lgili/Fenolite/docs/design-model.md

# The Fenolite design model (v0)

Normative text: `openspec/specs/design-model/`, `openspec/specs/canonical-serialization/` and
`openspec/specs/core-primitives/`. Decision record: `docs/adr/0001-neutral-model.md`.

## Entity header

Every entity (`fenolite.model.base.Entity`) carries:

| Field | Meaning |
|---|---|
| `id` | `<prefix>_<uuid>` (prefixes in `fenolite.core.ids.PREFIXES`) |
| `native_ids` | the object's id in each backend, e.g. `{"kicad": "a81c…"}` |
| `provenance` | backend, file, file SHA-256, opaque locator, evidence |
| `ext` | per backend, what the model does not understand, verbatim, with the minimum format version it needs |

Entities are frozen dataclasses; change them with `dataclasses.replace` and
`Design.replace_entity`.

## Units

Lengths are `int` nanometres, angles `int` microdegrees; floats are rejected everywhere
(`docs/formats/units.md`). `fenolite.core.units.parse_length("0.25mm") == 250_000`.

## Ids

| Object | Id |
|---|---|
| imported, with a native id | `uuid5(FENOLITE_NS, "<backend>:<native id>")` |
| imported, without one | `uuid5(FENOLITE_NS, "<backend>:<document id>:<section>:<content hash>")` |
| created by Fenolite | `uuid4` from a seeded generator (`--seed`) |
| placed copy of a library definition | from the caller's key, never from the seed (see "Placed copies") |
| created from a design script | `derived_id(prefix, "dsl", "<kind>:<key>")`, never from the seed (see "Ids of design scripts") |

A file hash never enters an id. Ids of objects without a native id are stable when *other*
objects change; the diff matches such objects by content.

## Layers (v0.1 subset)

| File | Class | Contents |
|---|---|---|
| `meta.json` | `DesignHeader` | id, name, `schema_version` (`"0"`), `fenolite_version` |
| `circuit.json` | `Circuit` | components (pins), nets (pin members), net classes, interfaces, modules, no-connect marks |
| `board.json` | `Board` | outline, layers, stack-up, footprints (pads), tracks, arcs, vias, zones, keep-outs, texts, graphics, holes |
| `rules.json` | `RuleSet` | rules: kind, selectors, layers, min/opt/max, severity, priority (1 = highest); check severities |
| `manufacturing.json` | `Manifest` | generated artefacts with tool, version, revision, variant, evidence, state |
| `findings.json` | `Findings` | issues, waivers |

`Design` aggregates them and offers read-only indexes (`by_id`, `by_ref`, `by_net`, `by_layer`)
and `validate()` (duplicate ids and references, dangling references, empty and single-pin nets, and
no-connect marks on unknown or connected pins).

### No-connect marks

`Circuit.no_connects: tuple[PinRef, ...]` (the last field of `Circuit`, `()` by default) lists the pins
that the design leaves unconnected on purpose (`no_connect` of `docs/dsl.md`).

- A mark is a `PinRef(component_id, pin)`, the form of a net member. `pin` has two forms: the
  designator as written (a pin number or a pin name) in the model that `to_model` gives, and a pin
  number after a build has resolved it. Marks are stored in `PinRef` order without duplicates.
- A mark is a fact of the connection, not of the library pin. `Pin` and `PinType` are unchanged, and
  `Pin.etype == "no_connect"` still means the pin type that the symbol declares. A mark has no id.
- The field is additive: `canonical` omits the default, so a design without marks gives the
  `circuit.json` bytes it gave before, and a file without the key `no_connects` loads with `()`.
  `SCHEMA_VERSION` stays `"0"`; `schemas/fenolite.model.v0/circuit.json` lists `no_connects` as an
  optional array of pin references.
- `Design.validate()` reports three findings for a mark, each with `where` set to `<ref>-<pin>` (or
  `<component id>-<pin>` when the component is unknown):
  - `model.no-connect-on-net` (error): a net lists the same pin reference; the message names the net.
  - `model.unknown-component` (error): no component has the id.
  - `model.unknown-pin` (error): the component holds pins and none has the number.
- A marked pin is no member of any net: `by_net`, `model.single-pin-net` and `model.dangling-net` are
  unchanged.

### Buses

`Circuit.buses: tuple[Bus, ...]` (empty by default, change c0043) records a bus, an indexed vector of nets.

- `Bus` carries the entity header (prefix `bus`), `name` (the vector's name without its range: `D` for
  `D[0..7]`) and `members`, an ordered tuple of `BusMember(index, net_id)`. A member without a net is left
  out, so indexes may have gaps.
- A bus differs from an `Interface`, which maps role names to nets. A group of nets with different names
  (a harness, a KiCad group bus) stays an `Interface`.
- The change is additive: a design without buses gives the `circuit.json` bytes it gave before, and a file
  without the key `buses` loads with `()`. `SCHEMA_VERSION` stays `"0"`.
- `Design.entities()` yields buses. `Design.validate()` reports, with `where` set to the bus name:
  - `model.unknown-net` (error): a member's `net_id` is no net of the circuit;
  - `model.duplicate-bus-index` (error): an index is used twice in one bus.
- A bus gives no net and no net member. No backend writes a bus; a build keeps it in `.fenolite/`.

## Library definitions

`fenolite.model.library` holds reference data shared by many designs, outside `Design` and outside
the `.fenolite/` layer files (normative text: requirement "Library definitions" of the
`design-model` capability, change c0008):

| Class | Contents |
|---|---|
| `FootprintDef` | entity: `name`, `library`, `description`, `keywords`, `kind`, `flags`, `properties`, `pads` (board `Pad`, `net_id = None`, positions relative to the definition), `graphics` (board `Graphic`), `models` |
| `SymbolDef` | entity: `name`, `library`, `extends`, `power`, `properties`, `in_bom`, `on_board`, `exclude_from_sim`, pin-name settings, `units`, `pins`, ordered symbol-local vector `graphics` |
| `SymbolPin`, `SymbolUnit`, `SymbolGraphic`, `PinAlternate` | value objects without the entity header; a pin is identified by `(unit, body_style, number)` and graphic points use integer nanometres |
| `Library` | `name`, `footprints`, `symbols`; schema `fenolite.library.v0` (`schemas/fenolite.model.v0/library.json`) |

- Every field other than `name` has a default. `keywords`, `flags`, `pads`, `graphics`, `models`,
  `units`, `pins` and `alternates` are ordered; `properties` is sorted by key.
- **Ids.** Definitions use the prefixes `fpd` and `sym`, with the native id `"<library>:<name>"`
  (or `"<name>"` for the library `""`) stored in `native_ids[<backend>]`.
- Pads, padstacks and graphics are scoped to their definition:
  - with a native uuid `U`, the id is `derived_id(prefix, backend, "<native id>:<U>")`, and `U` is
    stored in `native_ids[<backend>]`; a uuid repeated inside one definition keeps that form for its
    first occurrence, and its k-th repetition uses `"<native id>:<U>:<k>"`;
  - without one, it is a content id whose document is the definition's native id, whose section is
    `pad` or `gfx`, and whose digest includes an occurrence counter among identical contents.

  Ids are therefore unique within a `Library`. A consumer that places a definition twice derives new
  ids for the placed copies.

## Presentation

`fenolite.model.presentation` (change c0012) holds what a sheet draws around a board:

- `Board.sheet: SheetFrameRef | None`: the paper (`A0` … `A5`, `Letter`, `Legal`, `Tabloid`, or `custom`
  with `width` and `height` in nm), `portrait`, and `drawing_sheet`, the project-relative path of the
  drawing-sheet file the project names (or `${KIPRJMOD}/…`).
- `Board.title_block: TitleBlock | None`: `title`, `date`, `revision`, `organization`, `doc_id`,
  `responsible`, `approver`, and `params`, user parameters a sheet may show.
- `DrawingSheet(name, setup, items)`: a definition outside `Design`, like a library definition, with
  prefix `wks` and its own schema `drawing_sheet.json`. One sheet serves many boards and sizes, so it is
  never written to the six layer files. Its id is `derived_id("wks", "template", <sheet.name>)` for a
  sheet built from a `*.sheet.toml` specification and `derived_id("wks", "kicad", <name>)` for one read
  from a KiCad file.
- Items are value objects in drawing order: `SheetShape` (`kind` `line` or `rect`), `SheetText` and
  `SheetBitmap`. Every point is a `SheetPoint(corner, x, y)`, an offset from a corner of the margin box
  (the page minus the setup margins), positive toward the interior, so one sheet fits every page size.
- Texts hold neutral tokens only: `{title}`, `{doc_id}`, `{revision}`, `{sheet}`, `{sheets}`, `{date}`,
  `{organization}`, `{responsible}`, `{approver}`, `{filename}`, `{paper}`, `{param:NAME}`, and `{{`/`}}`
  for literal braces. `split_tokens` is the only parser; each backend maps the tokens to its own
  variables.
- `Design.validate()` reports `model.sheet-path` (an absolute path or a `..` segment), `model.sheet-size`
  (an inconsistent custom or named size) and `model.param-name` (a parameter name outside
  `[A-Za-z_][A-Za-z0-9_]*`).

## Schematic sheets

`fenolite.model.schematic` (change c0060) holds what one schematic file says:

- `SchematicSheet(name, paper, title_block, lib_symbols, symbols, labels, no_connects, wires, sheets, pages)`: a
  definition outside `Design`, like a `DrawingSheet`, with prefix `sch` and its own schema
  `schematic.json`. A generated sheet is derived from the circuit, and a sheet read from a file is checked
  and compared, so a sheet is never written to the six layer files.
- `SymbolInstance` (prefix `sci`): `lib_ref`, `position`, `rotation` (0, 90, 180 or 270 degrees in µdeg),
  `mirror` (`""`, `"x"` or `"y"`), `unit`, `body_style`, the properties with `ref`, `value` and `footprint`
  repeated as fields, the flags `dnp`, `in_bom`, `on_board` and `exclude_from_sim`, `lib_name`, and `uses`:
  one `SymbolUse(project, path, ref, unit)` per place of the hierarchy that shows the symbol.
- `NetLabel` (prefix `lbl`): `kind` (`local`, `global` or `hierarchical`, always written), `name`,
  `position`, `rotation` and `shape`. `NoConnectFlag` (prefix `ncf`): `position`.
- `SheetRef` (prefix `shr`): `name`, `file` (the text as written), `position`, `size` and `uses`, one
  `SheetUse(project, path, page)` each. `SheetPage(path, page)` lists the pages the root sheet names.
- `lib_symbols` holds the `SymbolDef` copies embedded in the file.
- Collections keep file order; `properties` is sorted by key. Uses and pages carry no ids.
- `Wire` (prefix `wir`, change c0070): `start` and `end`, horizontal or vertical and never a point. Only a
  sheet that Fenolite creates holds wires: the straight segments its generator draws from pin end to pin
  end. A backend keeps the wires of a file it reads as opaque slots, and `wires` stays empty.
- Junctions and buses are not modelled: a backend keeps them as opaque slots of the sheet.
- **Ids.** An entity read from a file has `derived_id(<prefix>, <backend>, <native id>)`. An entity that
  Fenolite creates for a design has `derived_id("sch", "fenolite", "<design name>")` for the sheet and
  `derived_id(<prefix>, "fenolite", "<design name>:<key>")` for the others, so two builds of one design
  give equal ids.

## Boards read from a backend

Normative text: requirements "Board entities read from file backends" and "Components synthesised
from a board" of the `design-model` capability (change c0009); KiCad facts in
`docs/formats/kicad/board.md`.

| Field | Meaning |
|---|---|
| `FootprintInstance.attributes` | ordered footprint flags: `smd`, `through_hole`, `board_only`, `exclude_from_pos_files`, `exclude_from_bom`, `dnp`, `allow_missing_courtyard`, `allow_soldermask_bridges` |
| `Via.via_type` | `through` (default), `blind`, `buried` or `micro` |
| `Track.locked`, `Arc.locked`, `Via.locked` | the copper lock (change c0108): tools must not move or remove the item. `fenolite route --rip` keeps it, the KiCad backend reads and writes it as `(locked yes)`, and an Altium build writes it as the lock bit of the record. `False` by default, and the key is written only when true, so a design without locked copper serialises to the bytes it had. Releases 0.2.x and 0.3.x cannot read a model document that carries the key `locked` on a track, an arc or a via: their reader refuses an unknown key |
| `ZoneFill.island` | the fill is an island; a zone may have several fills per layer, in file order |
| `Zone.name` | the zone's name, `""` when it has none |
| `Zone.settings` | how the zone is filled (section "Zone settings") |
| `Zone.filled` | the board's own fill flag, kept apart from `Zone.fills`: a zone may be filled with an empty result |
| `Zone.locked` | the zone is locked against edits in the board editor |
| `Pad.zone_connection` | how zones connect to the pad: `solid`, `thermal`, `none` or `thru_hole_only`; `None` means that the pad follows its footprint and the zone |
| `Pad.fab_property` | the fabrication mark of the pad (change c0118), what KiCad calls the fabrication property of a pad: `bga`, `fiducial_global`, `fiducial_local`, `test_point`, `heatsink`, `castellated`, `mechanical` or `press_fit`; `None` for no mark. Board pads and library pads carry it; the model does not check it against the pad's kind or layers. The key is written only when a mark is set, so a design without marks serialises to the bytes it had. Releases 0.2.x and 0.3.0 cannot read a model document that carries the key `fab_property`: their reader refuses an unknown key |

- **Pad frame.** `Pad.position` is footprint-local: absolute = `instance.position +
  R(instance.rotation)·pad.position`, with no further mirror, so a bottom footprint keeps its stored,
  mirrored coordinates. `Pad.rotation` is relative to the footprint, and `Pad.layers` are real board
  layers without wildcards.
- **Footprint assignment.** `Component.pin_pad_map` stores explicit symbol-pin-number to physical-pad-number
  pairs. An empty map means identity assignment; net membership remains keyed by symbol pin number. A pin
  may be bonded to several pads (section "Pins bonded to several pads").
  `Padstack.hole_shape`, `hole_length` and `hole_rotation` describe non-round drilled holes; `Pad.drill` is
  their width, and slot length includes both rounded ends. `hole_rotation` is the slot's axis in the pad's
  own frame, in a library footprint and on a board alike: it does not change when the pad or its footprint
  is rotated.
- **Outlines.** An empty `Zone.outline` or `Keepout.outline` means the backend keeps the outline as
  an opaque slot. `Board.outline` is `None` for an imported board; its edge graphics are authoritative.
- **Outline arcs.** `Outline.points` and `Outline.cutouts` hold the vertices of each ring, in order.
  `Outline.arcs` makes an edge an arc: `OutlineArc(ring, edge, mid)`, where ring 0 is `points`, ring k is
  `cutouts[k − 1]`, and edge i of a ring of n vertices joins vertex i to vertex (i + 1) mod n; the arc
  runs from the first vertex through `mid` to the second. Entries are sorted by `(ring, edge)`, at most
  one per edge. A ring has three vertices or more, or two when one of its two edges is an arc: a circle
  is two arcs. The canonical writer omits `arcs` when it is empty, so a `board.json` written before
  loads unchanged and an outline without arcs keeps its bytes.
  Release 0.2.x cannot read a model document that carries `arcs`: its reader refuses an unknown key.
- **Layers.** `Layer.ordinal` is the stack position; the backend's own number, type and user name
  are in `Layer.ext[<backend>]`.
- **Synthesised circuit.** A board read without a schematic gets one `Component` per footprint, one
  `Pin` per distinct non-empty pad number and net members from the numbered pads. `validate()`
  reports `model.duplicate-ref` as a warning (not an error) when the shared reference ends in `**`,
  or when every component sharing it is placed only by `board_only` footprints.

## Pins bonded to several pads

Normative text: requirement "Persist per-component pin-to-pad maps" of the `design-model` capability
(change c0123).

A pin of a part may be bonded to several pads: the tab and a pad of a regulator, the shield pads of a
connector, the pads a footprint model lists for one pin. `Component.pin_pad_map` says so by holding the
pin in several pairs: `(("3", "3"), ("3", "EP"))` bonds pin 3 to the pads 3 and EP.

- **The pads of a pin** are the pads of its pairs, in map order. The first is the pad a schematic symbol
  shows as the pin's number; the order has no other meaning. A pin that the map does not hold has one pad,
  of its own number. A pad has one pin.
- **Readers.** `Component.pads_of(pin)` gives the pads of a pin and `Component.pin_pads()` the pads of
  every pin the map holds. No other code turns the pairs into pads: `dict(component.pin_pad_map)` keeps
  one pad per pin, and a test refuses it anywhere in `src/fenolite` outside `model/circuit.py`.
- **Canonical form.** The field did not change: same name, same type, same place, pairs written in the
  order held, an empty map left out. A design whose pins have one pad each is written byte for byte as
  before, and a document written before loads as it is; nothing is migrated. `SCHEMA_VERSION` stays `"0"`
  (decided by the maintainer on 2026-10-06), and `schemas/fenolite.model.v0/circuit.json` gained only a
  description of the field.
- **The cost of keeping the version.** Fenolite 0.2.x and earlier read a document that holds a pin of
  several pads without an error and apply one pad per pin. Read such a
  document with the version that wrote it, or a later one.
- **Validation.** `Design.validate()` reports `model.pin-pad-map` (error), with `where` set to
  `<ref>-<pin>`, for a pair with an empty pin or pad, for a pair that occurs twice, and for a pad that two
  pins name. For a component that holds pins, a pin outside the map names the pad of its own number, so
  `(("1", "2"),)` on a part with the pins 1 and 2 is refused: the pad 2 would have two pins.
- **What each consumer does** with a pin of several pads: the KiCad build gives every pad the pin's net
  and embeds one hidden pin per further pad in the symbol (`docs/schematic.md`); the Altium build writes
  the pads as the map of the footprint model (`docs/altium.md`); `netlist.assignment_compare` and level 2
  of `equivalent` name every pad; the BOM, the placement file, the parity comparison and level 3 of
  `equivalent` do not read the map.

## Padstack holes, offsets and component bodies

Change c0043 completes the padstack and adds the body of a part. Every field has a default, so documents
written before them still load.

- `Padstack.hole_shape` (`round`, `square`, `slot`), `hole_length` (the length of a slot along its axis,
  ends included) and `hole_rotation` (the angle of the hole's axis relative to the footprint) describe a
  hole that is not round. `Pad.drill` stays the hole's size: the diameter of a round hole, the side of a
  square hole, the width of a slot.
- `PadstackLayer.offset: Point` is where the copper's centre lies on that layer relative to `Pad.position`,
  the centre of the hole, in the footprint frame.
- `Padstack.layers` may be empty: one shape on all layers with a hole that is not round. `Pad.padstack is
  None` still means one shape on all layers, a round hole or no hole, and no offset.
- In a library definition `PadstackLayer.layer` may be the wildcard `In*.Cu`, every inner copper layer.
- `ComponentBody` (prefix `bdy`) is the physical body of a part, in `FootprintInstance.bodies` and
  `FootprintDef.bodies`, ordered and empty by default: `kind` (`extruded` or `model`), `height` (from the
  board surface to the top of the body), `standoff` (from the board surface to its underside, 0 by
  default), `outline` (a polygon in the footprint frame, empty when the source gives none), `layer`,
  `model` (the name of a 3D model for the kind `model`) and `name`.
- A legacy body states a volume above its mounted side and carries no model data. Outward height
  is the largest known z_max (or legacy height); without known extents it is unknown.
- `fenolite.model.board.outward_height(footprint)` (change c0140) is the one function of the package that
  computes the height of a placed part: the largest upper bound of the footprint's known bodies, `None`
  when it has no known body or that bound is not positive. A body is known when its `projection_unknown`
  is false; its upper bound is its `z_max` when it has signed bounds (change c0099), and its `height`
  otherwise. It reads neither the component, nor a footprint property, nor a 3D model, nor `standoff`, nor
  `z_min`. No other field holds a part's height: `Component` has none, and a script states a height by
  giving the part a body (`docs/dsl.md`, `Part(height=…)`). Every consumer (the height limits of
  `docs/placement.md`, a checker, an exporter) calls it.
- `Design.validate()` reports `model.body-height` (error), with `where` set to the body's id, for a body
  without signed bounds and without unknown projection whose `height` is below its `standoff`
  or whose `standoff` is negative.
- Signed body intervals use integer-nm `z_min` and `z_max`, both present and ordered, in the
  mounted-face frame with positive Z outwards. They take precedence over source height/standoff;
  `model.body-volume` reports a half-specified or reversed interval at the body id.
- `projection_unknown` defaults to false. Unknown projections are retained but have no qualified
  extrusion; malformed source heights use 0, reversed heights, unsupported model types and mismatched
  projection sides produce warnings and bypass `model.body-height`. Explicit intervals still validate.
- Known imports serialize both bounds equal to source standoff/height, including negative standoff.
  Old v0.2.0 body documents retain default fields and identical bytes; legacy validation applies until
  source reimport. The canonical readers of releases 0.2.x and 0.3.0 refuse documents containing the new
  body keys.
- The KiCad backend reads and writes no body: a KiCad build keeps the bodies of a design in `.fenolite/`.

## Footprint items and corner ratio

Normative text: requirements "Graphics and texts of a footprint instance", "Corner ratio of a
rounded-rectangle pad" and "Models without footprint items" of the `design-model` capability (change
c0126).

| Field | Meaning |
|---|---|
| `FootprintInstance.graphics` | the drawings of this placed footprint: `Graphic` entities (the entity of `Board.graphics`), in the order of their source; `()` by default |
| `FootprintInstance.texts` | the free texts of this placed footprint: `Text` entities (the entity of `Board.texts`), in the order of their source; `()` by default |
| `Pad.corner_ratio` | the corner radius of a `roundrect` pad, an integer in parts per million of the shorter side of `Pad.size`, from 0 to 500 000; `None` by default, and for every other shape |

- **Frame.** A point `p` of a footprint's graphic or text is in the pad frame: it lies on the board at
  `instance.position + R(instance.rotation)·p`, with no further mirror, so a bottom footprint holds
  mirrored coordinates, as its pads do. `Text.rotation` is relative to the footprint.
- **Layers.** `layer` is the board layer the item lies on: a silkscreen line of a bottom footprint is on
  `B.SilkS`. A graphic may be of any kind and on any layer, a copper layer included; a consumer that
  cannot use one counts it and says so.
- **Reference and value.** Where they are drawn stays in `FootprintInstance.fields`; `texts` holds only
  texts that are no field, with the string as the source stores it.
- **Unit of the ratio.** 250 000 is a quarter of the shorter side (KiCad `roundrect_rratio` `0.25`,
  Altium 50 %). One Altium percent is 5 000 ppm; a KiCad decimal `r` is `r · 1 000 000`, rounded half to
  even when it has more than six decimals. No float and no decimal string is stored.
  `Design.validate()` reports `model.corner-ratio` (error), with `where` set to the pad's id, for a value
  outside the range and for a value on a pad that is no `roundrect`. A library pad (`FootprintDef.pads`)
  carries the field alike.
- **Who fills them.** The Altium import fills all three for a PCB document. An Altium build stores them
  in `.fenolite/board.json` for the footprints it wrote. The KiCad readers and writers neither fill nor
  read them: a design read from a KiCad board has empty `graphics` and `texts` and no ratio, and keeps
  its footprint drawings where it always kept them, in the footprint's opaque slots.
  `backends.kicad.fpitems.with_footprint_items` gives them on request, as read-only copies.
- **Old model documents.** The three fields are additive and `SCHEMA_VERSION` stays `"0"`. The canonical
  form leaves a field at its default out, so a design without footprint items gives the `board.json`
  bytes it gave before, and a model document without the keys `graphics`, `texts` and `corner_ratio`
  loads unchanged: `tests/data/model/v0.2.0/blink_2layer.board.json`, which release 0.2.0 itself wrote,
  loads and serialises again to its own bytes.
- **Release 0.2.0 cannot read a model document that carries one of the new keys: its reader refuses an
  unknown key** (`unexpected property 'graphics'`). The same holds for every 0.2.x release, and it held
  for every earlier additive change of the model. A `.fenolite/` folder that a newer release wrote for
  an Altium build, or the model of an imported Altium board, is therefore not readable by 0.2.x; build
  or import again with the older release if you must go back.

## Stack-up

`Board.stackup` describes the board's build-up from its top face to its bottom face (change c0101);
a board whose source states none has `stackup` `None`, and the model then holds no board thickness.

- `Stackup.layers` lists every entry the source keeps, in order. A `copper` entry is named after its
  copper layer in `Board.layers`. `soldermask`, `silkscreen` and `solderpaste` entries describe the outer
  layers and lie above the first copper entry or below the last; silkscreen and paste entries have the
  thickness 0. Every entry between two copper entries is a `dielectric`; a dielectric made of several
  sheets is one entry per sheet, consecutive, the sheets sharing a name.
- `StackLayer.dielectric_kind` is `core`, `prepreg` or `None` (not stated); `StackLayer.color` is the
  colour as the source names it; `Stackup.impedance_controlled` is true when the dielectric values are
  requirements for the fabricator. `epsilon_r` and `loss_tangent` are plain decimal texts or empty.
- `Stackup.thickness()` is the sum of the entries: the board thickness of the model, and the only one.
  `Stackup.depth(name)` gives the depths, below the top face, of the two faces of the first entry of that
  name (`KeyError` for an unknown name). `Stackup.between(upper, lower)` gives the entries strictly
  between two entries, top to bottom (`KeyError` for an unknown name, `ValueError` when `upper` does not
  lie above `lower`).
- `Design.validate()` reports, with `where` set to the stack-up's id and at most once each, naming the
  first problem: `model.stackup-order` (error) for an outer entry between two copper entries, two entries
  of one outer kind on one side, a dielectric outside the outer copper entries, two neighbouring copper
  entries with nothing between them, the dielectrics of one gap with different kinds, or a
  `dielectric_kind` on an entry that is not a dielectric; `model.stackup-copper` (error) for a stack-up
  without a copper entry, or whose copper entries are not the board's copper layers in ordinal order;
  `model.stackup-value` (error) for a negative thickness, a copper or dielectric entry of thickness 0, an
  `epsilon_r` that is neither empty nor a plain decimal above 0, or a `loss_tangent` that is neither empty
  nor a plain decimal (digits, an optional point and digits, no sign and no exponent; a loss tangent of 0
  is what KiCad writes for a solder mask).
- The three fields are additive: `canonical` omits the defaults, a `board.json` written before them loads
  unchanged and serialises to its own bytes (`tests/data/model/v0.2.1/blink_2layer.board.json`), and
  `schema_version` stays `"0"`. The other direction does not hold. Release 0.2.x cannot read a model
  document that carries `dielectric_kind`, `color` or `impedance_controlled`: its reader refuses an
  unknown key.

## Rule areas, board items and the area selector

Change c0103 adds what a script needs to declare rule areas and drawings:

- `Keepout.name: str = ""`, the name of a rule area. A `Keepout` whose five settings are false is a named
  area that only rules select.
- `Text.h_justify` and `Text.v_justify` (`left`, `center`, `right` and `top`, `center`, `bottom`; `center`
  by default), in the reading frame of the text.
- `Dimension`, a linear dimension between two points: `kind` (`aligned` or `orthogonal`), `layer`, `start`,
  `end`, `offset` (the signed distance of the dimension line from the points), `direction` (`horizontal`
  or `vertical`, for an orthogonal one), `units` (`mm` or `in`), `precision` (4 by default), and `size`,
  `thickness` and `width`, where `None` means the backend's default. The measured value is not a field: it
  follows from the points. `Board.dimensions` holds them; the id prefix is `dim`.
- The selector op `area`: `Selector("area", v)` matches a subject whose `RuleSubject.areas` (the names of
  the rule areas it lies in) holds a name that `v` matches with `fnmatch.fnmatchcase`. Letter case counts
  and `*` is a glob.
- The keys are additive: `canonical` omits the defaults, and a document written before them loads
  unchanged and serialises to its own bytes. The other direction does not hold. Release 0.2.x cannot read
  a model document that carries one of the new keys (`name` of a keep-out, `h_justify` and `v_justify` of
  a board text, `dimensions` of a board) or a selector of the op `area`: its reader refuses an unknown key
  and its schema an unknown op.

## Via protection

`Via.protection` and `Board.via_protection` say how vias are protected (change c0112). Both hold a
`ViaProtection`, a value object without an entity header and with eight fields, each `True`, `False` or
`None`: `tenting_front`, `tenting_back`, `covering_front`, `covering_back`, `plugging_front`,
`plugging_back`, `capping` and `filling`. `True` means that the feature is applied on that side (or to the
via, for `capping` and `filling`), `False` that it is not.

- On a via, `None` means that the field follows the board's default. A via without protection holds
  `ViaProtection()`, every field `None`. `protection` is the field before `locked` (c0108), which stays
  the last field of `Via`.
- `Board.via_protection` is the default for every via. `None`, whole or for one field, means the backend's
  own default: KiCad tents both sides and applies nothing else (`docs/formats/kicad/board.md`, "Via
  protection"); the Altium backend leaves the tenting flags clear (`docs/altium.md`).
- The model computes no effective value: `fenolite.backends.kicad.via_protection.effective` does, for the
  KiCad backend.
- The two fields are additive: `canonical` omits the defaults, so a via whose protection is
  `ViaProtection()` and a board without a default write the text they wrote before, a `board.json` written
  before them loads unchanged and serialises to its own bytes
  (`tests/data/model/v0.2.1/blink_2layer.board.json`), and `schema_version` stays `"0"`. The other
  direction does not hold. Fenolite 0.2.x and 0.3.0 cannot read a `board.json` that carries `protection` or
  `via_protection`: their reader of the canonical form is strict.

## Differential pairs

A differential pair is an `Interface` whose kind is a key of `fenolite.model.pairs.PAIR_ROLES`
(change c0104): `diff_pair` with the roles `p` and `n`, and `usb2` with `dp` and `dn`, the positive role
first. The model holds no other pair entity, and a pair holds no constraint of its own: its width, gap
and via gap are values of the net class of its two nets, and its limits are rules that select it.

- **Name rule** (`H-K-DIFFPAIR-NAMES-2`, `docs/formats/kicad/rules.md`). `split_pair_name(name)` takes the
  longest trailing run of digits and `_` as the tail; the character before it must be `P`, `N`, `+` or `-`
  (the polarity), and the text before that is the base. `coupled_name` swaps the polarity;
  `pair_base(positive, negative)` is the base when the first name has the polarity `P` or `+` and the
  second is its coupled name. `USB_P`/`USB_N` has the base `USB_`, `USB_DP`/`USB_DN` the base `USB_D`,
  `D_P0`/`D_N0` the base `D_`. Letter case counts. `net_bases(names)` gives the base of every name whose
  coupled name is among `names`; `pair_nets(interface)` gives the two net ids of a pair interface.
- **Class values.** `NetClass.diff_pair_width`, `diff_pair_gap` and `diff_pair_via_gap` are lengths in
  nm or `None` (the default), stored in `circuit.json`. They are what a router lays a pair with, not
  limits.
- **Rule kinds.** `RuleKind` holds five kinds for pairs and nets: `diff_pair_gap`, `diff_pair_uncoupled`,
  `skew` (every selected net against the longest of them), `diff_pair_skew` (the two nets of each
  selected pair) and `length`.
- **The pair leaf.** `SelectorOp` and `LEAF_OPS` hold `diff_pair`, whose value is a pair base or `*`.
  `RuleSubject.diff_pair` is the base of the subject's net when the design holds its coupled net, and
  `Selector("diff_pair", v)` matches a subject whose base matches `v` as a glob with its letter case, or
  ends with `_` and matches `v` without that `_`.
- The fields, the kinds and the leaf are additive: `canonical` omits the defaults, a `circuit.json` and a
  `rules.json` written before them load unchanged, and `schema_version` stays `"0"`. The other direction
  does not hold. Fenolite 0.2.x and 0.3.0 cannot read a `circuit.json` or a `rules.json` that carries them
  (one of the three class keys, one of the five kinds or a `diff_pair` leaf): their reader of the canonical
  form is strict. A build regenerates `.fenolite/`.

## Proximity rules

`RuleSet.proximity` holds the placement rules of a design (change c0113): which parts belong near which
pads. `fenolite.model.rules` defines two frozen value objects for it, without an entity header.

- `PadSelection(path, number="", index=None)` selects pads of one part by its component path: every pad
  when `number` is empty, the pads of that number otherwise, and only the one at `index` among them, in
  the footprint's pad order, when `index` is given. An `index` needs a `number`.
- `ProximityRule(name, parts, anchor, within, severity="error")`: each part of `parts` keeps one of its
  selected pads within `within` (nm, pad centre to pad centre) of a selected pad of `anchor`. `severity`
  is `error` or `warning` (`PlacementSeverity`). `parts` and `anchor` are not empty and `within` is above
  0; a `RuleSet` refuses two rules of one name.
- A rule is named by its key and has no id. It is no rule of `RuleSet.rules` and has no `RuleKind`: no
  backend lowers it, and a board read from a file has none. `to_model` writes the rules in name order
  (`docs/dsl.md`, `near`), and `fenolite.checks.placement.judge` judges them (`docs/placement.md`).
- The field is additive: `canonical` omits `proximity` when it is empty, so a design that declares no
  rule writes the bytes it wrote before and every output of 0.2.0 keeps its bytes, a `rules.json` written
  before the field loads unchanged, and `schema_version` stays `"0"`. The other direction does not hold.
  Fenolite 0.2.x and 0.3.0 cannot read a `rules.json` that carries `proximity`: their reader of the
  canonical form is strict.

## Height limits

`RuleSet.heights` holds the height limits of a design (change c0140): where parts may not be tall.
`fenolite.model.rules` defines the frozen value object for it, without an entity header.

- `HeightLimit(area, max, severity="error")`: every rule area (`Keepout`) whose `name` is `area` limits the
  parts under it to `max` (nm, the outward height of `outward_height`). `area` is not empty, `max` is above
  0, `severity` is `error` or `warning` (`PlacementSeverity`); a `RuleSet` refuses two limits of one area.
- A limit is keyed by its area and has no id. It is no rule of `RuleSet.rules` and has no `RuleKind`: no
  backend lowers it, and a board read from a file has none. `to_model` writes the limits in area order
  (`docs/dsl.md`, `height_limit`), and `fenolite.checks.placement.judge_heights` judges them
  (`docs/placement.md`).
- The field is additive: `canonical` omits `heights` when it is empty, so a design that declares no limit
  writes the bytes it wrote before, a `rules.json` written before the field loads unchanged, and
  `schema_version` stays `"0"`. The other direction does not hold. Fenolite 0.2.x and 0.3.0 cannot read a
  `rules.json` that carries `heights`: their reader of the canonical form is strict.

## Impedance targets

`RuleSet.impedance` holds the impedance targets of a design (change c0105; guide `docs/impedance.md`).

- `ImpedanceKind` is `single` or `differential`.
- `TraceGeometry(layer, references, width, gap=None)` is a value object: a copper layer, one or two
  reference layers in stack order (none equal to the layer), the width in nm above 0, and the gap in nm
  above 0 for a `differential` target, `None` for a `single` one.
- `ImpedanceTarget(name, kind, netclass_ids, ohms, tolerance_percent="", layers=())` is an entity (prefix `imp`): the
  ids of the classes it governs, `ohms` and `tolerance_percent` as decimal text (`"90"`, `"7.5"`; never
  from a `float`; `ohms` is `""` only for a target read from a file that gives none), and one geometry per
  layer in stack order. Targets keep their declaration order.
- `Design.validate()` reports `model.impedance-invalid` (error) for an unknown class, a class of two
  targets, two targets of one name, a layer given twice, a gap that does not fit the kind, a width or gap
  of 0 or less, a reference count other than one or two, a reference equal to the layer, and an `ohms` or
  tolerance text that is not a positive decimal or a tolerance of 100 or more.
- Every width and gap is the user's or a KiCad profile's: no estimate enters the model.
- The field is additive: `canonical` omits `impedance` when it is empty, a `rules.json` written before the
  field loads with an empty tuple, and `schema_version` stays `"0"`. The other direction does not hold:
  0.2.x and 0.3.0 cannot read a `rules.json` that carries the key `impedance`, because their reader of the
  canonical form is strict.

## Zone settings

Normative text: requirement "Zone settings in the board model" of the `design-model` capability (change
c0031); KiCad facts in `docs/formats/kicad/board.md`, "Zone settings".

`ZoneSettings` and `ZoneHatch` are frozen value objects without the entity header. Every `Zone` has a
`settings` value; the defaults are the values KiCad gives a new zone, so a zone created with
`ZoneSettings()` behaves like one drawn in KiCad with the default dialog.

| `ZoneSettings` field | Meaning | Default |
|---|---|---|
| `clearance` | the smallest distance the fill keeps from copper of other nets; a larger net-class or rule clearance still wins | 500 000 nm |
| `min_thickness` | the smallest width of copper that a fill keeps | 250 000 nm |
| `connection` | how the fill meets pads of its own net: `solid`, `thermal` (reliefs with spokes), `none`, or `thru_hole_only` (reliefs on through-hole pads, solid on the others) | `thermal` |
| `thermal_gap` | the gap of a thermal relief | 500 000 nm |
| `thermal_spoke_width` | the width of a relief's spokes | 500 000 nm |
| `island_removal` | `always` removes copper that no pad connects, `never` keeps it, `below_area` keeps islands of at least `min_island_area` | `always` |
| `min_island_area` | square nanometres | 10 000 000 000 000 (10 mm²) |
| `smoothing`, `smoothing_radius` | `none`, `chamfer` or `fillet` at the corners of the fill, and its size | `none`, 0 |
| `fill_mode` | `solid` or `hatched` | `solid` |
| `hatch` | a `ZoneHatch`: `thickness` (1 mm), `gap` (1.5 mm), `orientation` (0), `smoothing_level` (0), `smoothing_value` (`"0.1"`), `border` (`hatch_thickness` or `min_thickness`) and `min_hole_area` (`"0.15"`) | `ZoneHatch()` |

- **Ratios are strings.** `smoothing_value` and `min_hole_area` are decimal strings: the model holds no
  float.
- **Effective settings.** `settings.effective()` returns a copy in which every value that cannot change
  the fill is at its default: `hatch` of a solid fill, `smoothing_radius` without smoothing, and
  `min_island_area` unless `island_removal` is `below_area`. Comparisons and digests use it, so a value
  without effect never counts as a change.
- **`filled` is state, not a setting.** It says that the board holds the result of a fill, which may be
  empty. It does not enter `effective()`.
- **Pads.** `Pad.zone_connection` overrides the zone for one pad. Board pads and library pads carry it
  alike, so a library footprint can make its exposed pad solid in a thermal pour.
  `Pad.fab_property` (change c0118) is carried the same way: a library pad marked as a BGA ball, a
  fiducial or a test point keeps its mark on every placed copy.
- **Old documents.** The four fields have defaults, so a `board.json` written before them still loads.

## Placed copies

Normative text: requirement "Placed copies of library definitions" of the `design-model` capability
and the third case of "Identifier derivation" (change c0017); KiCad facts in
`docs/formats/kicad/board.md` ("Placed footprints").

A backend that places a library definition into a design derives every id of the copy from a key the
caller passes (c0011 passes the component path), never from the seeded generator and never from the
definition's own ids. For KiCad each native id is `uuid5(FENOLITE_NS, "kicad-place:<key>:<locator>")`,
the locator being the node's place in the emitted definition, and the Fenolite ids follow from those
native ids as for any imported object, so a design read back from the written file has the same ids.
Placing again with the same key gives the same ids; two keys share none; adding or removing another
placement changes no id of a copy. The copy records the definition in `FootprintInstance.lib_ref`,
belongs to the caller's component, and its pads have no net until the caller assigns one. The
definition stays unchanged.

## Ids of design scripts

Normative text: the fourth case of requirement "Identifier derivation" of the `design-model`
capability (change c0011); the key table is in `docs/dsl.md` ("Ids: the key table").

Every object that `fenolite.dsl.to_model` or `fenolite build` creates gets
`derived_id(prefix, "dsl", "<kind>:<key>")`, where the key is a name or a path from the script
(`component:<path>`, `net:<name>`, `pin:<path>:<number>`, `rule:<kind>`, …) from the closed table
`dsl.KEYS`.
Footprints and pads are placed copies keyed by the component path (see "Placed copies"), and the
board layers are keyed by their KiCad names. These ids are not generated: they do not depend on
`--seed`, on `PYTHONHASHSEED` or on the order in which the script creates objects, so inserting a part
changes no id of another object, and two builds of one script give byte-identical files.

## Ids of script copper

Normative text: the fifth case of requirement "Identifier derivation" (change c0028); the uuid layout
is in `docs/copper.md` ("Ids and markers").

A track or via created from a copper intent takes the KiCad uuid `copper_uuid(key, locator)` as its
native id, and the id that an imported object with that native id gets:
`derived_id("trk" | "via", "kicad", uuid)`. A design read back from the written board therefore has
the same ids. The key is the intent's key and the locator numbers the item inside that intent, so
adding, removing or reordering intents changes no id, and neither do `--seed` and `PYTHONHASHSEED`.

## Canonical JSON

`fenolite.model.canonical`: UTF-8, LF, two-space indent, keys in field order, defaults omitted,
integers only, collections of entities sorted by `(kind, path | ref | name | number, id)` unless a
field is marked `ordered` (stack-up and board layers, polygon points), mappings sorted by key.
`dumps(loads(dumps(x))) == dumps(x)`; moving one footprint changes only its position lines.
Reading validates every value against the same annotations the JSON Schemas in
`schemas/fenolite.model.v0/` are generated from and reports the first problem with its JSON pointer.

## Slots (for backends)

A backend represents each node it reads as an ordered list of `Modeled(field)` and
`Opaque(fragment, min_version)` children and writes opaque children back verbatim in their original
position. This is what makes "read → write unchanged" lossless without matching the tool's own
formatter byte for byte. The first backend to implement it is the KiCad board backend. On a write, a
backend changes an opaque child only where one of its requirements says so; the KiCad writer's list
is in the `kicad-slots` requirement "Slot source for model entities" (net references in the target's
form, rows the target no longer writes, slots dropped under `--allow-lossy`, the Reference and Value
atoms, and respelled fields written from changed model values).

## Layout authority

For a design authored in Fenolite, the exported tool project is the source of truth for layout;
`.fenolite/` is a regenerable, git-ignored cache; imported third-party files are kept immutable by
SHA-256 under `native/`.

## Rule kinds (c0107)

`model.rules.RuleKind` holds eighteen kinds. The thirteenth, `no_tracks`, was added by change c0107: tracks
and arcs of the items that `selector_a` selects are not allowed on the copper layers of `layers`. It takes
no limit and no `selector_b`, and it follows the twelve kinds of before, so the first twelve keep their
order; the five pair and length kinds of change c0104 ("Differential pairs") follow it.

The kind is additive in one direction only. A `rules.json` without a `no_tracks` rule is, byte for byte,
what it was (`tests/data/model/v0.2.1/twelve_kinds.rules.json` loads and serialises to its own bytes), and
`schema_version` stays `"0"`.
Releases 0.2.x and 0.3.x cannot read a model document that holds a `no_tracks` rule: their `RuleKind` lacks
the value.
## Net ties, waivers and check severities

Three keys of change c0114. Each is omitted at its default, so a design that uses none of them writes the
documents it wrote before, byte for byte.

- **`net_ties`** (`board.json`, `library.json`). `FootprintInstance.net_ties` and `FootprintDef.net_ties`
  are tuples of groups, each group the numbers of pads of different nets that the footprint joins on
  purpose, in the order its source lists them; ordered, `()` by default. A backend reads them from its
  own form (KiCad: the `net_tie_pad_groups` child), the copper check does not judge two pads of one
  group, and `Design.validate()` does not check the numbers against the pads. A backend that reads no
  groups leaves the field empty: the Altium import does. 0.2.x and 0.3.0 cannot read a document that
  carries `net_ties`.
- **`waivers`** (`findings.json`). `Findings.waivers` holds `Waiver(name, code, items, reason, min_gap)`
  values, sorted by name: the acceptance of one finding with a reason. `code` is a finding code
  (`copper.short`, `copper.clearance`, `copper.zone-overlap` or `<oracle>.drc.<suffix>`), `items` are
  the names of the finding's items as `where` prints them, or patterns of them, and `min_gap` is in
  integer nm. What a waiver may say is checked where it is declared (`design.waive()`, `docs/dsl.md`);
  how it matches is `fenolite.checks.waivers`. 0.2.x and 0.3.0 cannot read a `findings.json` that carries
  `waivers`.
- **`severities`** (`rules.json`). `RuleSet.severities` maps the finding code of a check of a
  design-rule tool (`<oracle>.drc.<suffix>`) to `error`, `warning` or `ignore`, written with its keys
  sorted. A severity is not a rule: it has no `RuleKind` and no row in a backend's rule table. 0.2.x and
  0.3.0 cannot read a `rules.json` that carries `severities`.
### Optional mechanical intent (c0096)

`Hole.intent`, `Keepout.intent` and `FootprintInstance.anchor` optionally hold `MechanicalIntent`:
a stable key, board-relative frame, integer nm tolerance, supplied source/evidence and `measured`,
`estimated` or `proposed` status. Conversion adds the board origin once; absent fields remain omitted
canonically. An anchor requires a locked DSL placement. Metadata records an input, not assembly fit.
No script call fills `Hole.intent` or `Keepout.intent`: holes and keep-outs of a script come from
`hole()` (c0102) and `rule_area()` (c0103), the calls the maintainer kept on 2026-10-07.
Planner reservations reference existing physical drill pads and never add a hole or change a net.

The DSL's intent metadata is conversion-only: `Placement.anchor` in `placements`. Builds and rebuilds do not persist these fields in a native
project or its `.fenolite/` cache. `FootprintInstance.anchor` is available to callers that explicitly
construct a neutral model; the build does not synthesize it from a placement request.
