lgili/Fenolite/openspec/changes/c0104-diff-pair-constraints/design.md

## Context

- **Scope.** The review of 2026-10-05 named the gaps to a complex board; since 2026-10-07 the group is milestone v0.4 (`docs/roadmap.md`, "Milestone names" and "v0.4: proposals on other branches", where the row of c0104 holds its id and slug only). The gap this change closes, in the review's words: "a differential pair lowered to KiCad: pair net names, class pair width, gap and via gap, rule kinds for gap, uncoupled length, skew and length". The plan's rules row put `length`, `skew` and `diff_pair_gap` at v0.6, and c0071 and c0073 list them as non-goals; this change pulls them forward with the uncoupled length, which the yardstick's pairs need.
- **What exists** on `origin/dev` at `9aba2dff` (2026-10-07). c0071 and c0073 are archived (2026-10-05), so the living specs hold their text, and the MODIFIED requirements of this change are copies of that living text with this change's edits only (compared word by word on that commit).
  - `model.circuit.Interface(name, kind, members)`. The DSL's `DiffPair(p, n)` gives kind `diff_pair` with the roles `p` and `n`, and `USB2(dp, dn, …)` gives kind `usb2` with `dp` and `dn` (c0073). No other pair type exists in `src/`.
  - `NetClass` holds `clearance`, `track_width`, `via_diameter`, `via_drill` and `description`. `lowering.NETCLASS_KEYS` writes the four lengths, and `lower_netclass` copies every other key of the project's `Default` entry, so every written class carries the template's `diff_pair_width` 0.2, `diff_pair_gap` 0.25 and `diff_pair_via_gap` 0.25 mm. `pro.ProjectClass` reads four values.
  - `model.rules`: twelve kinds (c0071); the ops `all`, `net`, `netclass`, `ref`, `layer`, `item_kind`, `and`, `or` and `not`; `Rule.min/opt/max` in nm. `rulemap.rule_nodes` writes only `min`, `opt` and `max` inside a constraint, and `lift_rule` keeps a rule with any other constraint child opaque. The token inventory loads `diff_pair_gap`, `diff_pair_uncoupled`, `skew`, `length` and `constraint/within_diff_pairs` since 9 (`H-K-TOK-RULES-FLOOR`; the flag is written as a list, and a bare atom disables the rules).
  - `lens.build`: `PAIR_KINDS`, `is_pair` (names equal except for a last character `P`/`N` or `+`/`-`, `H-K-DIFFPAIR-NAMES`) and `interface_checks`, which gives one `build.interface-not-lowered` info per `diff_pair` and `usb2` interface and `build.diff-pair-name`.
  - `checks.clearance.ClearanceResolver`: subjects of item kind, net, class, reference and layer; every leaf compared without letter case; `k` is the larger class clearance (c0029, c0068).
  - A DRC violation of any type becomes a `kicad.drc.<type>` finding, with one `explain` entry for the family, so new types need no registry.
  - The Altium build (c0084, implemented on `dev`, two tasks open, not archived). `backends.altium.rulemap.TABLE` holds one row per kind of `model.rules.RuleKind`: eight `exact` rows and four `no-counterpart` rows; `lower()` looks a rule's row up by its kind (`_ROWS[rule.kind]`), and the scenario "Every kind has a row" of c0084's "Rule lowering table" compares the kinds of the model with the table. A kind without a row raises `KeyError` in the build and fails that scenario. `rulemap._leaf` refuses every leaf other than `net` and `netclass` with `scope-unsupported`. Each rule that is not written gives one `altium.not-lowered` warning at `design-rules/<kind>`. `lens.altium` names the rule values of the net classes in one info at `rules` when no PCB document is written (with a document the class clearance, width and via values become rule records), and names `diff_pair`, `i2c`, `spi`, `uart` and `usb2` interfaces in one info at `interfaces`. `read.scope.parse_scope` has a closed grammar with no pair function. The word "pair" in `rulemap.ScopeForm` means a rule with two scopes, not a differential pair.
  - c0097 (branch `codex/c0097-copper-rule-explain`, not on `dev`): `ClearanceResolver.explain` returns the candidate rows `rule:<name>`, `class:<name>`, `floor` and the zone row, taken from the resolver's own candidates; its design says that a later pair-gap source adds a candidate row.
- **Measured on 2026-10-05.** Scratch benches were written with the `write_board` of the branch `review-roadmap-complex-board`: 0.2 mm tracks on `F.Cu`, rows 4 mm apart, the canary scoped to `CANARY_A`. DRC ran as `kicad-cli pcb drc --format json --severity-all -o <report> <board>` on the local 10.0.6, and as the same command in the pinned 9.0.9 image (`docker run --rm --platform linux/amd64 -v <bench folder>:/p -w /p -e HOME=/tmp kicad/kicad:9.0.9@sha256:e638b79b… kicad-cli pcb drc …`). The canary fired in every run, and the two majors gave the same outcomes on every row except the one marked.

  1. *Rule kinds*, project `{}`, pairs 0.3 mm apart edge to edge unless said; several rules files ran on one board, so a row recurs:

     | rule (condition `A.inDiffPair('<row>')` unless said) | row | reported |
     |---|---|---|
     | `diff_pair_gap (min 0.35mm)` | GA | `diff_pair_gap_out_of_range` "minimum gap 0.3500 mm; actual 0.3000 mm", naming both tracks |
     | the same | GB, 0.4 mm apart | nothing |
     | `diff_pair_gap (max 0.25mm)` | GC | `diff_pair_gap_out_of_range` "maximum gap 0.2500 mm" |
     | `diff_pair_gap (min 0.35mm) (max 0.5mm)` | GA; GB | reported; nothing |
     | `diff_pair_gap (opt 0.5mm)` | GD | nothing |
     | `diff_pair_gap (min 0.25mm) (opt 0.3mm) (max 0.35mm)`; `(min 0.35mm) (opt 0.35mm) (max 0.35mm)` | GE; GF | nothing; reported "minimum gap 0.3500 mm" |
     | `(layer "F.Cu")` with `diff_pair_gap (min 0.35mm)`; the same with `(layer "B.Cu")` | GA; GC, both on `F.Cu` | reported; nothing |
     | min 0.35 on the two net names | GE | reported |
     | min 0.35 on the positive net's name only | GF | reported |
     | min 0.35 on `GG_A` and `GG_B`, which do not pair by name | GG | nothing |
     | `diff_pair_uncoupled (max 2mm)` | UA: the positive track 3 mm longer | `diff_pair_uncoupled_length_too_long` "actual 3.0000 mm" |
     | the same | UB: 1 mm longer | nothing |
     | the same | UC: equal tracks 3 mm apart | nothing: parallel segments count as coupled at any distance |
     | `skew (max 0.5mm) (within_diff_pairs)` | SA: 20 and 21 mm | `skew_out_of_range` on the shorter track, "actual -1.0000 mm; target net length 21.0000 mm (from SA_N)" |
     | the same | SB: 20 and 20.2 mm | nothing |
     | `skew (max 0.5mm)` on four net names | SC 20/20 mm, SD 23/23 mm | `skew_out_of_range` on both SC tracks, -3 mm against SD_N |
     | `skew (max 0.5mm) (within_diff_pairs)` on four net names | SE 20/20, SF 23/23 | nothing |
     | the same | SG 20/21, SH 23/23 | on SG_P only |
     | `skew (opt 0.1mm) (within_diff_pairs)` | SM 20/21 | nothing |
     | `length (min 25mm)`; `(max 15mm)`; `(min 15mm) (max 25mm)`; `(opt 30mm)`; `(min 25mm) (max 30mm)`; `(min 15mm) (opt 20mm) (max 25mm)`, on a net name | 20 mm tracks | `length_out_of_range` "min length 25.0000 mm; actual 20.0000 mm"; reported; nothing; nothing; reported; nothing |
     | `length (max 20.5mm)` | 10 mm on `F.Cu`, a 0.6 mm via, 10 mm on `B.Cu` | reported: actual 21.5800 mm on 10.0.6, 21.5450 mm on 9.0.9 (the two majors differ here only) |

  2. *Selectors.* `A.inDiffPair('*')` reported every pair 0.3 mm apart, not GB (0.4 mm), not GG (no pair by name) and not UC. `A.inDiffPair('GD_')`, the base with its underscore, selected GD; `A.inDiffPair('gc')` selected nothing on `GC_P`/`GC_N`, so the base keeps its letter case, unlike `NetName`. `A.NetClass == 'DPG'` selected the pair of class DPG.
  3. *Order.* `diff_pair_gap` on `*` (min 0.35 mm) then on GA (min 0.25 mm): GA not reported; with the two rules swapped, reported. The same for `length` on `A.NetName == 'L*'` (max 15 mm) then on `LA` (max 25 mm).
  4. *Names*, `diff_pair_gap (min 0.35mm)` on both net names: `TA_P1`/`TA_N1`, `TB_P_2`/`TB_N_2` and `TDP1`/`TDN1` are pairs; `TC_P1`/`TC_N2` and `TG_PA`/`TG_NA` are not. `A.inDiffPair('TE_')` selects `TE_P1`/`TE_N1`; `A.inDiffPair('TF_P')` selects nothing on `TF_P1`/`TF_N1`. So KiCad skips a trailing run of digits and underscores before the polarity character, and the base is the text before that character. c0073's rule is the case of an empty run.
  5. *Class values*, a project from `synthesize_project` with the pair keys set by hand, the nets in classes by exact-name patterns, pairs 0.15 mm apart unless said:

     | class: clearance / pair gap / pair width / pair via gap (mm) | row | reported |
     |---|---|---|
     | DPA: 0.2 / 0.1 / 0.3 / 0.5 | CA_P/CA_N | nothing: the pair gap lowers the clearance inside the pair |
     | DPB: 0.2 / 0.25 / 0.2 / 0.25 | CB_P/CB_N | `clearance` "netclass 'DPB' clearance 0.2000 mm; actual 0.1500 mm" |
     | DPA | CC_A/CC_B, which do not pair | `clearance` (netclass 'DPA') |
     | DPC: 0.1 / 0.4 / 0.3 / 0.25 | CF_P/CF_N of 0.2 mm tracks | nothing: the pair gap and width are no limits |
     | DPA | two 0.6 mm vias of a pair, 0.3 mm apart | nothing: the via gap is no limit |

  6. *Custom rules against the class values* (class DPA unless said):

     | set-up | row | reported |
     |---|---|---|
     | a board-wide custom `clearance (min 0.2mm)` | CA, 0.15 mm | `clearance` "rule 'board' clearance 0.2000 mm; actual 0.1500 mm" |
     | the same, then `clearance (min 0.1mm)` on `A.inDiffPair('CA') && B.inDiffPair('CA')` | CA | nothing; CC still reported |
     | the same with `A.inDiffPair('CB') && AB.isCoupledDiffPair()` | CB (DPB) | nothing |
     | no board rule; `diff_pair_gap (min 0.1mm)` on CB | CB | `clearance` (netclass 'DPB'): a gap rule does not lower the clearance |
     | project `min_clearance` 0.12 mm | 0.11 mm; 0.13 mm | `clearance` "board minimum clearance 0.1200 mm" and `diff_pair_gap_out_of_range` "netclass 'DPA' (diff pair) minimum gap 0.1200 mm"; nothing |
     | project `min_clearance` 0.2 mm and the pair clearance rule (min 0.1 mm) | 0.15 mm | `diff_pair_gap_out_of_range` "netclass 'DPA' (diff pair) minimum gap 0.2000 mm", no `clearance` |
     | the same, then `diff_pair_gap (min 0.1mm)` on the pair | 0.15 mm | nothing |

  None of these benches is committed; task group 1 turns every row into a recorded probe. The measurements were made on the branch `review-roadmap-complex-board` and were not repeated on `dev`; the board and rules writers they used did not change in what these rows read (the kinds and the selector are new), and task group 1 repeats every row on `dev` before any table is filled.
- **Constraints.** Stdlib only, integers only, no value shipped (plan D6). A kind and a selector are written for a major only when a probe proved them there.

## Goals / Non-Goals

**Goals:**
- A script declares a pair's class values and its gap, uncoupled length, skew and length limits, and KiCad's DRC checks each on both majors.
- What KiCad takes as a pair, Fenolite takes as a pair, by one measured rule.
- `check` judges the clearance inside a pair as KiCad's DRC does.

**Non-Goals:**
- Everything under "Non-goals" in the proposal.
- Approximating a selector, as in c0071: a selector outside a kind's grammar is refused.
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
