lgili/Fenolite/openspec/changes/c0104-diff-pair-constraints/proposal.md

## Why

A script can declare a differential pair (`DiffPair`, `USB2`); c0073 warns when KiCad would not pair its names. Nothing else reaches KiCad: every class gets the template's pair width, gap and via gap, and no rule kind checks a pair. The review of 2026-10-05 found this as one of the gaps to a complex board (milestone v0.4, `docs/roadmap.md`, "v0.4: proposals on other branches"); the plan had these kinds at v0.6. On `origin/dev` at `9aba2dff` the gap is still whole: `model.rules.RuleKind` holds the twelve kinds of c0071, `SelectorOp` has no pair leaf, and `NetClass` holds four values.

Probes on 9.0.9 and 10.0.6 (2026-10-05, same results) show:

- No pair object: two nets pair by name, and `A.inDiffPair('<base>')` selects them. Digits and underscores may follow the P or N (`D_P0`/`D_N0`), which c0073's rule misses.
- Only custom rules check a pair: `diff_pair_gap` (min, max), `diff_pair_uncoupled` (max), `skew` (max; within each pair with `(within_diff_pairs)`) and `length` (min, max). `opt` is never checked.
- Class pair values are router defaults, not limits. A class pair gap below the class clearance lowers the clearance inside a pair, unless a custom clearance rule governs it.

## What Changes
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
