lgili/Fenolite/openspec/changes/c0105-impedance-targets/design.md

## Context

- **Scope.** The review of 2026-10-05 named the gaps to a complex board; since 2026-10-07 the group is milestone v0.4 (`docs/roadmap.md`, "Milestone names" and "v0.4: proposals on other branches", where the row of c0105 holds its id and slug only). The gap this change closes, in the review's words: "an impedance target per class or pair; width and gap from the stack-up, or KiCad 10 tuning profiles; the impedance table for the fabricator". It depends on c0101 (the stack-up in the model and in the board file) and c0104 (pairs lowered to KiCad, and the rule kind for the pair gap).
- **What exists** on `origin/dev` at `9aba2dff` (2026-10-07).
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
