lgili/Fenolite/openspec/changes/c0137-schematic-pin-frame-order/tasks.md

## 0. Entry check

- [x] 0.1 Find every place that maps a pin's library offset to the sheet. Proof: `grep -rn "pin_point\|turned(\|label_angle(" src tests tools`; `design.md`, Context.
  - 2026-10-08: one transform, `schlayout.turned`, behind `pin_point` and `label_angle`; every caller (`schlayout` boxes, `schgen`, `sch._text_anchor`, `sch_netlist._pins`, the test helpers) goes through them. No copy.
- [x] 0.2 Look for the infra commit of the v0.4 notes. Proof: `git log origin/v04 --oneline | grep -i 39a3668`; `git log origin/v04 --oneline -S pin_point`.
  - 2026-10-08: no object `39a36681` in the clone; the infra commit near the schematic oracle on `origin/v04` is 7d8c0d0a (the docker form of `FENOLITE_KICAD_CLI` for the probe runner). It touches no pin point and is not needed here (`design.md`, Context).
- [x] 0.3 Measure the order on the corpus. Proof: `uv run python tools/corpus_fetch.py --uses sch` and `--uses sch-9`; a scratch script (not a product test) over the fetched sheets.
  - 2026-10-08: 132 and 92 items, 0 failed. 125 sheets read; 188 instances mirrored and turned by 90° or 270° (all `mirror x`): 142 touch more at the rotate-first points, 45 tie, 1 the other way (explained); 336 against 76 pin points; 20 sheets of both tags. Mirror axis at 0°: 1 943 against 336 (`design.md`, Measurement).

## 1. Facts and register

- [x] 1.1 The fact in `docs/formats/kicad/schematic.md` (`CORPUS-VERIFIED`, S-0058 with the corpus rows), the correction of the `H-K-SCH-PINFRAME` row there and in `docs/hypotheses.md`, the row `H-K-SCH-PINFRAME-ORDER`, the c0137 note of S-0058 in `docs/evidence/sources.md` and the probe table of `docs/evidence/kicad-schematic.md`. Proof: `uv run pytest tests/unit/test_hypotheses_register.py tests/unit/test_evidence_register.py tests/unit/test_capability_evidence.py -q`.
  - 2026-10-08: passed with the gates of 4.1 (135 passed, 5 skipped).

## 2. The fix

- [x] 2.1 `schlayout.turned` rotates, then mirrors; docstrings of `turned`, `pin_point` and `PROVED_FRAMES`. Proof: `uv run pytest tests/unit/backends/kicad/test_pin_frame_order.py tests/unit/backends/kicad/test_schlayout.py -q`.
  - 2026-10-08: 50 passed after the one assertion of `test_schlayout.py` that held the old order (`pin_point(origin, left, 90, "y")`) was turned round.
- [x] 2.2 `sch_netlist.FRAME_ORDER_EVIDENCE`, `frame_evidence`, its use in `evidence_of` and in the build envelope. Proof: `uv run pytest tests/unit/backends/kicad/test_pin_frame_order.py -q`.
  - 2026-10-08: 34 passed: the twelve frames of `pin_point` and of `label_angle` by hand, the two orders differ only at the four mirrored quarter turns, the authored sheet of `tests/_pinframe.py` read back through the own netlist and its control, the evidence, and the blink with `U1` placed in five frames keeping its nets.
- [x] 2.3 Pinned builds and the KiCad backend tests unchanged. Proof: `uv run pytest tests/unit/backends/kicad tests/unit/lens/test_build_bytes_pinned.py tests/unit/lens/test_schplacements.py tests/unit/lens/test_build_schematic.py tests/unit/lens/test_build_netlist_guard.py -q -n 2 -m "not needs_kicad and not needs_corpus and not needs_libs"`; `git diff --stat origin/dev -- tests/data`.
  - 2026-10-08: 2442 passed, 1 skipped; `test_build_bytes_pinned.py` alone 83 passed; no pin moved and no file under `tests/data` changed (no pinned design and no golden places a unit mirrored).

## 3. Tests against KiCad

- [x] 3.1 `tests/kicad/schematic/test_stacked_corpus.py` without `left_out`. Proof: collected and skipped here (no `kicad-cli`); the candidates counted without `kicad-cli` with the test's own selection.
  - 2026-10-08: 49 skipped (`kicad-cli` not found) for 3.1 and 3.2 together. Candidates: `kicad-demo-10-0-6-sch-017` 10 before and 10 after, the same stacks; no other root project of 9 or 10 has one; `PINNED` unchanged.
- [x] 3.2 `tests/kicad/schematic/test_pin_frame_oracle.py` (`needs_kicad`) and the authored sheet `tests/_pinframe.py`. Proof: collected and skipped here; the sheet is read back by the unit tests of 2.2 for target 10.
- [x] 3.3 `FENOLITE_REQUIRE=kicad uv run pytest tests/kicad/schematic/test_pin_frame_oracle.py -rA` on 9.0.9 and 10.0.6; then `H-K-SCH-PINFRAME-ORDER` becomes `KICAD-VERIFIED (9.0.x, 10.0.x)` and `FRAME_ORDER_EVIDENCE` follows. Owed: CI (kicad-9/kicad-10).
  - 2026-10-08, CI run https://github.com/lgili/Fenolite/actions/runs/37836186018 of `release-0.4.0` at `32a19b3`: the `kicad-9` job (`kicad-cli` 9.0.9, `FENOLITE_REQUIRE=kicad`, `-rA`) prints `PASSED` for `test_every_pin_is_on_the_net_of_its_frame` and `test_the_control_tells_the_two_orders_apart`; the `kicad-10` job (10.0.6, `FENOLITE_REQUIRE=kicad,corpus`) passed with no skip of the file (3019 passed, 146 skipped, none in it). `H-K-SCH-PINFRAME-ORDER` is now `KICAD-VERIFIED (9.0.x, 10.0.x)` in `docs/hypotheses.md` and in its fact row of `docs/formats/kicad/schematic.md`, `FRAME_ORDER_EVIDENCE` is `Level.KICAD_VERIFIED`, `docs/schematic.md` names the new label and `docs/evidence/matrix.md` is regenerated.
- [x] 3.4 `FENOLITE_REQUIRE=kicad,corpus uv run pytest tests/kicad/schematic/test_stacked_corpus.py -rs` on 10.0.6 (and 9.0.9, where c0123's task 10.5 waits). Owed: CI (kicad-9/kicad-10).
  - 2026-10-08, CI run https://github.com/lgili/Fenolite/actions/runs/37836186018: on 10.0.6 (`kicad-10` job, `kicad,corpus` required) 46 of the 47 roots skip with their reasons (13 no project at the tag, 1 older format, 32 no stack) and the pinned `kicad-demo-10-0-6-sch-017` passes with its stacks, the mirrored and turned instances included; on 9.0.9 (`kicad-9` job) all 47 skip (12 no project at tag 9.0.9.1, 5 older format, 30 no stack), so 9.0.9 judges no stack, as c0123's task 10.5 says.
- [x] 3.5 `tests/kicad/schematic/test_naming_probes.py` and `tests/kicad/test_probe_results.py` on both majors: the `sch-pin-frame-*` outcomes stay `absent`. Owed: CI (kicad-9/kicad-10).
  - 2026-10-08, CI run https://github.com/lgili/Fenolite/actions/runs/37836186018: `test_naming_probes.py::test_pin_frame` and `test_probe_results.py::test_probe_results` `PASSED` in the `kicad-9` job (9.0.9) and passed with no skip in the `kicad-10` job (10.0.6), so the twelve `sch-pin-frame-*` outcomes are still `absent` on both majors.

## 4. Documents and gates

- [x] 4.1 `docs/schematic.md` (placements file), `CHANGELOG.md`. Proof: `make check-fast`; every `uv run python tools/gen_*.py --check`; `uv run pytest tests/residue tests/corpus/test_manifest.py -q`; `openspec validate c0137-schematic-pin-frame-order --strict`.
  - 2026-10-08: `make check-fast` 9942 passed, 18 skipped (exit 0); the three `gen_*` tools exit 0 with `--check` (the matrix page regenerated for `FRAME_ORDER_EVIDENCE`); residue, manifest and the register tests 135 passed, 5 skipped; the change is valid (exit 0), its one note is that MODIFIED "Stacked pins of corpus sheets" waits for c0123's archive, and `validate --changes --strict` lists no error of it (its 5 known errors are those of c0084, c0085, c0086 and c0128).
- [x] 4.2 `make check` on the rebased branch before the merge.
  - 2026-10-08, on the release branch (`release-0.4.0`, `32a19b3` and the settlement commits of c0154, which change no code but this change's evidence label): `make check` exit 0 (ruff check all passed, 1772 files already formatted, pyright 0 errors, residue 0 hits with 11 waivers and the private gate skipped, `13828 passed, 2374 skipped in 1243.06s` on Python 3.11.15, 4 workers) (c0154, task 4.3). CI run https://github.com/lgili/Fenolite/actions/runs/37836186018 of `32a19b3` passed every job.
