lgili/Fenolite/openspec/changes/c0121-altium-component-bodies/tasks.md

Implementation waits until the batch of the write part of v0.3 (c0083 to c0092 and their follow-ups) is on `dev`; the base of the implementing branch is `dev` then, not the branch this proposal was written on.

## 0. Entry check

- [x] 0.1 Read `openspec list` and the requirements this change modifies where they stand: "Component bodies are reported" (c0085), "Imported boards are written from the model" and "RT-A2 on a written model" (c0090), in the living specs when those changes are archived and in their deltas otherwise. Write under this task, with the date: which of c0085, c0090 and c0043 are archived; whether another change (c0128 is the likely one) edited one of the three texts since 2026-10-06, and then copy its text and apply this change's edit again; and whether the maintainer reversed one of the "Decisions (2026-10-06)" of the design, which is then switched as its entry says. Proof: `openspec validate c0121-altium-component-bodies --strict --no-interactive` passes.
  - 2026-10-07: done. `openspec list`: c0085, c0090, c0127 and c0128 are on `dev` and not archived; c0043 is archived (2026-10-05). "Component bodies are reported" stands in c0085's delta, "RT-A2 on a written model" in c0090's, and neither was edited since. "Imported boards are written from the model" was modified by c0127 and then by c0128: the delta here now starts from c0128's text, the last of them, with this change's edits applied again; c0126 (proposed only) modifies the same requirement from c0090's text and takes the newer text when it is implemented. The clauses of c0099 that decision 9 no longer allows were removed from "Component bodies are reported". No decision of "Decisions (2026-10-06)" was reversed. `openspec validate c0121-altium-component-bodies --strict --no-interactive`: valid.

## 1. Fact rows first (no writer code before this group is ticked)

- [x] 1.1 Register S-0570 and S-0571 in `docs/evidence/sources.md` (licence, what was read, the date; c0121 keeps S-0570 for the documentation page that c0099 also reads, but if c0099 is on `dev` first, cite c0099's id for that page instead and leave S-0570 unused) and the eight rows `H-A-PCBX-BODY-*` of the design in `docs/hypotheses.md` (backend `altium`, level `INFERRED`); add a row to `LEGAL-ANNEX.md`. Proof: `uv run pytest tests/unit/test_hypotheses_register.py tests/unit/test_provenance.py`.
  - 2026-10-07: done before any writer code. S-0570 and S-0571 are registered (both pages read again on 2026-10-07; c0099 is not on `dev`, so S-0570 is used), the eight rows `H-A-PCBX-BODY-*` are in the register and a row is in `LEGAL-ANNEX.md`. `uv run pytest tests/unit/test_hypotheses_register.py tests/unit/test_provenance.py -q -n 0`: 44 passed.
- [x] 1.2 Write `tests/corpus/test_altium_bodies.py` from the measurement of the design ("Measured"): the kinds per document, the binary fields, the key order, every constant, the links between keys, the twin record, the centre of the bounding box, the `Models` entries, and the count of repositories. It prints counts and value forms only. Where the run differs from a number of the design, correct the design and say so under "Found on <date>". Proof: `FENOLITE_REQUIRE=corpus FENOLITE_HEAVY=1 uv run pytest tests/corpus/test_altium_bodies.py -rA` (say whether the heavy row ran).
  - 2026-10-07: done before any writer code. The measurement was repeated with throwaway scripts kept outside the repository and then pinned in `tests/corpus/test_altium_bodies.py`: per document the bodies of each kind and the entries of `Models`, every asserted row on every record, and the counted rows as numbers per document whose sums are the numbers of the page. `FENOLITE_REQUIRE=corpus FENOLITE_HEAVY=1 uv run pytest tests/corpus/test_altium_bodies.py -rA -q -n 0`: 13 passed, **with the heavy row** (one run). No number of the design's field table differs; two sentences of "Measured" are corrected ("Found on 2026-10-07", 1).
- [x] 1.3 Write the section "Written form of an extruded body" of `docs/formats/altium/pcb-bodies.md`: one row per binary field and per key of the field table of the design, with the value rule, the sources, the label that task 1.2 earned and the hypothesis; the two stand-in rows; the rows of a library body; the sentence that 1265 of the 1272 records come from one repository; and what is not written (model bodies, the optional keys). Proof: `uv run pytest tests/unit/test_format_facts.py tests/unit/test_provenance.py tests/consistency`.
  - 2026-10-07: done before any writer code: 8 rows of binary fields, 35 key rows (two marked stand-in, under `H-A-PCBX-BODY-OPEN`), 3 rows of what is written of a model body (the layer rule, the short form, the library), and what is not written. The section opens with how far the evidence goes. `uv run pytest tests/unit/test_format_facts.py tests/unit/test_provenance.py tests/unit/test_hypotheses_register.py tests/consistency/test_cli_consistency.py -q -n 2`: passed (434 passed and 15 skipped in the run of the closing, with eight more files).

## 2. The record and the document

- [x] 2.1 Write `pcbrecords.BODY_KEYS`, `body_record` and `body_model_id`, and the test that compares `BODY_KEYS` with the rows of task 1.3 (scenarios "Keys and rows agree", "Rectangle on a top component", "Short form"). Proof: `uv run pytest tests/unit/backends/altium/test_pcb_bodies.py`; `uv run pyright src`.
  - 2026-10-07: done. `uv run pytest tests/unit/backends/altium/test_pcb_bodies.py -q -n 0`: 20 passed (`-k facts`: 3). `uv run pyright src/fenolite/backends/altium`: 0 errors (the whole `pyright src` is part of `make check-fast`, task 6.3).
- [x] 2.2 Write `pcbdoc.PlacedBody`, `PcbDocSpec.bodies`, `body_problem` and the two storages (scenario "Document with three bodies"); a spec without bodies keeps its bytes. Proof: `uv run pytest tests/unit/backends/altium -k "bodies or pcbdoc"`.
  - 2026-10-07: done. `uv run pytest tests/unit/backends/altium -q -n 2`: 2300 passed, 1 skipped (the whole folder, which holds `-k "bodies or pcbdoc"`). The independent reader of the tests (`tests/_altium_pcb_read.py`) refused a body storage with data and a primitive of type 12: it now decodes a body on its own, from the fact page, and `test_pcb_own_files.py` compares both readers on `body2`.

## 3. Build and model writer

- [x] 3.1 Add `--altium-bodies` and `bodies=` to the build, the lens and `lower`; lower the bodies with their reasons; `result.pcb.bodies`; reword the entry of `altium.not-lowered` in `explain.toml` where it says that no body is written (scenarios of "Component bodies are reported" and of "Component bodies in an Altium build", but "Sample with bodies"). Proof: `uv run pytest tests/unit/lens/test_altium_bodies.py tests/unit/lens/test_altium_pcb_complete.py tests/unit/cli/test_build_altium.py tests/unit/cli/test_explain_cmd.py tests/unit/backends/altium/test_lower.py`.
  - 2026-10-07: done. The option, `bodies=` on `build_altium`, `write_model`, `from_design`, `write_design`, `AltiumBackend.write` and `model_roundtrip`; `result.pcb.bodies`. The result of the command did not hold `pcb` at all: it does now ("Found on 2026-10-07", 4). `explain.toml`: one clause added ("Found", 12). `uv run pytest tests/unit/lens/test_altium_bodies.py tests/unit/lens/test_altium_pcb_complete.py tests/unit/cli/test_build_altium.py tests/unit/cli/test_explain_cmd.py tests/unit/backends/altium/test_lower.py -q -n 2`: passed (the lens files in a run of 22 Altium lens files, 410 passed and 1 skipped; the CLI files in a run of 18 files, 238 passed; `test_explain_cmd.py` 8 passed).
- [x] 3.2 Write the bodies of a library footprint (scenario "Footprint with a body"). First item of the cut order: when cut, write why under this task and leave "Component bodies of a library footprint" open. Proof: `uv run pytest tests/unit/backends/altium/test_pcblib_bodies.py tests/unit/backends/altium -k pcblib`.
  - 2026-10-07: done, not cut. `uv run pytest tests/unit/backends/altium/test_pcblib_bodies.py -q -n 0`: 3 passed; the folder run of 2.2 holds `-k pcblib`. The body is the last primitive, counted in the header, without a unique-id entry, as the one saved library with a body has it ("Found", 10).

## 4. Sample, read-back, round trips, oracle

- [x] 4.1 Author `tests/_altium_body2.py` and commit the built files under `tests/data/altium/body2/` with their rows in `tests/data/MANIFEST.toml` (scenario "Sample with bodies"); check that no other committed sample changed. Proof: `uv run pytest tests/unit/lens/test_altium_bodies.py -k body2` and `uv run pytest tests/unit/lens -k "altium and samples"`; then, after `git add -A`, `uv run pytest tests/corpus/test_manifest.py tests/residue` and `git status --short tests/data/altium` lists only `body2/`.
  - 2026-10-07: done. `tests/data/altium/body2/` holds the five files of the build with `--altium-bodies extruded`, with five rows in `tests/data/MANIFEST.toml`. `uv run pytest tests/unit/lens/test_altium_bodies.py -k body2`: passed; `test_altium_samples_of_earlier_changes_keep_their_bytes` passed in the lens run of 3.1; after `git add -A`, `uv run pytest tests/corpus/test_manifest.py tests/residue -q -n 2`: 85 passed after one waiver of the residue scan for `body2.PcbLib` ("Found", 13), and `git status --short tests/data/altium` lists only `body2/`.
- [x] 4.2 Write `BODY_SCOPE` and the comparison of the kind `body` in RT-A2 and RT-A3 (scenarios "Own sample" and "A moved vertex is caught"). Proof: `uv run pytest tests/unit/lens/test_altium_bodies.py tests/unit/lens/test_altium_rta2.py tests/unit/backends/altium -k "rta or roundtrip"`.
  - 2026-10-07: done. `roundtrip.BODY_SCOPE`; the comparison is `bodydiff.py` ("Found", 8 and 9). `uv run pytest tests/unit/lens/test_altium_bodies.py tests/unit/lens/test_altium_rta2.py -q -n 2` and the folder run of 2.2 (`-k "rta or roundtrip"`): passed; `tests/unit/checks/test_rta2.py`, `test_rta3.py` and `test_documents.py` passed.
- [x] 4.3 Run the corpus documents with bodies on and write the table into `docs/evidence/altium-roundtrip.md` under "RT-A3" (scenario "Corpus documents with bodies"); the table of the default must not move. Third item of the cut order. Proof: `FENOLITE_REQUIRE=corpus uv run pytest tests/corpus/test_altium_rta3.py tests/corpus/test_altium_roundtrip.py -rA` (say whether `FENOLITE_HEAVY=1` was set).
  - 2026-10-07: done for the seven documents that are not heavy; **the heavy row with bodies is owed** (a long run). `FENOLITE_REQUIRE=corpus uv run pytest tests/corpus/test_altium_rta3.py tests/corpus/test_altium_roundtrip.py tests/corpus/test_altium_bodies.py -q -n 2` **without** `FENOLITE_HEAVY=1`: 98 passed, 6 skipped. With bodies the seven trips are equal and write 2, 0, 5, 30, 0, 0 and 18 bodies (55 of 446); the 391 others name a model. The table of the default did not move. The evidence page marks the heavy row as expected, not measured.
  - 2026-10-07: the slot: `FENOLITE_REQUIRE=corpus FENOLITE_HEAVY=1 uv run pytest tests/corpus/test_altium_rta3.py tests/corpus/test_altium_roundtrip.py tests/corpus/test_altium_bodies.py -rA -n 2` **with** `FENOLITE_HEAVY=1`: 104 passed, exit code 0. The heavy document with bodies is equal: 1217 bodies written, 81 not written (each names a 3D model). The evidence page and the row `H-A-PCBX-BODY-READBACK` hold the measured numbers; nothing is owed.
- [x] 4.4 Write `tests/_bodycases.py` and `tests/kicad/altium/test_pcb_bodies_oracle.py`, and record the probe `altium-pcbx-bodies` for KiCad 10.0.6. Proof: `uv run pytest tests/kicad/altium/test_pcb_bodies_oracle.py tests/kicad/test_probe_results.py -rA`.
  - 2026-10-07: written and run as one file; **`tests/kicad/test_probe_results.py` is owed** (it runs every probe of the major, a long run), so the task stays open. `uv run pytest tests/kicad/altium/test_pcb_bodies_oracle.py -q -n 0 -rA`: 4 passed with `kicad-cli` 10.0.6 (macOS), three times in a row; the probe `altium-pcbx-bodies` is `equal` and is recorded in `docs/evidence/kicad/probes/10.0.6.json` by hand. Levels 1 to 4, not 5, and the boards are compared as sets of lines ("Found", 11).
  - 2026-10-07: the slot: `uv run pytest tests/kicad/test_probe_results.py tests/kicad/altium -q -n 2`: 95 passed, exit code 0, `kicad-cli` 10.0.6 (macOS). The probe file holds `altium-pcbx-bodies` `equal` and no outcome drifted.

## 5. Step X8 and pages

- [x] 5.1 Replace the line of step X8 in Part X of `docs/evidence/altium-pcb.md` by the steps X8.1 to X8.7 of the design, with the table of values and the SHA-256 of the files; add the tests `-k golden` (writes both file sets into the folder of `FENOLITE_ALTIUM_BODY2`), `-k protocol` (the digests of the page) and `-k saved_report` (counts of a file that Altium saved); build the two sets into `~/fenolite-altium-checks/session-2/X8-bodies/` (`saved/` and `short/`) and add step X8 with both forms to the list of **session 2** of the maintainer's Altium work on that page, not to session 1, whose folder he already has; change the sentence of `verify/kit/steps.py` that says no step reads bodies. The `short` set is the second item of the cut order. Proof: `uv run pytest tests/unit/lens/test_altium_bodies.py -k "golden or protocol"` and `uv run pytest tests/unit/verify`.
  - 2026-10-07: done, the `short` set not cut. Step X8 of Part X holds the steps X8.1 to X8.7, the table of values, the SHA-256 of both sets, session 2 and Altium Designer 26, and the sentence that the option stays off until the step is reported. The page had no list of session 2: step X8 names its session itself. Both sets and a `README.md` are built in `~/fenolite-altium-checks/session-2/X8-bodies/` (`saved/`, `short/`); `session-1` was not touched. `uv run pytest tests/unit/lens/test_altium_bodies.py -k "golden or protocol"`: passed; `uv run pytest tests/unit/verify/kit tests/unit/cli/test_explain_cmd.py tests/unit/cli/test_kit_cmd.py -q -n 2`: 67 passed with the reworded sentence of `verify/kit/steps.py` (one failure of the explain table was the length of the entry, corrected); the four other files of `tests/unit/verify` passed in the run of the closing.
- [ ] 5.2 Hand the files to the maintainer with the steps; record his report under "Reports" of `docs/evidence/altium-pcb.md` (tool as `AD <major>.<minor>`, date, one generic outcome per step, no artefact) and in `docs/hypotheses.md`; give a refuted row a registered successor. OPEN until Altium was run; nothing is marked `ALTIUM-VERIFIED` before. Proof: `uv run pytest tests/unit/test_hypotheses_register.py tests/unit/test_provenance.py`.
  - 2026-10-07: OPEN: Altium was not run. The files are in `~/fenolite-altium-checks/session-2/X8-bodies/`. Nothing is marked `ALTIUM-VERIFIED`.
  - 2026-10-08: step X8 was not done in the maintainer's session 2 (`docs/evidence/altium-pcb.md`, "Session 2 of 2026-10-08"); owed after 0.3.0, and `--altium-bodies extruded` stays off by default.
- [x] 5.3 Document the option, what is written of a body and what is not, in `docs/altium.md` (the rows "component bodies" of "Complete board" and of the written scope) and in `docs/cli-contract.md`. Proof: `uv run pytest tests/consistency tests/unit/test_repo_layout.py`.
  - 2026-10-07: done: `docs/altium.md` (the row of "Complete board", the new paragraph "Component bodies", the rows of the written scope and of the write of a model) and `docs/cli-contract.md` (the option, the synopsis, `result.pcb.bodies`). `uv run pytest tests/consistency/test_cli_consistency.py tests/unit/test_repo_layout.py -q -n 2`: passed in the run of the closing.

## 6. Closing

- [x] 6.1 Update the evidence: every row of this change holds its measured level and result in `docs/hypotheses.md`; `pcbdoc.EVIDENCE` names the rows a written body rests on; `uv run python tools/gen_evidence_matrix.py` as the last generated edit. Proof: `uv run pytest tests/unit/test_provenance.py tests/unit/test_hypotheses_register.py tests/unit/backends/test_evidence_declared.py tests/unit/test_evidence_matrix_page.py`.
  - 2026-10-07: done. `H-A-PCBX-BODY-FORM` and `-2D` are `CORPUS-VERIFIED` by their rule, and say that they are thin; `-READBACK` is `INFERRED` and confirmed; `-KICAD` is `ORACLE-VERIFIED(kicad-cli)` for 10.0.6; `-OPEN`, `-SHORT`, `-ID` and `-LIB` are `INFERRED` and pending. `pcbdoc.EVIDENCE` and `pcblib.EVIDENCE` name the rows; `pcbrecords.EVIDENCE` is pinned to its thirteen rows by a test and was left; the build's evidence gains `pcblib.EVIDENCE`. The matrix was regenerated last. `uv run pytest tests/unit/test_provenance.py tests/unit/test_hypotheses_register.py tests/unit/backends/test_evidence_declared.py tests/unit/test_evidence_matrix_page.py tests/unit/lens/test_altium_build.py -q -n 2`: passed.
- [x] 6.2 Add to `CHANGELOG.md` under Unreleased: "An Altium build writes the extruded component bodies of a board on request (`--altium-bodies extruded`, off by default); bodies that name a 3D model are reported". Set the row of this change in `docs/roadmap.md` to its state. Proof: `git diff --stat CHANGELOG.md docs/roadmap.md` lists both files.
  - 2026-10-07: done: one line under `[Unreleased]`, which says that the evidence is thin and that the result gains `pcb`; the row of the change in `docs/roadmap.md`. `git diff --stat CHANGELOG.md docs/roadmap.md` lists both.
- [x] 6.3 Run the residue and the fast suite. Proof: `uv run pytest tests/residue tests/corpus/test_manifest.py` and `uv run python tools/residue/scan.py` exit 0; `make check-fast` passes; `openspec validate --all --strict` passes; `python3 tools/dco_check.py <base>..HEAD` prints nothing. The full `make check` and `gh pr checks` are the coordinator's, once, at the merge.
  - 2026-10-07: open until the slot for the long runs: `make check-fast PYTEST_WORKERS=4`, the unit suite on Python 3.11, the heavy corpus row with bodies and `tests/kicad/test_probe_results.py` are owed. Run so far: `ruff check` and `ruff format --check` on `src` and on the test files touched, `pyright` on the packages touched, `uv run python tools/residue/scan.py` (0 hits), `tests/residue` and `tests/corpus/test_manifest.py` after `git add -A`, `openspec validate --all --strict`.
  - 2026-10-07: the slot, on the branch rebased onto `origin/dev` `a32dcfa4`, one run after another: `make check-fast PYTEST_WORKERS=4`: 9430 passed, 18 skipped, exit code 0; `uv run --isolated --python 3.11 --extra dev pytest tests/unit -q -n 4 -p no:cacheprovider`: 9151 passed, 3 skipped, exit code 0; the heavy corpus run of 4.3 and the oracle run of 4.4. After `git add -A`: `tests/residue`, `tests/corpus/test_manifest.py`, `tests/unit/test_evidence_matrix_page.py`, `uv run python tools/residue/scan.py`, `openspec validate --all --strict` and `python3 tools/dco_check.py origin/dev..HEAD` (the last on the amended commit). The full `make check` and `gh pr checks` are the coordinator's.
