lgili/Fenolite/openspec/changes/c0079-agent-guide/tasks.md

## 0. Entry check

- [x] 0.1 Read the living `cli-contract`, `release-gate` and `package-layering` specs and `openspec list`. Write under this task, with the date and the commit:
  - that `0.3.0` is released and that c0077 is archived (the starter depends on it; stop here otherwise);
  - whether c0092 is archived (it edits `agent/SKILL.md` and decides the status of the Altium write kinds that the start page points at) and, for every open change that names `agent/SKILL.md` (`grep -rln "agent/SKILL.md" openspec/changes --exclude-dir=archive`), the task that names it: change the path to `src/fenolite/agent/skill/SKILL.md` in this change's first commit;
  - whether c0078 is archived (the start page then names `fenolite fetch freerouting`, else it does not);
  - the public commands and the global flags of the day, from `fenolite capabilities --json --no-tools` and `fenolite build --help`, and the size of that reply;
  - whether another change modified "Agent guide is executable" since this proposal (then regenerate the MODIFIED delta from the living text).
  Register the page that documents the first row of `AGENT_DIRS` in `docs/evidence/sources.md` as S-0617. Proof: `openspec validate c0079-agent-guide --strict --no-interactive` passes after any re-base; `uv run pytest tests/unit/test_provenance.py tests/unit/verify/test_cited_ids.py -q`; `grep -c '^| S-0617 ' docs/evidence/sources.md` prints `1`.
  - **Entry note, 2026-10-07, on the integration branch `v04` at `f36e08d9` (`dev` at `c69f8c6b` plus the v0.4 proposals). The task stays open: two of its conditions do not hold on this base.**
    - `0.3.0` is not released (the package is 0.2.1) and c0077 is not archived: it is open and another lane implements it. The coordinator decided to implement, on this base, every task that does not need c0077. Waiting for c0077: task 4.2 (the block on KiCad, since `check` on a catalog-only board reports `netlist.assignment-differs` and `netlist.uncovered` without it) and task 6.1.
    - c0092 is not archived. The start page states no fixed word for the Altium target and points at `capabilities --json` (`result.matrix`, `experimental`), so it holds before and after c0092.
    - c0078 is not archived: the start page does not name `fenolite fetch`.
    - Open changes that name `agent/SKILL.md` (`grep -rln "agent/SKILL.md" openspec/changes --exclude-dir=archive`): c0078 (task 5.2), c0080 (proposal), c0092 (proposal, task 5.1), c0108 (design, task 7.1), c0120 (design, task 7.1) and c0141 (task 3.1). Their paths are **not** edited here: other lanes implement several of them tonight on sibling branches. The coordinator changes each to `src/fenolite/agent/skill/SKILL.md` when the branches are stacked.
    - Measured: `fenolite capabilities --json --no-tools` prints 21 294 bytes (`matrix` 12 141, `experimental` 3 470, `commands` 3 137, `backends` 1 305, `routers` 567, `extras` 293). It lists 30 public commands (`analyze`, `bom`, `build`, `capabilities`, `catalog`, `check`, `diff`, `doctor`, `equivalent`, `explain`, `export`, `fill`, `fmt`, `inspect`, `kit`, `manifest`, `neighbors`, `net`, `netlist`, `pads`, `parity`, `place`, `pnp`, `region`, `render`, `restore`, `roundtrip`, `route`, `sync`, `template`) and the hidden `_echo`. The global flags of `fenolite build --help` are `--json`, `--text`, `--fields`, `--limit`, `--cursor`, `--format`, `--seed`, `--timestamp`, `--no-backup`, `--kicad-version` and `--allow-lossy`.
    - No other change modifies "Agent guide is executable": the name is in this change only. `openspec validate c0079-agent-guide --strict --no-interactive` passes.
    - **After the rebase onto the wave-1 tip `7392159d` (2026-10-07):** c0077 and c0078 are on the base (implemented, not archived), so the start page names `fenolite fetch freerouting` and carries the route and report-limit sentences that c0078, c0108 and c0141 wrote into the old file. S-0617 is registered: the page "Extend Claude with skills" (https://code.claude.com/docs/en/skills) was read on 2026-10-07 for the one fact of the row `claude-code` → `.claude/skills`; the id was free and the row is the last of the table. The task stays open for what is not this change's to do: `0.3.0` is not released, c0077 is not archived, and the paths in the other open changes are the coordinator's.
    - **Closing note, 2026-10-08, base `04ef42a` (`v04`, rebased onto 0.3.0 in `9fb3513`).** `0.3.0` is released: `fenolite --version` prints `0.3.0`, `CHANGELOG.md` holds `## [0.3.0] - 2026-10-08`, and the release record is the archived change `2026-10-08-c0150-release-0-3-0`. c0077 is not archived but is implemented on this base and closed for 0.4 in the same pass, which the maintainer's decision of 2026-10-08 (release 0.4 is prepared from `v04`) makes enough for the starter. c0092 is not archived; the start page still points at `capabilities --json` for the Altium kinds, so it holds either way. c0078 is implemented on the base, and the start page names `fenolite fetch freerouting`. The open tasks that name the old path now name `src/fenolite/agent/skill/SKILL.md`: c0092 task 5.1 and c0141 task 3.1 (the other hits are ticked tasks, designs and proposals that record what was done or read at `9aba2dff`, and stay as written). Measured: `fenolite capabilities --json --no-tools` prints 23 371 bytes (`result` 23 145) and lists 37 public commands (`analyze`, `bom`, `build`, `capabilities`, `catalog`, `check`, `diff`, `doctor`, `equivalent`, `explain`, `export`, `fetch`, `fill`, `fmt`, `guide`, `impedance`, `init`, `inspect`, `kit`, `manifest`, `models`, `neighbors`, `net`, `netlist`, `pads`, `parity`, `place`, `pnp`, `region`, `render`, `restore`, `roundtrip`, `route`, `skill`, `sync`, `template`, `testpoints`) and the hidden `_echo`; the global flags of `fenolite build --help` are `--json`, `--text`, `--fields`, `--limit`, `--cursor`, `--format`, `--progress`, `--seed`, `--timestamp`, `--no-backup`, `--kicad-version` and `--allow-lossy`. No archive modified "Agent guide is executable" (the archives of 0.2.2 and 0.3.0 leave it as it was), so the delta stands. S-0617 is registered (`grep -c '^| S-0617 ' docs/evidence/sources.md` prints `1`). Proofs: `openspec validate c0079-agent-guide --strict --no-interactive` gives no error (long-requirement warnings only); `uv run pytest tests/unit/test_provenance.py tests/unit/verify/test_cited_ids.py -q` passes.
- [x] 0.2 Add the row `H-K-GUIDE-STARTER` to `docs/hypotheses.md` (backend `kicad`, level `INFERRED`, the test and criterion of `design.md`, result `pending`). Proof: `uv run pytest tests/unit/test_hypotheses_register.py -q`; `grep -c '^| H-K-GUIDE-STARTER ' docs/hypotheses.md` prints `1`.
  - Done on 2026-10-07 after the rebase: the row is the last of the table and `uv run pytest tests/unit/test_hypotheses_register.py -q` passes on the base `7392159d`.

## 1. The loader

- [x] 1.1 Create `src/fenolite/agent/` with `__init__.py` and `guide.py` (front matter, `pages`, `page`, `skill_files`, `GuideError`), move `agent/SKILL.md` to `src/fenolite/agent/skill/SKILL.md` with `git mv`, and write `tests/unit/agent/test_guide.py` (scenarios "Guide loads from the installed package", "Malformed page is refused", "Guide stays stdlib-only"). Keep the file's text for now and point `tests/unit/test_agent_skill.py` and `tests/routing/test_acceptance_loop.py` at the new path. Proof: `uv run pytest tests/unit/agent tests/unit/test_agent_skill.py tests/unit/test_import_graph.py tests/unit/test_spdx_headers.py -q`; `uv run pyright src`; `uv build` lists `fenolite/agent/skill/SKILL.md` in the wheel.
- [x] 1.2 Add starters to `guide` (`starters`, `render_starter`) and write `src/fenolite/agent/starters/blink/` (`starter.toml`, `design.py.tmpl`): tune the placement until `route --router direct` closes the three nets with a clean copper check for targets 9 and 10 (the hermetic proof of "Starter projects"). Proof: `uv run pytest tests/unit/cli/test_init_cmd.py -k starter -q` (written here, with the catalog rule); `uv build` lists the two starter files in the wheel.
- [x] 1.3 Add `AGENT_DIRS`, `AGENTS_SECTION` and `SKILL_NAME` to `guide`, with the source comment per row (scenario "Rows are sourced"). Proof: `uv run pytest tests/unit/agent/test_guide.py -k agent_dirs tests/residue -q`.
  - Done on 2026-10-07: the row `claude-code` → `.claude/skills` with its source S-0617 on the row's line; `uv run pytest tests/unit/agent/test_guide.py -k agent_dirs tests/residue -q` passes (2 passed).

## 2. Dispatcher and descriptions

- [x] 2.1 Add `Result.text`, print it in text mode, and add the hidden option `--text-body` to `_echo` (scenarios of "Command text"). Proof: `uv run pytest tests/unit/cli/test_output.py tests/unit/cli/test_main.py tests/consistency -q`.
- [x] 2.2 Write `src/fenolite/cli/describe.py` and `tests/unit/cli/test_describe.py` (scenarios of "Command description"). Proof: `uv run pytest tests/unit/cli/test_describe.py -q`; `uv run pyright src`.

## 3. Commands

- [x] 3.1 Write `src/fenolite/cli/cmd_guide.py` and `tests/unit/cli/test_guide_cmd.py` (scenarios of "Guide command"). Proof: `uv run pytest tests/unit/cli/test_guide_cmd.py tests/consistency tests/unit/cli/test_hermetic_examples.py -q`.
- [x] 3.2 Write `src/fenolite/cli/cmd_skill.py` and `tests/unit/cli/test_skill_cmd.py` (scenarios of "Skill command"), with a test that walks the folder before and after `--agents-md` and proves that only `AGENTS.md` and its backup changed. Proof: `uv run pytest tests/unit/cli/test_skill_cmd.py tests/consistency tests/unit/cli/test_hermetic_examples.py -q`.
- [x] 3.3 Write `src/fenolite/cli/cmd_init.py` and the rest of `tests/unit/cli/test_init_cmd.py` (scenarios of "Init command"). Proof: `uv run pytest tests/unit/cli/test_init_cmd.py tests/consistency tests/unit/cli/test_hermetic_examples.py -q`.
- [x] 3.4 Add `--brief` and `--command NAME` to `capabilities` and write `tests/unit/cli/test_capabilities_brief.py` (scenarios of "Brief capabilities" and "Command view of capabilities"). Write under this task the measured size of the brief result and of the default result. Proof: `uv run pytest tests/unit/cli/test_capabilities_brief.py tests/unit/cli/test_capabilities.py tests/unit/cli/test_capabilities_backends.py tests/unit/cli/test_capabilities_experimental.py tests/consistency -q`.
  - Measured on 2026-10-07 with `--no-tools`, as the JSON of `result`: the brief view is 5 714 bytes for 33 public commands (the bound is 300 × 33 + 2 000 = 11 900), of which `commands` is 4 898; the default view is 21 318 bytes (21 067 before this change: its `commands` gained the entries of `guide`, `init` and `skill` and nothing else changed).
  - After the rebase onto `7392159d` (35 public commands, with `fetch` of c0078): the brief view is 5 995 bytes (the bound is 300 × 35 + 2 000 = 12 500) and the default view 21 881 bytes.

## 4. The start page and the block

- [x] 4.1 Rewrite `src/fenolite/agent/skill/SKILL.md` ("Start page"): the rules, the new `fenolite-loop` block, what each step is for, when a step fails, how to read a page, "Small questions between the steps" with every command it names on `dev` that day plus `inspect`, the sentence that separates the guide from the Altium verification kit, and "Limits". Copy the block into `README.md`, and update `README.md` and `AGENTS.md` (the guide's path and `fenolite guide`). Update `tests/unit/test_agent_skill.py`: the order check, the hermetic prefix, the rules (scenarios "Block parses", "A stale flag fails", "First six lines need no tool", "Start page states the rules", "No command is lost"). Proof: `uv run pytest tests/unit/test_agent_skill.py tests/unit/agent tests/residue -q`; `grep -rn "agent/SKILL.md" README.md AGENTS.md tests src` prints only lines that hold `src/fenolite/agent/skill/SKILL.md`.
  - Done on 2026-10-07. `AGENTS.md` names the guide's path and, in one added sentence of item 7, `fenolite guide start --text`.
- [x] 4.2 Write `tests/kicad/acceptance/test_skill_block.py` and remove `test_skill_block` from `tests/routing/test_acceptance_loop.py`; update the row of item 7 in `docs/release/v0.1.md` only if `tests/unit/test_release_record.py` requires the test to exist at the old place (then say there that the test moved). Proof: `uv run pytest tests/kicad/acceptance/test_skill_block.py -rA` on the local KiCad 10.0.6 and on KiCad 9.0.9; `uv run pytest tests/unit/test_release_record.py tests/unit/test_ci_workflow.py -q`.
  - Half open. On the base with c0077, `uv run pytest tests/kicad/acceptance/test_skill_block.py -rA` on the local KiCad 10.0.6: 2 passed (the ten lines for target 9 and for target 10 exit 0, `check` reports 0 violations and 0 unconnected items, `blink/fab` holds the manifest and Gerber files). `uv run pytest tests/unit/test_release_record.py tests/unit/test_ci_workflow.py -q` passes. 9.0.9 run owed to the coordinator's image run.
  - 2026-10-08: the 9.0.9 half could not be settled by the image run. Inside the pinned image run by `PYTHONPATH` (no installed distribution), `test_block[9]` fails at `route`: `unknown router 'direct' (registered: none)`, because the test gives its subprocess `PYTHONPATH=<root>/src` alone and the router entry points are then not visible; that is the recipe, not KiCad. With the host's Python and `FENOLITE_KICAD_CLI=docker:<the pinned image>`, the ten lines exit 0 for target 9, and the test then fails on `capabilities`, which reports no `kicad-cli` for the docker form. The `kicad-9` job, which installs the package, settles it.
  - 2026-10-08: ticked by CI run 37772583226 on `04ef42a` (every job green): the `kicad-9` job (`kicad/kicad:9.0.9@sha256:e638b79b…`) passes `tests/kicad/acceptance/test_skill_block.py::test_block[9]` and skips `test_block[10]` ("target 10 on kicad-cli 9"); the `kicad-10` job (`kicad/kicad:10.0.6`) passes the file. Locally, without `kicad-cli`, both cases are collected and skip (`kicad-cli not found`), and `uv run pytest tests/unit/test_release_record.py tests/unit/test_ci_workflow.py -q` passes (47 passed with the two skips). `test_skill_block` is no longer in `tests/routing/test_acceptance_loop.py`.
- [x] 4.3 Make the `wheel` CI job run `fenolite guide start --text` and `fenolite init blink --dry-run --json` from an empty folder with the installed wheel (scenario "Wheel carries the guide"), and update `tests/unit/test_ci_workflow.py`. Proof: `uv run pytest tests/unit/test_ci_workflow.py -q`; locally, `uv build` and then `uvx --from dist/*.whl fenolite guide start --text` from an empty folder exits 0. The `wheel` job of the pull request is read at the merge.
  - Done on 2026-10-07. Local proof: `uv build`, the wheel installed alone into a fresh environment with `--no-index`, then `fenolite guide start --text` (exit 0, the page with its block) and `fenolite init blink --dry-run --json` (exit 0, plan `blink/design.py`, nothing written) from an empty folder. The `wheel` job of the pull request is read at the merge.

## 5. Documentation

- [x] 5.1 Add to `docs/cli-contract.md`: the sections `guide`, `skill` and `init` with their result keys and exit codes; the brief view and the command view under "Discovery", with the fields of an argument and the key `targets.build`; `Result.text` under "Output", with what `--format concise` does beside it. Each statement is checked against a run of the command. Proof: `uv run pytest tests/consistency tests/unit/test_repo_layout.py tests/residue -q`.
  - Done on 2026-10-07: the sections `guide`, `skill` and `init` at the end of the page, "The brief view and the command view" under "Discovery", and "A command's own text" under "Output".

## 6. Closing

- [x] 6.1 Update the evidence labels: `H-K-GUIDE-STARTER` becomes `KICAD-VERIFIED (9.0.x, 10.0.x)` with the two runs, or records which line failed and why. Proof: `uv run pytest tests/unit/test_provenance.py tests/unit/test_hypotheses_register.py -q`.
  - Half open: the row is `KICAD-VERIFIED (10.0.x)` with the run of 2026-10-07 on 10.0.6 for both targets. It becomes `KICAD-VERIFIED (9.0.x, 10.0.x)` with the 9.0.9 run, owed to the coordinator's image run.
  - 2026-10-08: ticked. `H-K-GUIDE-STARTER` is `KICAD-VERIFIED (9.0.x, 10.0.x)`: its result names the `kicad-9` job of CI run 37772583226 (`test_block[9]` passed) beside the 10.0.6 run. `uv run pytest tests/unit/test_provenance.py tests/unit/test_hypotheses_register.py -q` passes.
- [x] 6.2 Add to `CHANGELOG.md` under `## [Unreleased]`: "**The agent guide ships in the package**: `fenolite guide` prints it, `fenolite skill install` copies it to an agent's skill folder or adds a pointer to `AGENTS.md`, and `fenolite init` writes a starter project that passes `check` with the built-in catalog and router; `capabilities --brief` and `capabilities --command NAME` give a small first reply and a command's arguments as data. **`agent/SKILL.md` moved into `src/fenolite/agent/skill/`**, and its loop block now starts from an empty folder". Update the row of this change in `docs/roadmap.md`. Proof: `git diff --stat HEAD -- CHANGELOG.md docs/roadmap.md` lists both files.
  - Open: the `CHANGELOG.md` entry is written (the last entry of `## [Unreleased]`); roadmap/README edited by the coordinator.
  - 2026-10-08, base `04ef42a`: ticked. The entry now says that the block is proved on 9.0.9 too, and the row of c0079 in `docs/roadmap.md` carries the slug of its folder (`agent-guide`; the page said `agent-kit`) and says that it ships in 0.4; `git diff --stat HEAD -- CHANGELOG.md docs/roadmap.md` lists both files.
- [x] 6.3 Stop and report "ready for the long runs": `make check-fast`, the unit suite on Python 3.11 (`uv run --python 3.11 pytest tests/unit -q`), `uv run pytest tests/residue tests/corpus/test_manifest.py -q` after `git add -A`, `uv run python tools/residue/scan.py`, and `openspec validate --all --strict --no-interactive`. The full `make check` is run once by the coordinator on the rebased branch, not by the implementing agent. Proof: each command exits 0.
  - 2026-10-08, branch `v04-close-a` on `04ef42a`, with every edit of the closing pass of c0077 to c0103 in the tree (the gate of the release, run once for all of them): `make check-fast PYTEST_WORKERS=4` exits 0 (ruff check, the guide's `--check`, ruff format, pyright, the residue scan, and 12731 passed, 29 skipped); the whole unit suite on Python 3.11.15, `uv run --isolated --python 3.11 --extra dev pytest tests/unit -q -n 4 -p no:cacheprovider`: 12348 passed, 25 skipped, exit 0; after `git add -A`, `uv run pytest tests/residue tests/corpus/test_manifest.py -q`: 80 passed, 5 skipped (no `kicad-cli`, no KiCad libraries), exit 0; `uv run python tools/residue/scan.py`: 0 hits, exit 0; `openspec validate --all --strict --no-interactive` reports the same six errors as on `04ef42a` (c0084, c0085 twice, c0086, c0108, c0128) and none of this change, besides the long-requirement warnings. The full `make check` is the coordinator's.
