lgili/Fenolite/openspec/changes/c0117-fab-assembly-drawings/tasks.md

## 0. Entry check

- [x] 0.1 Read the living `manufacturing-exports`, `cli-contract`, `kicad-oracle`, `sheet-templates` and `package-layering` specs and `openspec list`. Write under this task, with the date and the commit of `dev`: that `0.3.0` is released and c0084, c0101 and c0116 are archived (else stop: the stack-up table, `run_kind(layers=)` and the PDF date rule need them); that the MODIFIED delta of "Artefact states" is regenerated from the living text of that day with only `fab-drawing` and `assembly-drawing` added (c0116's kinds stay; if c0118 or c0105 landed first against the order of design Decision 17, theirs stay too); whether "Export command" or "Export kinds and their arguments" differ from c0116's text (then re-read "Drawing options of the export command" against the living text and repair the delta); whether c0103, c0105, c0112 or c0077 landed first against that order (then say under this task which builder, block or row is taken from them, and add the delta that Decisions 9 and 11 leave to them); whether c0080 is archived (task 8.2); and whether another change added a requirement of the same name as one here. Proof: `openspec validate c0117-fab-assembly-drawings --strict --no-interactive` passes after any repair.
  - 2026-10-08, on the integration base of v0.4 (`7392159d`: `dev` at `446b310a` with the proposals of the milestone and the changes of wave 1). `openspec list` and the tree: `0.3.0` is not released (the last tag is `v0.2.1`); c0084 is implemented and not archived ("Export command" of the living spec has no `--altium-rul` yet); c0116 is implemented on this base (`run_kind(layers=)`, the `/CreationDate` prefix, `result.repeat`) and not archived; **c0101 is not on this base** (the model has no `dielectric_kind`, `color`, `impedance_controlled` or `Stackup.thickness()`, and `read_board` fills no stack-up). By the coordinator's rule for this wave the work went on instead of stopping: everything that does not need c0101 is done, and the stack-up table reads c0101's fields where the model has them (it prints `dielectric` and sums the entries until then). The MODIFIED delta of "Artefact states" is regenerated from c0116's text of the requirement (what the living text holds once c0116 is archived, order c0116, c0117): its kinds and its scenario "Documents follow their source" stay, and only `fab-drawing`, `assembly-drawing` and the scenario "A drawing follows its board" are added. "Drawing options of the export command" was re-read against c0116's "Export command" (a selected kind, `--all`, the tool, `--preset`, `result.repeat`): nothing to repair. c0103, c0105, c0112 are not on this base; c0077 is (its `Reference` is on `F.SilkS`, so Decision 12 still adds the references); c0080 is not archived (no guide line in task 8.2). No other change or living spec holds a requirement of one of the nine names. `openspec validate c0117-fab-assembly-drawings --strict --no-interactive`: valid, exit 0.

## 1. Probe and register

- [x] 1.1 Add the rows `H-K-DRAW-ITEMS`, `H-K-DRAW-TEXT`, `H-K-DRAW-PAGE`, `H-K-DRAW-SHEET`, `H-K-DRAW-DRILL`, `H-K-DRAW-ASSEMBLY`, `H-K-DRAW-REPEAT` and `H-K-DRAW-LAYER` to `docs/hypotheses.md` (level `INFERRED`, the tests and criteria of `design.md`, result `pending` with the measurements of 2026-10-05 as the first record). Widen the "used for" text of S-0020, S-0022, S-0037 and S-0039 in `docs/evidence/sources.md` with the facts of the design's Context, only as each source states them. Proof: `uv run pytest tests/unit/test_hypotheses_register.py tests/unit/test_provenance.py`; `grep -cE '^\| H-K-DRAW-(ITEMS|TEXT|PAGE|SHEET|DRILL|ASSEMBLY|REPEAT|LAYER) ' docs/hypotheses.md` prints `8`.
  - Partly done on 2026-10-08. The eight rows are in `docs/hypotheses.md` (level `INFERRED`, the measurements of 2026-10-05 as the first record, then the 10.0.6 probes): `pytest tests/unit/test_hypotheses_register.py tests/unit/test_provenance.py`: 44 passed, exit 0; the `grep -c` prints `8`. Open: only the cell of S-0020 (the tool run as an oracle) is widened. The pages S-0022, S-0037 and S-0039 were not read again in this session (no download), so nothing was added to their cells, and the fact rows cite S-0020 for what was measured and S-0039 only for the token names that `tokens.toml` already holds.
  - 2026-10-08, on `v04-close-c` from `origin/v04` at `d6e6a19`: ticked. The CLI pages were read again (`https://docs.kicad.org/10.0/en/cli/cli.html`, S-0022, and `https://docs.kicad.org/9.0/en/cli/cli.html`, S-0037), and their "used for" cells now name what each page states of the facts of the Context: the options of `pcb export pdf` (`--include-border-title`, `-D`/`--define-var`, the three DNP options of the fabrication layers, `--sketch-pads-on-fab-layers`, the three modes; `--scale`, `--bg-color`, `--check-zones` and `--variant` on the 10.0 page only, `--plot-invisible-text` on the 9.0 page only), `--scale`, `--page-size-mode` and `--exclude-drawing-sheet` of `pcb export svg`, and `--generate-map`, `--map-format` and their formats of `pcb export drill`, with `--generate-report` and `--report-path` on the 10.0 page only (the 9.0 page omits them, which the 9.0.9 help shows: S-0020). S-0039 is widened only with what `tokens.toml` records from it for a drawing (the rows `table` and `table-uuid`); the measured facts stay cited to S-0020. `uv run pytest tests/unit/test_hypotheses_register.py tests/unit/test_provenance.py`: 44 passed, exit 0; the `grep -c` prints `8`.
- [x] 1.2 Write `tests/kicad/drawings/_drawbench.py` (the bench of "Drawing facts are probed") and the probes of items (`draw-dimension` among them), text, page and sheet in `tests/kicad/drawings/test_drawing_probes.py`, registered in `tests/kicad/_probes.py`. Record the page sizes KiCad plots for A2, A1 and A0 and the default sheet's boxes on A4 to A0. A probe that records another outcome stops its part, and the register row says what KiCad showed. Proof: `uv run pytest tests/kicad/drawings/test_drawing_probes.py -k "items or text or page or default_sheet" -rA` on the local `kicad-cli` 10.0.6; the probes are in `docs/evidence/kicad/probes/10.0.6.json`.
  - 2026-10-08: the bench is `tests/_drawdesign.py` (the design and its text, importable by the unit tests) and `tests/kicad/drawings/_drawbench.py` (the probes). Its stack-up is in the model only: the board text holds none before c0101 writes it. `FENOLITE_REQUIRE=kicad pytest tests/kicad/drawings/test_drawing_probes.py -k "items or text or page or default_sheet" -rA` on the local `kicad-cli` 10.0.6: 8 passed, 5 deselected, exit 0. The 29 probes are in `docs/evidence/kicad/probes/10.0.6.json` (merged by a script in the form `_probes.verify` writes; the whole `tests/kicad/test_probe_results.py` was started and stopped after ten minutes, so the coordinator's `kicad-10` run is its first full check). Page sizes of A2, A1 and A0 and the default sheet's boxes: `docs/evidence/kicad-drawings.md`. One probe recorded another outcome than the hypothesis stated: a line is longer than its advances by 0.25 × the size, so the bound of 1.45 × the size per glyph was too short for one `m`; the register row says what KiCad showed, `text_width` adds the constant (`LINE_EXTRA`), the delta of "Drawing tables and notes" states it, and with it `draw-glyph-bound` is `equal`.
- [x] 1.3 Add the probes of drill, assembly, repeat and layer to the same file. Record how the report lists slotted holes and the drill files of blind and micro vias, and the names of their maps; task 6.1 compares by what is recorded. Proof: `uv run pytest tests/kicad/drawings/test_drawing_probes.py -k "drill or assembly or repeat or layer" -rA` on the local 10.0.6.
  - 2026-10-08: `FENOLITE_REQUIRE=kicad pytest tests/kicad/drawings/test_drawing_probes.py -k "drill or assembly or repeat or layer" -rA` on the local 10.0.6: 4 passed, 9 deselected, exit 0. Recorded: the report counts a slot with the round holes of its width (`(3 holes)  (with 1 slot)`), the blind and the micro via share `<stem>-front-in1.drl` with the map `<stem>-front-in1-drl_map.pdf`, and the report heads that file with its layer pair; `check_drill` compares by that. `--exclude-value` is no option of `pcb export svg` on 10.0.6, so `draw-values` reads the PDF.
- [x] 1.4 Run every probe of the file in the pinned 9.0.9 image, in one container. Proof: `docker run --rm --platform linux/amd64 -v "$PWD":/w -w /w -e HOME=/tmp "kicad/kicad:9.0.9@sha256:e638b79b0321f29395a5b783e94bb9f3c73303e8da15da27b8f5cb4b67a37729" …` running `uv run pytest tests/kicad/drawings/test_drawing_probes.py -rA`, or the `kicad-9` job; the probes are in `9.0.9.json`; `uv run pytest tests/kicad/test_probe_results.py`.
  - Not run: no container run in this session (2026-10-08). `docs/evidence/kicad/probes/9.0.9.json` holds none of the 29 rows, so `tests/kicad/test_probe_results.py` reports them as drift on 9.0.9 until the `kicad-9` job or one image run records them.
  - 2026-10-08: ticked by the second local run of 2026-10-08 in the pinned 9.0.9 image (`kicad/kicad:9.0.9@sha256:e638b79b…`, linux/amd64, branch `v04-k9-probes-2`; whole `tests/kicad` without the corpus: 998 passed, 2 failed, 806 skipped, 1 xfailed; `tests/kicad/test_probe_results.py` passed on the 723 probes of major 9): `tests/kicad/drawings/test_drawing_probes.py` 13 passed; the 29 rows are in `9.0.9.json`, merged by name: the outcomes of 10.0.6, except `help-pcb-export-pdf-scale` and `help-pcb-export-svg-scale`, which are `absent` on 9.0.9 as `H-K-DRAW-PAGE` states.

## 2. Spec file

- [x] 2.1 Write `src/fenolite/exports/drawing_spec.py` (`SCHEMA`, `DrawingSpec`, `PageSpec`, `FabSpec`, `AssemblySpec`, `DEFAULT`, `SpecError`, `read_spec`) and `tests/unit/exports/test_drawing_spec.py` (scenarios of "Drawing specification files", the closed keys one by one, a note with a control character). Proof: `uv run pytest tests/unit/exports/test_drawing_spec.py tests/unit/test_import_graph.py`; `uv run pyright src`.
  - 2026-10-08: `pytest tests/unit/exports/test_drawing_spec.py tests/unit/test_import_graph.py`: 62 passed, exit 0; `pyright src`: 0 errors, exit 0.

## 3. Tables and notes

- [x] 3.1 Write `text_width`, `break_lines`, `LINE_PITCH`, `GLYPH_BOUND` and `GLYPH_SET` from the probes of task 1.2, `Block` and `notes_block` in `src/fenolite/exports/drawing_tables.py`, with `tests/unit/exports/test_drawing_tables.py -k "text or notes"` (the scenario "Notes are broken by the bound", a word longer than the width, line feeds kept). Proof: `uv run pytest tests/unit/exports/test_drawing_tables.py -k "text or notes"`.
  - 2026-10-08: `pytest tests/unit/exports/test_drawing_tables.py -k "text or notes"`: 5 passed, 8 deselected, exit 0. `text_width` also adds `LINE_EXTRA` (task 1.2).
- [x] 3.2 Write `board_block`, `stackup_block`, `drill_rows` and `drill_block`, and `impedance_block`, which returns no block (design Decision 9); extend the test file (scenarios "Stack-up rows of a two-layer board", "Drill rows of vias and pads", "No stack-up", and a spec whose `tables` names `impedance` giving no block and no issue). Proof: `uv run pytest tests/unit/exports/test_drawing_tables.py`; `uv run pyright src`.
  - 2026-10-08: `pytest tests/unit/exports/test_drawing_tables.py`: 13 passed, exit 0; `pyright src`: 0 errors. Without c0101 the scenario "Stack-up rows of a two-layer board" asserts `dielectric` where it says `core`, and takes the total from the sum of the entries; the test reads the field when the model has it.

## 4. Layout

- [x] 4.1 Write `src/fenolite/exports/drawing_layout.py` (`Obstacles`, `Placed`, `place`, `choose_paper`, `AUTO_PAPERS` with the page sizes of task 1.2) and the board box of each page, mirror included, with `tests/unit/exports/test_drawing_layout.py` (the four scenarios of "Drawing page layout", fixed corners, determinism). Proof: `uv run pytest tests/unit/exports/test_drawing_layout.py tests/unit/test_import_graph.py`.
  - 2026-10-08: `pytest tests/unit/exports/test_drawing_layout.py tests/unit/test_import_graph.py`: 39 passed, exit 0.
- [x] 4.2 Write `default_sheet_obstacles(width, height)` in `src/fenolite/backends/kicad/drawing.py` from the boxes of task 1.2, and the obstacles of a known sheet through `templates.layout` in `cmd_export` (`drawing.sheet-unread` for a sheet that cannot be read or built). Proof: `uv run pytest tests/unit/backends/kicad/test_drawing_copy.py -k obstacles tests/unit/cli/test_export_drawings.py -k sheet`.
  - 2026-10-08: `pytest tests/unit/backends/kicad/test_drawing_copy.py tests/unit/cli/test_export_drawings.py -k "obstacles or sheet"`: 4 passed, 19 deselected, exit 0.

## 5. Plot copies

- [x] 5.1 Add `PlotTable`, `PlotText` and `PlotDimension` to `src/fenolite/backends/base.py`, and `plot_copy`, `item_nodes`, `layer_extent` and `shows_reference` to `src/fenolite/backends/kicad/drawing.py`; build the orthogonal dimension node in `drawing.py` in the form that the probe `draw-dimension` of task 1.2 recorded (design Decision 11); write `tests/unit/backends/kicad/test_drawing_copy.py` (the four scenarios of "Drawing plot copies"). Proof: `uv run pytest tests/unit/backends/kicad/test_drawing_copy.py tests/unit/test_import_graph.py`; `uv run pyright src`.
  - 2026-10-08: `pytest tests/unit/backends/kicad/test_drawing_copy.py tests/unit/test_import_graph.py`: 40 passed, exit 0; `pyright src`: 0 errors. The dimension node is in the form c0103 specifies, and `draw-dimension` is `present` on 10.0.6.
- [x] 5.2 Let `KicadCli.run` and `KicadCli.export` take `bytes` sources in `files`, and extend `tests/_fakecli.py` with fake PDF, map and report outputs. Proof: `uv run pytest tests/unit/backends/kicad/test_cli_runner.py -k bytes tests/unit/cli/test_export_cmd.py`.
  - 2026-10-08: `pytest tests/unit/backends/kicad/test_cli_runner.py -k bytes`: 3 passed, 36 deselected, exit 0; `pytest tests/unit/cli/test_export_cmd.py`: 35 passed, exit 0.

## 6. Drawing kinds

- [x] 6.1 Write `run_fab_drawing` and `read_drill_report` in `src/fenolite/exports/drawings.py` and `backends/kicad/drawing.py`, with the report check of Decision 10 as task 1.3 recorded it; extend `tests/unit/exports/test_drawings.py` (scenarios "Files of the kind", "Both forms of a tool line", a count that differs, an unreadable report). Proof: `uv run pytest tests/unit/exports/test_drawings.py -k fab`.
  - 2026-10-08: `pytest tests/unit/exports/test_drawings.py -k fab`: 8 passed, 5 deselected, exit 0.
- [x] 6.2 Write `run_assembly_drawing` with the options, the side rule and the added references (scenarios of "Assembly drawing kind"). Proof: `uv run pytest tests/unit/exports/test_drawings.py -k assembly`.
  - 2026-10-08: `pytest tests/unit/exports/test_drawings.py -k assembly`: 5 passed, 8 deselected, exit 0.
- [x] 6.3 Add the two kinds to `VOLATILE_PREFIXES` (reusing c0116's PDF prefix), the seven `drawing.*` codes to `exports/codes.py` with one entry each in `src/fenolite/cli/data/explain.toml`, `exports.drawings.EVIDENCE`, and the two kinds to `exports.states.DERIVED` with the manifest entries of "Drawing kinds in the manifest"; extend `tests/unit/exports/test_states.py` (scenario "A drawing follows its board"). Proof: `uv run pytest tests/unit/exports tests/unit/cli/test_explain_cmd.py tests/consistency -k "drawing or codes or explain or states"`.
  - 2026-10-08: `pytest tests/unit/exports tests/unit/cli/test_explain_cmd.py tests/consistency -k "drawing or codes or explain or states"`: 100 passed, 474 deselected, exit 0. The closed sets of `tests/unit/exports/test_plan.py::test_issue_codes` and `test_states.py::test_roles_and_ranks` hold the seven codes and the two kinds.

## 7. Export command

- [x] 7.1 Add `--fab-drawing`, `--assembly-drawing` and `--drawing-spec` to `src/fenolite/cli/cmd_export.py`, with `result.drawings`, the combined evidence and the all-or-nothing rule; write `tests/unit/cli/test_export_drawings.py` (scenarios of "Drawing options of the export command", "Drawings join the manifest" and "A count that differs", and one test that a `.PcbDoc` path with `--fab-drawing` exits 2 with `FEN-2001` before the spec is read). Proof: `uv run pytest tests/unit/cli/test_export_drawings.py tests/unit/cli/test_export_cmd.py tests/unit/cli/test_check_readonly.py tests/unit/cli/test_hermetic_examples.py tests/consistency`.
  - 2026-10-08: `pytest tests/unit/cli/test_export_drawings.py tests/unit/cli/test_export_cmd.py tests/unit/cli/test_check_readonly.py tests/unit/cli/test_hermetic_examples.py tests/consistency`: 375 passed, 17 skipped, exit 0. `result.drawings` is present only when a drawing kind is selected, so the reply of every other call is as before.

## 8. Oracle and documentation

- [x] 8.1 Write `tests/kicad/drawings/test_drawing_oracle.py` (the checks of "Drawing facts are probed" on the bench's exported drawings). Proof: `uv run pytest tests/kicad/drawings/test_drawing_oracle.py -rA` on the local 10.0.6 and in the pinned 9.0.9 image.
  - Done on 10.0.6 (2026-10-08): `FENOLITE_REQUIRE=kicad pytest tests/kicad/drawings/test_drawing_oracle.py -rA`: 4 passed, exit 0 (both kinds exported, the drill check passes, every block text inside its block and outside the board box and the sheet, no line wider than its column, equal content hashes of two exports). Open: the pinned 9.0.9 image was not run (no container run in this session).
  - 2026-10-08: ticked by the second local run of 2026-10-08 in the pinned 9.0.9 image (`kicad/kicad:9.0.9@sha256:e638b79b…`, linux/amd64, branch `v04-k9-probes-2`; whole `tests/kicad` without the corpus: 998 passed, 2 failed, 806 skipped, 1 xfailed; `tests/kicad/test_probe_results.py` passed on the 723 probes of major 9): `tests/kicad/drawings/test_drawing_oracle.py` 4 passed.
- [x] 8.2 Write `docs/drawings.md` (the spec file with every key and default, the pages, the tables, the layout rule, the codes, the limits of the proposal, and that a note naming an undefined variable is printed as written) and `docs/evidence/kicad-drawings.md` (the probe outcomes); say there that the drawing kinds take a KiCad board and what an Altium project has instead (design Decision 18), and that the maps under `drawings/` are those the preset key `drill.map` writes under `drill/`; update `docs/exports.md`, `docs/cli-contract.md`, and `docs/formats/kicad/cli.md` and `board.md` with the facts of the Context and their labels. If c0080 is archived, add one tested line for `--fab-drawing` with `--drawing-spec` to its guide page. Proof: `uv run pytest tests/consistency tests/unit/test_format_facts.py tests/unit/test_repo_layout.py tests/residue`.
  - 2026-10-08: `pytest tests/consistency tests/unit/test_format_facts.py tests/unit/test_repo_layout.py tests/residue`: 342 passed, 17 skipped, exit 0. Written: `docs/drawings.md`, `docs/evidence/kicad-drawings.md`, the section "Drawings" of `docs/exports.md`, the options, `result.drawings` and the seven codes in `docs/cli-contract.md`, and the fact rows of `docs/formats/kicad/cli.md` ("Drawings") and `board.md` ("Drawing items"), every row `INFERRED`. c0080 is not archived, so no guide line was added.

## 9. Closing

- [x] 9.1 Run the tests and the residue scan. Proof: `make check-fast`; `uv run pytest tests/unit tests/kicad/drawings -q`; the unit suite on Python 3.11 (`uv run --python 3.11 pytest tests/unit -q -n auto --dist loadfile`); `uv run python tools/residue/scan.py` exits 0; `openspec validate c0117-fab-assembly-drawings --strict --no-interactive` passes; the full `make check` and the pull request checks (`unit`, `kicad-9`, `kicad-10`) are run once at the merge by the coordinator, never by the implementing agent.
  - `make check-fast PYTEST_WORKERS=3`, run once on 2026-10-08: ruff, format, pyright and the residue scan passed; of the tests, 10166 passed, 22 skipped and 3 failed, exit 2. The three were `tests/unit/test_kicad_probes.py` (its fake test lists the folders of `tests/kicad` and lacked `drawings/`); the folder was added and `pytest tests/unit/test_kicad_probes.py`: 11 passed, exit 0. The whole of `check-fast` was not run a second time. `openspec validate c0117-fab-assembly-drawings --strict --no-interactive`: valid; `uv run python tools/residue/scan.py`: exit 0. Open: the whole unit suite on Python 3.11 was not run (no Python 3.11 is installed on this machine, and none was downloaded); the full `make check` and the pull request checks are the coordinator's.
  - 2026-10-08, on `v04-close-c` from `origin/v04` at `d6e6a19`, with the edits of this closing round staged: `make check-fast PYTEST_WORKERS=3` exits 0 (ruff, format, pyright, residue scan; 12888 passed, 29 skipped; a first run failed only on `tests/unit/test_evidence_matrix_page.py` before `docs/evidence/matrix.md` was regenerated); `uv run --isolated --python 3.11 --extra dev pytest tests/unit -q -n 3 -p no:cacheprovider` exits 0 (12497 passed, 25 skipped); `uv run pytest tests/residue tests/corpus/test_manifest.py` (82 passed, 3 skipped) and `uv run python tools/residue/scan.py` (0 hits) exit 0; `uv run python tools/gen_schemas.py --check` exits 0; `openspec validate --all --strict --no-interactive` gives only the errors that were there before (c0084, c0085 twice, c0086, c0108, c0128) and long-requirement warnings; `python3 tools/dco_check.py origin/v04..HEAD` prints nothing. Three workers in place of four, as parallel agents share the machine. `uv run pytest tests/unit tests/kicad/drawings -q` is inside those runs (the drawing tests skip without `kicad-cli`; they passed in CI run 37772583226).
- [x] 9.2 Update the evidence labels: the eight `H-K-DRAW-*` rows become `KICAD-VERIFIED (9.0.x, 10.0.x)` with their scope, or record what was refuted and the part stopped; `exports.drawings.EVIDENCE` rises to `KICAD-VERIFIED` when `H-K-DRAW-ITEMS`, `-PAGE` and `-DRILL` hold on both majors; the fact rows of task 8.2 carry the same labels. Proof: `uv run pytest tests/unit/test_provenance.py tests/unit/test_hypotheses_register.py tests/kicad/test_probe_results.py`.
  - Not done: the eight rows and `exports.drawings.EVIDENCE` stay `INFERRED`, because the probes are recorded on 10.0.6 only (task 1.4). On 10.0.6 every probe has the outcome its hypothesis states, after the correction of `H-K-DRAW-TEXT` (task 1.2).
  - 2026-10-08: after the image run named under task 1.4, the eight `H-K-DRAW-*` rows are `KICAD-VERIFIED (9.0.x, 10.0.x)`. Still open: the code-side evidence constants and the labels of the fact rows of `docs/formats/kicad/` were not raised by the commit that recorded the probes; CI has still to confirm the 9.0.9 half. (`exports.drawings.EVIDENCE` is `INFERRED`.)
  - 2026-10-08, on `v04-close-c` (`d6e6a19`): ticked. Every test of `tests/kicad/drawings/` (unchanged since `04ef42a`) passed in the all-green CI run 37772583226 on that commit, in the `kicad-9` job (each `PASSED` in its `-rA` log: the probes of items, text, page, default sheet A4 to A0, drill, assembly, repeat and layer, and the four oracle checks) and in the `kicad-10` job (none skipped), so `H-K-DRAW-ITEMS`, `-PAGE` and `-DRILL` hold on both majors and `exports.drawings.EVIDENCE` (`backends/kicad/drawing.py`) is `KICAD_VERIFIED`, with the two unit tests that pinned `INFERRED`, `docs/drawings.md` and `docs/cli-contract.md` following. The fact rows of `docs/formats/kicad/cli.md` ("Drawings", 10 rows) and `board.md` ("Drawing items", 7 rows) are `KICAD-VERIFIED (9.0.x, 10.0.x)`, the row on `--scale` `(10.0.x)`. `uv run pytest tests/unit/test_provenance.py tests/unit/test_hypotheses_register.py tests/kicad/test_probe_results.py`: passed (the probe file check skips without `kicad-cli`); the drawing unit tests: 95 passed.
- [x] 9.3 Add to `CHANGELOG.md` under Unreleased: "`export --fab-drawing` writes a fabrication drawing (outline and its dimensions, board, stack-up, drill and impedance tables, numbered notes) with KiCad's drill maps and report, and `--assembly-drawing` top and bottom assembly drawings, all plotted by `kicad-cli` from a copy of the board; `--drawing-spec FILE` sets paper, sheet, tables, notes and assembly options; the drill counts are checked against KiCad's report". Update the line of c0117 under "v0.4" in `docs/roadmap.md`. Proof: `git diff --stat CHANGELOG.md docs/roadmap.md` lists both files.
  - Partly done on 2026-10-08: the entry is the last one of `## [Unreleased]` in `CHANGELOG.md` (with the two limits of this base: no impedance row, and no stack-up table before c0101). `docs/roadmap.md` is not edited here: the coordinator of the wave updates it.
  - The CHANGELOG line of this round is under `### Changed` of `## [Unreleased]`, and the row of this change in `docs/roadmap.md` (v0.4, the complex board) says what ships in 0.4. `git diff --stat CHANGELOG.md docs/roadmap.md` lists both files.
