lgili/Fenolite/openspec/changes/c0118-assembly-test-features/tasks.md

## 0. Entry check

- [x] 0.1 Read the living `design-model`, `kicad-file-backend`, `design-dsl`, `dsl-footprint-authoring`, `cli-contract`, `manufacturing-exports`, `assembly-outputs`, `altium-build` and `kicad-oracle` specs and `openspec list`. Write under this task, with the date and the commit of `dev`: that `0.3.0` is released and c0102 and c0103 are archived (else stop: task group 3 needs `rule_area`, the generated definitions and `Fenolite_Holes:Hole`); the names under which they landed `Design.rule_area`, `Design.rule_areas`, `H-K-AREA-KEEPOUT` and `H-K-HOLE-FOOTPRINT`, and what c0102's living "PCB document output" does with a hole part in an Altium build (then correct design Decision 13 and "Assembly and test features in an Altium build" if a tooling hole can be written); whether c0096 is on `dev`, and if so that its `hole` and `keepout` calls are those of c0102 and c0103 (maintainer's decision 2 of 2026-10-07); that the three MODIFIED deltas ("IPC-D-356 parsing", "Artefact states", "Manifest option of producing commands") are regenerated from the living text of the day with only this change's edits (the kinds of c0116 and c0117 stay); whether c0077 and c0080 are archived (tasks 3.6 and 7.2). Proof: `openspec validate c0118-assembly-test-features --strict --no-interactive` passes after any re-base.
  - Result: 2026-10-08, on the v0.4 integration base `15964cc3` (branch `v04-impl-c0118`): **entry check not met, so the task stays open.** `0.3.0` is not released (the version is dynamic; the last tag line of `CHANGELOG.md` is 0.2.1) and c0102 and c0103 are neither archived nor implemented (`openspec list`: 0/25 and 0/26 tasks; `Design` has no `rule_area`, `rule_areas` or `hole`; `docs/hypotheses.md` holds no `H-K-AREA-KEEPOUT` or `H-K-HOLE-FOOTPRINT` row). c0096 is not on the base. c0077 is implemented but not archived; c0080 is not archived (0/15). By the coordinator's rule for this night the parts that need neither change were done (groups 1, 2, 4, 5, 6 and tasks 3.1, 7.1), and the rest of group 3 is open. Decision 13 could not be re-read against c0102's final "PCB document output": nothing changed there. The three MODIFIED deltas were compared with the living text of the day by a script: "IPC-D-356 parsing", "Artefact states" and "Manifest option of producing commands" each equal the living requirement plus this change's edits only (one bullet and one scenario each; four bullets for the manifest option), so nothing was rewritten. c0116 and c0117 are not archived, so the living text holds none of their kinds yet: the two shared deltas must be regenerated again when they archive (order c0116, c0117, c0118, c0105). `openspec validate c0118-assembly-test-features --strict --no-interactive`: valid, exit 0.
  - 2026-10-08, on `v04-close-c` from `origin/v04` at `d6e6a19`: met as the maintainer's release plan of 2026-10-08 reads it. `0.3.0` is released (c0150, archived, `docs/release/v0.3.md`). c0102 and c0103 are on `v04` with every task closed, not archived (they ship in 0.4 with this change): `Design.rule_area` and `Design.rule_areas` (c0103) and `Design.hole` with `Fenolite_Holes:Hole` (c0102) are the names this change uses, and `H-K-AREA-KEEPOUT` and `H-K-HOLE-FOOTPRINT` are registered under those ids. c0102's "PCB document output" writes every part of `Fenolite_Holes:Hole` as a board hole, so a tooling hole is written as one: Decision 13 and "Assembly and test features in an Altium build" already say so (task 3.5). c0096 is on `v04` without hole or keep-out calls of its own (its R10 of 2026-10-08): its holes and keep-outs are those of c0102 and c0103. The MODIFIED deltas were regenerated from the text the tip leaves: "Artefact states" from c0117's delta (which carries c0116's kinds and its two scenarios), with only `testpoints` added to the kinds and the scenario "The test-point table follows its board"; "Manifest option of producing commands" from c0116's delta (its `layer` and `sch-pdf` sentences, its evidence bullet and its scenario "Layer and source of document entries" kept), with only `testpoints` added to the four bullets and the scenario "The test-point table joins the manifest"; "IPC-D-356 parsing" equals the living text plus this change's bullet and scenario, so it stands. c0077 and c0080 are on `v04` with every task closed and count as archived for v0.4 (tasks 3.6 and 7.2). `openspec validate c0118-assembly-test-features --strict --no-interactive` reports only the long-requirement warnings of its ADDED requirements.

## 1. Probe and register

- [x] 1.1 Add the rows `H-K-PAD-FABPROP`, `H-K-PAD-FABPROP-LIB`, `H-K-FIDUCIAL-FORM`, `H-K-FIDUCIAL-KEEPOUT` and `H-K-TESTPOINT-D356` to `docs/hypotheses.md` (backend `kicad`, level `INFERRED`, the tests and criteria of `design.md`, result `pending` with the measurements of 2026-10-05 as the first record). Proof: `uv run pytest tests/unit/test_hypotheses_register.py tests/unit/test_provenance.py`; `grep -cE '^\| (H-K-PAD-FABPROP|H-K-PAD-FABPROP-LIB|H-K-FIDUCIAL-FORM|H-K-FIDUCIAL-KEEPOUT|H-K-TESTPOINT-D356) ' docs/hypotheses.md` prints `5`.
  - Result: 2026-10-08: the five rows are at the end of the table of `docs/hypotheses.md`, `INFERRED`, with the measurements of 2026-10-05 as first record and the 10.0.6 run of 2026-10-08. `uv run pytest tests/unit/test_hypotheses_register.py tests/unit/test_provenance.py`: passed, exit 0; the `grep -cE` prints `5`.
- [x] 1.2 Write `tests/kicad/assembly/_featurebench.py` (the marked-pad bench of measurements 2 and 3: copies of `Mini` footprints and authored footprints, marks added by token edit until task 2.2 writes them) and `tests/kicad/assembly/test_pad_properties.py` with the probes `pad-fabprop-<value>`, `pad-fabprop-outputs`, `pad-fabprop-padstack`, `pad-fabprop-lib-mismatch` and `pad-fabprop-lib-same`; register them and record their outcomes. Write the facts to `docs/formats/kicad/board.md` (the token table, the place of the child, the Gerber functions) with sources S-0020 and S-0029. An outcome that differs from `design.md` stops this task, and the design is corrected first. Proof: `uv run pytest tests/kicad/assembly/test_pad_properties.py -rA` on the local KiCad 10.0.6 and inside the pinned 9.0.9 image; `FENOLITE_PROBES_WRITE=1` updates both probe files; `uv run pytest tests/kicad/test_probe_results.py tests/unit/test_format_facts.py`.
  - Result: 2026-10-08: done for KiCad 10.0.6, open for 9.0.9 (no run inside the pinned image this night; docker was not to be used). `_featurebench.py` and `test_pad_properties.py` are written; the bench is a created board with one footprint per mark, marked by token edit and, since task 2.2, also written from the model; the library subjects are the built blink (a marked copy) and the blink with authored marked parts. Probes on 10.0.6, targets 9 and 10: the eight `pad-fabprop-<value>`, `pad-fabprop-outputs`, `pad-fabprop-padstack` and the added `pad-fabprop-resave` = `equal`; `pad-fabprop-lib-mismatch` = `present`; `pad-fabprop-lib-same` = `absent`. Every outcome is the one of `design.md`. They are registered for major 10 only (`_featurebench.MAJORS`), so the kicad-9 job does not ask for outcomes nobody recorded; the 9.0.9 run sets `MAJORS = (9, 10)` and records `9.0.9.json`. Facts are in `docs/formats/kicad/board.md`, "Pad fabrication properties". `FENOLITE_REQUIRE=kicad uv run pytest tests/kicad/assembly/test_pad_properties.py -rA`: 15 passed, exit 0. `uv run pytest tests/unit/test_format_facts.py`: passed. The 19 outcomes of this change were added to `docs/evidence/kicad/probes/10.0.6.json` by a script that runs `_probes.run` for them and writes the file in the form of `FENOLITE_PROBES_WRITE=1`; the whole-file write was not possible because `tests/kicad/test_probe_results.py` fails on this base before it compares (the `pcb-layers-*` probes of `_layertables` raise `LossyWriteError`, also on a clean checkout of `15964cc3`: `tests/kicad/board/test_layer_tables.py`, 17 failed).
  - 2026-10-08, on `v04-close-c` (`d6e6a19`): written; awaits the CI run. `tests/kicad/assembly/test_features_nine.py` runs, on KiCad 9 only (marker `needs_kicad`, skipped on another major), every probe of `_featurebench.feature_probes` that is stated for both majors, prints its outcome beside the one 10.0.6 recorded (`-rA` of the `kicad-9` job) and writes it to the census file; `test_expected_names_every_probe_of_both_majors` holds the table to the registry. The probes stay registered for major 10 only, so `tests/kicad/test_probe_results.py` asks nothing new of the `kicad-9` job; once its log shows the outcomes, `MAJORS` becomes `(9, 10)` and `9.0.9.json` takes them. Locally (no `kicad-cli`): 18 tests collected, skipped cleanly. `pad-fabprop-press_fit` is vacuous on 9.0.9 as the bench stands (it skips target 9), so the drop on load that the requirement names is not measured by it.
  - 2026-10-08, on `v04-ci-ticks` from `origin/v04` at `38fecbd`: done for 9.0.9. The `kicad-9` job (the pinned image `kicad/kicad:9.0.9@sha256:e638b79b…`) of CI run 37803522539 on `a105cc0` (the code of `38fecbd` less a test-only fix of `test_features_nine.py`) printed with `-rA`, from `tests/kicad/assembly/test_features_nine.py::test_nine_observation`: `pad-fabprop-bga`, `-castellated`, `-fiducial_global`, `-fiducial_local`, `-heatsink`, `-mechanical`, `-press_fit`, `-test_point`, `-outputs` and `-padstack` = `equal`, `pad-fabprop-lib-mismatch` = `present`, `pad-fabprop-lib-same` = `absent`, each the outcome that 10.0.6 recorded and `design.md` states. Its only failure was `test_expected_names_every_probe_of_both_majors` (the table check, fixed by `38fecbd`). Following the module docstrings, `_featurebench.MAJORS` is now `(9, 10)` and the twelve outcomes are in `docs/evidence/kicad/probes/9.0.9.json`, added by hand in the form that `FENOLITE_PROBES_WRITE=1` writes (sorted keys), since no `kicad-cli` is here; `pad-fabprop-resave` stays registered for 10 alone. Limits kept: `pad-fabprop-press_fit` is vacuous on 9.0.9 (it skips target 9 there), so the drop on load is not measured by it; `test_pad_properties.py` itself was skipped in that job (the probes were registered for 10 alone then), so its control `test_unmarked_pads_keep_their_function` runs on 9.0.9 for the first time in the next `kicad-9` job, where `tests/kicad/test_probe_results.py` also checks the new lines.
- [x] 1.3 Add to `_featurebench.py` the boards of measurements 5, 6 and 9 written through the model API (a fiducial of two pads, test pads on both sides and through-hole, a keep-out octagon), and record the probes `asm-fiducial-drc`, `asm-fiducial-mask`, `asm-fiducial-d356`, `asm-keepout-track` and `asm-keepout-fill` (10.0.6 only: 9.0.9 cannot refill) in `tests/kicad/assembly/test_features_oracle.py`, with their facts in `docs/formats/kicad/board.md`. Proof: `uv run pytest tests/kicad/assembly/test_features_oracle.py -rA` on 10.0.6 and inside the 9.0.9 image; `uv run pytest tests/kicad/test_probe_results.py`.
  - Result: 2026-10-08: done for KiCad 10.0.6, open for 9.0.9 (as task 1.2). The features bench is written through the model API: a fiducial of two unnumbered pads on each side (without the courtyard: a placed footprint holds no graphics in the model on this base), four test pads and a keep-out octagon of 3 mm. On 10.0.6, targets 9 and 10: `asm-fiducial-drc` = `absent`, `asm-fiducial-mask` = `equal`, `asm-fiducial-d356` = `equal`, `asm-keepout-track` = `present`, `asm-keepout-fill` = `equal` (the pour stays 1.500000 mm from the centre). `FENOLITE_REQUIRE=kicad uv run pytest tests/kicad/assembly/test_features_oracle.py -rA`: 6 passed, exit 0.
  - 2026-10-08: the 9.0.9 half (`asm-fiducial-drc`, `-mask`, `-d356`, `asm-keepout-track`) is in `tests/kicad/assembly/test_features_nine.py` with task 1.2: written; awaits the CI run (`kicad-9` job).
  - 2026-10-08, on `v04-ci-ticks`: done for 9.0.9. The `kicad-9` job of CI run 37803522539 on `a105cc0` printed `asm-fiducial-drc` = `absent`, `asm-fiducial-mask` = `equal`, `asm-fiducial-d356` = `equal` and `asm-keepout-track` = `present` (`test_features_nine.py`, `-rA`), each the 10.0.6 outcome; they are registered for both majors (`MAJORS = (9, 10)`) and in `9.0.9.json`. `asm-keepout-fill` stays registered for 10 alone (9.0.9 cannot refill).

## 2. Model and the KiCad mapping

- [x] 2.1 Add `PadFabProperty` and `Pad.fab_property` to `src/fenolite/model/board.py`, regenerate the schemas, and write `tests/unit/model/test_pad_fab_property.py` (scenarios of "Assembly and test pad properties in the model", and one test that the committed fixture of release 0.2.0, `tests/data/model/v0.2.0/blink_2layer.board.json` of c0126, loads unchanged and serialises to its own bytes). Write the compatibility sentence to `docs/design-model.md`: 0.2.x and 0.3.0 cannot read a model document that carries `fab_property`. Proof: `uv run pytest tests/unit/model tests/unit/test_schema_drift.py`; `uv run python tools/gen_schemas.py --check` exits 0; `grep -c 'fab_property' docs/design-model.md` prints at least `2`.
  - Result: 2026-10-08: `uv run pytest tests/unit/model tests/unit/test_schema_drift.py`: passed (the 0.2.0 fixture case is skipped: `tests/data/model/v0.2.0/` comes with c0126, which is not on this base; the 0.2.1 fixture loads and serialises to its own bytes). `tools/gen_schemas.py` regenerated `board.json` and `library.json`; `--check` exits 0. `grep -c 'fab_property' docs/design-model.md` prints `1` line with three occurrences (the row holds the field, the eight values and the compatibility sentence).
- [x] 2.2 Map the child in `_fpmap` (`FAB_PROPERTY_TOKENS`, the reader, the emitters, `PAD_CANONICAL`), `CANONICAL_ORDER["pad"]` in `pcb.py`, the slot in `mod.prepare_authored_definition` and the value in `embed.place_footprint`; check that `press_fit` for target 9 is refused by the emit check; write `tests/unit/backends/kicad/test_pad_fab_property.py` (scenarios of "Assembly and test pad properties on boards and footprints"). Proof: `uv run pytest tests/unit/backends/kicad/test_pad_fab_property.py tests/unit/backends/kicad`; `uv run pytest tests/corpus/test_footprint_rt.py` with the libraries cached; `uv run pyright src`.
  - Result: 2026-10-08: `uv run pytest tests/unit/backends/kicad/test_pad_fab_property.py`: 26 passed; `uv run pytest tests/unit/backends/kicad`: passed; `uv run pytest tests/corpus/test_footprint_rt.py` with the libraries cached: 25 passed, exit 0; `uv run pyright src`: 0 errors. `embed.place_footprint` needed no edit: it reads the emitted footprint back, so the mark follows the definition's slot. `press_fit` for target 9 is refused by the emit check (`kicad.token.too-new`, row `pad-property-pressfit`, not droppable).
- [x] 2.3 Add `Ipcd356Record.covered` to `src/fenolite/backends/kicad/ipcd356.py` and the scenario "Mask codes" to `tests/unit/backends/kicad/test_ipcd356.py`. Proof: `uv run pytest tests/unit/backends/kicad/test_ipcd356.py tests/unit/backends/kicad -k "ipcd356 or padnets"`.
  - Result: 2026-10-08: `uv run pytest tests/unit/backends/kicad/test_ipcd356.py`: 8 passed, exit 0.

## 3. Script

- [x] 3.1 Add `fab_property=` to `Footprint.pad` and write `tests/unit/dsl/test_footprint_fab_property.py` (scenarios of "Assembly and test properties on authored pads"). Proof: `uv run pytest tests/unit/dsl/test_footprint_fab_property.py tests/unit/dsl/test_footprint.py tests/unit/test_import_graph.py`.
  - Result: 2026-10-08: `uv run pytest tests/unit/dsl/test_footprint_fab_property.py tests/unit/dsl/test_footprint.py tests/unit/test_import_graph.py`: passed, exit 0.
- [x] 3.2 Write `src/fenolite/dsl/assembly.py` (`ASSEMBLY_LIBRARY`, `clear_outline`, `fiducial_footprint`, `fiducial_symbol`) and `Design.fiducial`, with the keep-out through `rule_area`; test `clear_outline` against an exact `Fraction` computation (every vertex outside the circle or on it, every edge at a distance of at least `d / 2` from the centre) for diameters from 1 nm to 10 mm (scenarios of "Fiducials in the DSL"). Proof: `uv run pytest tests/unit/dsl/test_assembly_features.py -k "fiducial or outline" tests/unit/test_import_graph.py`; `uv run pyright src`.
  - Note: 2026-10-08, after c0118 was stacked on v0.4 (rebased onto 0.3.0): `Design.rule_area` (c0103) and `Design.hole` (c0102) are on the branch, so tasks 3.2 to 3.6 are no longer blocked; they are not started. `tests/unit/dsl/test_assembly_features.py::test_the_script_calls_wait_for_their_prerequisites` now asks for both prerequisites and for none or all three calls.
  - Result: 2026-10-08 (first pass): open: `Design.fiducial` needs `Design.rule_area` (c0103) and the generated definitions with unnumbered pads (c0102), which are not on this base. Done: `src/fenolite/dsl/assembly.py` with `ASSEMBLY_LIBRARY` and `clear_outline`, tested against an exact `Fraction` computation for diameters from 1 nm to 10 mm (`uv run pytest tests/unit/dsl/test_assembly_features.py`: 19 passed).
  - Result: 2026-10-08, on `v04-c0118-dsl` (base `1adc0ef`): done. `dsl/assembly.py` has `fiducial_footprint`, `fiducial_symbol`, `AssemblyFootprint` (the two unnumbered `smd` pads, which `Footprint.pad` refuses to an authored footprint) and `AssemblySymbol`; `clear_outline` now returns its vertices in the order of the requirement, starting at `(x + a, y − b)` (the first pass started at `(x + b, y − a)`, the same octagon). `Design.fiducial` checks every argument and builds the keep-out with `dsl.items.rule_area` (the function behind `Design.rule_area`) before it records anything (design, Decision 5, "As implemented"). Scenarios "A global fiducial", "A local fiducial on the bottom" and "Refused fiducials" are tests. `uv run pytest tests/unit/dsl/test_assembly_features.py -k "fiducial or outline" tests/unit/test_import_graph.py`: 22 passed, exit 0; `uv run pyright src`: 0 errors, exit 0.
- [x] 3.3 Add `test_point_footprint`, `test_point_symbol` and `Design.test_point` (scenarios of "Test points in the DSL"). Proof: `uv run pytest tests/unit/dsl/test_assembly_features.py -k test_point tests/unit/dsl`.
  - Result: 2026-10-08 (first pass): open: needs the generated definitions of c0102 (not on this base).
  - Result: 2026-10-08, on `v04-c0118-dsl`: done. `test_point_footprint`, `test_point_symbol` and `Design.test_point`; the net's name is checked against the design's nets before anything is recorded. Scenarios "An SMD test point on a net", "A through-hole test point on the bottom" and "Refused test points" are tests. `uv run pytest tests/unit/dsl/test_assembly_features.py -k test_point tests/unit/dsl`: 4 passed, exit 0 (the `-k` filters the whole folder); `uv run pytest tests/unit/dsl`: 761 passed, exit 0.
- [x] 3.4 Add `tooling_hole_footprint` and `Design.tooling_hole`, with c0102's hole symbol (scenarios of "Tooling holes in the DSL"). If task 0.1 found c0096 on `dev`, add a test that a design with one `tooling_hole()` and one `hole()` of the same drill at another place gives no duplicate-drill finding of c0096's check. Proof: `uv run pytest tests/unit/dsl/test_assembly_features.py -k tooling tests/unit/dsl`.
  - Result: 2026-10-08 (first pass): open: needs c0102's hole part and `Fenolite_Holes:Hole` (not on this base).
  - Result: 2026-10-08, on `v04-c0118-dsl`: done. `tooling_hole_footprint` is the not-plated pad of `hole()` in a `HoleFootprint` named `Fenolite_Assembly:ToolingHole_<d>[_Clear<c>]`, with c0102's flags and courtyards; the symbol is c0102's `Fenolite_Holes:Hole`, shared with `hole()`. With `clear`, the keep-out lies on every copper layer: `RuleArea.layers` records them by name, so the scenario reads `("F.Cu", "B.Cu")` where it said `layers is None` (corrected in the delta and in design Decision 5). c0096 is not on the branch, so no duplicate-drill test is due. `uv run pytest tests/unit/dsl/test_assembly_features.py -k tooling tests/unit/dsl`: 4 passed, exit 0.
- [x] 3.5 Write `tests/unit/lens/test_build_assembly.py` (scenarios of "Assembly and test features in a build"). In the Altium build, leave the parts of `fiducial()` and `tooling_hole()` out before the footprint check, write test points as ordinary parts, and give the two `altium.not-lowered` infos (`assembly features`, `pad properties`); test that a script without the three calls plans the same Altium files as before (scenario "Test point written, fiducial left out"). Proof: `uv run pytest tests/unit/lens/test_build_assembly.py tests/unit/lens tests/unit/backends/altium -k "assembly or altium or lower" tests/consistency`.
  - Result: 2026-10-08: open for the parts of `fiducial()` and `tooling_hole()` (tasks 3.2 and 3.4). Done: a part whose footprint holds a marked pad is written as an ordinary part, and one `altium.not-lowered` info of the kind "pad properties" names every written footprint with a marked pad; a script without a mark plans the same Altium files and issues as before. `uv run pytest tests/unit/lens/test_build_assembly.py`: 4 passed, exit 0.
  - Result: 2026-10-08, on `v04-c0118-dsl`: done, with Decision 13 corrected as its last bullet asks: c0102's `split_hole_parts` writes every part of the symbol `Fenolite_Holes:Hole` as a board hole, so a tooling hole is written as one and only fiducials are left out (`lens.altium.split_fiducial_parts`, before the footprint check, with one `altium.not-lowered` info of the kind `assembly features`). The delta "Assembly and test features in an Altium build", its scenario, the proposal and `docs/altium.md` say so. The KiCad build of "Features in a build" (targets 9 and 10), the courtyards seen by the placement guard, "Features rebuild to the same bytes" and a script without the calls are tests in the same file; `tests/unit/cli/test_testpoints_cmd.py` has the CSV of that build with the `tooling_hole` row of `TH1`. `uv run pytest tests/unit/lens/test_build_assembly.py tests/unit/lens tests/unit/backends/altium -k "assembly or altium or lower" tests/consistency`: 2969 passed, 5 skipped, exit 0.
- [x] 3.6 Build the benches of task 1.3 from a script with the three calls; the outcomes of task 1.3 MUST NOT change; add `asm-tooling-drill` and `asm-features-pos` (scenario "Built features on both majors"). Proof: `uv run pytest tests/kicad/assembly/test_features_oracle.py -rA` on 10.0.6 and inside the 9.0.9 image.
  - Result: 2026-10-08 (first pass): open: needs the three calls (tasks 3.2 to 3.4).
  - Result: 2026-10-08, on `v04-c0118-dsl`: open, owed: CI (no `kicad-cli` on this machine). The three calls exist, and `tests/_asmfeatures.CALLS` holds the lines of "Features in a build" for the bench; building the bench of task 1.3 from them, the probes `asm-tooling-drill` and `asm-features-pos`, and their outcomes on 10.0.6 and 9.0.9 need a run with `kicad-cli`.
  - 2026-10-08, on `v04-close-c` (`d6e6a19`): written; awaits the CI run. `tests/kicad/assembly/test_built_features.py` builds the blink with the three calls of `_asmfeatures.CALLS` for the target the running major loads best and checks, on that board, what the probes of task 1.3 check (no DRC violation names `FID1`, `FID2`, `TP1` or `TH1`, the library checks aside; the mask circle of 2 mm at each fiducial; one `327` record on no net per fiducial, covered on the other side) and the two new outcomes: `asm-tooling-drill` (one not-plated hit at the centre of `TH1`, a tool of 3 mm) and `asm-features-pos` (the position file lists `FID1` and `FID2` at their places, and neither `TP1` nor `TH1`). They are asserted in the file and become registered probes once a run has shown them on both majors. Locally (no `kicad-cli`): 6 tests collected, skipped cleanly; their hermetic half (the build and the uuids of the four features) was run with `kicad-cli` mocked out and passes.
  - 2026-10-08, on `v04-ci-ticks`: done. `tests/kicad/assembly/test_built_features.py` (the blink with `_asmfeatures.CALLS`: `FID1`, `FID2`, `TP1`, `TH1`) passed its six tests in both jobs of CI run 37803522539 on `a105cc0`: `kicad-10` (10.0.6) and `kicad-9` (9.0.9, `-rA`: `test_the_built_board_holds_the_features`, `test_built_features_drc`, `test_built_fiducial_mask`, `test_built_fiducial_d356`, `test_tooling_drill`, `test_features_pos` PASSED). So the outcomes of task 1.3 hold on the built features (no violation names a feature, the 2 mm mask flash, the `327` record on no net), and `asm-tooling-drill` (one NPTH hit of 3 mm at the hole) and `asm-features-pos` (the two fiducials listed, no test point or hole) hold on both majors. They are asserted tests, not registered probes: their outcome has no line in the probe files.

## 4. Report

- [x] 4.1 Write `src/fenolite/exports/testpoints.py`: the rows, the access rule and the coverage, and `tests/unit/exports/test_testpoints.py` (scenarios of "Test-point report rows" and "Test-point coverage"). Proof: `uv run pytest tests/unit/exports/test_testpoints.py tests/unit/test_import_graph.py`; `uv run pyright src`.
  - Result: 2026-10-08: `uv run pytest tests/unit/exports/test_testpoints.py tests/unit/test_import_graph.py`: passed, exit 0; `uv run pyright src`: 0 errors. `Report` also holds `marked`, the marked pads of the whole board, so that a one-sided report of a marked board gives no `testpoint.none`.
- [x] 4.2 Add `findings`, the six codes in `exports/codes.py` with one entry each in `src/fenolite/cli/data/explain.toml` (`testpoint.covered`, `testpoint.no-net`, `testpoint.none`, `testpoint.coverage-low`, `testpoint.too-close`, `fiducial.too-few`), and `EVIDENCE` (scenarios of "Assembly and test findings"), with property tests of the pitch rule against a brute-force comparison in `Fraction`. Proof: `uv run pytest tests/unit/exports/test_testpoints.py -k findings tests/unit/cli/test_explain_cmd.py`.
  - Result: 2026-10-08: `uv run pytest tests/unit/exports/test_testpoints.py -k findings tests/unit/cli/test_explain_cmd.py`: passed, exit 0. The six entries of `explain.toml` are at their sorted places; no other entry was touched.
- [x] 4.3 Write `src/fenolite/cli/cmd_testpoints.py` with the CSV through the template's `[placement]` table, and `tests/unit/cli/test_testpoints_cmd.py` (scenarios of "Testpoints command"); add `testpoints` to `tests/unit/cli/test_check_readonly.py`; declare `paged="test_points"`, with a paging test in the same file. Proof: `uv run pytest tests/unit/cli/test_testpoints_cmd.py tests/unit/cli/test_check_readonly.py tests/unit/cli/test_hermetic_examples.py tests/consistency`.
  - Result: 2026-10-08: `uv run pytest tests/unit/cli/test_testpoints_cmd.py tests/unit/cli/test_check_readonly.py tests/unit/cli/test_hermetic_examples.py tests/consistency`: passed, exit 0. The built board of the command tests is the blink with an authored test pad and two authored fiducial marks (`tests/_asmfeatures.py`): the scenarios that name `TH1` and the build of "Features in a build" wait for task group 3.
- [x] 4.4 Write `tests/kicad/assembly/test_testpoints_d356.py` with the probe `asm-testpoint-d356` (scenario "Four kinds of test pad"). If a row and its record disagree, stop and correct the access rule from the records first. Proof: `uv run pytest tests/kicad/assembly/test_testpoints_d356.py -rA` on 10.0.6 and inside the 9.0.9 image; `uv run pytest tests/kicad/test_probe_results.py`.
  - Result: 2026-10-08: done for KiCad 10.0.6, open for 9.0.9 (as task 1.2). The four test pads are written through the model API, not by `design.test_point()` (task 3.3). On 10.0.6, targets 9 and 10: the rows have the access `top`, `bottom`, `both` and `none`, the records hold `A01 S2`, `A02 S1`, `A00 S0` and `A01 S3`, and `asm-testpoint-d356` = `equal`; the access rule needed no correction. `FENOLITE_REQUIRE=kicad uv run pytest tests/kicad/assembly/test_testpoints_d356.py -rA`: 3 passed, exit 0.
  - 2026-10-08: the 9.0.9 half (`asm-testpoint-d356`) is in `tests/kicad/assembly/test_features_nine.py` with task 1.2: written; awaits the CI run (`kicad-9` job). The bench of that probe stays the model-API one; the built test point is checked by `test_built_features.py` (task 3.6).
  - 2026-10-08, on `v04-ci-ticks`: done for 9.0.9. The `kicad-9` job of CI run 37803522539 on `a105cc0` printed `asm-testpoint-d356` = `equal` (`test_features_nine.py`, `-rA`), the 10.0.6 outcome: the access rule needed no correction on either major. Registered for both majors and in `9.0.9.json`; `test_testpoints_d356.py` itself runs on 9.0.9 from the next `kicad-9` job.

## 5. Placement table

- [x] 5.1 Add `fiducial` to `PlacementRow` and `PlacedRow`, the field `fiducial` and the key `fiducials` to `exports/assembly.py` and `exports/placement.py`, and their tests (scenarios of "Fiducial rows in the placement table"); `tests/kicad/assembly/test_assembly_oracle.py` keeps passing. Proof: `uv run pytest tests/unit/exports/test_placement.py tests/unit/exports/test_assembly.py tests/unit/cli/test_pnp_cmd.py`; `uv run pytest tests/kicad/assembly/test_assembly_oracle.py -rA` on 10.0.6.
  - Result: 2026-10-08: `uv run pytest tests/unit/exports/test_placement.py tests/unit/exports/test_assembly.py tests/unit/cli/test_pnp_cmd.py`: passed, exit 0; `FENOLITE_REQUIRE=kicad uv run pytest tests/kicad/assembly/test_assembly_oracle.py -rA` on 10.0.6: 14 passed, exit 0. The fiducial of the command test is an authored part with a marked pad, not one of `design.fiducial()` (task 3.2).

## 6. Manifest

- [x] 6.1 Give `testpoints` its `--manifest` option (through `cli/_manifest.py`, as `pnp` has it) and add the kind `testpoints` to `exports.states.DERIVED` (scenarios "The CSV joins the manifest", "The test-point table joins the manifest" and "The test-point table follows its board"). Proof: `uv run pytest tests/unit/cli/test_testpoints_cmd.py tests/unit/exports/test_states.py tests/unit/exports`.
  - Result: 2026-10-08: `uv run pytest tests/unit/cli/test_testpoints_cmd.py tests/unit/exports/test_states.py tests/unit/exports`: passed, exit 0.

## 7. Documentation

- [x] 7.1 Update `docs/dsl.md` (a section "Assembly and test features": the three calls, their libraries and names, the keep-outs and why fiducials and tooling holes are locked, `fab_property=`, what KiCad's library parts lack), `docs/assembly.md` (the report, coverage, the targets, the CSV, fiducial rows), `docs/design-model.md` (the eight marks), `docs/cli-contract.md` (`testpoints` and its codes) and `docs/formats/kicad/libraries.md` (the counts of Context). Proof: `uv run pytest tests/consistency tests/unit/test_repo_layout.py tests/residue tests/unit/test_format_facts.py tests/unit/exports/test_assembly_guide.py`.
  - Result: 2026-10-08: done for what exists, open for the three calls. `docs/dsl.md` has the section "Assembly and test features" with `fab_property=`, what KiCad's library parts lack, and a plain statement that the three calls are not available yet; `docs/assembly.md` has the report, coverage, the targets, the CSV and the fiducial rows; `docs/design-model.md` the eight marks; `docs/cli-contract.md` the section `testpoints` with its codes; `docs/formats/kicad/libraries.md` the counts, counted again on 2026-10-08 in the library that KiCad 10.0.6 installs (they equal those of Context). `uv run pytest tests/consistency tests/unit/test_repo_layout.py tests/residue tests/unit/test_format_facts.py tests/unit/exports/test_assembly_guide.py`: 378 passed, 20 skipped, exit 0.
  - Result: 2026-10-08, on `v04-c0118-dsl`: done. "Assembly and test features" in `docs/dsl.md` now gives the three calls, their libraries and names, the keep-outs and why fiducials and tooling holes are locked, and what an Altium build does with them; `docs/altium.md` has the paragraph "Assembly and test features" and the two kinds in the row of `altium.not-lowered`. The same command with `tests/corpus/test_manifest.py`: 471 passed, 26 skipped, exit 0.
- [x] 7.2 If c0080 is archived, add one tested line each for `fiducial()`, `test_point()`, `tooling_hole()` and `fenolite testpoints` to its guide page; otherwise write "c0080 not archived" under this task. Proof: `uv run pytest tests/consistency` and the guide test that c0080 names.
  - Result: 2026-10-08: c0080 not archived (0 of 15 tasks on this base).
  - 2026-10-08, on `v04-close-c` (`d6e6a19`): c0080 is on `v04` with every task closed, so it counts as archived for v0.4. Page `placement`: its tested design block calls `design.fiducial("FID1", …)`, `design.test_point("TP2", gnd, …)` and `design.tooling_hole("TH1", …)`, with a bullet; page `fabrication` already ran `fenolite testpoints` in three tested lines and now names the two calls. The block builds for targets 9 and 10 (one `layout.unplaced` warning, from `C1`, as before) and should add no error to the KiCad check of `tests/unit/agent/test_pages_kicad.py` (`placement`, 0: open connections only), which the `kicad-10` job runs: the features have no pin on a new net but `TP2` on `GND`, already open. `uv run pytest tests/consistency`: passed; `uv run pytest tests/unit/agent -q`: 79 passed, 10 skipped (the `kicad-cli` cases).

## 8. Closing

- [x] 8.1 Run the residue scan and the tests an implementing agent runs. Proof: `uv run pytest tests/residue` and `uv run python tools/residue/scan.py` exit 0; `uv run python tools/gen_schemas.py --check` exits 0; `make check-fast` passes; the unit suite passes on Python 3.11 (`uv run --python 3.11 pytest tests/unit -q -n auto --dist loadfile`); `openspec validate c0118-assembly-test-features --strict --no-interactive` passes; the full `make check` and the pull request checks (`unit`, `kicad-9`, `kicad-10`) are run once at the merge by the coordinator, never by the implementing agent.
  - Result: 2026-10-08: open. Passed, each with exit 0: `uv run pytest tests/residue` with `tests/corpus/test_manifest.py` (85 passed), `uv run python tools/residue/scan.py` (0 hits), `tools/gen_schemas.py --check`, `tools/gen_evidence_matrix.py --check`, `uv run ruff check .`, `uv run ruff format --check .`, `uv run pyright src` (0 errors), `openspec validate --all --strict --no-interactive` (101 passed), the touched unit files (381 passed, 1 skipped) and the four oracle files on KiCad 10.0.6 (38 passed). Not finished when the commit was made: `make check-fast PYTEST_WORKERS=3` was still running, and the Python 3.11 unit run was not started.
  - 2026-10-08, on `v04-close-c` from `origin/v04` at `d6e6a19`, with the edits of this closing round staged: `make check-fast PYTEST_WORKERS=3` exits 0 (ruff, format, pyright, residue scan; 12888 passed, 29 skipped; a first run failed only on `tests/unit/test_evidence_matrix_page.py` before `docs/evidence/matrix.md` was regenerated); `uv run --isolated --python 3.11 --extra dev pytest tests/unit -q -n 3 -p no:cacheprovider` exits 0 (12497 passed, 25 skipped); `uv run pytest tests/residue tests/corpus/test_manifest.py` (82 passed, 3 skipped) and `uv run python tools/residue/scan.py` (0 hits) exit 0; `uv run python tools/gen_schemas.py --check` exits 0; `openspec validate --all --strict --no-interactive` gives only the errors that were there before (c0084, c0085 twice, c0086, c0108, c0128) and long-requirement warnings; `python3 tools/dco_check.py origin/v04..HEAD` prints nothing. Three workers in place of four, as parallel agents share the machine.
- [x] 8.2 Update the evidence labels: the five rows become `KICAD-VERIFIED` with the scope of "Evidence level per behaviour", or record what was refuted and the part that stopped; raise `exports.testpoints.EVIDENCE` only when `H-K-TESTPOINT-D356` and `H-K-PAD-FABPROP` hold on both majors. Proof: `uv run pytest tests/unit/test_provenance.py tests/unit/test_hypotheses_register.py tests/kicad/test_probe_results.py`.
  - Result: 2026-10-08: open: the five rows stay `INFERRED` and `exports.testpoints.EVIDENCE` stays `INFERRED`, because the 9.0.9 half of every criterion is not recorded (tasks 1.2, 1.3 and 4.4). Nothing was refuted: every 10.0.6 outcome is the expected one, and each row records the run. `uv run pytest tests/unit/test_provenance.py tests/unit/test_hypotheses_register.py`: passed; `tests/kicad/test_probe_results.py` fails on this base for another change's probes (task 1.2).
  - 2026-10-08: still open: the five rows need the 9.0.9 outcomes of `tests/kicad/assembly/test_features_nine.py` (written; awaits the CI run, task 1.2); `exports.testpoints.EVIDENCE` stays `INFERRED` until `H-K-TESTPOINT-D356` and `H-K-PAD-FABPROP` hold on both majors.
  - 2026-10-08, on `v04-ci-ticks`: done. `H-K-PAD-FABPROP`, `H-K-PAD-FABPROP-LIB`, `H-K-FIDUCIAL-FORM`, `H-K-FIDUCIAL-KEEPOUT` (the refill on 10.0.x only, as "Evidence level per behaviour" scopes it) and `H-K-TESTPOINT-D356` are `KICAD-VERIFIED (9.0.x, 10.0.x)`, from the 9.0.9 outcomes of CI run 37803522539 (tasks 1.2, 1.3 and 4.4); nothing was refuted. `H-K-PAD-FABPROP` names what its probes do not measure on 9.0.9 (the drop of `pressfit`, the re-save). `exports.testpoints.EVIDENCE` is `KICAD-VERIFIED`, since `H-K-TESTPOINT-D356` and `H-K-PAD-FABPROP` hold on both majors; `docs/cli-contract.md` (`testpoints`) says so. `uv run pytest tests/unit/test_provenance.py tests/unit/test_hypotheses_register.py`: passed; `tests/kicad/test_probe_results.py` needs `kicad-cli` (skipped here) and checks the new `9.0.9.json` lines in the next `kicad-9` job.
- [x] 8.3 Add to `CHANGELOG.md` under Unreleased: "Pads keep KiCad's fabrication marks (fiducial, test point, BGA, heatsink, castellated, mechanical, press-fit) in the model. A script places fiducials, test points and tooling holes with `design.fiducial()`, `design.test_point()` and `design.tooling_hole()`, whose footprints are generated and whose fiducials and tooling holes get a copper keep-out; authored pads take `fab_property=`. New command `testpoints`: test points, fiducials, holes, net coverage and the user's targets, and a CSV. Placement tables mark fiducial rows. An Altium build writes test points as parts and leaves fiducials and tooling holes out. Releases 0.2.x and 0.3.0 cannot read a model document that carries `fab_property`." Update `docs/roadmap.md` (the line of c0118 under "v0.4", and the panel question). Proof: `git diff --stat CHANGELOG.md docs/roadmap.md` lists both files.
  - Result: 2026-10-08: the entry is at the end of "Unreleased" in `CHANGELOG.md`, worded for the part that is implemented (it says that the three script calls are not in it yet). `docs/roadmap.md` is not edited: the coordinator of the wave edits it. `git diff --stat CHANGELOG.md` lists the file.
  - The CHANGELOG line of this round is under `### Changed` of `## [Unreleased]`, and the row of this change in `docs/roadmap.md` (v0.4, the complex board) says what ships in 0.4. `git diff --stat CHANGELOG.md docs/roadmap.md` lists both files. The entry was written for the whole change before this round; it says the 9.0.9 run is open.
