lgili/Fenolite/openspec/changes/c0080-agent-authoring-guide/tasks.md

## 0. Entry check

- [x] 0.1 Read the living `agent-guide` and `cli-contract` specs, `openspec list` and `fenolite capabilities --brief --json`. Write under this task, with the date and the commit:
  - that `0.3.0` is released and that c0077 and c0079 are archived (stop here otherwise);
  - the public commands on `dev` that day, each with the page of Decision 1 that takes its line. The table of Decision 1 places the 30 commands of `9aba2dff`, the three of c0079 and `fetch`; a command that is not in it (one of c0096, c0097, c0099 or of another change archived since) is placed here;
  - the names of `fenolite.dsl.__all__` that day, each with its page or its reason in `DSL_NOT_TAUGHT` (`MechanicalIntent` when c0096 is on `dev`);
  - the codes of the `FEN-` registry that day;
  - the Altium write kinds with the status and the evidence level that `capabilities` reports for each (the table of the page `altium`);
  - the smallest case for which the suites already get `FEN-7001` from a write (the `lossy` sandbox);
  - what `check` and `explain` answer for two crossed tracks (the session of 2026-10-05 repeated: the codes, whether `hint` is empty, the form of `where`), on the `copper.short` finding as it is with or without c0097;
  - the first batch of `docs/evidence/agent-eval.md` if c0081 has run one, with the failures it lists (each becomes a recipe or a paragraph of a page).
  Proof: `openspec validate c0080-agent-authoring-guide --strict --no-interactive` passes after any re-base, and the notes hold each of the lists above.
  - **Not ticked: its first statement does not hold on this base.** 2026-10-08, base `15964cc3` (the integration branch of v0.4): `fenolite --version` is 0.2.1 and `0.3.0` is not released; c0077, c0078 and c0079 are implemented on the base and not archived; c0081, c0092, c0096, c0097 and c0099 are not on it. The wave implements this change all the same, so everything below was done for real and the other tasks do not wait. To close 0.1 after `0.3.0`: read the table of the page `altium` again (the test `altium_status` fails by itself when a kind graduates) and archive c0077 and c0079 first. Proof run: `openspec validate c0080-agent-authoring-guide --strict --no-interactive` exit 0 (the six requirements stay ADDED: the base has no living `agent-guide` spec, and c0079's delta holds none of the six names).
  - **Public commands, 35** (`fenolite capabilities --brief --json`), each with the page that holds its tested line: `design-script`: `init`, `build`, `sync`, `template`; `parts`: `catalog`; `placement`: `place`, `pads`, `neighbors`, `region`; `routing`: `route`, `fill`, `net`, `fetch` (c0078 is on the base); `rules`: `analyze`; `checks`: `check`, `explain`, `netlist`, `parity`, `doctor`, `capabilities`; `files`: `inspect`, `diff`, `equivalent`, `roundtrip`, `fmt`, `restore`; `fabrication`: `export`, `render`, `bom`, `pnp`, `manifest`, and `models` (not in the table of Decision 1; it lists the 3D models that `export --step` uses, so `fabrication` is the closest page); `altium`: `kit`; `recovery`: `guide`, `skill`. `place --strategy` takes `grid` and `manual` only: `constrained` (c0096) is not on the base.
  - **Names of `fenolite.dsl.__all__`, 62** (58 at `9aba2dff`, plus `protect`, `stack`, `stackup_locked`, `via_protection_locked`; no `MechanicalIntent`). Taught, 33: `design-script`: `Design`, `Module`, `Net`, `Part`, `connect`, `no_connect`, `mm`, `mil`, `inch`, `nm`; `parts`: `ohm`, `farad`, `henry`, `volt`, `amp`, `watt`, `hertz`, `second`, `Interface`, `I2C`, `SPI`, `UART`, `USB2`, `Harness`, `DiffPair`; `footprints`: `Footprint`, `Symbol`; `routing`: `via_step`, `arc_to`, `protect`; `rules`: `select`, `stack`; `altium`: `Power` (next item). In `DSL_NOT_TAUGHT`, 29: the 27 of Decision 1 and `stackup_locked`, `via_protection_locked` (the build calls them).
  - **`Power` is taught in the block of `altium`, not of `design-script`.** A KiCad build of a script that names catalog parts (`Fenolite:`) and adds a `Power` stops with exit 5, `build.vendor-unsafe-name`: "symbol libraries 'Fenolite' and 'fenolite' differ only in letter case" (the power symbols of the schematic are in a library `fenolite`). That is a defect of the base, outside this change ("Nothing changes in a build"). The page `design-script` teaches `Power` in prose and says what happens; `test_design_power_with_catalog_parts_is_refused` pins it, so the fix of the defect fails that test until the page is edited.
  - **After c0143 and c0111 were stacked beside this change** (2026-10-08): c0143 fixed that defect, so the page `design-script` now says that a `Power` builds with catalog parts and the test is `test_design_power_with_catalog_parts_builds` (exit 0, no `build.vendor-unsafe-name`, the flag in `lib/Fenolite.kicad_sym`). c0111 added `Anchor` and `AnchorRef` to `fenolite.dsl.__all__`: both are records that `part.at(…)` and `part.pad(…).at(…)` return, so they are in `DSL_NOT_TAUGHT` (31 names), and the design block of `routing` teaches the calls with an anchored waypoint. Proof run: `uv run pytest tests/unit/agent -q`: 82 passed.
  - **`FEN-` registry, 19 codes**: `FEN-1001`, `FEN-2001` to `FEN-2004`, `FEN-3001` to `FEN-3006`, `FEN-4001`, `FEN-5001`, `FEN-6001` to `FEN-6003`, `FEN-7001` to `FEN-7003` (`FEN-3006` and `FEN-6003` from c0078; none of c0120).
  - **Altium write kinds** (`fenolite capabilities --json --no-tools`): `write_kinds` of the Altium backend is empty; `matrix` has nine Altium rows with a `write` level, all `INFERRED` and all with `experimental: ["write"]`: `altium_harness`, `altium_outjob`, `altium_pcbdoc`, `altium_pcblib`, `altium_prjpcb`, `altium_schdoc_ascii`, `altium_schdoc_binary`, `altium_schdot`, `altium_schlib`.
  - **The `lossy` sandbox**: the starter with one `creepage` rule, built with `--kicad-version 9`: exit 7, `FEN-7001`, issue `rules.kind-unchecked`; with `--allow-lossy` exit 0 and `rules.dropped-for-target` (warning). It is the case of `docs/dsl.md`, "Rules with selectors".
  - **Two crossed tracks** (the starter with R1 and D1 exchanged, `route --router direct`, then `check --stages model.validate,copper.clearance`): exit 5, one issue `copper.short`, `where` = `/kicad_pcb/segment[0], /kicad_pcb/segment[2]` (file locators, not references), `hint` = `""` (still empty), message "copper of GND and VIN touches on F.Cu at (107.976091, 109.240987) mm". `fenolite explain copper.short` exits 0 with a `meaning` and a `fix`. After `place --move R1=15mm,14mm --move D1=15mm,6mm,180` (two `place.copper-left` warnings) and `route --router direct --rip`, the same check exits 0. c0097 is not on the base.
  - **c0081**: no harness and no `docs/evidence/agent-eval.md` on the base, so no first batch and no list of failures.
  - **Found on the way**: the start page of c0079 said `fenolite manifest blink/build --artifacts blink/fab --confirm`; that command exits 2 (`FEN-2001`, "the artefact folder … is not inside the project folder"), measured with kicad-cli 10.0.6. Task 3.4 rewrote that section, and the page `fabrication` exports into `blink/build/fab`.
  - **Closing note, 2026-10-08, base `04ef42a` (`v04`, rebased onto 0.3.0 in `9fb3513`).** `0.3.0` is released (`fenolite --version` prints `0.3.0`; `CHANGELOG.md` holds `## [0.3.0] - 2026-10-08`; the release record is the archived change `2026-10-08-c0150-release-0-3-0`). c0077 and c0079 are implemented on this base and closed for 0.4 in the same pass, not archived; release 0.4 is prepared from `v04` by the maintainer's decision of 2026-10-08, so the entry check is closed on this base. What changed since the note above: **public commands, 37** (`fenolite capabilities --json --no-tools`): the 35 above with `guide`, `init` and `skill` already counted, plus `impedance` (page `rules`) and `testpoints` (page `fabrication`), each with its tested line, and `models` on `fabrication`; `uv run pytest tests/unit/agent -q -k "coverage or altium_status or recipes or crossed or lossy or fen_codes"`: 20 passed, so every command, DSL name and error code has its page. **`fenolite.dsl.__all__`, 72 names**, of which 37 are in `DSL_NOT_TAUGHT` with a reason. **`FEN-` registry, 22 codes**: `FEN-1001` to `FEN-1003`, `FEN-2001` to `FEN-2004`, `FEN-3001` to `FEN-3006`, `FEN-4001`, `FEN-4002`, `FEN-5001`, `FEN-6001` to `FEN-6003`, `FEN-7001` to `FEN-7003` (`FEN-1002`, `FEN-1003`, `FEN-4002` and `FEN-6002` came with c0120 and others stacked on `v04`; the page `recovery` names each). **Altium write kinds**: 0.3.0 keeps every Altium write experimental (its changelog: "Every Altium write stays experimental in 0.3.0"), and `test_altium_status` passes against the table of the page `altium`. **The `lossy` sandbox and the crossed tracks**: their recipes pass (`tests/unit/agent/test_recipes.py`). **c0081**: its harness and `docs/evidence/agent-eval.md` are on this base; the `Runs` table is empty, because the runs with a real agent are deferred to the next release by the maintainer's decision of 2026-10-08, so there is no first batch and no failure to turn into a recipe. Proof: `openspec validate c0080-agent-authoring-guide --strict --no-interactive` gives no error (long-requirement warnings only).

## 1. Blocks and their tests

- [x] 1.1 Add `Block` and `blocks(page)` to `src/fenolite/agent/guide.py`, and write the block checks of `tests/unit/agent/test_pages.py`: allowed tags, `fenolite-cmd` through the real parser, `fenolite-design` built hermetically for targets 9 and 10 or for Altium (scenarios "Every command line parses", "Every design builds", "An untested block is refused"). They pass on the start page alone. Proof: `uv run pytest tests/unit/agent/test_pages.py -k "cmd or design or untested" tests/unit/agent/test_guide.py -q`; `uv run pyright src`.
  - 2026-10-08: `uv run pytest tests/unit/agent/test_pages.py -k "cmd or design or untested" tests/unit/agent/test_guide.py -q`: 22 passed, 37 deselected, exit 0 (run with all pages written: seven KiCad design blocks for targets 9 and 10, one Altium block, and the refused ones). `uv run pyright src`: 0 errors, exit 0. `Block.line_number` is the line of the opening fence in `Page.text`. `_copy` of `tests/unit/agent/test_guide.py` now empties `references/` of its copy, because that folder is no longer empty in the package.
- [x] 1.2 Add the budget and writing-rule checks (scenarios of "Page budgets and writing rules"). Proof: `uv run pytest tests/unit/agent/test_pages.py -k "budget or rules" -q`.
  - 2026-10-08: `uv run pytest tests/unit/agent/test_pages.py -k "budget or rules" -q`: 5 passed, 33 deselected, exit 0. The largest written page is `recovery` (about 9.2 kB, 180 lines); `commands` has 459 lines; the folder holds about 125 kB of 150 kB.

## 2. Generated pages

- [x] 2.1 Write `tools/gen_agent_guide.py` with `--check`, the pages `references/commands.md` and `references/dsl-reference.md`, the index between the markers of the start page, and `guide.DSL_NOT_TAUGHT` with a reason per name; add the generator's check to `make check-fast` (scenarios of "Generated guide pages"). Proof: `uv run python tools/gen_agent_guide.py --check` exits 0; `uv run pytest tests/unit/agent/test_pages.py -k generated tests/unit/test_spdx_headers.py -q`; `grep -c gen_agent_guide Makefile` is at least 1.
  - 2026-10-08: `uv run python tools/gen_agent_guide.py --check` exit 0; `uv run pytest tests/unit/agent/test_pages.py -k generated tests/unit/test_spdx_headers.py -q`: 3 passed, 37 deselected, exit 0 (the `-k` deselects the header tests, which run whole in the closing proofs); `grep -c gen_agent_guide Makefile`: 2. The check is a second line of the target `lint`, which `check` and `check-fast` both run: `tests/unit/test_parallel_runs.py` (capability ci-baseline) fixes the list of their prerequisites, so no target was added. `dsl-reference` also lists the functions of the modules `select` and `stack`; its first sentences leave out references to `docs/` and change ids, so that the page obeys the writing rules.

## 3. Written pages

Each task writes its pages from the code and from runs of the commands, in Fenolite's own words, gives every command of Decision 1 its tested line, and keeps the block, budget and writing-rule tests green.

- [x] 3.1 Write `design-script` and `parts` (with the units and the interfaces). Proof: `uv run pytest tests/unit/agent/test_pages.py -k "topics or cmd or design or budget or rules" -q`; `uv run fenolite guide design-script --text` and `uv run fenolite guide parts --text` exit 0.
  - 2026-10-08: `uv run pytest tests/unit/agent/test_pages.py -k "topics or cmd or design or budget or rules" -q`: 27 passed, 11 deselected, exit 0. `uv run fenolite guide design-script --text` and `uv run fenolite guide parts --text`: exit 0. `parts` has two design blocks (values with a pad map and properties; interfaces) and stays at 7 kB, so there is no page `interfaces`.
- [x] 3.2 Write `footprints` and `placement`. Proof: the same test selection; `uv run fenolite guide placement --text` names `fenolite pads` and `place --move`.
  - 2026-10-08: the same selection, 27 passed, exit 0. `uv run fenolite guide placement --text`: exit 0, names `fenolite pads` (2 lines) and `place --move` (1).
- [x] 3.3 Write `routing` and `rules` (scenario "A page through the command line"). Name `fenolite fetch freerouting` only when c0078 is archived. Proof: the same test selection; `uv run fenolite guide routing --text` names `direct`, `--rip`, `design.track` and `fenolite fill`.
  - 2026-10-08: the same selection, 27 passed, exit 0. `uv run fenolite guide routing --text`: exit 0, names `direct`, `--rip`, `design.track` and `fenolite fill`; `fenolite fetch freerouting` has its two lines, c0078 being on the base. The design block of the page was also run through kicad-cli 10.0.6: after `fenolite fill`, `fenolite check` exits 0 (`FENOLITE_REQUIRE=kicad uv run pytest tests/unit/agent/test_pages_kicad.py -q`: 9 passed, exit 0; the file is marked for KiCad 10, so a KiCad 9 runner skips it).
- [x] 3.4 Write `checks`, `files` and `fabrication`, and turn the section "Small questions between the steps" of the start page into one line per page. Proof: the same test selection; `uv run pytest tests/unit/test_agent_skill.py -q`; `uv run fenolite guide files --text` names `roundtrip`, `diff`, `equivalent` and `restore`.
  - 2026-10-08: the same selection, 27 passed, exit 0; `uv run pytest tests/unit/test_agent_skill.py -q`: 16 passed, exit 0; `uv run fenolite guide files --text`: exit 0, names `roundtrip`, `diff`, `equivalent` and `restore`. The start page has 174 lines; its section on small questions is seven items, one per page.
- [x] 3.5 Write `altium` with its table of write kinds; its script is tagged `fenolite-design altium` (scenario "Altium status follows capabilities"). Proof: `uv run pytest tests/unit/agent/test_pages.py -k "design or altium_status" -q`.
  - 2026-10-08: `uv run pytest tests/unit/agent/test_pages.py -k "design or altium_status" -q`: 19 passed, 19 deselected, exit 0. The table has nine rows, all `experimental` and `INFERRED`, as the base reports; it is read again after c0092 and `0.3.0` (the test fails until then).

## 4. Recovery

- [x] 4.1 Write `tests/unit/agent/_sandbox.py` (`SANDBOXES`: `starter`, `bad-lib-id`, `script-error`, `crossed`, `lossy`, each with its corrected form where the recipe needs one) and `tests/unit/agent/test_recipes.py` with the recipe runner (scenario "A recipe that lies fails"). The sandboxes are built in code from the starter; no file is added under `tests/data`, so `tests/data/MANIFEST.toml` does not change. Proof: `uv run pytest tests/unit/agent/test_recipes.py -k "runner or lies" tests/corpus/test_manifest.py -q`.
  - 2026-10-08: `uv run pytest tests/unit/agent/test_recipes.py -k "runner or lies" tests/corpus/test_manifest.py -q`: 3 passed, 58 deselected, exit 0. No file under `tests/data`. `tests/unit/agent/conftest.py` puts the folder on the path and gives the fixture `no_tools`.
- [x] 4.2 Write the page `recovery`: the seven recipes and the table of the remaining codes (scenarios "Recipes behave as written", "Crossed tracks are repaired", "Every error code is named"). Proof: `uv run pytest tests/unit/agent/test_recipes.py tests/unit/agent/test_pages.py -k "recipes or crossed or fen_codes or budget" -q`.
  - 2026-10-08: `uv run pytest tests/unit/agent/test_recipes.py tests/unit/agent/test_pages.py -k "recipes or crossed or fen_codes or budget" -q`: 16 passed, 36 deselected, exit 0. The page shows the broken and the fixed line of a script as a `text` block that a test compares with the sandboxes, not as a second whole `fenolite-design` block (design, Decision 6): two more whole scripts do not fit the byte budget. `where` of `FEN-3004` is `<path of the script>:line:<n>`, so the page says "ends with `line:N`".

## 5. Coverage

- [x] 5.1 Add the coverage checks (scenarios of "Guide covers the public surface"), add the missing lines they report, and add the rule to `AGENTS.md` (Workflow) and `CONTRIBUTING.md`. Proof: `uv run pytest tests/unit/agent/test_pages.py -k coverage tests/unit/test_agent_skill.py tests/residue -q`.
  - 2026-10-08: `uv run pytest tests/unit/agent/test_pages.py -k coverage tests/unit/test_agent_skill.py tests/residue -q`: 4 passed, 88 deselected, exit 0 (the `-k` deselects the other two files; both run whole in the closing proofs). No line was missing. A DSL name counts as taught when the code of a design block uses it as a bare name: comments, texts, attributes after a dot and keywords of a call do not count.

## 6. Closing

- [x] 6.1 Update the evidence: no hypothesis is registered by this change. If c0081's harness exists, ask the maintainer for the second batch and record its row beside the first in `docs/evidence/agent-eval.md`; if it does not, or the maintainer does not start the batch, say so under this task. Proof: `uv run pytest tests/unit/test_provenance.py tests/unit/test_hypotheses_register.py -q`.
  - 2026-10-08: `uv run pytest tests/unit/test_provenance.py tests/unit/test_hypotheses_register.py -q`: 44 passed, exit 0. No hypothesis and no source is registered. c0081's harness is not on this base: there is no first batch, no second batch was asked for, and `docs/evidence/agent-eval.md` does not exist. The effect of the pages on an agent is not measured.
- [x] 6.2 Add to `CHANGELOG.md` under `## [Unreleased]`: "**The agent guide teaches how to design a board**: eleven pages (`fenolite guide <topic>`) on the design script, parts, footprints, placement, routing, rules, checks, reading and comparing files, fabrication files, the Altium target and recovery, plus generated command and DSL references. Every command line, design script and recovery recipe of the guide is run by tests, and **a new command, DSL name or error code must be added to it**". Update the row of this change in `docs/roadmap.md`. Proof: `git diff --stat HEAD -- CHANGELOG.md docs/roadmap.md` lists both files.
  - **Open.** 2026-10-08: the entry is in `CHANGELOG.md`, at the end of `## [Unreleased]`. `docs/roadmap.md` is not edited on this branch: the coordinator of the wave edits it for the stacked branches, so the proof (both files in the diff) does not pass here.
  - 2026-10-08, base `04ef42a`: ticked. `CHANGELOG.md` held the entry twice (a shorter copy from the stacking of the branches); the copy is removed and the longer entry kept. The row of c0080 in `docs/roadmap.md` says that it ships in 0.4; `git diff --stat HEAD -- CHANGELOG.md docs/roadmap.md` lists both files.
- [x] 6.3 Stop and report "ready for the long runs": `make check-fast` (which now runs `tools/gen_agent_guide.py --check`), the unit suite on Python 3.11 (`uv run --python 3.11 pytest tests/unit -q`), `uv run pytest tests/residue tests/corpus/test_manifest.py -q` after `git add -A`, `uv run python tools/residue/scan.py`, `uv build` (the wheel lists the thirteen pages), and `openspec validate --all --strict --no-interactive`. The full `make check` is run once by the coordinator on the rebased branch, not by the implementing agent. Proof: each command exits 0.
  - **Open: two of its runs were not made, and `make check-fast` exits 2 for failures of the base.** 2026-10-08:
    - `make check-fast PYTEST_WORKERS=3`, run once: lint, format, types and residue pass; tests 6 failed, 10870 passed, 24 skipped, exit 2. Two failures were this branch's (`tests/unit/test_parallel_runs.py` fixes the prerequisites of `check` and `check-fast`; the guide check then moved into the target `lint`, and the file passes: 3 passed). Four fail the same way on a clean checkout of `15964cc3`: `tests/unit/test_spdx_headers.py::test_every_python_file_has_the_header` (`tools/yardstick.py` starts with a `#!` line) and three of `tests/unit/lens/test_altium_rta2.py` (`examples/yardstick/design.py` is not classified, and its Altium build exits 5). None is touched by this change; they are left to the coordinator. `make check-fast` was not run a second time.
    - The unit suite on Python 3.11 was run for the files of this change only: `uv run --offline --isolated --python 3.11 --extra dev pytest tests/unit/agent tests/unit/test_agent_skill.py -q`: 98 passed, exit 0. The whole `tests/unit` on 3.11 was not run.
    - `uv run pytest tests/corpus/test_manifest.py tests/residue -q` after `git add -A`: 85 passed, exit 0. `uv run python tools/residue/scan.py`: 0 hits, exit 0. `uv build --offline --wheel`: exit 0, the wheel lists `SKILL.md` and the thirteen pages. `openspec validate --all --strict --no-interactive`: 101 passed, exit 0. `uv run python tools/gen_schemas.py --check` and `tools/gen_evidence_matrix.py --check`: exit 0.
  - 2026-10-08, branch `v04-close-a` on `04ef42a`, with every edit of the closing pass of c0077 to c0103 in the tree (the gate of the release, run once for all of them): `make check-fast PYTEST_WORKERS=4` exits 0 (ruff check, the guide's `--check`, ruff format, pyright, the residue scan, and 12731 passed, 29 skipped); the whole unit suite on Python 3.11.15, `uv run --isolated --python 3.11 --extra dev pytest tests/unit -q -n 4 -p no:cacheprovider`: 12348 passed, 25 skipped, exit 0; after `git add -A`, `uv run pytest tests/residue tests/corpus/test_manifest.py -q`: 80 passed, 5 skipped (no `kicad-cli`, no KiCad libraries), exit 0; `uv run python tools/residue/scan.py`: 0 hits, exit 0; `openspec validate --all --strict --no-interactive` reports the same six errors as on `04ef42a` (c0084, c0085 twice, c0086, c0108, c0128) and none of this change, besides the long-requirement warnings. The full `make check` is the coordinator's. `uv build --wheel`: exit 0, the wheel lists `SKILL.md` and the thirteen pages.
