lgili/Fenolite/openspec/changes/c0106-length-measure-tune/tasks.md

## 0. Entry check

- [x] 0.1 Read the living `board-analyses`, `backend-protocol`, `board-frame`, `geometry-kernel`, `verification-loop`, `design-dsl`, `manual-copper`, `kicad-oracle`, `design-equivalence` and `altium-verification` specs and `openspec list`. Check the prerequisites of the proposal: release `0.3.0` cut; c0104 and c0101 archived. Note that c0066 and c0089 are archived, and read `checks/equivalence/routing.py` (its `arc_length`, `_distance` and their callers) and `checks/stages.py` and `checks/documents.py` (the two stage lists) as they are that day. Check that the seven hypothesis ids and the fifteen issue codes are still free (`docs/hypotheses.md`, `src/fenolite/cli/data/explain.toml`). Write under this task, with the date and the commit of `dev`: whether c0104 is archived and the names it gave (the rule kinds and their limits, the mark of a skew rule judged within pairs, the pair entity, how a pair selector matches a `RuleSubject`), then adapt "Length rules stage", "Pair skew in the length report" and their scenarios to those names before code starts; whether c0101 is archived (`Board.stackup` read and written, a board thickness in the model); whether c0100 is archived; whether c0123 landed (two pads of one number and the start-pad rule); and whether another change added a requirement of the same name as one of this change's fifteen. Proof: `openspec validate c0106-length-measure-tune --strict --no-interactive` passes after any adaptation.
  - Read on 2026-10-08, on the v0.4 integration base `15964cc3` (dev plus the proposals and the first changes of the milestone). Still open because c0104 is not on this base, so its names cannot be confirmed and "Length rules stage" and "Pair skew in the length report" are not adapted. What was found:
  - Release `0.3.0` is not cut on this base.
  - **c0104: not implemented** (0 of 29 tasks). `RuleKind` holds the twelve kinds of c0071, `RuleSubject` has no `diff_pair`, `model/pairs.py` does not exist. Tasks 4.3 (pair rows), 6.1 (the stage) and the stage half of 7.1 wait for it.
  - c0101: implemented on this base, not archived (`Board.stackup` read and written, `Stackup.depth`; the model holds no board thickness, the reader keeps `(general (thickness …))` opaque). The depths use it.
  - c0100: implemented on this base, not archived (boards of 6 and 8 copper layers), so task 1.3 was run.
  - c0123: implemented on this base (several pads of one number). The start-pad rule sorts by `(ref, number)` and then by pad id, and `test_two_pads_of_one_number` covers two pads of one number.
  - c0066 and c0089 are archived. `checks/equivalence/routing.py` held its own `arc_length` (128 bits) and `_distance`; `checks/stages.py` and `checks/documents.py` hold the two stage lists as the design describes them.
  - The seven hypothesis ids and the fifteen issue codes were free; no living requirement has one of the fifteen names (`grep` over `openspec/specs`, 0 matches).
  - Proof: `openspec validate c0106-length-measure-tune --strict --no-interactive` exit 0, after the delta amendments listed under 1.2, 3.2, 4.1 and 8.2.
  - 2026-10-08, on `v04` at `1adc0ef` (c0104 stacked, implemented, not archived): c0104's names are those this change assumed, so "Length rules stage" needs no adaptation: the kinds `length` (`min`, `opt`, `max`), `skew` and `diff_pair_skew` (`model.rules.RuleKind`; a hand-written `skew … (within_diff_pairs)` lifts to `diff_pair_skew`); no pair entity besides `Interface`, whose kind is a key of `model.pairs.PAIR_ROLES` (`diff_pair` with `p`, `n`; `usb2` with `dp`, `dn`), with `pair_nets` and `net_bases`; `RuleSubject.diff_pair` holds the base of `net_bases`, and the leaf matches it by `base_matches` (letter case counts; a base ending in `_` also matches without it). "Pair skew in the length report" lost its clause "until `model.pairs` exists, `pairs` is empty" and gained the scenario "Pair by name". Release `0.3.0` is still not cut, and c0104, c0101 and c0100 are still not archived, so the task stays open. The openspec CLI of this session (1.14.1) fails `--strict` on every change of the repository for its new warning "Requirement text is very long" (c0104 too); `openspec validate c0106-length-measure-tune --no-interactive` exit 0, and `--strict` gives no `ERROR`, warnings only.
  - 2026-10-08, on `v04` at `09ee580` (branch `v04-close-b`): checked again: `CHANGELOG.md` holds `## [0.3.0] - 2026-10-08` (c0150 archived; no tag `v0.3.0` on `origin`); c0104, c0101 and c0100 are built on the branch and not archived, and the names of c0104 are those adapted in the note above. The maintainer's decision of 2026-10-08 closes this change for 0.4 without the archives. `openspec validate c0106-length-measure-tune --strict --no-interactive`: no ERROR, the long-requirement warnings only, which the coordinator accepts for this release.

## 1. Probe and register

- [x] 1.1 Add the rows `H-K-NETLEN-TOTAL`, `H-K-NETLEN-VIA10`, `H-K-NETLEN-VIA9`, `H-K-NETLEN-STACKUP`, `H-K-NETLEN-RULES`, `H-G-NETLEN-PATH` and `H-K-NETLEN-MEANDER` to `docs/hypotheses.md` (level `INFERRED`, the tests and criteria of `design.md`, result `pending` with the measurements of Context as the first record). Proof: `uv run pytest tests/unit/test_hypotheses_register.py tests/unit/test_provenance.py`; `grep -cE '^\| H-[KG]-NETLEN-' docs/hypotheses.md` prints `7`.
  - Result, 2026-10-08: seven rows at the end of the register table; `uv run pytest tests/unit/test_hypotheses_register.py tests/unit/test_provenance.py` 44 passed, exit 0; the `grep` prints 7.
- [x] 1.2 Write `tests/_lengthbench.py`, the benches of Context (tables 1 to 4) for targets 9 and 10, built hermetically; the explicit stack-ups are set in `Board.stackup` and written into the file by c0101's writer, or by token edit while c0101 is not archived. Add one four-layer board whose stack-up node c0101's reader does not project, and record what KiCad counts for its vias (design, Risks). Write `tests/kicad/length/test_length_parity.py` with the bracket runs, the scoped canary and the probes of "Net length parity canaries", taking `T` from the hand-computed values of Context until task 3.3 lands. Record the outcomes. Proof: `uv run pytest tests/kicad/length/test_length_parity.py -rA` on the local KiCad 10.0.6 and inside the pinned 9.0.9 image; `FENOLITE_PROBES_WRITE=1` updates both probe files; `uv run pytest tests/kicad/test_probe_results.py`.
  - Result, 2026-10-08: done for KiCad 10.0.6; open for 9.0.9 (the pinned image is not run in this session) and for the full probe-file test.
  - 2026-10-08, integration onto `v04` (on c0104): the eleven `length-*` probes were run inside the pinned 9.0.9 image (`kicad/kicad:9.0.9` by digest, local) and are recorded in `docs/evidence/kicad/probes/9.0.9.json`: all `equal`, the outcomes of 10.0.6. `tests/kicad/length/test_length_parity.py` gives 18 passed on the local 10.0.6 and 18 passed inside the image; `FENOLITE_REQUIRE=kicad uv run pytest tests/kicad/test_probe_results.py` on 10.0.6: 1 passed (every probe registered for major 10 run again, 12 min 45 s). The probe-file test of 9.0.9 still lacks probes that other changes registered (c0104's pair probes, c0114's net-tie probes); none of them is of this change.
  - `tests/_lengthbench.py` holds the cases `two`, `two-stackup`, `two-noheight`, `four`, `four-explicit`, `four-unprojected`, `six`, `eight` and `rules`; the stack-ups go through `Board.stackup` and c0101's writer. `tests/kicad/length/_lengthcases.py` holds the runs and probes, and `T` already comes from `length_facts` (task 7.1).
  - `FENOLITE_REQUIRE=kicad uv run pytest tests/kicad/length/test_length_parity.py -rA` on 10.0.6: 18 passed, exit 0; the canary fired in every run.
  - The eleven `length-*` outcomes of 10.0.6 were merged into `docs/evidence/kicad/probes/10.0.6.json` by a script that runs only these probes (`FENOLITE_PROBES_WRITE=1` would rerun every probe of the major). **`9.0.9.json` holds none of them**, so `tests/kicad/test_probe_results.py` fails on 9.0.9 until they are written there; that test was not run in full on 10.0.6 either.
  - The node c0101's reader does not project: 10.0.6 counts the thicknesses of a node without silkscreen and paste rows (`length-via-four-unprojected` `equal` against the explicit totals; the default totals are not what it prints). So `length_facts` gives such a file no depth (`stackup` `none`) instead of the default; "KiCad net lengths" and "Net length parity canaries" were amended to say so.
- [x] 1.3 Once c0100 is archived: add six- and eight-layer boards without a stack-up to the benches, record the default stack-up there, and extend `H-K-NETLEN-STACKUP` or record what differs. Proof: `uv run pytest tests/kicad/length/test_length_parity.py -rA -k default_stackup` on both majors.
  - Result, 2026-10-08: done on 10.0.6: the cases `six` and `eight` (no stack-up) are `equal` (`length-via-six`, `length-via-eight`; dielectrics of 0.274 mm and 0.1857 mm), `-k default_stackup` 4 passed. Open for 9.0.9.
  - 2026-10-08, integration: `length-via-six` and `length-via-eight` are `equal` inside the pinned 9.0.9 image too and are recorded in `9.0.9.json`; `-k default_stackup` passes there (4 cases of the 21 of `tests/kicad/length`). The task stays open for its condition (c0100 archived).
  - 2026-10-08: ticked by CI run 37772583226 on `04ef42a` (all jobs green): `-k default_stackup` passed for `two`, `four`, `six` and `eight` in the `kicad-9` job (9.0.9) and in the `kicad-10` job (10.0.6), and `length-via-six` and `length-via-eight` are `equal` in both probe files; `H-K-NETLEN-STACKUP` is extended to 6 and 8 layers (task 10.3). c0100 is built on the branch and not archived; the maintainer's decision of 2026-10-08 closes this change for 0.4 without the archive.

## 2. Kernel lengths

- [x] 2.1 Write `src/fenolite/geometry/lengths.py` (`segment_length`, `arc_length`, `arc_length_to`) and re-export them; write `tests/unit/geometry/test_lengths.py` (scenarios "Segment", "Half circle and its quarter", "Points on a line", "Agreement with an independent computation"), with the comparison against `views.arc_length` and against `checks.equivalence.routing.arc_length` as they are before this task changes them, on generated arcs, on collinear points (`mid` between and outside the ends), on points of which two are equal and on the arcs of the level-5 fixtures. Write the count of inputs compared and any difference under this task; a difference stops the task until the requirement "Path lengths" is corrected to what `dev` returns. Proof: `uv run pytest tests/unit/geometry/test_lengths.py tests/unit/test_import_graph.py`; `uv run pyright src`.
  - Result, 2026-10-08: before the two copies were changed, the kernel was compared with `views.arc_length` and `routing.arc_length` on 12 001 inputs (4 000 generated arcs, 4 000 collinear triples with `mid` between and outside the ends, 4 000 triples with two or three equal points, the one arc of the level-5 fixtures): 0 differences with either. `uv run pytest tests/unit/geometry/test_lengths.py tests/unit/test_import_graph.py` 40 passed, exit 0; `uv run pyright src` 0 errors. One function more than the task names: `segment_length_to`, which `arc_length_to` uses for points that form no arc and the paths use to split a track ("Path lengths" amended).
- [x] 2.2 Make `analysis.views` and `checks.equivalence.routing` call the kernel and remove their own fixed-point arithmetic (scenario "Equivalence level 5 measures with the kernel"). Add one sentence to `docs/analyses.md` and one to `docs/equivalence.md`: `NetLength.routed` and the span lengths of `equiv.route-length` sum the same per-item lengths. Proof: `uv run pytest tests/unit/geometry/test_lengths.py tests/unit/analysis/test_views.py tests/unit/checks/equivalence tests/unit/test_import_graph.py`; the no-float scan of `tests/unit/analysis/test_report.py -k no_float` passes; `grep -c "_atan_fixed" src/fenolite/analysis/views.py src/fenolite/checks/equivalence/routing.py` prints 0 for both files.
  - Result, 2026-10-08: 174 passed, exit 0; `-k no_float` 1 passed; `grep -c "_atan_fixed"` prints 0 for both files. `routing.track_length` keeps its own exact sum of collinear tracks (not arc arithmetic); the sentence of `docs/equivalence.md` says that a span adds the tracks of one line before it rounds.

## 3. KiCad net lengths

- [x] 3.1 Add `NetLength`, `LengthFacts` and `LengthSource` to `src/fenolite/backends/base.py`, `KicadBackend.length_facts` and `_LENGTHS` (scenarios "KiCad backend is a length source" and "Records are plain data"). Proof: `uv run pytest tests/unit/backends/test_base_types.py -k "length_source or length_records" tests/unit/backends/test_registry.py -k base_imports`; `uv run pyright src`.
  - Result, 2026-10-08: `-k "length_source or length_records"` 2 passed, `test_registry.py -k base_imports` 2 passed, exit 0; `uv run pyright src` 0 errors.
- [x] 3.2 Write `layer_depths` (per major, from `Board.stackup` or the default stack-up), `die_lengths`, `counts_via_heights`, `LENGTH_ISSUE_CODES` and `EVIDENCE` in `src/fenolite/backends/kicad/lengths.py`, with `tests/unit/backends/kicad/test_lengths.py` (scenarios "Default stack-up" and "Die length and the project switch"), and the tables of `kicad.length.default-stackup` and `kicad.length.bad-die` in `cli/data/explain.toml`. Proof: `uv run pytest tests/unit/backends/kicad/test_lengths.py -k "default or die or switch" tests/unit/cli/test_explain_cmd.py`.
  - Result, 2026-10-08: 4 passed, exit 0 (the `-k` of the command also deselects the explain tests; `tests/unit/cli/test_explain_cmd.py` alone: 8 passed). `explain.TABLES` names `LENGTH_ISSUE_CODES`. `length_facts` reads the project file of its `ProjectSet` (one switch and the major), as `KicadBackend.design_rules` reads its two files; "KiCad net lengths" was amended, which said that no function reads a file.
- [x] 3.3 Write `joined_layers`, `via_height` per major, `net_lengths` and `length_facts` (scenarios "Via heights per major", "A pad joins a via" and "The total is the sum of its parts"). Proof: `uv run pytest tests/unit/backends/kicad/test_lengths.py tests/unit/backends/test_base_types.py tests/unit/test_import_graph.py`.
  - Result, 2026-10-08: 85 passed, exit 0.

## 4. Paths and pairs

- [x] 4.1 Write `LengthRow`, `LengthReport` and the totals of `measure_lengths` in `src/fenolite/analysis/length.py`, and the joins of Decision 7 (item ends, splits of tracks and arcs, pads met by a body, vias), with `tests/unit/analysis/test_length.py` (scenarios of "Net length report", and unit cases of every kind of join). Proof: `uv run pytest tests/unit/analysis/test_length.py -k "facts or selection or join"`.
  - Result, 2026-10-08: `-k "facts or selection or join"` 9 passed, exit 0. A via is joined like a pad (on a track body, and to the pad it stands in), which the scenario "KiCad 9 counts no height where the path does" needs; "Pin-to-pin length" was amended to say so.
- [x] 4.2 Write `PathRow`, the start pad, the search, `off_path` and the open pads (scenarios of "Pin-to-pin length"), with a property test: on generated unbranched chains of tracks, arcs and vias between two pads, the path equals the total with facts of major 10. Proof: `uv run pytest tests/unit/analysis/test_length.py`.
  - Result, 2026-10-08: 24 passed, exit 0; the property holds on 40 generated chains.
- [x] 4.3 Add `PairRow`, the pairs of the report, the two `analysis.length-*` codes with their tables in `cli/data/explain.toml`, and `analysis.length.EVIDENCE` (scenarios of "Pair skew in the length report" and "Length analysis issue codes"). Proof: `uv run pytest tests/unit/analysis tests/unit/cli/test_explain_cmd.py`; `uv run pyright src`.
  - Result, 2026-10-08: open: `model.pairs` (c0104) is not on this base, so `LengthReport.pairs` is always empty and no pair scenario runs. (2026-10-08, integration: c0104 is on the branch now; the pairs of the report were not written in the integration, the task stays open.) Done: the record `PairRow`, the two `analysis.length-*` codes with their tables, `analysis.length.EVIDENCE`. `uv run pytest tests/unit/analysis tests/unit/cli/test_explain_cmd.py` 265 passed, exit 0.
  - Result, 2026-10-08 (on `v04` at `1adc0ef`, c0104 stacked): the pairs of the report are written with c0104's pair model: each interface whose kind is a key of `PAIR_ROLES`, under its name, its nets from `pair_nets`; then each two measured nets that `net_bases` couples and no pair interface names, under their base, the positive net as `p`; sorted by name. `path_skew` when each net has one path (two pads) and both exist. Tests `-k pair`: the scenario "Pair one millimetre apart", a pair by name on the rules bench (`SK_`), a `usb2` interface with a path skew, and a pair whose second net is not measured. `uv run pytest tests/unit/analysis tests/unit/cli/test_explain_cmd.py tests/unit/cli/test_analyze_length.py` 314 passed, exit 0; `uv run pyright src` 0 errors, exit 0.

## 5. Analyze kind

- [x] 5.1 Add the kind `length` and the options `--net` and `--from` to `src/fenolite/cli/cmd_analyze.py`, with the major from the global `--kicad-version`, with `tests/unit/cli/test_analyze_length.py` (scenarios of "Length kind in the analyze command"), with a case on an Altium PCB document of the samples (no facts, one `analysis.input-missing`, `UNVERIFIED`), and document them in `docs/cli-contract.md`. Proof: `uv run pytest tests/unit/cli/test_analyze_length.py tests/unit/cli/test_analyze_cmd.py tests/unit/cli/test_check_readonly.py tests/consistency`.
  - Result, 2026-10-08: 347 passed, 19 skipped, exit 0. `result.inputs` gains `nets`, `from` and `kicad_version` only when the kind runs, so the default reply is unchanged. `tests/unit/cli/test_analyze_power.py` asserts the opt-in kinds and now names `length`.

## 6. Length rules stage (second in the cut order)

- [x] 6.1 Write `src/fenolite/checks/length.py`, the three `length.*` codes in `checks/codes.py` with their tables in `cli/data/explain.toml`, the stage in `STAGE_ORDER` (after `copper.clearance`, before `zone.fill`) with its runner in `run_checks`, and `tests/unit/checks/test_length_stage.py` (scenarios of "Length rules stage" and "Length stage issue codes"). Leave `checks.documents.DOCUMENT_STAGES` as it is (scenario "Altium input has no length stage"). Proof: `uv run pytest tests/unit/checks tests/unit/cli/test_check_cmd.py tests/unit/cli/test_check_readonly.py tests/unit/cli/test_explain_cmd.py tests/consistency`.
  - Result, 2026-10-08: not started: the stage judges the rule kinds `length`, `skew` and `diff_pair_skew` and the pair bases of c0104, which is not on this base. No `length.*` code, no stage, no `checks/length.py`.
  - 2026-10-08, integration: c0104 is on the branch now (`length`, `skew`, `diff_pair_skew`, `model.pairs`); the stage is a new module with three codes and was not written in the integration, the task stays open.
  - Result, 2026-10-08 (on `v04` at `1adc0ef`): `checks/length.py` (`length_stage`, `judge_lengths`, `governing`, `routed_lengths`, `EVIDENCE`), the three `length.*` codes in `checks/codes.py` and `explain.toml`, `length.rules` in `STAGE_ORDER` right after `copper.clearance` (so before `placement.rules` of c0113, which c0113's design placed after it, and before `zone.fill`), its runner in `run_checks` with the validator as rules and length source; `DOCUMENT_STAGES` unchanged. `tests/unit/checks/test_length_stage.py` 22 passed: the five scenarios, the rules cases of `H-K-NETLEN-RULES` on targets 9 and 10 through the command without `kicad-cli`, and fakes for precedence, `ignore`, the two skew kinds as one constraint, ties and the missing sources. Rule selectors are matched with names folded as the copper check folds them (`clearance.selector_matches`, design "Found on 2026-10-08 (length stage)"). The lists of stages in `test_stages.py`, `test_copper_stage.py`, `test_placement_stage.py`, `test_check_cmd.py` and the agent page `checks` name the stage. `uv run pytest tests/unit/checks tests/unit/cli/test_check_cmd.py tests/unit/cli/test_check_readonly.py tests/unit/cli/test_explain_cmd.py tests/consistency` 1058 passed, 21 skipped, exit 0.

## 7. Oracle

- [x] 7.1 Take `T` from `length_facts` in `test_length_parity.py`, add the stage's verdicts on the rules benches, and run the canaries on both majors (scenarios of "Net length parity canaries"). A probe that records `different` stops the part it settles, and what KiCad showed goes into the register row. Write `docs/formats/kicad/length.md` (every fact with S-0020 or S-0029, its label and its hypothesis) and `docs/evidence/length.md` (the printed `actual` values per case and major). Proof: `uv run pytest tests/kicad/length/test_length_parity.py -rA` on the local KiCad 10.0.6 and inside the pinned 9.0.9 image; `uv run pytest tests/unit/test_format_facts.py tests/kicad/test_probe_results.py`.
  - Result, 2026-10-08: open for the stage verdicts (6.1) and for 9.0.9. Done: `T` comes from `length_facts`; `-k rules` compares KiCad's violations with the nets `H-K-NETLEN-RULES` predicts (5 cases, equal on 10.0.6; no `length-rules-*` probe is registered until the stage exists); `docs/formats/kicad/length.md` and `docs/evidence/length.md` are written (the 9.0.9 column is the proposal's first record, marked as such). `uv run pytest tests/unit/test_format_facts.py` passes (66 passed with the register tests).
  - 2026-10-08 (on `v04` at `1adc0ef`): the stage verdicts are added to `test_rules` (`_lengthcases.stage_pairs`: the stage on the bench with the KiCad backend as both sources must name KiCad's nets); without `kicad-cli` the helper gives the predicted pairs for all five cases on targets 9 and 10. Owed: CI (the `kicad-9` and `kicad-10` jobs run `test_length_parity.py -k rules` with the stage; the `length-rules-*` probes are registered and recorded by that run). No `kicad-cli` in this session.
  - 2026-10-08: ticked by CI run 37772583226 on `04ef42a` (all jobs green): `tests/kicad/length/test_length_parity.py` passed whole in the `kicad-9` job (9.0.9; KiCad's printed lengths equal Fenolite's totals, and `test_rules` gives the stage's verdicts on the five cases equal to KiCad's violations) and in the `kicad-10` job (10.0.6); `tests/kicad/test_probe_results.py` passed on both. No `length-rules-*` probe is registered: `test_rules` compares the stage with KiCad's violations directly. `uv run pytest tests/unit/test_format_facts.py`: passed.

## 8. Meanders (first in the cut order)

- [x] 8.1 Add `Design.meander`, `MeanderIntent` and `dsl.meanders` to `dsl/intents.py`, `dsl/design.py` and `dsl/__init__.py` (scenarios of "Meanders in the DSL"). Proof: `uv run pytest tests/unit/dsl/test_meander_dsl.py tests/unit/dsl tests/unit/test_import_graph.py`.
  - Result, 2026-10-08: 506 passed, exit 0.
- [x] 8.2 Write `src/fenolite/backends/kicad/meander.py` (`MeanderIntentLike`, `resolve_meanders`, `LENGTH_TOLERANCE_NM`, `MEANDER_ISSUE_CODES`, `EVIDENCE`), the tables of the eight `kicad.meander.*` codes in `cli/data/explain.toml`, with `tests/unit/backends/kicad/test_meander.py` (scenarios of "Meanders from intents") and a property test on generated runs, directions and targets: the intent's length is within 10 nm of the target, or the meander is refused with a code of the table and the design is unchanged. Proof: `uv run pytest tests/unit/backends/kicad/test_meander.py tests/unit/cli/test_explain_cmd.py`; `uv run pyright src`.
  - Result, 2026-10-08: 22 passed, exit 0; `uv run pyright src` 0 errors. The property test: 300 generated runs, every one within 10 nm of its target or refused with a code of the table and the design unchanged. A missing length of 0 to 10 nm gives `kicad.meander.not-needed` (the task says exactly 0): it is already within the tolerance, and bumps of a few nanometres would be the alternative ("Meanders from intents" amended).
- [x] 8.3 Add `meanders=` to `build_design` with its step after `resolve_copper`, `result.copper.meanders`, the call in `cmd_build.py`, the authored design scripts of `tests/_meanderdesign.py` and `tests/unit/lens/test_build_meander.py` (scenarios of "Meanders in a build"). Proof: `uv run pytest tests/unit/lens/test_build_meander.py tests/unit/lens tests/unit/cli/test_build_command.py tests/consistency`.
  - Result, 2026-10-08: 323 passed, 19 skipped, exit 0 (`tests/unit/lens/test_build_meander.py`: 7 passed; the rest of `tests/unit/lens` ran in the broad run, where the only failures were the three `test_altium_rta2.py` tests of the yardstick example, which fail the same way on a clean checkout of `15964cc3`). `result.copper.meanders` is present only in the reply of a script with meanders. The Altium build passes the meanders to its in-memory KiCad build, and `kicad.meander.*` joins its script copper codes.
- [x] 8.4 Write `tests/kicad/length/test_meander_oracle.py` with the three designs and the probes `length-meander-*` (scenario "Meanders on both majors"). Proof: `uv run pytest tests/kicad/length/test_meander_oracle.py -rA` on the local KiCad 10.0.6 and inside the pinned 9.0.9 image.
  - Result, 2026-10-08: done on 10.0.6: `FENOLITE_REQUIRE=kicad uv run pytest tests/kicad/length/test_meander_oracle.py -rA` 3 passed, exit 0; `length-meander-axis`, `-angle` and `-pair` are `equal`. Open for 9.0.9.
  - 2026-10-08, integration onto `v04` (on c0104): the eleven `length-*` probes were run inside the pinned 9.0.9 image (`kicad/kicad:9.0.9` by digest, local) and are recorded in `docs/evidence/kicad/probes/9.0.9.json`: all `equal`, the outcomes of 10.0.6; `tests/kicad/length/test_meander_oracle.py` gives 3 passed inside the image and 3 passed on the local 10.0.6.

## 9. Documentation

- [x] 9.1 Update `docs/analyses.md` (the length kind: total and path, the counting of each major, the default stack-up, the limits listed in the proposal, the oracle of each behaviour), `docs/dsl.md` and `docs/copper.md` (`Design.meander`: its shape, its codes, its limits) and `docs/cli-contract.md` (`length.rules` and the `length.*`, `analysis.length-*`, `kicad.length.*` and `kicad.meander.*` codes). Proof: `uv run pytest tests/consistency tests/unit/test_repo_layout.py tests/residue`.
  - Result, 2026-10-08: written for everything that exists: `docs/analyses.md` ("Length"), `docs/dsl.md` and `docs/copper.md` ("Meanders"), `docs/cli-contract.md` (the kind, its options and the `analysis.length-*`, `kicad.length.*` and `kicad.meander.*` codes), `docs/geometry.md` ("Path lengths"). Open: `length.rules` and the three `length.*` codes, with task 6.1. `uv run pytest tests/consistency tests/unit/test_repo_layout.py tests/residue` 344 passed, 19 skipped, exit 0.
  - Result, 2026-10-08 (on `v04` at `1adc0ef`): `docs/cli-contract.md` has the stage in the stage table, the paragraph "Length rules", the three `length.*` codes and the pair rows of `result.pairs`; `docs/analyses.md` has "Pair skew", "Length rules in check" and two oracle rows. `uv run pytest tests/consistency tests/unit/test_repo_layout.py tests/residue` 398 passed, 26 skipped, exit 0.
- [x] 9.2 If c0080 is on `dev`: add one tested line for `fenolite analyze --kinds length` and one for `Design.meander` to the guide page that c0080 names, with its recipe test. Otherwise write "c0080 not on dev" under this task. Proof: the guide test that c0080 names, run with `-k length` (on the day: `uv run pytest tests/unit/agent -q -k length`), or the note under this task.
  - Result, 2026-10-08: c0080 not on dev (0 of 15 tasks on this base), so no guide line is added.
  - 2026-10-08, integration onto `v04`: c0080 is on the branch now, so the two lines are added: `fenolite analyze … --kinds length --json` in the command block of the page `rules` ("Measuring a board"), and `design.meander("vin_len", …)` in the tested script of the page `routing`, which the guide tests build, check and fill. `MeanderIntent` and `meanders` stand in `guide.DSL_NOT_TAUGHT` (a record a call returns; a call of the build). No test of `tests/unit/agent` has `length` in its name, so the proof as written selects nothing; run instead: `uv run pytest tests/unit/agent -q` gives 82 passed (the blocks of `routing` and `rules` among them).

## 10. Closing

- [x] 10.1 Run the residue and the fast suite. Proof: `uv run pytest tests/residue tests/corpus/test_manifest.py` (after `git add -A`) and `uv run python tools/residue/scan.py` exit 0; `make check-fast` passes; `openspec validate c0106-length-measure-tune --strict --no-interactive` and `openspec validate --all --strict --no-interactive` pass. The full `make check` and `gh pr checks` (`unit`, `kicad-9`, `kicad-10`) are the coordinator's, once, on the rebased branch at merge; this change's agent does not start a full suite.
  - Result, 2026-10-08: open: `make check-fast PYTEST_WORKERS=3` was started and had not finished when this change was committed (its ruff steps passed; the log is with the session). Passed before it: `uv run pytest tests/corpus/test_manifest.py tests/residue` 85 passed, `uv run python tools/residue/scan.py` 0 hits, `openspec validate --all --strict --no-interactive` 101 passed, each exit 0.
  - 2026-10-08 (on `v04` at `1adc0ef`, the length stage): `uv run pytest tests/residue tests/corpus/test_manifest.py` (after staging every file) 80 passed, 5 skipped, exit 0; `uv run python tools/residue/scan.py` 0 hits, exit 0; the four `tools/gen_*.py --check` exit 0. `make check-fast PYTEST_WORKERS=2`: ruff, format, pyright (0 errors) and residue passed; `test-fast` gave 12 692 passed, 30 skipped and 1 failed (`test_manifest_cmd.py::test_states_from_a_check`, a list of the default stages without `length.rules`), exit 2; the list was corrected (and the two of `tests/kicad/check`) and the file gives 18 passed, exit 0; the suite was not run a second time (one full run per agent). `openspec validate --all --strict --no-interactive` (CLI 1.14.1): the six known `ERROR`s of c0084, c0085 (2), c0086, c0108 and c0128, none in c0106, whose `--strict` run gives the CLI's "very long" warnings only. Still open: a green `make check-fast` on the rebased branch and the `openspec validate` proofs as written.
  - 2026-10-08, on `v04` at `09ee580` with the edits of this pass (branch `v04-close-b`): `make check-fast PYTEST_WORKERS=3`: ruff check, ruff format, the guide check, pyright and the residue scan pass, 12761 passed, 30 skipped, exit 0 (no rerun needed: the two timing tests passed). `uv run --isolated --python 3.11 --extra dev pytest tests/unit -q -n 3 -p no:cacheprovider`: 12378 passed, 26 skipped, exit 0 (three workers, as the coordinator asked, for the four of the proof). After `git add -A`: `uv run pytest tests/residue tests/corpus/test_manifest.py` 82 passed, 3 skipped; `uv run python tools/residue/scan.py` 0 hits; `tools/gen_schemas.py --check` and `tools/gen_evidence_matrix.py --check` exit 0. `openspec validate --all --strict --no-interactive`: five ERRORs, all of other changes (c0084, c0085 twice, c0086, c0128; the one of c0108 is gone) and the long-requirement warnings that every change gives, which the coordinator accepts for this release; this change's own `--strict` run gives no ERROR. The full `make check` and the CI run are the coordinator's.
- [x] 10.2 Run the unit suite on Python 3.11 before handing over. Proof: `uv run --isolated --python 3.11 --extra dev pytest tests/unit -q -n 4 -p no:cacheprovider` exits 0.
  - Result, 2026-10-08: open: the whole unit suite was not run on 3.11 in this session (one full suite at a time on the shared machine). The test files this change added or touched pass on 3.11: `uv run --isolated --python 3.11 --extra dev pytest <10 files> -q` 141 passed, exit 0.
  - 2026-10-08, on `v04` at `09ee580` with the edits of this pass (branch `v04-close-b`): `make check-fast PYTEST_WORKERS=3`: ruff check, ruff format, the guide check, pyright and the residue scan pass, 12761 passed, 30 skipped, exit 0 (no rerun needed: the two timing tests passed). `uv run --isolated --python 3.11 --extra dev pytest tests/unit -q -n 3 -p no:cacheprovider`: 12378 passed, 26 skipped, exit 0 (three workers, as the coordinator asked, for the four of the proof). After `git add -A`: `uv run pytest tests/residue tests/corpus/test_manifest.py` 82 passed, 3 skipped; `uv run python tools/residue/scan.py` 0 hits; `tools/gen_schemas.py --check` and `tools/gen_evidence_matrix.py --check` exit 0. `openspec validate --all --strict --no-interactive`: five ERRORs, all of other changes (c0084, c0085 twice, c0086, c0128; the one of c0108 is gone) and the long-requirement warnings that every change gives, which the coordinator accepts for this release; this change's own `--strict` run gives no ERROR. The full `make check` and the CI run are the coordinator's.
- [x] 10.3 Update the evidence labels: `H-K-NETLEN-TOTAL`, `H-K-NETLEN-VIA10`, `H-K-NETLEN-VIA9`, `H-K-NETLEN-STACKUP`, `H-K-NETLEN-RULES` and `H-K-NETLEN-MEANDER` become `KICAD-VERIFIED` with their scope (the stack-up row for the layer counts measured), or record what was refuted and the fallback taken; `H-G-NETLEN-PATH` stays `INFERRED`. Proof: `uv run pytest tests/unit/test_provenance.py tests/unit/test_hypotheses_register.py tests/kicad/test_probe_results.py`.
  - Open, 2026-10-08 (integration): the 9.0.9 outcomes are recorded now (tasks 1.2 and 8.4), so the labels can be raised; the rows, the `EVIDENCE` values of `lengths.py` and `meander.py` and the fact rows of `docs/formats/kicad/length.md` were not edited in the integration.
  - Result, 2026-10-08: `H-K-NETLEN-VIA10` is `KICAD-VERIFIED (10.0.x)`: its criterion names 10.0.6 only and is met. The five other `H-K-` rows stay `INFERRED` with what 10.0.6 showed, because their criteria name both majors and 9.0.9 is not run (`H-K-NETLEN-RULES` also waits for the stage). `H-G-NETLEN-PATH` stays `INFERRED`. `uv run pytest tests/unit/test_provenance.py tests/unit/test_hypotheses_register.py tests/unit/test_format_facts.py` 66 passed, exit 0.
  - 2026-10-08: from CI run 37772583226 on `04ef42a` (all jobs green): `H-K-NETLEN-TOTAL`, `H-K-NETLEN-RULES` and `H-K-NETLEN-MEANDER` are `KICAD-VERIFIED (9.0.x, 10.0.x)`, `H-K-NETLEN-STACKUP` `KICAD-VERIFIED (9.0.x, 10.0.x)` with the scope of 2, 4, 6 and 8 copper layers at 1.6 mm, `H-K-NETLEN-VIA9` `KICAD-VERIFIED (9.0.x)` and `H-K-NETLEN-VIA10` stays `KICAD-VERIFIED (10.0.x)`; `H-G-NETLEN-PATH` stays `INFERRED`. The fact rows of `docs/formats/kicad/length.md` follow (ten rows raised). `lengths.EVIDENCE`, `meander.EVIDENCE` and `checks.length.EVIDENCE` stay `INFERRED`, as their docstrings say: they cover benches, not every board. `uv run pytest tests/unit/test_provenance.py tests/unit/test_hypotheses_register.py tests/kicad/test_probe_results.py`: 44 passed, 1 skipped (no `kicad-cli` here; the probe test passed in both CI jobs).
- [x] 10.4 Add to `CHANGELOG.md` under Unreleased: "Net lengths as KiCad 9 and 10 count them (tracks, arcs, via heights from the stack-up, die lengths), pin-to-pin lengths and pair skew in `fenolite analyze --kinds length`, a `length.rules` stage in `check` for length and skew rules, and `Design.meander` to bring a script track to a target length". The entry also says that the stage runs on KiCad input only and that the routed lengths of `equivalent --level 5` come from the same kernel functions. Update `docs/roadmap.md`: the row of c0106 (the table of "v0.4: proposals on other branches", or the milestone table if the section was folded into it by then) and the v0.6 line "matched-length and skew analysis" it takes, in the Phase 5 table and in the table of proposed cuts. Proof: `git diff --stat CHANGELOG.md docs/roadmap.md` lists both files; `grep -n "matched-length" docs/roadmap.md` shows both lines changed.
  - Result, 2026-10-08: `CHANGELOG.md` has its entry at the end of Unreleased (it says what is not in this part). `docs/roadmap.md` is not edited in this session: the coordinator of the v0.4 wave edits it.
  - 2026-10-08 (on `v04` at `1adc0ef`): the entry now names the pair skew and the stage `length.rules` with its three codes, KiCad input only. `docs/roadmap.md` is still the coordinator's, so the task stays open.
  - 2026-10-08: `docs/roadmap.md`: the row of c0106 says it is built on `v04` and takes matched-length and skew analysis from v0.6; the v0.6 line of the Phase 5 table and the row of the table of proposed cuts say the analysis moved to v0.4 with c0106; a paragraph "c0106 on `v04`". `CHANGELOG.md` gains a line under `### Changed` for the raised rows. `git diff --stat CHANGELOG.md docs/roadmap.md` lists both; `grep -n "matched-length" docs/roadmap.md` shows both lines changed.
