lgili/Fenolite/openspec/changes/c0091-altium-verification-kit/tasks.md

## 0. Entry check

- [x] 0.1 Read `openspec list` and the living `altium-verification`, `verification-evidence` and `cli-contract` specs. Write under this task, with the date: which of the changes this one depends on are archived (a missing one stops the tasks that name it, and say which); whether another change modified a requirement that this change supersedes ("Spec deltas and archive order" in the design lists them): then write the MODIFIED text from the living one before any code; and which of c0084 to c0090 are archived: the steps of a group whose change is not archived are written and marked `pending`, and the first real run waits for all of them. Proof: `openspec validate c0091-altium-verification-kit --strict --no-interactive` passes.

  Entry check of 2026-10-06 (branch `c0091-altium-verification-kit`, on the commits of c0084 to c0087, c0089 and c0122):
  - **Archived:** none of the changes this one depends on. `openspec list` shows c0084 (11/13 tasks), c0085 (13/16), c0086 (13/16), c0087 (10/12), c0089 (9/10) and c0122 (10/11) as active with their code on this branch, and c0088 (0/12) and c0090 (0/13) as not started.
  - **What that stops.** Nothing of tasks 1.1 to 5.2: the kit's code needs the writers of c0084 to c0087 and levels 1 to 5 of `equivalent` (c0089), which are on the branch. Task 5.3 (the first real run) waits until c0084 to c0090 are archived.
  - **Pending.** c0088 is missing: `kit verify` has no `copper.clearance` stage for an Altium document, so that check is declared, documented and skipped with the reason `pending: c0088`; it is never passed silently. The import reads no clearance for a polygon yet (`docs/evidence/equivalence-triangle.md`), which c0088 also changes. c0090 is missing: no step of the kit writes back an imported board, and the group K9 step that updates a schematic from the libraries and the re-saved board after the change order (group K3) are compared through the import as it stands; what c0090 adds to that comparison is `pending: c0090`. The steps of the groups K4 (rule check counts against Fenolite's own judgement) and K6 (copper check on the repoured board) carry `pending` checks for c0088; the steps themselves are written and are run.
  - **Superseded requirement.** `verification-evidence`, "Reserved id families": no active change modifies it (only the archived c0014 and c0016 did). Its living text still requires `H-A-WRITE-*`, `H-A-PH-*` and `H-G-DSN-*` in the table, while the live table dropped `H-G-DSN-*` when c0023 registered its rows. The MODIFIED text was written from the living one into this change's delta before any code: the two Altium families leave the table when task 2.2 names their kit steps.
  - **`cli-contract`:** no active change adds a requirement named "Kit command"; c0092 is not started.
  - **Layering, found on 2026-10-06.** `package-layering` lets `verify` import `model`, `geometry` and `backends` only. Building a sample needs `dsl`, `catalog` and `lens`, and comparing a re-saved document needs `checks`. `fenolite.verify.kit` therefore takes the sample builder and the document judge as arguments, and `fenolite/cli/_kit.py` holds the two that the command uses. `build_kit` and `verify_results` have one keyword more than the design lists; the layering table is not changed.

## 1. Registers and page

- [x] 1.1 Add the five rows to `docs/hypotheses.md`; write the skeleton of `docs/altium-kit.md` (what the kit is, what a run proves, what a saved file may contain) and `docs/evidence/altium-kit/README.md`. Proof: `uv run pytest tests/unit/test_hypotheses_register.py tests/unit/test_provenance.py tests/unit/test_repo_layout.py`.

## 2. Kit build

- [x] 2.1 Author the five sample scripts under `examples/kit/` and write `manifest.py` (scenarios of "Verification kit contents"). Proof: `uv run pytest tests/unit/verify/kit/test_manifest.py tests/residue`; `uv run pyright src`.

  Done on 2026-10-06. The five scripts use Fenolite's own catalog for every symbol and footprint, so a build reads no library and no table. A script may bind `KIT` (sheets, forms, copper, planes, drawing sheet) and `kit_model(model)` for what the DSL cannot declare: the bus of `tree`, the six layers and board items of `board6`, the copper of `routed`. `build_kit(out, *, seed, timestamp, sources)` takes the built samples as an argument (entry check, "Layering"); `fenolite.cli._kit.kit_sources()` builds them. The kit holds no `.fenolite/` folder. No JSON Schema file is generated for `kit.json`: `schemas/` is generated from dataclasses and the manifest is a mapping.
- [x] 2.2 Write `steps.py` with the groups K1 to K9 and the generated `STEPS.md` (scenario "Steps and register agree"); set the settling test of `H-A-WRITE-*` and `H-A-PH-*` to their steps. Proof: `uv run pytest tests/unit/verify/kit/test_steps.py tests/unit/test_hypotheses_register.py`.

  Done on 2026-10-06: 32 steps in nine groups. The test cells of the eight rows `H-A-WRITE-*` and `H-A-PH-*` name their steps, and the two families left the reserved table. Their statements still speak of the author's earlier writer while the kit's samples are Fenolite's, and "Author-report rows" still allows those rows only an author-report level or `INFERRED`: a kit run cannot label them until c0092 decides that. `H-A-SCHX-BUS` is named by no step: no step reads the bus in Altium.
- [x] 2.3 Register the pages of Altium's public scripting documentation that the script relies on (one source row per page, read for facts), list every call with its source in `SCRIPT_CALLS` and in `docs/altium-kit.md`, then write `script.py` and mark the steps it performs `scripted` (scenarios of "Kit script"). A call without a public page is not used and its step stays manual; say which under this task. Proof: `uv run pytest tests/unit/verify/kit/test_script.py tests/unit/verify/kit/test_steps.py tests/unit/test_provenance.py`.

  Done on 2026-10-06. Pages registered before the script was written, all of Altium's public documentation, read for names and signatures through a text rendering of each page, nothing transcribed: S-0500 (writing scripts: DelphiScript is the default, File » Run Script), S-0501 (DelphiScript functions: the file and string routines, Try-Except), S-0502 (keywords), S-0503 (Workspace Manager API: `GetWorkspace`, `DM_FocusedProject`, `DM_MessagesManager`, the messages manager and its items), S-0504 (`IProject`: `DM_Compile`, `DM_ProjectFullPath`, `DM_ProjectFileName`), and two read and not used: S-0505 (`IServerDocument`, `IClient`) and S-0506 (server processes). Two addresses gave 404 and are not sources (`…/altium-dxp-developer/iworkspace-interface`, `…/imessagesmanager-interface`); the pages of the commands for the rule check and for report generation now lead to user-guide pages that name no process.
  **Scripted:** the five compile steps K2.1 to K2.5 (compile the project in focus, write its messages, log the step). **Manual, and why** (`script.NOT_SCRIPTED`, shown in `docs/altium-kit.md`): opening a project (two forms of `DM_OpenProject` in the documentation, and a person must see a repair prompt); every save under a result name (`DoSafeChangeFileNameAndSave` is described only as a test, `DoFileSave` as a save in place with format names of older versions); the rule check report, Repour All and the output job's containers (no process documented; the rule check opens a dialog); the change order and Update From Libraries (dialogs). The design asked for more; a call without a public page is not used.
  **Inferred, not documented:** that a script file opened without a script project is offered by File » Run Script; that `Messages` counts from 0; that `DM_ProjectFullPath` ends in the file name; that `Append` on a missing file raises an error that Try-Except catches. The script was never run: `H-A-KIT-SCRIPT` is `INFERRED`.

## 3. Kit verify

- [x] 3.1 Write `results.py`: manifest check, form schema, re-saved documents, the kit profile and the privacy scan (scenarios of "Kit result verification"), with the simulated run. Proof: `uv run pytest tests/unit/verify/kit/test_results.py`.

  Done on 2026-10-06, with three things to know. (1) The reference of a re-saved document is Fenolite's reading of the kit's own document, not the build's model: that model holds no placed footprint, and its unconnected pins differ from an import's. (2) `verify_results(folder, *, judge)` takes the document judge as an argument (entry check, "Layering"); `fenolite.cli._kit.judge_document` is the product's. (3) Fenolite's writers write every polygon unpoured, so no file of theirs can stand in for a repoured board: in the simulated run the check `poured` of step K6.1 runs on the import of the kit's own board with its zones filled in the model (`_simulate.simulated_judge`); with the product's judge that step fails on the stand-in, which a test asserts. That the import gives fills for a polygon that Altium poured is c0122's claim and is first exercised by a real run. `copper.clearance` on a re-saved board is pending on c0088 and keeps `H-A-KIT-DRC` and `H-A-KIT-REPOUR` at `pending`. The kit profile holds one exclusion (a part without a designator).

## 4. Record and label

- [x] 4.1 Write `record.py` and `stale_rows` (scenarios of "Kit run record"). Proof: `uv run pytest tests/unit/verify/kit/test_record.py`.
- [x] 4.2 Add the kit label rule to the register test (scenarios of "Kit label rows"). Proof: `uv run pytest tests/unit/test_hypotheses_register.py tests/unit/verify`.

## 5. Command and documentation

- [x] 5.1 Write `cmd_kit.py` (scenarios of "Kit command"). Proof: `uv run pytest tests/unit/cli/test_kit_cmd.py tests/consistency tests/unit/cli/test_hermetic_examples.py`.
- [x] 5.2 Finish `docs/altium-kit.md` with the steps, the time each group takes, and how to publish the archive; link it from `README.md` and `docs/evidence/README.md`. Proof: `uv run pytest tests/consistency tests/unit/test_repo_layout.py`.
- [ ] 5.3 Hand the kit to the maintainer for a first run on his machine (the design, "Decisions", lists the groups). The run is recorded by c0092's task, or here when c0084 to c0090 are archived: `fenolite kit verify`, `fenolite kit record`, commit the record. Proof: `fenolite kit status --json` lists the run and no stale row.

  **Not done: left to the maintainer** (written on 2026-10-06; there is no Altium on the machine of this change, and the run waits for c0084 to c0090). What to do, on the Windows machine with Altium Designer and a licence that may be used for Fenolite:
  1. In a checkout of the branch that holds c0084 to c0091: `uv run fenolite kit build --out <folder outside the repository>\kit --confirm --json`. Note `result.kit_sha256`. The kit lands in that folder: `STEPS.md`, `kit_script.pas`, `flat\`, `tree\`, `routed\`, `board6\`, `libs\`, `templates\` and `results\`.
  1a. Before anything else in Altium: open `kit_script.pas` in the script editor and compile it. Its call signatures were read from a rendering of the documentation pages on 2026-10-06 and it has never run. If a line is refused, report the first error line and do group K2 by hand.
  2. Open `STEPS.md` and fill `altium_version` (`AD <major>.<minor>`), `os_family` (`Windows`), `date` and `"synthetic": false` in `results\form.json`.
  3. Do the groups in order. Estimates made without a run, not measurements: K1 10 min, K2 8 min, K3 8 min, K4 8 min, K5 10 min, K6 4 min, K7 6 min, K8 5 min, K9 5 min; about 65 minutes with the form. For group K2 either follow the manual instruction, or, per sample project: focus the project, open `kit_script.pas`, File » Run Script, `FenoliteKitRun`; if `results\script.log` holds an error line or stays empty, do that step by hand and say so in the report (it settles `H-A-KIT-SCRIPT` either way).
  4. `uv run fenolite kit verify <folder>\kit --json`. Read `result.privacy` first, then the failed steps. A failed step is a finding to report, not something to repair in the files.
  5. `uv run fenolite kit record <folder>\kit --out <repository> --dry-run --json`, then `--confirm`. It writes `<folder>\results.zip` and `docs/evidence/altium-kit/<run id>.json`, and prints `result.rows`.
  6. Publish `results.zip` as the release asset `altium-kit-<run id>.zip`; commit the record; set the rows of `result.rows` that are to change (label and result text as printed). `H-A-WRITE-*` and `H-A-PH-*` stay as they are until c0092 changes "Author-report rows". Proof: `uv run fenolite kit status --json` lists the run and no stale row, and `uv run pytest tests/unit/test_hypotheses_register.py` passes.
  (Updated 2026-10-06: c0088 is on the branch and the copper check of K4.2 and K6.1 is wired to its stage; nothing is pending.) Expect the first run to show what Altium normalises on a save: each such difference fails its step until the kit profile names it with its cause.

## 6. Closing

- [ ] 6.1 Run the residue and full test suites. Proof: `uv run pytest tests/residue tests/corpus/test_manifest.py` and `uv run python tools/residue/scan.py` exit 0; `make check` passes; `openspec validate c0091-altium-verification-kit --strict --no-interactive` passes; `gh pr checks` shows `unit` passing.
- [x] 6.2 Update the evidence: every row of this change holds its measured level and result in `docs/hypotheses.md`, the cells of `backends/altium/claims.py` say what is written and at which level, and `uv run python tools/gen_evidence_matrix.py` regenerates `docs/evidence/matrix.md`. Proof: `uv run pytest tests/unit/test_provenance.py tests/unit/test_hypotheses_register.py tests/unit/backends/test_evidence_declared.py`.
- [x] 6.3 Add to `CHANGELOG.md` under Unreleased: "`fenolite kit` builds the Altium verification kit, checks the files a run leaves and records the run: the base of the label `ALTIUM-VERIFIED(kit)`". Update `docs/roadmap.md`. Proof: `git diff --stat CHANGELOG.md docs/roadmap.md` lists both files.
