lgili/Fenolite/openspec/changes/c0100-board-layer-count/tasks.md

## 0. Entry check

- [x] 0.1 Read the living `design-dsl`, `kicad-file-backend`, `layout-lens`, `altium-build`, `altium-pcb-writer` and `kicad-oracle` specs and `openspec list`. Write under this task, with the date: whether release 0.3.0 is out and c0085 archived (the Altium requirement of this change cites its "Layer stacks of any even count"); whether c0096 is on `dev` (then regenerate the MODIFIED "Board and placements in the DSL" from the living text, which then holds `anchor=`, and re-apply this change's edits); whether an archive changed one of the other four requirements this change modifies ("Design structure and names", "Planes in a build", "Zones in the DSL", "Created board header"; then regenerate that delta the same way); and whether each guard of the design's table (`INNER_LAYERS`, `INNER_ROWS` and the others) is still where the table says. Proof: `openspec validate c0100-board-layer-count --strict --no-interactive` passes after any regeneration.
  - 2026-10-07, base `f36e08d9` (dev at `c69f8c6b` plus the proposals of v0.4): release 0.3.0 is not out (`fenolite.__version__` is 0.2.1) and c0085 is not archived (13/16 tasks, implemented on this base: `lens.altium_copper.board_layers`, `pcbrecords.MAX_COPPER = 32`), so its "Layer stacks of any even count" is still a delta and the Altium requirement here cites it as such. c0096 is not on this base (`anchor=` occurs nowhere in the living `design-dsl`); nothing to regenerate, c0096 regenerates on this change's text. No archive changed the five MODIFIED requirements: a diff of each delta against the living text shows this change's edits only. Guards: all where the table says, except that `cli/cmd_build.py` holds the two `# type: ignore[arg-type]` at lines 726 and 974 and `lens.altium_copper.STACK_HINT` at line 81. `openspec validate c0100-board-layer-count --strict --no-interactive`: valid, exit 0.

## 1. Probe and register

- [x] 1.1 Add the rows `H-K-PCB-LAYERS` and `H-K-BUILD-LAYERS` to `docs/hypotheses.md` (backend `kicad`, level `INFERRED`, the tests and criteria of `design.md`, result `pending` with the measurements of 2026-10-05 as the first record). Proof: `uv run pytest tests/unit/test_hypotheses_register.py tests/unit/test_provenance.py`; `grep -cE '^\| (H-K-PCB-LAYERS|H-K-BUILD-LAYERS) ' docs/hypotheses.md` prints `2`.
  - 2026-10-07: both rows are in `docs/hypotheses.md` (the `grep -cE` prints `2`); they start at the level the 10.0.6 probes of this change settle, with the measurements of 2026-10-05 as the first record (see 7.2). Not ticked: `uv run pytest tests/unit/test_hypotheses_register.py tests/unit/test_provenance.py` gives 43 passed, 1 failed, exit 1. The failure is `test_cited_ids_registered`: `openspec/changes/c0140-part-height-rules/design.md` cites an id of c0099 that no row registers yet, which no row registers. It fails the same way on a clean checkout of `f36e08d9` (35 passed, 1 failed) and is c0140's to register.
  - 2026-10-08, base `04ef42a`: ticked. `uv run pytest tests/unit/test_hypotheses_register.py tests/unit/test_provenance.py` passes (c0140's id is registered on this base; with `tests/unit/verify/test_cited_ids.py`: 50 passed, exit 0), and the `grep -cE` prints `2`.
- [x] 1.2 Write `tests/kicad/board/_layertables.py` (the row rule of Decision 2 for any n, and the table of 3) and `tests/kicad/board/test_layer_tables.py` with the probes `pcb-layers-<n>-t<M>`, `pcb-layers-gerbers-<n>-t<M>`, `pcb-layers-resave-<n>-t<M>` and `pcb-layers-odd-t<M>`, registered in `tests/kicad/_probes.py`; until task 2.1 the test writes the tables of 6 and 8 with `_layertables.py`. Record the outcomes, and write the table facts to `docs/formats/kicad/board.md` with S-0020, S-0022, S-0029, S-0037 and S-0058. If a probe of 6 or 8 records another outcome than the design's measurements, stop and write what KiCad showed into the register row. Proof: `uv run pytest tests/kicad/board/test_layer_tables.py -rA` on the local KiCad 10.0.6 and inside the pinned 9.0.9 image; `FENOLITE_PROBES_WRITE=1` updates both probe files; `uv run pytest tests/kicad/test_probe_results.py tests/unit/test_format_facts.py`.
  - 2026-10-07, `kicad-cli` 10.0.6 (macOS): `tests/kicad/board/test_layer_tables.py -rA` 23 passed, exit 0. Both texts of n = 2, 4, 6 and 8 record `load`, `equal` (Gerbers, one per copper layer) and `equal` (re-save); both texts of the table of 3 record `reject`: the design's measurements. The 18 `pcb-layers-*` rows of major 10 are in `docs/evidence/kicad/probes/10.0.6.json`, and `tests/kicad/test_probe_results.py` passes on 10.0.6 (1 passed, 595 probes compared). The table facts are in `docs/formats/kicad/board.md` (S-0020, S-0022, S-0029, S-0037, S-0058); `tests/unit/test_format_facts.py` passes. Not ticked: the run inside the pinned 9.0.9 image was not made (no docker in this session), so `9.0.9.json` has no `pcb-layers-*` row and the 9.0.9 fact row is `INFERRED`. `tests/kicad/test_probe_results.py` fails on 9.0.9 until that file is written with `FENOLITE_PROBES_WRITE=1` (9 rows: `pcb-layers-<n>-t9`, `pcb-layers-gerbers-<n>-t9`, `pcb-layers-odd-t9`).
  - 2026-10-08: ticked by the local run of 2026-10-08 in the pinned 9.0.9 image (`kicad/kicad:9.0.9@sha256:e638b79b…`, linux/amd64, branch `v04-k9-probes`; whole `tests/kicad` without the corpus: 777 passed, 4 failed, 784 skipped, 1 xfailed; `tests/kicad/test_probe_results.py` passed on the 536 probes of major 9): `tests/kicad/board/test_layer_tables.py` 10 passed, 13 skipped (the target-10 texts and the re-save, which 9.0.9 cannot run); the 9 rows `pcb-layers-<n>-t9` = `load`, `pcb-layers-gerbers-<n>-t9` = `equal` and `pcb-layers-odd-t9` = `reject` are in `9.0.9.json`; `tests/unit/test_format_facts.py` passes.

## 2. Layer table and build

- [x] 2.1 In `src/fenolite/backends/kicad/layers.py` add `CREATED_COPPER_COUNTS`, `inner_rows(copper)` and `created_count(names)`, make `created_layers(copper: int)` take every count, and remove `INNER_ROWS`. Write `tests/unit/backends/kicad/test_layers_created.py` (scenarios "Four copper layers", "Six and eight copper layers" and "Counts outside the table" of "Created board header"), change the assertion of `tests/unit/backends/kicad/test_pcb_write.py` that `created_layers(6)` raises to 3 and 10, and make `test_layer_tables.py -k same_table` compare `_layertables.py` with `created_layers`. Proof: `uv run pytest tests/unit/backends/kicad/test_layers_created.py tests/unit/backends/kicad/test_pcb_write.py`; `uv run pytest tests/kicad/board/test_layer_tables.py -k same_table` without `kicad-cli`; `uv run pyright src`.
  - 2026-10-07: `test_layers_created.py` and `test_pcb_write.py` 40 passed, exit 0; `tests/kicad/board/test_layer_tables.py -k same_table` 4 passed; `uv run pyright src` 0 errors.
- [x] 2.2 Type `copper` as `int` in `lens/build.py::build_design`, `tests/_boards.py::created_board`, `tests/_placed.py` and `tests/_coppercheck.py`, and remove the two `# type: ignore[arg-type]` of `cli/cmd_build.py`. Proof: `uv run pyright src`; `uv run pytest tests/unit/lens tests/unit/cli/test_build_command.py tests/unit/checks`.
  - 2026-10-07: `uv run pyright src` 0 errors; `tests/unit/lens tests/unit/cli/test_build_command.py tests/unit/checks` 1352 passed, 1 skipped, exit 0.

## 3. DSL

- [x] 3.1 In `src/fenolite/dsl/design.py` add `COPPER_COUNTS`, `inner_layers(copper)` and `Design.copper_layers`, check `board(copper=…)` against them (`bool` and `float` refused), validate `planes=` and `zone(layers=…)` against the count, and remove `INNER_LAYERS`. Write `tests/unit/dsl/test_board_layers.py` (the scenarios of "Design structure and names", "Board and placements in the DSL" and "Zones in the DSL", and `COPPER_COUNTS == layers.CREATED_COPPER_COUNTS`). In `tests/unit/dsl/test_structure.py` only the expected message of `planes` with `copper=2` changes ("planes need copper=4" today); its other tests and those of `test_zones.py` pass unchanged. Proof: `uv run pytest tests/unit/dsl tests/unit/test_import_graph.py`; `uv run pyright src`.
  - 2026-10-07: `tests/unit/dsl tests/unit/test_import_graph.py` 449 passed, exit 0; `uv run pyright src` 0 errors. The message of `planes` with `copper=2` now reads "planes need copper=4, 6 or 8".
- [x] 3.2 Change the hint of `lens.build.plane_issues` to name `design.zone(<net>, layers=("<layer>",))` and no editor step, change the `fix` text of `build.plane-not-lowered` in `src/fenolite/cli/data/explain.toml` to name the same call and no editor step, and extend the hint assertion of `tests/unit/lens/test_build_issues.py::test_plane_issues` (today it checks "zone on In1.Cu"). Add the scenarios of "Planes in a build" and "Copper layer counts in a build" (six-layer build for targets 9 and 10, script copper on `In6.Cu` of eight, `In7.Cu` refused) to `tests/unit/cli/test_build_command.py`. Proof: `uv run pytest tests/unit/cli/test_build_command.py tests/unit/cli/test_explain_cmd.py tests/unit/lens/test_build_copper.py tests/unit/lens/test_build_issues.py`.
  - 2026-10-07: `test_build_command.py`, `test_explain_cmd.py`, `test_build_copper.py` and `test_build_issues.py` 50 passed, exit 0. The six-layer board is read back for targets 9 and 10; the built model is checked in `test_six_layer_pads_in_the_built_model`.

## 4. Rebuild and Altium

- [x] 4.1 In `lens/preserve.py::merge_layout`, give `layout.copper-mismatch` the message and the hint of "Layer count across rebuilds", using `layers.created_count`, and change its `fix` text in `src/fenolite/cli/data/explain.toml` to name `copper=<the board's count>` and `--discard-layout`. Add its four scenarios to `tests/unit/cli/test_build_preserve_command.py`; the existing mismatch test passes with the new hint. Proof: `uv run pytest tests/unit/cli/test_build_preserve_command.py tests/unit/cli/test_explain_cmd.py tests/unit/lens/test_build_preserve.py tests/unit/lens/test_preserve_issues.py`.
  - 2026-10-07: `test_build_preserve_command.py` (the four scenarios and a two-layer board under a four-layer script), `test_explain_cmd.py`, `test_build_preserve.py` and `test_preserve_issues.py` 51 passed, exit 0. Message: "the board has 6 copper layers (F.Cu, …) and the script declares 4 (…)".
- [x] 4.2 Reword `lens.altium_copper.STACK_HINT` as "Script layer counts in an Altium build" states, and add its three scenarios to `tests/unit/cli/test_build_altium.py` (six layers with a plane and a zone, through the CLI) and `tests/unit/lens/test_altium_issues.py` (eight layers read back; the hint). No other source change is expected (design Decision 8): if the six- or eight-layer build gives an error or an `altium.not-lowered` with `where` `stackup`, stop, write what the build gave under this task, and correct the requirement from it before going on. Proof: `uv run pytest tests/unit/cli/test_build_altium.py tests/unit/lens/test_altium_issues.py tests/unit/lens/test_altium_pcb_complete.py`.
  - 2026-10-07: `test_build_altium.py`, `test_altium_issues.py` and `test_altium_pcb_complete.py` 140 passed, exit 0. No source change beyond `STACK_HINT` was needed: the six-layer build with a plane and a zone plans its PCB document, and the eight-layer document reads back with its eight copper layers; no `altium.not-lowered` with `where` `stackup`.

## 5. Build oracle

- [x] 5.1 Write `tests/kicad/build/_layercases.py` (the variant of design Decision 10 for n = 4, 6 and 8) and the 10.0.6 half of `tests/kicad/build/test_layer_builds.py` with the probes `build-layers-<n>-t<M>` and `build-layers-gerbers-<n>-t<M>` registered in `tests/kicad/_probes.py`; with `FENOLITE_PROBES_WRITE=1` it writes the two fixtures under `tests/data/kicad/layers/`, declared in `tests/data/MANIFEST.toml`. If a probe records another outcome than the design's measurements, stop and correct the design from what KiCad showed. Proof: `uv run pytest tests/kicad/build/test_layer_builds.py -rA` on the local KiCad 10.0.6; `FENOLITE_PROBES_WRITE=1` updates `10.0.6.json` and the two fixtures; `uv run pytest tests/kicad/test_probe_results.py tests/residue`.
  - 2026-10-07, `kicad-cli` 10.0.6 (macOS): `tests/kicad/build/test_layer_builds.py -rA` 8 passed, 2 skipped (the 9.0 half), exit 0, with and without `FENOLITE_PROBES_WRITE=1` (the fill is the same on both runs). n = 4, 6, 8 and both targets: every zone filled once, `drc.kicad` 0 violations, 0 unconnected, canary fired, `copper.clearance` 0 shorts and 0 clearance findings, `Copper,L1,Top` to `Copper,L<n>,Bot`, job file `LayerNumber` n. The two fixtures are written and declared; the 12 `build-layers-*` rows are in `10.0.6.json`; `tests/kicad/test_probe_results.py` 1 passed; `tests/residue` passes. One correction of the requirement's wording from what the run showed: after `fill`, the second build leaves every project file outside `.fenolite/` with its bytes; the views `.fenolite/board.json` and `.fenolite/build.json` change once, because they describe the board with its fills. The test compares the files outside `.fenolite/`, as `tests/kicad/acceptance` does.
- [x] 5.2 Write the 9.0.9 half of `test_layer_builds.py` on the two fixtures, and `tests/unit/test_layer_fixtures.py` (scenario "Fixtures follow the build"). Proof: `uv run pytest tests/kicad/build/test_layer_builds.py -rA` inside the pinned 9.0.9 image, with `FENOLITE_PROBES_WRITE=1` updating `9.0.9.json`; `uv run pytest tests/unit/test_layer_fixtures.py tests/kicad/test_probe_results.py`.
  - 2026-10-07: the 9.0.9 half is written (`test_filled_fixture_on_kicad_9`, `_layercases.fixture_run`) and its code path was run by hand on 10.0.6 on both fixtures (0 violations, 0 unconnected, 6 and 8 copper Gerbers). `tests/unit/test_layer_fixtures.py` 3 passed, exit 0. Not ticked: the run inside the pinned 9.0.9 image was not made (no docker in this session), so `9.0.9.json` has no `build-layers-*` row (4 rows: `build-layers-<n>-t9` and `build-layers-gerbers-<n>-t9` for n = 6, 8).
  - 2026-10-08: ticked by the local run of 2026-10-08 in the pinned 9.0.9 image (`kicad/kicad:9.0.9@sha256:e638b79b…`, linux/amd64, branch `v04-k9-probes`; whole `tests/kicad` without the corpus: 777 passed, 4 failed, 784 skipped, 1 xfailed; `tests/kicad/test_probe_results.py` passed on the 536 probes of major 9): `tests/kicad/build/test_layer_builds.py` 2 passed (`test_filled_fixture_on_kicad_9` for 6 and 8 layers), 8 skipped (the 10.0 half); `build-layers-<n>-t9` = `absent` and `build-layers-gerbers-<n>-t9` = `equal` for n = 6, 8 are in `9.0.9.json`; `tests/unit/test_layer_fixtures.py` 3 passed.

## 6. Documentation

- [x] 6.1 Update `docs/dsl.md` (the counts of `board()`, `Design.copper_layers`, planes on any inner layer and the KiCad hint, the `layers` row of the zone table, the `DslError` list), `docs/lens.md` (the mismatch hint and the rebuild of a board given more layers in KiCad), `docs/altium.md` (a script of 6 or 8 layers is written with c0085's stack; the layer names of the document) and `docs/formats/kicad/board.md` ("Created boards": the inner row rule and the counts). Proof: `uv run pytest tests/consistency tests/unit/test_format_facts.py tests/residue`.
  - 2026-10-07: `tests/consistency tests/unit/test_format_facts.py tests/residue` 313 passed, 15 skipped, exit 0.
- [x] 6.2 If c0080 is archived, add one tested line for `design.board(…, copper=6)` and `Design.copper_layers` to its guide page on boards, as c0080 asks of every change that adds a public script name; otherwise write under this task that c0080 is open. Proof: the guide test that c0080 names passes, or the note is present.
  - 2026-10-07: c0080 is open (0/15 tasks, not archived): no guide page on boards exists yet. c0080 adds the tested line for `design.board(…, copper=6)` and `Design.copper_layers` when it writes that page.

## 7. Closing

- [x] 7.1 Run the residue and the test suites. Proof: `uv run pytest tests/residue`, `uv run python tools/residue/scan.py` and `uv run pytest tests/corpus/test_manifest.py` (the two fixtures are declared in `tests/data/MANIFEST.toml`) exit 0; `make check-fast` passes; the whole unit suite passes on Python 3.11, `uv run --isolated --python 3.11 --extra dev pytest tests/unit -q -n 6 -p no:cacheprovider`; `openspec validate c0100-board-layer-count --strict --no-interactive` passes. The full `make check` and `gh pr checks` (`unit`, `kicad-9`, `kicad-10`) are the coordinator's run at the merge, not this task's.
  - 2026-10-07: `tests/residue` and `tests/corpus/test_manifest.py` 85 passed, exit 0; `tools/residue/scan.py` 0 hits, exit 0; `openspec validate --all --strict` 100 passed, exit 0; the unit suite on Python 3.11 (`-n 3`): 9316 passed, 3 skipped, 1 failed (test_cited_ids_registered), exit 1; `make check-fast PYTEST_WORKERS=3`: ruff, format, pyright and the residue scan pass; tests 9595 passed, 18 skipped, 1 failed (the same test), exit 2. Not ticked while `test_cited_ids_registered` fails on the base (see 1.1).
  - 2026-10-08, branch `v04-close-a` on `04ef42a`, with every edit of the closing pass of c0077 to c0103 in the tree (the gate of the release, run once for all of them): `make check-fast PYTEST_WORKERS=4` exits 0 (ruff check, the guide's `--check`, ruff format, pyright, the residue scan, and 12731 passed, 29 skipped); the whole unit suite on Python 3.11.15, `uv run --isolated --python 3.11 --extra dev pytest tests/unit -q -n 4 -p no:cacheprovider`: 12348 passed, 25 skipped, exit 0; after `git add -A`, `uv run pytest tests/residue tests/corpus/test_manifest.py -q`: 80 passed, 5 skipped (no `kicad-cli`, no KiCad libraries), exit 0; `uv run python tools/residue/scan.py`: 0 hits, exit 0; `openspec validate --all --strict --no-interactive` reports the same six errors as on `04ef42a` (c0084, c0085 twice, c0086, c0108, c0128) and none of this change, besides the long-requirement warnings. The full `make check` is the coordinator's. The two fixtures stay declared in `tests/data/MANIFEST.toml`.
- [x] 7.2 Update the evidence: `H-K-PCB-LAYERS` becomes `KICAD-VERIFIED (9.0.x, 10.0.x)` with the re-save on 10.0.x named in its result, and `H-K-BUILD-LAYERS` `KICAD-VERIFIED (9.0.x, 10.0.x)` with the 9.0.x part on the fixtures named, or record what was refuted. Proof: `uv run pytest tests/unit/test_provenance.py tests/unit/test_hypotheses_register.py tests/kicad/test_probe_results.py`.
  - 2026-10-07: both rows are `KICAD-VERIFIED (10.0.x)` with the recorded 10.0.6 outcomes; the re-save is named as 10.0.6 only. Not ticked: the 9.0.x part (tables on 9.0.9, the two fixtures on 9.0.9) waits for the run in the pinned image; then the level becomes `KICAD-VERIFIED (9.0.x, 10.0.x)` and the 9.0.9 fact row of `board.md` its label.
  - 2026-10-08: ticked: `H-K-PCB-LAYERS` and `H-K-BUILD-LAYERS` are `KICAD-VERIFIED (9.0.x, 10.0.x)` with the image run of 2026-10-08 named in their results (the re-save on 10.0.6 only; the 9.0.x part of the builds on the two fixtures), and the 9.0.9 fact row of `docs/formats/kicad/board.md` is `KICAD-VERIFIED (9.0.x)`. `uv run pytest tests/unit/test_provenance.py tests/unit/test_hypotheses_register.py` passes; `tests/kicad/test_probe_results.py` passed in the image. CI has still to confirm the 9.0.9 half.
- [x] 7.3 Add to `CHANGELOG.md` under Unreleased: "`design.board(copper=…)` takes 6 and 8 copper layers: zones, planes and script copper on every inner layer, the KiCad layer table KiCad itself writes, proved through fill, DRC and export on KiCad 9 and 10; `Design.copper_layers`; a rebuild names the board's count when it differs; `--target altium` writes the six- and eight-layer document with the stack of c0085. `fenolite.dsl.design.INNER_LAYERS` and `layers.INNER_ROWS` are replaced by `inner_layers(copper)` and `inner_rows(copper)`". Update the entry of c0100 in `docs/roadmap.md` ("v0.4: proposals on other branches"). Proof: `git diff --stat CHANGELOG.md docs/roadmap.md` lists both files.
  - 2026-10-07: the entry is at the end of `## [Unreleased]` of `CHANGELOG.md`. Not ticked: `docs/roadmap.md` is the coordinator's file in this wave and was not edited, so `git diff --stat` lists `CHANGELOG.md` only.
  - 2026-10-08, base `04ef42a`: ticked. The entry now says that the proof holds on KiCad 9 and 10 (both rows `KICAD-VERIFIED (9.0.x, 10.0.x)`; the `kicad-9` and `kicad-10` jobs of CI run 37772583226 pass `test_layer_tables.py` and `test_layer_builds.py`), and the row of c0100 in `docs/roadmap.md` ("v0.4: proposals on other branches") says that it ships in 0.4; `git diff --stat CHANGELOG.md docs/roadmap.md` lists both files.
