lgili/Fenolite/openspec/changes/c0101-board-stackup/tasks.md

## 0. Entry check

- [x] 0.1 Read the living `kicad-file-backend`, `design-model`, `design-dsl`, `layout-lens`, `board-analyses`, `manufacturing-exports`, `cli-contract`, `altium-build` and `kicad-oracle` specs, and `openspec list`. Write under this task, with the date: whether release 0.3.0 is out with c0085, c0090 and c0126 archived (the Altium requirement and the 0.2.0 fixture rest on them); whether c0100 is archived (it must be: regenerate the MODIFIED "Created board header" from the living text, which then holds its `created_layers` sentence, re-apply this change's edits, and run the six-layer build of task 7.1); whether another archive changed "Modelled board content" or "Projected fields on write" (then regenerate that delta the same way; c0103 and c0112 regenerate after this change, design Decision 13); and what the living text now says about `setup`, `inspect` and export kinds. Proof: `openspec validate c0101-board-stackup --strict --no-interactive` passes after any regeneration.
  - Done: 2026-10-08, on the tip `7392159d`: release 0.3.0 is not out and c0126 is not on the branch (design, "Found on 2026-10-07"). c0100 is on the branch, implemented and not archived: "Created board header" is regenerated on the text of its delta, this change's edits applied again. No implemented change modifies "Modelled board content" or "Projected fields on write": both stand on the living text. "Export command" is regenerated on c0116's delta. `openspec validate c0101-board-stackup --strict --no-interactive` passes.

## 1. Probe and register

- [x] 1.1 Add the rows `H-K-STACKUP-JOB`, `H-K-STACKUP-COMPLETE`, `H-K-STACKUP-DEFAULT` and `H-K-STACKUP-RESAVE` to `docs/hypotheses.md` (backend `kicad`, level `INFERRED`, the tests and criteria of `design.md`, result `pending` with the measurements of 2026-10-05 as the first record), and widen the "used for" cells of S-0020, S-0021, S-0029, S-0033, S-0058 and S-0125 with the stack-up facts. Proof: `uv run pytest tests/unit/test_hypotheses_register.py tests/unit/test_provenance.py`; `grep -cE '^\| H-K-STACKUP-(JOB|COMPLETE|DEFAULT|RESAVE) ' docs/hypotheses.md` prints `4`.
  - Open: the four rows are registered (2026-10-07; the grep prints 4, `test_provenance.py` passes); the "used for" cells of S-0020, S-0021, S-0029, S-0033, S-0058 and S-0125 are not widened, because `docs/evidence/sources.md` is append-only for the lanes of this night. S-0033 was not read for this change: the names are sourced from S-0021 (read again on 2026-10-07) and S-0058.
  - 2026-10-08, base `04ef42a`: ticked. The "used for" cells of S-0020 (the job file, completeness, defaults, re-save and IPC-2581 runs), S-0021 (the `stackup` section and `general` thickness), S-0029 (the probes on the pinned 9.0.9 image), S-0058 (the rows of KiCad-written nodes and the census) and S-0125 (the download page lists the Gerber Job Format Specification, revision 2020.08) are widened with the stack-up facts. S-0033 is not: it is a keyword list in KiCad's source tree, the change takes no fact from it, and since 2026-10-08 no third-party source code is cited as a format fact; the design ("Sources") is corrected so. `uv run pytest tests/unit/test_hypotheses_register.py tests/unit/test_provenance.py` passes, and the `grep -cE` prints `4`.
- [x] 1.2 Write `tests/kicad/board/_stackbench.py`: created boards of 2, 4, 6 and 8 copper layers written by `write_board` for a major, the node cases of the oracle requirement inserted by token edit, the export of `F.Cu` and a reader of the job file; and its hermetic half `tests/unit/backends/kicad/test_stackbench.py` (every bench parses, every case is listed once). Proof: `uv run pytest tests/unit/backends/kicad/test_stackbench.py`; `uv run pytest tests/residue`.
  - Done: 2026-10-08: the module is `tests/_stackbench.py`; with c0100 on the branch its benches exist for 2, 4, 6 and 8 copper layers, and `tests/unit/backends/kicad/test_stackbench.py` passes.
- [x] 1.3 Write the KiCad half of `tests/kicad/board/test_stackup_oracle.py -k "complete or default"` (job verdicts only; the reader's verdict joins in task 3.3) and record the probes on both majors. The 9.0.9 outcomes of `more`, `nopaste`, `order` and `nopaste-table`, measured on 10.0.6 only, settle that half. A probe that differs stops this change: write what KiCad showed into the register row and correct Decision 5. Proof: `uv run pytest tests/kicad/board/test_stackup_oracle.py -k "complete or default" -rA` on the local KiCad 10.0.6 and inside the pinned 9.0.9 image; `FENOLITE_PROBES_WRITE=1` updates both probe files; `uv run pytest tests/kicad/test_probe_results.py`.
  - Open: the 9.0.9 side of `pcb-stackup-default-6` and `-8` waits for the one image run of the wave. Recorded: the seven `incomplete` probes `absent`, `order` and `nopaste-table` `present`, `default-2` and `default-4` `equal`, on 10.0.6 and 9.0.9 (2026-10-07; the 9.0.9 half of `more`, `nopaste`, `order` and `nopaste-table` gives the outcomes of 10.0.6, Decision 5 stands); `default-6` and `default-8` `equal` on 10.0.6 (2026-10-08). The outcomes were merged into the probe files by running these probes alone.
  - 2026-10-08: ticked by the local run of 2026-10-08 in the pinned 9.0.9 image (`kicad/kicad:9.0.9@sha256:e638b79b…`, linux/amd64, branch `v04-k9-probes`; whole `tests/kicad` without the corpus: 777 passed, 4 failed, 784 skipped, 1 xfailed; `tests/kicad/test_probe_results.py` passed on the 536 probes of major 9): `pcb-stackup-default-6` and `-8` = `equal` on 9.0.9, recorded in `9.0.9.json`; `test_stackup_oracle.py` 18 passed, 3 skipped (the 10.0-only re-save and IPC tests).
- [x] 1.4 Record `pcb-stackup-resave-defaults` and `pcb-stackup-ipc-thickness` on 10.0.6, with nodes in the form of Decision 6 inserted by token edit. Proof: `uv run pytest tests/kicad/board/test_stackup_oracle.py -k "resave_defaults or ipc" -rA` on the local KiCad 10.0.6.
  - Done: 2026-10-07: both `equal` on 10.0.6. The bench row of the dielectric holds a thickness alone: a dielectric row without a thickness comes back with `(thickness 0)`, which the hypothesis does not state.
- [x] 1.5 Write the section "Stack-up" of `docs/formats/kicad/board.md` (rows and types, child order, sheets, tail, completeness, defaults, the two thickness sources), each fact with its source and label, and `docs/evidence/kicad-stackup.md` with the measurements of `design.md`. Proof: `uv run pytest tests/unit/test_format_facts.py tests/residue`.
  - Done: 2026-10-07: section "Stack-up (c0101)" of `docs/formats/kicad/board.md` and `docs/evidence/kicad-stackup.md` (the measurements of the day, not those of the proposal).

## 2. Model

- [x] 2.1 Add `DielectricKind`, `StackLayer.dielectric_kind`, `StackLayer.color`, `Stackup.impedance_controlled`, `Stackup.thickness()`, `depth()` and `between()` to `src/fenolite/model/board.py`, regenerate the board schema, and write `tests/unit/model/test_stackup.py` (scenarios "Old documents still load", "A document of 0.2.0 still loads" on c0126's fixture `tests/data/model/v0.2.0/blink_2layer.board.json`, "Thickness, depth and the entries between two layers" and "Schema regenerated"). Proof: `uv run pytest tests/unit/model/test_stackup.py tests/unit/model/test_canonical.py tests/unit/model/test_footprint_items.py tests/unit/test_schema_drift.py`; `uv run python tools/gen_schemas.py --check`; `uv run pyright src`.
  - Done: 2026-10-07: the fixture is `tests/data/model/v0.2.1/blink_2layer.board.json`, written by the code of the base commit (c0126's 0.2.0 fixture is not on the branch); `tests/unit/model/test_footprint_items.py` of the proof is c0126's and does not exist. `tools/residue/scope.toml` gains one `numeric-code` waiver for the fixture (coordinates in nanometres above 100 mm): the maintainer approves waivers per file.
- [x] 2.2 Add `model.stackup-order`, `model.stackup-copper` and `model.stackup-value` to `Design.validate()` (scenarios "Copper entries out of table order" and "Mixed gap and a bad decimal"). Run the Altium import tests, the six-layer sample `tests/data/altium/board6` and the round-trip tests of c0090, and write under this task any finding that an imported or written stack-up now gives. Proof: `uv run pytest tests/unit/model -k "stackup or validate" tests/unit/backends/altium tests/unit/lens/test_altium_pcb_complete.py tests/unit/checks/test_rta2.py tests/unit/checks/test_rta3.py`; `uv run pytest tests/corpus/test_altium_import.py -rA` with the corpus cached.
  - Done: 2026-10-07: no imported or written stack-up gives a finding: `tests/unit/backends/altium` and the listed files pass (2330 passed), and `tests/corpus/test_altium_import.py` passes on the cached corpus without the heavy items. The loss tangent may be 0 ("Found on 2026-10-07").
- [x] 2.3 Describe the fields, helpers and findings in `docs/design-model.md`, with the sentence "Release 0.2.x cannot read a model document that carries `dielectric_kind`, `color` or `impedance_controlled`: its reader refuses an unknown key", and list the three codes in `docs/cli-contract.md`. Proof: `grep -n "0.2.x cannot read" docs/design-model.md` prints the sentence; `uv run pytest tests/consistency tests/residue`.
  - Done: 2026-10-07.

## 3. Reading

- [x] 3.1 Author `tests/data/kicad/board/stackup_four.kicad_pcb` (the board of "Four-layer node projected") with its row in `tests/data/MANIFEST.toml`, and add it beside `two_layer.kicad_pcb` to `tests/kicad/board/test_board_loads.py`. Proof: `uv run pytest tests/residue tests/unit/test_repo_layout.py tests/corpus/test_manifest.py`; `uv run pytest tests/kicad/board/test_board_loads.py -k fixture -rA` on the local KiCad 10.0.6.
  - Done: 2026-10-07: written by Fenolite's own writer from `tests/_boards.py` (`bare_board(4, four_layer_stackup())`), format 20241229; it loads on 10.0.6 and 9.0.9.
- [x] 3.2 Write `src/fenolite/backends/kicad/stackup.py` with `TYPES`, `project_stackup`, `values` and the three read codes, and `tests/unit/backends/kicad/test_stackup_read.py` (scenarios of "Stack-up on boards": sheets, side order, finish, completeness, exact values, ids). Proof: `uv run pytest tests/unit/backends/kicad/test_stackup_read.py tests/unit/test_import_graph.py`; `uv run pyright src`.
  - Done: 2026-10-07: 30 tests.
- [x] 3.3 Call `project_stackup` from `read_board`, with the thickness warning and the codes in `pcb.ISSUE_CODES` (scenarios "Total thickness that differs from the rows", "Board without a node", "Stack-up projected from an opaque setup"), and add the reader's verdict to the completeness probes of task 1.3. Proof: `uv run pytest tests/unit/backends/kicad -k "stackup or read or opaque"`; `uv run pytest tests/kicad/board/test_stackup_oracle.py -k complete -rA` on the local KiCad 10.0.6.
  - Done: 2026-10-07: the reader's verdict is asserted beside each completeness probe on both majors.
- [x] 3.4 Write `tests/corpus/test_stackup_census.py` (scenario "Corpus census") and copy its census into `docs/evidence/kicad-stackup.md`. Proof: `FENOLITE_CENSUS_OUT=<file> uv run pytest tests/corpus/test_stackup_census.py tests/corpus/test_board_rt1.py -rA` with the corpus cached; `git status --porcelain` lists no file under the cache.
  - Done: 2026-10-07: 17 of the 21 boards read hold a node and all 17 are projected (the proposal's census counted 18 of 24 on another cache state); RT1 passes.

## 4. Writing

- [x] 4.1 Add `complete`, `stackup_node` and the refusal `kicad.board.stackup-invalid` to `stackup.py`, with `tests/unit/backends/kicad/test_stackup_write.py` (completion, row order, sheets, tail, a mask of thickness 0, refusal with `allow_lossy`). Proof: `uv run pytest tests/unit/backends/kicad/test_stackup_write.py`; `uv run pyright src`.
  - Done: 2026-10-07.
- [x] 4.2 Write the node on created boards in `pcb.py` (first child of `setup`, `general` thickness of the completed stack-up), add the eight names to `FLOOR_HEADS` and their rows to `docs/formats/kicad/board.md`, and give `tests/_boards.py::created_board()` its stack-up (scenarios of "Created board header", "Created four-layer board", "Masks the stack-up omits"). Proof: `uv run pytest tests/unit/backends/kicad/test_pcb_write.py tests/unit/backends/kicad/test_stackup_write.py`.
  - Done: 2026-10-07: seven names join `FLOOR_HEADS`, not eight: `type` is in the skeleton, and the list is disjoint from it ("Found on 2026-10-07"). An existing test that wrote a board thickness from a stack-up of one copper and one dielectric entry now gives it both copper entries: such a stack-up is refused.
- [x] 4.3 Rewrite the node of a read board in `projection()` (`setup` and the `thickness` of `general`), with `kicad.board.stackup-rewritten` (scenarios "Stack-up edited on a read board", "Stack-up added to a read board", "Copper entries that do not fit the table", "Written nodes read back"). Proof: `uv run pytest tests/unit/backends/kicad -k "stackup or projected or roundtrip"`; `uv run pytest tests/corpus/test_board_rt1.py` with the corpus cached.
  - Done: 2026-10-07.
- [x] 4.4 Load the created test board with its stack-up on both majors (`H-K-PCB-WRITE` keeps its level). Proof: `uv run pytest tests/kicad/board/test_triad.py -rA` on the local KiCad 10.0.6 and inside the pinned 9.0.9 image.
  - Done: 2026-10-07: `tests/kicad/board/test_triad.py` passes on 10.0.6 and in the 9.0.9 image.

## 5. Script

- [x] 5.1 Write `src/fenolite/dsl/stack.py` (`StackEntry`, `silkscreen`, `mask`, `copper`, `core`, `prepreg`; decimals, lengths, refusals) and `tests/unit/dsl/test_stackup_dsl.py -k entries`. Proof: `uv run pytest tests/unit/dsl/test_stackup_dsl.py tests/unit/test_import_graph.py`; `uv run pyright src`.
  - Done: 2026-10-07: `dsl/stack.py` also imports `fenolite.dsl.errors` and `fenolite.dsl.units` ("Found on 2026-10-07").
- [x] 5.2 Add `Design.stackup`, `StackupSpec`, the model stack-up of `to_model`, the keys `stackup` and `stack_layer`, `stackup_locked` and the re-exports (scenarios of "Stack-up in the DSL"), and the section "Stack-up" and the key rows of `docs/dsl.md`. Proof: `uv run pytest tests/unit/dsl tests/unit/test_import_graph.py tests/consistency`.
  - Done: 2026-10-07.

## 6. Build and rebuild

- [x] 6.1 Add `merge_stackup`, `StackupMerge` and `MERGE_ISSUE_CODES` to `stackup.py`, with `tests/unit/backends/kicad/test_stackup_merge.py` (the five cases, the first difference named, purity). Proof: `uv run pytest tests/unit/backends/kicad/test_stackup_merge.py`.
  - Done: 2026-10-07.
- [x] 6.2 Add `lock_stackup` and the merge step to `build_design`, `result.stackup`, the call in `cmd_build.py`, an entry in `src/fenolite/cli/data/explain.toml` for each of the eleven new codes, and the rebuild rule in `docs/lens.md` (scenarios of "Stack-up in a build" and "Stack-up across rebuilds"). Proof: `uv run pytest tests/unit/lens/test_build_stackup.py tests/unit/lens/test_preserve_issues.py tests/unit/cli/test_build_command.py tests/unit/cli/test_explain_cmd.py tests/consistency`.
  - Done: 2026-10-07: eight entries in `explain.toml`, not eleven: the three `model.stackup-*` codes are in no `*ISSUE_CODES` table, as no `model.*` code is, and an entry without a table fails `test_explain_cmd.py`.
- [x] 6.3 Apply "Stack-ups with masks, sheets and kinds in an Altium build" to both `stack_from_stackup` functions (`lens/altium_copper.py` and `backends/altium/lower.py`): the stated dielectric kind, the info for values without a key (`account.skip` in the write of a model), and the gap named when sheets do not fit. Write `tests/unit/lens/test_altium_stackup.py` and `tests/unit/backends/altium/test_lower_stackup.py` with its four scenarios, and describe the rules in `docs/altium.md`. No new code is added, so `explain.toml` gains no entry. Proof: `uv run pytest tests/unit/lens/test_altium_stackup.py tests/unit/backends/altium/test_lower_stackup.py tests/unit/lens/test_altium_pcb_complete.py tests/unit/lens/test_altium_pcb_golden.py tests/unit/lens/test_altium_copper_golden.py`; every committed Altium sample keeps its bytes.
  - Done: 2026-10-07: every committed Altium sample keeps its bytes (the golden tests pass).

## 7. Oracle

- [x] 7.1 Write `test_stackup_oracle.py -k job` (`pcb-stackup-job-<n>` for 2, 4, 6 and 8 layers on the bench) and `build-stackup-job` with the stack-up blink; with c0100 archived, add its six-layer variant. A probe that is not `equal` stops this part: record what KiCad showed and correct the writer before going on. Proof: `uv run pytest tests/kicad/board/test_stackup_oracle.py -k job -rA` on the local KiCad 10.0.6 and inside the pinned 9.0.9 image; both probe files hold the five probes as `equal`.
  - Open: the 9.0.9 side of `pcb-stackup-job-6`, `-8` and of the six-layer variant inside `build-stackup-job` waits for the one image run of the wave. Recorded: `job-2`, `job-4` and `build-stackup-job` (two-layer blink) `equal` on both majors (2026-10-07); `job-6`, `job-8` and `build-stackup-job` with its six-layer variant `equal` on 10.0.6 (2026-10-08).
  - 2026-10-08: ticked by the local run of 2026-10-08 in the pinned 9.0.9 image (`kicad/kicad:9.0.9@sha256:e638b79b…`, linux/amd64, branch `v04-k9-probes`; whole `tests/kicad` without the corpus: 777 passed, 4 failed, 784 skipped, 1 xfailed; `tests/kicad/test_probe_results.py` passed on the 536 probes of major 9): `pcb-stackup-job-6` and `-8` = `equal` on 9.0.9, recorded in `9.0.9.json`; `build-stackup-job`, recorded `equal` on 2026-10-07 before its six-layer variant existed, compared `equal` again with the variant. The five probes are `equal` in both files.
- [x] 7.2 Record `pcb-stackup-resave` on 10.0.6 with the nodes that the writer of section 4 writes. Proof: `uv run pytest tests/kicad/board/test_stackup_oracle.py -k resave -rA` on the local KiCad 10.0.6.
  - Done: 2026-10-07: `equal` for the benches that exist. KiCad adds 4.5 and 0.02 to a dielectric sheet that states neither; the probe compares with that ("Found on 2026-10-07").

## 8. Analyses and outputs

- [x] 8.1 Add `inputs.board_thickness_source` and `inputs.stackup` to `cmd_analyze.py` (scenarios of "Stack-up thicknesses in analyze"), and say in `docs/analyses.md` that a KiCad stack-up now gives the thicknesses. Proof: `uv run pytest tests/unit/cli/test_analyze_cmd.py tests/unit/analysis`.
  - Done: 2026-10-07.
- [x] 8.2 Add `STACKUP_KINDS`, `export.stackup-default` and the write condition by errors to `exports/plan.py`, `exports/codes.py` and `cmd_export.py` (scenarios of "Stack-up note in exports"), and the note to `docs/exports.md`. Proof: `uv run pytest tests/unit/cli/test_export_cmd.py tests/unit/exports`.
  - Done: 2026-10-07: `export --gerbers` of a board without a stack-up now holds one info. 2026-10-08: on the tip only an error stops the writes (c0116's rule, kept); the delta of "Export command" is regenerated on c0116's text.
- [x] 8.3 Add `result.stackup` to `cmd_inspect.py` (scenarios of "Stack-up in inspect") and describe it in `docs/cli-contract.md`. Proof: `uv run pytest tests/unit/cli/test_inspect_cmd.py tests/unit/cli/test_hermetic_examples.py tests/consistency`.
  - Done: 2026-10-07.
- [x] 8.4 Only if c0080 is archived: add one tested line for `design.stackup()` to the guide page that c0080 names for board definition. Proof: the guide test of c0080 passes with the line.
  - Open: c0080 is not archived.
  - 2026-10-08, base `04ef42a`: ticked. c0080 is on this branch and counts as available for 0.4. The page that c0080 gives the build-up is `rules` (its section "The stack-up" and the `design.stackup(...)` of its first design block); it gains a paragraph on the presets and a `fenolite-design` block whose line `design.stackup(*stack.preset("four-layer-1.6mm"), finish="ENIG")` builds a four-layer board for targets 9 and 10. `tools/gen_agent_guide.py` rewrote `references/dsl-reference.md` (the docstring of `stack.preset`). `uv run pytest tests/unit/agent -q`: 79 passed, 10 skipped (no `kicad-cli`), with `test_design_blocks_build[rules:138:9]` and `[rules:138:10]` among them.

## 9. Presets (cut first)

- [x] 9.1 Choose at most three public fabricator pages that state a whole stack-up (2, 4 and 6 copper layers), register each in `docs/evidence/sources.md` under S-0620, S-0621 and S-0622 (first check that the three ids are still free there; take the next free ids of the block S-0620 to S-0639 otherwise and correct the design) with its URL, terms and date, write the preset files, `stack.preset` and `stack.PRESETS`, and list them in `docs/dsl.md` (scenarios of "Stack-up presets"). The files hold only what the page states; no fabricator name in a file name. If the maintainer cuts the part, write so under this task and remove the requirement's delta. Proof: `uv run pytest tests/unit/dsl/test_stackup_presets.py tests/unit/test_provenance.py tests/residue`.
  - Open: not started on 2026-10-07: the presets are the first cut of the design and came after every part that is never cut; no fabricator page was read. `stack.PRESETS` is empty and `stack.preset()` refuses every name. S-0620 to S-0622 are not used.
  - 2026-10-08, base `04ef42a`: ticked. Three pages of one fabricator, each a whole stack-up table with millimetre values: https://docs.oshpark.com/services/two-layer/, `/four-layer/` and `/six-layer/`, read on 2026-10-08. They are S-0720, S-0721 and S-0722, not S-0620 to S-0622: S-0620 to S-0622 were still free, but the coordinator of release 0.4 gave the lanes that close v0.4 the ids from S-0720 up, because parallel branches take ids of the S-06xx blocks; design (Decision 12, "Interfaces") and proposal are corrected. Each row states the page's terms ("© 2023 OSH Park, LLC", facts only) and the evidence label `INFERRED`. The files are `src/fenolite/dsl/stackups/two-layer-1.6mm.toml`, `four-layer-1.6mm.toml` and `six-layer-1.6mm.toml` (no fabricator name in a file name), with `source`, `url`, `retrieved`, `copper` and one `[[entry]]` per row of the page; a dielectric constant comes from the row, else from the page's one "Dielectric" value of its substrate (two- and four-layer cores), and the six-layer middle core, whose row and page name none, has none; no `finish` (the finish is the script's). The page's silkscreen thickness stays in the file and is not passed on, since a stack-up silkscreen has none. `stack.PRESETS` lists the files in code-point order and `stack.preset()` reads them with `importlib.resources`. `docs/dsl.md` has the section "Stack-up presets" with each preset's URL, source id and date. Proof: `uv run pytest tests/unit/dsl/test_stackup_presets.py tests/unit/test_provenance.py tests/residue` passes (53 passed, 5 skipped).

## 10. Closing

- [x] 10.1 Run the residue and the tests. Proof: `uv run pytest tests/residue tests/corpus/test_manifest.py` and `uv run python tools/residue/scan.py` exit 0; `uv run python tools/gen_schemas.py --check` exits 0; `make check-fast` passes; the whole unit suite passes on Python 3.11, `uv run --isolated --python 3.11 --extra dev pytest tests/unit -q -n 6 -p no:cacheprovider`; `openspec validate c0101-board-stackup --strict --no-interactive` passes. The full `make check` and `gh pr checks` (`unit`, `kicad-9`, `kicad-10`) are the coordinator's run at the merge, not this task's.
  - Open: 2026-10-07: the checks of the night ran (the report holds the counts); the whole unit suite on Python 3.11 was not run, by the rules of the night.
  - 2026-10-08, branch `v04-close-a` on `04ef42a`, with every edit of the closing pass of c0077 to c0103 in the tree (the gate of the release, run once for all of them): `make check-fast PYTEST_WORKERS=4` exits 0 (ruff check, the guide's `--check`, ruff format, pyright, the residue scan, and 12731 passed, 29 skipped); the whole unit suite on Python 3.11.15, `uv run --isolated --python 3.11 --extra dev pytest tests/unit -q -n 4 -p no:cacheprovider`: 12348 passed, 25 skipped, exit 0; after `git add -A`, `uv run pytest tests/residue tests/corpus/test_manifest.py -q`: 80 passed, 5 skipped (no `kicad-cli`, no KiCad libraries), exit 0; `uv run python tools/residue/scan.py`: 0 hits, exit 0; `openspec validate --all --strict --no-interactive` reports the same six errors as on `04ef42a` (c0084, c0085 twice, c0086, c0108, c0128) and none of this change, besides the long-requirement warnings. The full `make check` is the coordinator's. `uv run python tools/gen_schemas.py --check` exits 0, and so does `tools/gen_evidence_matrix.py --check` after `docs/evidence/matrix.md` was regenerated for `stackup.EVIDENCE`; the wheel lists the three preset files.
- [x] 10.2 Update the evidence labels: `H-K-STACKUP-JOB`, `H-K-STACKUP-COMPLETE` and `H-K-STACKUP-DEFAULT` become `KICAD-VERIFIED (9.0.x, 10.0.x)` and `H-K-STACKUP-RESAVE` `KICAD-VERIFIED (10.0.x)`, with their runs, or record what was refuted and the fallback taken; `stackup.EVIDENCE` and the labels of the "Stack-up" facts of `docs/formats/kicad/board.md` follow. Proof: `uv run pytest tests/unit/test_provenance.py tests/unit/test_hypotheses_register.py tests/kicad/test_probe_results.py tests/unit/test_format_facts.py`.
  - Open: `H-K-STACKUP-JOB` and `H-K-STACKUP-DEFAULT` name both majors for the benches of 6 and 8 layers: they are `equal` on 10.0.6, and the 9.0.9 side waits for the one image run of the wave, so both rows stay `INFERRED`. `H-K-STACKUP-COMPLETE` is `KICAD-VERIFIED (9.0.x, 10.0.x)` and `H-K-STACKUP-RESAVE` `KICAD-VERIFIED (10.0.x)`; `stackup.EVIDENCE` stays `INFERRED`.
  - 2026-10-08: `H-K-STACKUP-JOB` and `H-K-STACKUP-DEFAULT` are now `KICAD-VERIFIED (9.0.x, 10.0.x)` (the image run of 2026-10-08, named in the rows). Still open: `stackup.EVIDENCE` and the labels of the "Stack-up" facts of `docs/formats/kicad/board.md` were not raised by the commit that recorded the probes.
  - 2026-10-08, base `04ef42a`: ticked. `stackup.EVIDENCE` is `KICAD-VERIFIED` (its four hypotheses are; the re-save on 10.0.x), and the "Stack-up" facts of `docs/formats/kicad/board.md` follow: the job-file row and the default row `KICAD-VERIFIED (9.0.x, 10.0.x)`, the row of what a 10.0.6 re-save adds `KICAD-VERIFIED (10.0.x)`. CI run 37772583226 on `04ef42a` confirms the 9.0.9 half: its `kicad-9` job passes `tests/kicad/board/test_stackup_oracle.py` (job 2, 4, 6, 8 and the built blink, the incomplete and complete nodes, the defaults of 2, 4, 6, 8) and `tests/kicad/test_probe_results.py`. `uv run pytest tests/unit/test_provenance.py tests/unit/test_hypotheses_register.py tests/unit/test_format_facts.py` passes; `tests/kicad/test_probe_results.py` skips here without `kicad-cli` and passes in both `kicad-*` jobs of that run.
- [x] 10.3 Add to `CHANGELOG.md` under Unreleased: "Board stack-ups: `read_board` fills `Board.stackup` from a KiCad stack-up that KiCad uses, created boards get the complete node and a matching board thickness, and scripts declare one with `design.stackup()` and `fenolite.dsl.stack` (the board's stack-up wins over an unlocked script one). `analyze` takes its thicknesses from it, `export` notes a job file that will state KiCad's default, and `inspect` shows it. New warnings name a stack-up that KiCad ignores and a board thickness that differs from its layers. An Altium build writes a stated core or prepreg, passes masks over and names what the document does not hold. **Release 0.2.x cannot read a model document that carries the new keys** (`dielectric_kind`, `color`, `impedance_controlled`)." Update the entry of c0101 in `docs/roadmap.md` ("v0.4: proposals on other branches"). Proof: `grep -n "0.2.x cannot read" CHANGELOG.md` prints the line; `git diff --stat CHANGELOG.md docs/roadmap.md` lists both files.
  - Open: the changelog line is written (2026-10-07); `docs/roadmap.md` is the coordinator's file this night.
  - 2026-10-08, base `04ef42a`: ticked. The entry gains the presets and the raised labels, and the row of c0101 in `docs/roadmap.md` says that it ships in 0.4. `grep -n "0.2.x cannot read" CHANGELOG.md` prints its line (17); `git diff --stat CHANGELOG.md docs/roadmap.md` lists both files.

## Corrections

- [x] C1 (2026-10-08). `Design.stackup()` refused a board declared with `board(outline=…)` of change c0102 ("stackup() is called after board()"): it tested `Design.size`, which only `board(width, height)` sets. It now tests `Design.outline_path`, which both forms set, as `zone()` does. The requirement "Stack-up in the DSL" says "in either of its forms" and gains the scenario "A shaped board takes a stack-up". Found while building `examples/yardstick` (c0119, task 0.2). Proof: `uv run pytest tests/unit/lens/test_build_outline_compose.py -q` (fails before the correction, passes after); `uv run pytest tests/unit/dsl/test_stackup_dsl.py tests/unit/lens/test_build_stackup.py -q`.
