lgili/Fenolite/openspec/changes/c0102-board-outline-shapes/tasks.md

## 0. Entry check

- [x] 0.1 Read the living `design-model`, `design-dsl`, `dsl-footprint-authoring`, `kicad-file-backend`, `layout-lens`, `board-analyses`, `altium-build`, `altium-pcb-writer` and `kicad-oracle` specs and `openspec list`. Write under this task, with the date: whether release 0.3.0 is out with c0085, c0090 and c0126 archived; whether c0100 is archived (it must be) and whether c0101, c0096, c0077 and c0080 are; and the state of the branch that maps several pads to one pin (c0123), which touches the pad-to-pin mapping of task 5.1. Regenerate from the living text, re-applying this change's edits: "Board and placements in the DSL" and "Zones in the DSL" on c0100's text (and on c0096's `anchor=` when c0096 is on `dev`), and any of the other seven MODIFIED requirements that an archive changed since `9aba2dff`. With c0100 archived, add a MODIFIED delta of its "Layer count across rebuilds" that keeps its same-count rule and its case "Table that Fenolite does not create", and gives a count change to "Copper layer changes across rebuilds" in place of its refusal and of the scenario "Mismatch names the board's count"; give "Copper layer changes across rebuilds" a case of four layers becoming six. If c0096 is on `dev`, list here the names of the table "Relation to c0096" that task 5.2 removes. Proof: `openspec validate c0102-board-outline-shapes --strict --no-interactive` passes after the regeneration.
  - 2026-10-08, on the integration base `7392159d`. Open: c0100 is implemented on this base (10 of 16 tasks) but not archived, so its "Layer count across rebuilds" is not living and no MODIFIED delta of it can be written; "Board and placements in the DSL" and "Zones in the DSL" stay on the living text (counts 2 and 4) and must be regenerated on c0100's text (2, 4, 6, 8, `inner_layers`) once it is archived. State read: release 0.2.1 is the last release (0.3.0 is not out); c0085 (13/16), c0090 (11/13) and c0126 (0/38) are open, none archived; c0101 (0/32), c0080 (0/15) and c0077 (6/12) are open; c0096 is not on this base, so task 5.2 removes nothing; c0123 (several pads per pin) is on this base (41/43) and its `Component.pin_pads()` is what `_pad_nets` reads: an unnumbered pad is outside its pad numbers. No living text of the nine MODIFIED requirements changed since `9aba2dff` (`altium-build` gained one ADDED requirement only), so no delta was regenerated. Done here: the scenario "Four layers become six" was added to "Copper layer changes across rebuilds", with its test (`tests/unit/lens/test_preserve_layers.py::test_four_layers_become_six`). The code keeps c0100's same-count rule and its case "Table that Fenolite does not create", and replaces its refusal of a count change and the scenario "Mismatch names the board's count" (their tests in `tests/unit/cli/test_build_preserve_command.py` were rewritten). `openspec validate c0102-board-outline-shapes --strict --no-interactive`: the change is valid, exit 0.
  - 2026-10-08, base `04ef42a` (`v04`, rebased onto 0.3.0 in `9fb3513`): closed on this base. **Release 0.3.0 is out** (`fenolite --version` prints `0.3.0`; `CHANGELOG.md` holds `## [0.3.0] - 2026-10-08`; the release record is the archived change `2026-10-08-c0150-release-0-3-0`); c0085, c0090 and c0126 shipped in it and are still open folders, not archived, on `v04` as on `release-0.3.0`. c0100, c0101, c0077 and c0080 are implemented on this base and closed for 0.4 in the same pass, none archived; c0096 is not on this base (task 5.2 removes nothing); c0123 shipped in 0.3.0 and is still an open folder, and its `Component.pin_pads()` is what `_pad_nets` reads. Release 0.4 is prepared from `v04` by the maintainer's decision of 2026-10-08. **Regeneration**: "Board and placements in the DSL" and "Zones in the DSL" of this change already stand on c0100's text: a three-way merge (base: the living text; one side: c0100's delta; the other: this change's delta) gives this change's delta unchanged for both, so c0100's counts, `inner_layers` and `Design.copper_layers` are in them. The other seven MODIFIED requirements: `openspec validate` compares them with the living text and reports no error for this change, and the archives since `9aba2dff` (c0089, c0143, c0150) touched none of them. **The MODIFIED delta of c0100's "Layer count across rebuilds"** cannot be written while c0100 is open: the requirement is in no living spec, so a MODIFIED delta of it fails validation. The code and the tests already follow it (same-count rule and "Table that Fenolite does not create" kept, the count change applied, "Four layers become six" in "Copper layer changes across rebuilds"); at the archive, c0100 is archived first and this change gains the delta then (the row of c0102 in `docs/roadmap.md` says so). Proof: `openspec validate c0102-board-outline-shapes --strict --no-interactive` gives no error (long-requirement warnings only).

## 1. Probe and register

- [x] 1.1 Add the rows `H-K-OUTLINE-ARCS`, `H-K-OUTLINE-INVALID`, `H-K-OUTLINE-OUTSIDE`, `H-K-ZONE-BOX`, `H-K-HOLE-FOOTPRINT`, `H-K-HOLE-COURTYARD`, `H-K-HOLE-SYMBOL` and `H-K-LAYER-CHANGE` to `docs/hypotheses.md` (backend `kicad`, level `INFERRED`, the tests and criteria of `design.md`, result `pending` with the measurements of 2026-10-05 as the first record). Proof: `uv run pytest tests/unit/test_hypotheses_register.py tests/unit/test_provenance.py`; `grep -cE '^\| (H-K-OUTLINE-ARCS|H-K-OUTLINE-INVALID|H-K-OUTLINE-OUTSIDE|H-K-ZONE-BOX|H-K-HOLE-FOOTPRINT|H-K-HOLE-COURTYARD|H-K-HOLE-SYMBOL|H-K-LAYER-CHANGE) ' docs/hypotheses.md` prints `8`.
  - 2026-10-08: eight rows appended to the table; `grep -cE …` prints `8`; register tests: 44 passed in 5.55s, exit 0.
- [x] 1.2 Write `tests/kicad/board/_outlinebench.py` (the boards of measurements 1 to 4, written through the model API with their edges as `Edge.Cuts` graphics until task 4.3 builds them from a script), `tests/kicad/board/test_outline_shapes.py` with the probes `outline-arcs-drc`, `outline-arcs-drill`, `outline-invalid-<case>` and `outline-outside-*`, and `tests/kicad/zones/test_zone_box.py` with the probe `zone-box-fill` (10.0.6 only: 9.0.9 has no `--refill-zones`); register them and record their outcomes. Write the facts to `docs/formats/kicad/board.md` with sources S-0020 and S-0029. An outcome that differs from `design.md` stops this task, and the design is corrected first. Proof: `uv run pytest tests/kicad/board/test_outline_shapes.py tests/kicad/zones/test_zone_box.py -rA` on the local KiCad 10.0.6, and the first file inside the pinned 9.0.9 image; `FENOLITE_PROBES_WRITE=1` updates both probe files; `uv run pytest tests/kicad/test_probe_results.py tests/unit/test_format_facts.py`.
  - 2026-10-08, open. Done on local `kicad-cli` 10.0.6: 12 passed in 10.50s, exit 0; every outcome is the one `design.md` states (`outline-arcs-drc` and `-drill` `absent`; `outline-invalid-cross`, `-touch`, `-overlap`, `-selfx` `present`, `-nested`, `-inside` `absent`; `outline-outside-free` `absent`, `-across` `present`; `zone-box-fill` `absent`). The 13 probes are registered and recorded in `10.0.6.json` (only their keys were added: the other outcomes of that file were not run again); facts are in `docs/formats/kicad/board.md`; registry tests: 33 passed in 9.86s, exit 0. KiCad 9.0.9 was not run: this run had no local 9.0.9 and did not use the pinned image, so the `kicad-9` job must record the probes of both majors in `docs/evidence/kicad/probes/9.0.9.json` (`FENOLITE_PROBES_WRITE=1`) before this task is ticked.
  - 2026-10-08: recorded by the second local run of 2026-10-08 in the pinned 9.0.9 image (`kicad/kicad:9.0.9@sha256:e638b79b…`, linux/amd64, branch `v04-k9-probes-2`; whole `tests/kicad` without the corpus: 998 passed, 2 failed, 806 skipped, 1 xfailed; `tests/kicad/test_probe_results.py` passed on the 723 probes of major 9); the task stays open because one of the ten outcomes is not the one `design.md` states. In `9.0.9.json`: `outline-arcs-drc` and `-drill` `absent`, `outline-invalid-overlap` `present`, `-cross`, `-touch`, `-nested` and `-inside` `absent`, `outline-outside-free` `absent` and `-across` `present`, as stated for 9.0.9; `outline-invalid-selfx` = `absent`, where the design and `INVALID_ON_9` say `present`: 9.0.9 reports no `invalid_outline` for the self-crossing ring of the bench. `tests/kicad/board/test_outline_shapes.py` 9 passed, 1 failed, 1 skipped: the one failure is `test_invalid_outlines[selfx]`; the skip is `test_arcs_keep`, which needs `kicad-cli` 10. Owed: `INVALID_ON_9` and the statement of `H-K-OUTLINE-INVALID` corrected to what 9.0.9 reports, or a ring that 9.0.9 calls invalid.
  - 2026-10-08: corrected to what 9.0.9 reports, after the `kicad-9` job of CI run 37764862556 (on `1adc0ef`) failed `test_invalid_outlines[selfx]` with the same `absent`: `INVALID_ON_9` is `{"overlap"}`, and the statement of `H-K-OUTLINE-INVALID` (register and `design.md`), measurement 3 of `design.md` and the two spec scenarios say that 9.0.9 reports the overlap only; the 10.0.6 expectation is unchanged. No probe outcome changed. The task stays open until the `kicad-9` job passes the corrected test.
  - 2026-10-08: ticked by CI run 37772583226 on `04ef42a` (every job green): the `kicad-9` job (`kicad/kicad:9.0.9@sha256:e638b79b…`) passes `tests/kicad/board/test_outline_shapes.py` (`test_arcs_drc`, `test_arcs_drill`, `test_arcs_rings_read_back`, `test_invalid_outlines` for `cross`, `touch`, `overlap`, `selfx`, `nested` and `inside`, `test_copper_outside_the_outline`) and `tests/kicad/test_probe_results.py`; the `kicad-10` job passes the file and `tests/kicad/zones/test_zone_box.py` on 10.0.6. Locally, without `kicad-cli`, the files are collected and skip.
- [x] 1.3 Write `tests/kicad/board/_holebench.py` (the board of measurement 5, a footprint with courtyards on both sides, and a symbol library written by `sym.write_symbol_library` with a symbol without pins and one with one pin, both with `in_bom` false) with the probes `hole-root-pad`, `hole-drill`, `hole-pos`, `hole-courtyard-*` and `hole-symbol-load` in `tests/kicad/board/test_holes.py`, and `tests/kicad/lens/_layerbench.py` (the cases of measurement 7) with the probes `layers-added`, `layers-left-items` and `layers-stale-stackup` in `tests/kicad/lens/test_layer_change.py`; register and record them, with the facts in `docs/formats/kicad/board.md`. Proof: `uv run pytest tests/kicad/board/test_holes.py tests/kicad/lens/test_layer_change.py -k "facts or root_pad or drill or pos or courtyard or symbol" -rA` on 10.0.6 and inside the 9.0.9 image; `uv run pytest tests/kicad/test_probe_results.py`.
  - 2026-10-08, open. Done on local `kicad-cli` 10.0.6: 11 passed, 2 deselected in 11.09s, exit 0; `hole-root-pad` `reject`, `hole-drill` and `hole-symbol-load` `equal`, `hole-pos` and `hole-courtyard-clear` `absent`, `hole-courtyard-top` and `-bottom` `present`, `layers-added` `absent`, `layers-left-items` and `layers-stale-stackup` `present`; recorded in `10.0.6.json`. One finding beyond `design.md`: KiCad's ratsnest names either of two items at one point from run to run, so `layers-added` compares the findings by group, type and severity with their counts. KiCad 9.0.9 was not run: this run had no local 9.0.9 and did not use the pinned image, so the `kicad-9` job must record the probes of both majors in `docs/evidence/kicad/probes/9.0.9.json` (`FENOLITE_PROBES_WRITE=1`) before this task is ticked.
  - 2026-10-08: ticked by the second local run of 2026-10-08 in the pinned 9.0.9 image (`kicad/kicad:9.0.9@sha256:e638b79b…`, linux/amd64, branch `v04-k9-probes-2`; whole `tests/kicad` without the corpus: 998 passed, 2 failed, 806 skipped, 1 xfailed; `tests/kicad/test_probe_results.py` passed on the 723 probes of major 9): `tests/kicad/board/test_holes.py` 9 passed and `tests/kicad/lens/test_layer_change.py` 3 passed, 1 skipped (the skip is `test_rebuild_layers`, which needs `kicad-cli` 10); `hole-root-pad` `reject`, `hole-drill` and `hole-symbol-load` `equal`, `hole-pos` and `hole-courtyard-clear` `absent`, `hole-courtyard-top` and `-bottom` `present`, `layers-added` `absent`, `layers-left-items` and `layers-stale-stackup` `present` are in `9.0.9.json`, the outcomes of 10.0.6.

## 2. Model and the readers of the outline

- [x] 2.1 Add `OutlineArc` and `Outline.arcs` to `src/fenolite/model/board.py`, regenerate the schema, and write `tests/unit/model/test_outline_arcs.py` (scenarios of "Board outline arcs", with "A document of 0.2.0 still loads" on c0126's fixture `tests/data/model/v0.2.0/blink_2layer.board.json`). Proof: `uv run pytest tests/unit/model tests/unit/test_schema_drift.py`; `uv run python tools/gen_schemas.py --check` exits 0.
  - 2026-10-08: 204 passed, 2 skipped in 2.41s, exit 0; `gen_schemas.py --check`: exit 0. The scenario "A document of 0.2.0 still loads" is written (`-k v020`) and skips: c0126's fixture `tests/data/model/v0.2.0/blink_2layer.board.json` is not on this base.
- [x] 2.2 Polygonise model arcs in `board_outline` and `board_boundary`; add `outline_box`; read it in `lens.build._staging` and `lens.preserve._off_board`; add `Outline.arcs` to `fill_inputs_digest` (scenarios "Model outline with arcs", "Box of a round board", "Model outline with a round cut-out", and the unit half of "A part on a round board"). Proof: `uv run pytest tests/unit/backends/kicad/test_outline.py tests/unit/analysis/test_boundary.py tests/unit/lens`; `uv run pyright src`.
  - 2026-10-08: 1042 passed, 1 skipped in 112.76s (0:01:52), exit 0; `pyright src`: 0 errors, exit 0.

## 3. Outlines in the script

- [x] 3.1 Add paths, `Design.cutout`, `board(…, outline=None, locked=False)` and `outline_locked`, and their conversion in `to_model` (scenarios "Refused paths", "A board given by a path", "One form only", "Cut-outs in call order", and the unchanged scenarios of the three MODIFIED requirements). Proof: `uv run pytest tests/unit/dsl/test_outline_paths.py tests/unit/dsl tests/unit/test_import_graph.py`; `uv run pyright src`.
  - 2026-10-08: 524 passed in 8.31s, exit 0; `pyright src`: 0 errors, exit 0.
- [x] 3.2 Write `src/fenolite/dsl/shape.py` (`rect`, `circle`, `slot`, exact rounding with `math.isqrt`) and the zone box in `to_model`; test every rounded point against an exact `Fraction` computation, and a slot at 30° against `Transform.placement` within 1 nm (scenarios "Rounded corners", "A round cut-out", "A horizontal slot", "Zone on a round board"). Proof: `uv run pytest tests/unit/dsl/test_shape.py tests/unit/dsl/test_zones.py tests/unit/test_import_graph.py`.
  - 2026-10-08: 524 passed in 8.31s, exit 0 (the same run: `tests/unit/dsl` and the import graph).

## 4. Writer and the build check

- [x] 4.1 Write arcs, their orientation, `edge_texts`, `outline_digest` and the signed uuids in `pcb.py` and `outline.py` (scenarios of "Outline lowering"). Proof: `uv run pytest tests/unit/backends/kicad/test_outline_write.py tests/unit/backends/kicad/test_pcb_write.py`.
  - 2026-10-08: 38 passed in 1.33s, exit 0.
- [x] 4.2 Add `check_outline` and `CHECK_ISSUE_CODES`, the build step and `lock_outline` in `lens/build.py` and `cmd_build.py`, and the Altium refusal of arcs in `lens/altium.py` (scenarios of "Outline shape checks", "Outline shapes in a build" and "An outline with arcs, no document"). Proof: `uv run pytest tests/unit/backends/kicad/test_outline.py -k check tests/unit/lens/test_build_outline.py tests/unit/lens/test_altium_pcb.py tests/unit/lens/test_altium_issues.py tests/consistency`.
  - 2026-10-08: 451 passed, 17 skipped in 17.75s, exit 0 (the files were run whole, without `-k check`).
- [x] 4.3 Build the arcs and zone-box benches of task 1.2 from a script, the zone declared without an outline; the outcomes of task 1.2 MUST NOT change. Proof: `uv run pytest tests/kicad/board/test_outline_shapes.py -k arcs tests/kicad/zones/test_zone_box.py -rA` on 10.0.6, and the first file inside the 9.0.9 image.
  - 2026-10-08, open. Done on local `kicad-cli` 10.0.6: 5 passed, 7 deselected in 6.29s, exit 0; the boards built from a script give the outcomes of task 1.2, the zone declared without an outline. KiCad 9.0.9 was not run: this run had no local 9.0.9 and did not use the pinned image, so the `kicad-9` job must record the probes of both majors in `docs/evidence/kicad/probes/9.0.9.json` (`FENOLITE_PROBES_WRITE=1`) before this task is ticked.
  - 2026-10-08: ticked by the second local run of 2026-10-08 in the pinned 9.0.9 image (`kicad/kicad:9.0.9@sha256:e638b79b…`, linux/amd64, branch `v04-k9-probes-2`; whole `tests/kicad` without the corpus: 998 passed, 2 failed, 806 skipped, 1 xfailed; `tests/kicad/test_probe_results.py` passed on the 723 probes of major 9): the `arcs` tests of `tests/kicad/board/test_outline_shapes.py` pass on 9.0.9 for the boards built from a script (`test_arcs_drc`, `test_arcs_drill` and `test_arcs_rings_read_back` pass, `outline-arcs-drc` and `outline-arcs-drill` `absent`; `test_arcs_keep` needs `kicad-cli` 10 and skips); `tests/kicad/zones/test_zone_box.py` is 10.0 only and skips.

## 5. Holes

- [x] 5.1 Accept unnumbered `np_thru_hole` pads in `dsl/footprint.py`, with their ids, no pin and no `build.pad-without-pin` (scenarios of "Unnumbered hole pads in authored footprints"). Proof: `uv run pytest tests/unit/dsl/test_footprint_holes.py tests/unit/dsl tests/unit/lens -k pad_without_pin`.
  - 2026-10-08: 5 passed in 1.01s, exit 0; `tests/unit/dsl`: 524 passed in 8.31s, exit 0.
- [x] 5.2 Write `src/fenolite/dsl/holes.py` and `Design.hole()` and register the definitions (scenarios of "Board holes in the DSL"). If c0096 is on `dev`, remove its `Design.hole(key, …)`, `Design.holes`, the `KEYS` row `hole`, the lowering of script holes into `Board.holes` and the `FEN-3004` refusal of script holes in the KiCad build, with their tests (design, "Relation to c0096"); `Hole.intent`, `Board.holes` and `MechanicalIntent` stay. In the Altium build, hand hole parts to the document as board holes: a round hole that is not plated is written, a slot and a plated hole are reported (scenarios "A round hole becomes a free pad" and "A plated hole and a slot are reported" of "PCB document output"). Proof: `uv run pytest tests/unit/dsl/test_holes.py tests/unit/dsl tests/unit/lens/test_altium_pcb.py tests/unit/lens/test_altium_pcb_complete.py tests/unit/lens/test_altium_issues.py`; every committed Altium sample keeps its bytes (`uv run pytest tests/unit/lens/test_altium_pcb_golden.py tests/unit/lens/test_altium_copper_golden.py`); `uv run pyright src`.
  - 2026-10-08: 665 passed in 11.15s, exit 0 (the Altium golden tests among them: every committed Altium sample keeps its bytes); `pyright src`: 0 errors, exit 0. c0096 is not on this base: nothing was removed.
- [x] 5.3 Write `tests/unit/lens/test_build_holes.py` (scenarios of "Board holes in a build", with "A hole in the placements file" in `tests/unit/cli/test_sync_cmd.py`), and build the hole and symbol benches of task 1.3 from a script with `design.hole()`; the outcomes of task 1.3 MUST NOT change. Proof: `uv run pytest tests/unit/lens/test_build_holes.py tests/unit/cli/test_sync_cmd.py`; `uv run pytest tests/kicad/board/test_holes.py -rA` on 10.0.6 and inside the 9.0.9 image.
  - 2026-10-08, open. Unit half done: 29 passed in 11.61s, exit 0. Oracle on local `kicad-cli` 10.0.6: 9 passed in 8.29s, exit 0; the holes of `design.hole()` give the outcomes of task 1.3. KiCad 9.0.9 was not run: this run had no local 9.0.9 and did not use the pinned image, so the `kicad-9` job must record the probes of both majors in `docs/evidence/kicad/probes/9.0.9.json` (`FENOLITE_PROBES_WRITE=1`) before this task is ticked.
  - 2026-10-08: ticked by the second local run of 2026-10-08 in the pinned 9.0.9 image (`kicad/kicad:9.0.9@sha256:e638b79b…`, linux/amd64, branch `v04-k9-probes-2`; whole `tests/kicad` without the corpus: 998 passed, 2 failed, 806 skipped, 1 xfailed; `tests/kicad/test_probe_results.py` passed on the 723 probes of major 9): `tests/kicad/board/test_holes.py` 9 passed with the holes of `design.hole()`; the outcomes of task 1.3 are unchanged on 9.0.9.

## 6. Outline changes across rebuilds

- [x] 6.1 Write `merge_outline`, `OutlineMerge` and `MERGE_ISSUE_CODES` in `outline.py`: the signature, the five cases, re-signing and the lock, on token-edited boards (unit half of the scenarios of "Outline changes across rebuilds"). Proof: `uv run pytest tests/unit/backends/kicad/test_outline_merge.py`.
  - 2026-10-08: 11 passed in 4.58s, exit 0.
- [x] 6.2 Drop the copper that does not fit, let zones without an outline follow, leave the edge items of footprints alone and name their footprints in the message, and adapt the board in `merge_layout` (scenarios of "Outline changes across rebuilds", "Edge items of a footprint stay" among them, and of "Board content outside the design is kept"). Proof: `uv run pytest tests/unit/lens/test_preserve_outline.py tests/unit/lens tests/consistency`.
  - 2026-10-08: 9 passed in 4.19s, exit 0; `tests/unit/lens`: 1042 passed, 1 skipped in 112.76s (0:01:52), exit 0; `tests/consistency` in the run of task 4.2: 451 passed, 17 skipped in 17.75s, exit 0.
- [x] 6.3 Add the probes `outline-arcs-keep` and `rebuild-outline` (scenario "A re-save keeps the signature"). Proof: `uv run pytest tests/kicad/board/test_outline_shapes.py -k keep tests/kicad/lens/test_outline_rebuild.py -rA` on 10.0.6.
  - 2026-10-08, local `kicad-cli` 10.0.6: 2 passed, 10 deselected in 4.43s, exit 0; `outline-arcs-keep` `equal`, `rebuild-outline` `absent`.

## 7. Copper layer changes across rebuilds

- [x] 7.1 Write `merge_layers`, `LayerMerge` and `MERGE_ISSUE_CODES` in `layers.py`: rows, items on removed layers, re-projected pads and the stack-up (unit half of the scenarios of "Copper layer changes across rebuilds"). Proof: `uv run pytest tests/unit/backends/kicad/test_layers_merge.py`; `uv run pyright src`.
  - 2026-10-08: 9 passed in 2.68s, exit 0; `pyright src`: 0 errors, exit 0.
- [x] 7.2 Adapt the board in `merge_layout` before the outline, narrow `layout.copper-mismatch`, and add the probe `rebuild-layers` (scenarios of "Copper layer changes across rebuilds" and "Copper count changed in the script"). Proof: `uv run pytest tests/unit/lens/test_preserve_layers.py tests/unit/lens tests/consistency`; `uv run pytest tests/kicad/lens/test_layer_change.py -k rebuild -rA` on 10.0.6.
  - 2026-10-08: 48 passed in 22.65s, exit 0; local `kicad-cli` 10.0.6: 1 passed, 3 deselected in 4.91s, exit 0; `rebuild-layers` `absent`.
- [x] 7.3 With c0101 on the branch, a complete stack-up is read into `Board.stackup`: when `merge_layers` removes a stale `stackup` child it MUST also set `Board.stackup` to `None` (scenario "A read stack-up goes with the layers it names"). Proof: `uv run pytest tests/unit/backends/kicad/test_layers_merge.py tests/unit/lens/test_preserve_layers.py`.
  - 2026-10-08, when the change was carried onto `v04`. Measured before the fix: the rebuild of a four-layer board with a complete stack-up as two layers wrote no file and gave `model.stackup-copper` (error) after `kicad.layers.stackup-reset`, and `write_board` of the merged board raised `LossyWriteError`. After it: 18 passed in 5.57s, exit 0.

## 8. Documentation

- [x] 8.1 Update `docs/dsl.md` ("Board": paths, `shape`, `cutout`, `locked`; "Holes": `hole()`, its library and names, plated holes, the lock, the placements file; "Zones": the box of the board ring), `docs/lens.md` (outline and copper count changes, signed edges, dropped copper, footprint edge items, the stack-up reset), `docs/altium.md` (an outline with arcs plans no document; round holes are written, slots and plated holes reported; no courtyard), `docs/design-model.md` (`Outline.arcs`, with the sentence "Release 0.2.x cannot read a model document that carries `arcs`: its reader refuses an unknown key"), `docs/formats/kicad/board.md` (the arc orientation and the edge uuids) and `docs/cli-contract.md` (the `kicad.outline.*` and `kicad.layers.*` codes). Proof: `grep -n "0.2.x cannot read" docs/design-model.md` prints the sentence; `uv run pytest tests/consistency tests/unit/test_repo_layout.py tests/residue tests/unit/test_format_facts.py`.
  - 2026-10-08: `grep -n "0.2.x cannot read" docs/design-model.md` prints the sentence (line 209); 350 passed, 17 skipped in 80.86s (0:01:20), exit 0.
- [x] 8.2 If c0080 is archived, add one tested line each for `board(outline=…)`, `shape`, `cutout` and `hole` to its guide page; otherwise write "c0080 not archived" under this task. Proof: `uv run pytest tests/consistency` and the guide test that c0080 names.
  - 2026-10-08: c0080 not archived (0 of 15 tasks on this base); no guide line was written.
- [x] 8.3 Add an entry to `src/fenolite/cli/data/explain.toml` for each of the eight new codes (`kicad.outline.invalid`, `kicad.outline.zone-short`, `kicad.outline.replaced`, `kicad.outline.forced`, `kicad.outline.copper-dropped`, `kicad.layers.added`, `kicad.layers.removed`, `kicad.layers.stackup-reset`), and change the `fix` texts of `layout.outline-kept` (it names `board(..., locked=True)`) and of `layout.copper-mismatch` (a count change of Fenolite's own tables is now applied). Proof: `uv run pytest tests/unit/cli/test_explain_cmd.py tests/consistency`.
  - 2026-10-08: 350 passed, 17 skipped in 80.86s (0:01:20), exit 0 (`tests/unit/cli/test_explain_cmd.py` and `tests/consistency` in that run).

## 9. Closing

- [x] 9.1 Run the residue and the test suites. Proof: `uv run pytest tests/residue` and `uv run python tools/residue/scan.py` exit 0; `uv run python tools/gen_schemas.py --check` exits 0; `make check-fast` passes; the whole unit suite passes on Python 3.11, `uv run --isolated --python 3.11 --extra dev pytest tests/unit -q -n 6 -p no:cacheprovider`; `openspec validate c0102-board-outline-shapes --strict --no-interactive` passes. This change adds no file under `tests/data`; if one is added after all, declare it in `tests/data/MANIFEST.toml` and run `uv run pytest tests/corpus/test_manifest.py`. The full `make check` and `gh pr checks` (`unit`, `kicad-9`, `kicad-10`) are the coordinator's run at the merge, not this task's.
  - 2026-10-08: `pytest tests/corpus/test_manifest.py tests/residue`: 85 passed, exit 0; `tools/residue/scan.py`: 0 hits in 2842 files, exit 0; `gen_schemas.py --check`: exit 0; `make check-fast PYTEST_WORKERS=3`: 10233 passed, 23 skipped, exit 0; the unit suite on Python 3.11.13 (`uv run --offline --isolated --python 3.11 --extra dev pytest tests/unit -q -n 6 -p no:cacheprovider`): 9938 passed, 6 skipped, exit 0; `openspec validate c0102-board-outline-shapes --strict --no-interactive`: valid, exit 0. No file was added under `tests/data`; eight committed boards there took the signed edge uuids (four acceptance boards, two layer fixtures, the parity sample and the sync sample).
- [x] 9.2 Update the evidence labels: the eight rows become `KICAD-VERIFIED` with the scope of "Evidence level per behaviour", or record what was refuted and the part that stopped. Proof: `uv run pytest tests/unit/test_provenance.py tests/unit/test_hypotheses_register.py tests/kicad/test_probe_results.py`.
  - 2026-10-08, open. `H-K-ZONE-BOX` is `KICAD-VERIFIED (10.0.x)`, its whole scope. The other seven rows stay `INFERRED` with the outcomes of 10.0.6 in their result: their criterion names both majors, and 9.0.9 was not run by this change. Nothing was refuted. Register tests after the edit: 174 passed (`test_provenance.py`, `test_hypotheses_register.py`, `test_format_facts.py`, the matrix page, `tests/unit/verify`), exit 0; `tests/kicad/test_probe_results.py` was not run: it runs every probe of the major, and only the 24 keys of this change were recorded.
  - 2026-10-08: after the image run named under task 1.3, `H-K-OUTLINE-ARCS`, `H-K-OUTLINE-OUTSIDE`, `H-K-HOLE-FOOTPRINT`, `H-K-HOLE-COURTYARD`, `H-K-HOLE-SYMBOL` and `H-K-LAYER-CHANGE` are `KICAD-VERIFIED (9.0.x, 10.0.x)`; `H-K-OUTLINE-INVALID` stays `INFERRED` with what 9.0.9 showed (`outline-invalid-selfx` `absent`). Still open: the code-side evidence constants and the labels of the fact rows of `docs/formats/kicad/` were not raised by the commit that recorded the probes; CI has still to confirm the 9.0.9 half.
  - 2026-10-08: ticked. CI run 37772583226 confirms the 9.0.9 half (the `kicad-9` job passes `test_outline_shapes.py`, `test_holes.py`, `test_layer_change.py` and the probe check), so `H-K-OUTLINE-INVALID` is `KICAD-VERIFIED (9.0.x, 10.0.x)` too, with the statement as corrected (9.0.9 reports the overlapping cut-outs only). The eight rows are `KICAD-VERIFIED`, seven for both majors and `H-K-ZONE-BOX` for 10.0.x, its whole scope. The fact rows of `docs/formats/kicad/board.md` follow (the outline, outside, hole, courtyard, symbol and layer-change rows `KICAD-VERIFIED (9.0.x, 10.0.x)`; the row of `invalid_outline` states what 9.0.9 reports). No evidence constant of the code carries these hypotheses, so none changes. `uv run pytest tests/unit/test_provenance.py tests/unit/test_hypotheses_register.py tests/unit/test_format_facts.py` passes; `tests/kicad/test_probe_results.py` skips here without `kicad-cli` and passes in both `kicad-*` jobs of that run.
- [x] 9.3 Add to `CHANGELOG.md` under Unreleased: "A script can give the board an outline with arcs and cut-outs (`board(outline=…)`, `cutout()`, `fenolite.dsl.shape`) and holes (`design.hole()`); authored footprints accept unnumbered hole pads. A rebuild now follows a new outline or copper count: copper that no longer fits, or that lies on a removed layer, is dropped and reported, and a stale stack-up is removed. Outline edges carry new uuids from the first build after this change. With `--target altium` an outline with arcs plans no PCB document, a round hole that is not plated is written, and a slot or a plated hole is reported. **Release 0.2.x cannot read a model document that carries the new key `arcs`.**" If task 5.2 removed c0096's hole call, name `Design.hole(key, …)`, `Design.holes` and the key `hole:<key>` as removed. Update the entry of c0102 in `docs/roadmap.md` ("v0.4: proposals on other branches"). Proof: `grep -n "0.2.x cannot read" CHANGELOG.md` prints the line; `git diff --stat CHANGELOG.md docs/roadmap.md` lists both files.
  - 2026-10-08, open. The entry is the last one of `## [Unreleased]` in `CHANGELOG.md` (`grep -n "0.2.x cannot read" CHANGELOG.md` prints its line). `docs/roadmap.md` was not edited: the coordinator of the v0.4 wave updates the entry of c0102 when the branches are stacked. c0096 is not on this base, so no removed name is listed.
  - 2026-10-08, base `04ef42a`: ticked. The entry gains the evidence of the outline facts (and what 9.0.9 reports for `invalid_outline`), and the row of c0102 in `docs/roadmap.md` says that it ships in 0.4 and that c0100 is archived first. `grep -n "0.2.x cannot read" CHANGELOG.md` prints its line; `git diff --stat CHANGELOG.md docs/roadmap.md` lists both files.
