lgili/Fenolite/openspec/changes/c0103-dsl-keepouts-board-items/tasks.md

## 0. Entry check

- [x] 0.1 Read the living `design-dsl`, `design-model`, `kicad-file-backend`, `rules-model`, `copper-check`, `verification-loop`, `layout-lens`, `altium-build`, `altium-pcb-writer` and `kicad-oracle` specs and `openspec list`. Write under this task, with the date: whether release 0.3.0 is out with c0084, c0085, c0088 and c0126 archived; whether c0100, c0101 and c0102 are archived (they must be) and whether c0096, c0097, c0104 and c0080 are. Regenerate from the living text, re-applying this change's edits: "Modelled board content" on c0101's text; "Identifier derivation" when c0096 is on `dev` (its rows `hole` and `keepout` go, design "Relation to c0096"); "Closed selector grammar" when c0104 landed first; and any MODIFIED requirement that an archive changed since `9aba2dff`. If c0096 is on `dev`, list here the names of the table "Relation to c0096" that task 5.1 removes; if c0097 is, task 7.4 applies. Proof: `openspec validate c0103-dsl-keepouts-board-items --strict --no-interactive` passes after any regeneration.
  - 2026-10-08, on the base `15964cc3` (the integration branch of v0.4): release 0.3.0 is not out and none of c0084, c0085, c0088, c0126, c0100, c0101, c0102, c0096, c0097, c0104 and c0080 is archived (`openspec list` shows all of them open; the last archives are c0089, c0122, c0133 and c0135). The code of c0084, c0085, c0088, c0100 and c0101 is on the base; c0102 and c0126 are not implemented there (no `FootprintInstance.texts`, no `tests/data/model/v0.2.0/`), and c0096, c0097, c0104 and c0080 are on other branches. Regeneration: the four MODIFIED requirements were compared with the living text (`design-model` "Identifier derivation", `kicad-file-backend` "Modelled board content", `rules-model` "Closed selector grammar", `copper-check` "Clearance in force"): each delta is the living text plus this change's edits only, so nothing changed. "Modelled board content" stays on the living text, since c0101's sentence is not archived. c0096 is not on the base: task 5.1 removes nothing. Proof: `openspec validate c0103-dsl-keepouts-board-items --strict --no-interactive` exit 0 ("is valid").

## 1. Probe and register

- [x] 1.1 Add the rows `H-K-AREA-KEEPOUT`, `H-K-AREA-COND`, `H-K-AREA-NAME`, `H-K-BOARD-TEXT`, `H-K-DIM` and `H-K-COPPER-AREA` to `docs/hypotheses.md` (backend `kicad`, level `INFERRED`, the tests and criteria of `design.md`, result `pending` with the measurements of 2026-10-05 as the first record). Proof: `uv run pytest tests/unit/test_hypotheses_register.py tests/unit/test_provenance.py`; `grep -cE '^\| H-K-(AREA-KEEPOUT|AREA-COND|AREA-NAME|BOARD-TEXT|DIM|COPPER-AREA) ' docs/hypotheses.md` prints `6`.
  - 2026-10-08: six rows appended after the last row of the table; `uv run pytest tests/unit/test_hypotheses_register.py tests/unit/test_provenance.py` 44 passed, exit 0; the grep prints `6`.
- [x] 1.2 Port the keep-out and area benches of the probes into `tests/kicad/rules/_areacases.py`, add the case not yet run (two areas named `HV`, `area-cond-twin`), and write `tests/kicad/board/test_keepout_settings.py` and `tests/kicad/rules/test_area_rules.py` with the probes of "Rule areas and area conditions are probed". Until task 3.1 lands, the benches patch the area name into the written text. If an outcome differs from the design, stop and correct the design from the report before going on. Proof: `uv run pytest tests/kicad/board/test_keepout_settings.py tests/kicad/rules/test_area_rules.py -rA` on the local KiCad 10.0.6 and in the pinned 9.0.9 image; `FENOLITE_PROBES_WRITE=1` updates both probe files; `uv run pytest tests/kicad/test_probe_results.py`.
  - Open: the 9.0.9 half was not run (no pinned image was used on 2026-10-08). Done: the benches are in `tests/kicad/rules/_areacases.py` (the writer writes the name, so nothing is patched), with `area-cond-twin`; on the local `kicad-cli` 10.0.6, `uv run pytest tests/kicad/board/test_keepout_settings.py tests/kicad/rules/test_area_rules.py -rA` gave 21 passed, exit 0, every outcome as the design states. `tests/kicad/test_probe_results.py` fails on this base for another reason: the layer-table probes of `tests/kicad/board/_layertables.py` raise `LossyWriteError` (`model.stackup-copper`), as `tests/kicad/board/test_layer_tables.py` does on the clean base `15964cc3` (17 failed). The 29 new outcomes of 10.0.6 were merged into `docs/evidence/kicad/probes/10.0.6.json` by running only the new probes; `9.0.9.json` is unchanged, so the `kicad-9` job needs `FENOLITE_PROBES_WRITE=1` once.
  - 2026-10-08: ticked by the second local run of 2026-10-08 in the pinned 9.0.9 image (`kicad/kicad:9.0.9@sha256:e638b79b…`, linux/amd64, branch `v04-k9-probes-2`; whole `tests/kicad` without the corpus: 998 passed, 2 failed, 806 skipped, 1 xfailed; `tests/kicad/test_probe_results.py` passed on the 723 probes of major 9): `tests/kicad/board/test_keepout_settings.py` 7 passed, 2 skipped (the refill and the re-save of the name are 10.0 only) and `tests/kicad/rules/test_area_rules.py` 12 passed; the seven `area-keepout-*` rows, the ten `area-cond-*` rows and `dru-cond-area` are in `9.0.9.json` with the outcomes of 10.0.6, merged by name. `SELECTOR_SUPPORT["area"]` gained 9 in the same commit, as `test_support_matches_probe_results` asks of the probe files: a rule with an area leaf is now written for target 9.
- [x] 1.3 Check every name that a created dimension writes against the 8.0.0 keyword list (S-0033) and the token inventory; add the 8.0 names to `pcb.FLOOR_HEADS` and the others to the inventory with their first major, with the source. Proof: `uv run pytest tests/unit/backends/kicad/test_inventory.py tests/unit/backends/kicad/test_check_emittable.py`.
  - Open: the check against the 8.0.0 keyword list (S-0033) needs a fetch, which this run did not do. Done on 2026-10-08: `arrow_direction` and the list form of `keep_text_aligned` are rows of the inventory already (9.0); the fourteen other names of a dimension were added to `pcb.FLOOR_HEADS`, with a note that they are those of the demo boards of 9.0.9 and 10.0.6 (S-0058, 11 linear dimensions read from the cached corpus) and that their 8.0 check is open. `uv run pytest tests/unit/backends/kicad/test_inventory.py tests/unit/backends/kicad/test_check_emittable.py` 58 passed, exit 0.
  - 2026-10-08, base `04ef42a`: ticked, with the check made on KiCad-written files and the format page instead of S-0033: S-0033 is a keyword list in KiCad's source tree, and since 2026-10-08 no third-party source code is cited as a format fact. The demo boards of tag 8.0.0 were fetched (`gitlab.com/kicad/code/kicad/-/raw/8.0.0/demos/…`, CC-BY-SA-4.0 by the `LICENSE.README` of that tag) and read for facts only: two of them are in the 8.0 format `20240108` and hold dimensions (`sonde xilinx.kicad_pcb`, one, and `video.kicad_pcb`, two, all `aligned`), and their children hold thirteen of the fourteen names (`dimension`, `height`, `format`, `prefix`, `suffix`, `units`, `units_format`, `precision`, `style`, `arrow_length`, `text_position_mode`, `extension_height`, `extension_offset`); registered as S-0723. `orientation`, the child of an orthogonal dimension, is in no 8.0.0 demo board; the format page S-0001 documents it and dates only `radial` dimensions to version 7 and later, so it stays in `pcb.FLOOR_HEADS` with S-0001 as its source (`INFERRED`). `arrow_direction` and the list form of `keep_text_aligned` stay inventory rows of 9.0. The docstring of `pcb.FLOOR_HEADS`, the "Names" and "Floor names" notes of `docs/formats/kicad/board.md` and two fact rows (S-0723 and S-0001, `INFERRED`, `H-K-PCB-WRITE`) say so, and S-0001's "used for" cell is widened. `uv run pytest tests/unit/backends/kicad/test_inventory.py tests/unit/backends/kicad/test_check_emittable.py tests/unit/test_format_facts.py tests/unit/test_provenance.py -q`: 88 passed, exit 0.

## 2. Model

- [x] 2.1 Add `Keepout.name`, `Text.h_justify`, `Text.v_justify`, `Dimension` with `DimensionKind`, `DimensionDirection` and `DimensionUnits`, `Board.dimensions` and the prefix `dim`, and regenerate `board.json` (scenarios of "Rule areas, board items and the area selector in the model", with "A document of 0.2.0 still loads" on c0126's fixture `tests/data/model/v0.2.0/blink_2layer.board.json`). Check that the texts of footprint instances (c0126) keep their bytes with the two new defaults. Proof: `uv run pytest tests/unit/model tests/unit/test_schema_drift.py`; `uv run python tools/gen_schemas.py --check` exits 0.
  - 2026-10-08: `uv run pytest tests/unit/model tests/unit/test_schema_drift.py` 236 passed, 2 skipped, exit 0; `uv run python tools/gen_schemas.py --check` exit 0 (both schemas regenerated with the tool). The fixture of c0126 (`tests/data/model/v0.2.0/`) and the texts of footprint instances are not on this base: `-k v020_board_items` runs on `tests/data/model/v0.2.1/blink_2layer.board.json` (passed) and skips the 0.2.0 file until c0126 lands.
- [x] 2.2 Add `area` to `SelectorOp` and `LEAF_OPS`, `RuleSubject.areas` and the `area` case of `Selector.matches`, and regenerate `rules.json` (scenario "Area selector against a subject"). Proof: `uv run pytest tests/unit/model -k "selector or rule"`; `uv run python tools/gen_schemas.py --check` exits 0; `uv run pyright src`.
  - 2026-10-08: `uv run pytest tests/unit/model -k "selector or rule"` 15 passed, exit 0; `tools/gen_schemas.py --check` exit 0; `uv run pyright src` 0 errors.

## 3. KiCad reader and writer

- [x] 3.1 Read and write the rule-area name (`KEEPOUT_FIELDS`, `_emit_zone`) and the text justification (the reader's projection of `effects`, the writer's `justify`) (scenarios "Named rule area", "Justified text" of both requirements and "Created rule area with a name"). Proof: `uv run pytest tests/unit/backends/kicad/test_pcb_items.py tests/unit/backends/kicad/test_pcb_write.py tests/unit/backends/kicad/test_pcb_rebuild.py`.
  - 2026-10-08: `uv run pytest tests/unit/backends/kicad/test_pcb_items.py tests/unit/backends/kicad/test_pcb_write.py tests/unit/backends/kicad/test_pcb_rebuild.py` 85 passed, exit 0.
- [x] 3.2 Read `dimension` nodes of type `aligned` and `orthogonal` into `Dimension` with projected `format`, `style` and `gr_text` slots and no duplicate-uuid warning; write created dimensions with the cache value; place `dimension` in `CANONICAL_ORDER` (scenarios of the dimensions in "Modelled board content" and "Board items of a script are written"). Proof: `uv run pytest tests/unit/backends/kicad/test_pcb_items.py tests/unit/backends/kicad/test_pcb_write.py -k dimension`; `FENOLITE_CENSUS_OUT=<file> uv run pytest tests/corpus/test_board_census.py -rA` with the corpus cached records how many demo dimensions are modelled and how many stay opaque.
  - 2026-10-08: `-k dimension` 12 passed, exit 0. Census with the cached corpus (`FENOLITE_CENSUS_OUT=<file> uv run pytest tests/corpus/test_board_census.py -rA`, 12 passed, exit 0; a test `test_board_items` was added): 11 dimensions of the demo boards of 10.0.6 are modelled (2, 1, 6 and 2 in four boards) and no root dimension stays opaque; 8 rule areas carry a name and 401 board texts a justification. `tests/corpus/test_board_rt1.py`, `test_board_read.py`, `test_board_fields.py` and `test_fmt_idempotent.py`: 76 passed, 4 skipped, exit 0.
- [x] 3.3 Write `src/fenolite/backends/kicad/boarditems.py` (`ITEM_MARKER`, `item_uuid`, `is_item_uuid`, `mark_items`, `ItemMerge`, `merge_items`, `unknown_areas`, `MERGE_ISSUE_CODES`, `EVIDENCE`) and `tests/unit/backends/kicad/test_boarditems.py` (scenarios "Item uuids are marked" and "Board item merge codes are closed"). Proof: `uv run pytest tests/unit/backends/kicad/test_boarditems.py tests/unit/test_import_graph.py`; `uv run pyright src`.
  - 2026-10-08: `uv run pytest tests/unit/backends/kicad/test_boarditems.py tests/unit/test_import_graph.py` 38 passed, exit 0; `uv run pyright src` 0 errors. The module also exports `script_items`, which `merge_layout` uses.

## 4. Rules

- [x] 4.1 Add `area` to `rulemap`: the writer in `_term`, the lift of `intersectsArea` in `_Parse`, the leaves of the nine kinds in `KIND_SELECTORS`, `SELECTOR_KEYS`, and `SELECTOR_SUPPORT` pinned to `dru-cond-area` (scenarios of "Closed selector grammar"). Proof: `uv run pytest tests/unit/backends/kicad/test_rulemap.py tests/unit/backends/kicad/test_rulemap_kinds.py tests/unit/backends/kicad/test_dru.py tests/unit/backends/kicad/test_lowering.py tests/unit/backends/kicad/test_copperrules.py`.
  - 2026-10-08: the five files 219 passed, exit 0. `SELECTOR_SUPPORT["area"]` is `{10}`: `dru-cond-area` is recorded `present` for 10.0.6 only, so a rule with an area leaf is refused for target 9 until the probe is recorded for 9.0.9 (task 1.2).

## 5. DSL

- [x] 5.1 Write `src/fenolite/dsl/items.py`, `Design.rule_area`, `Design.rule_areas`, the re-export of `RuleArea` and the keep-outs of `to_model` (scenarios of "Rule areas in the DSL"). If c0096 is on `dev`, remove its `Design.keepout(key, …)`, `Design.keepouts`, the `KEYS` row `keepout` and its rule that board areas win on a rebuild, with their tests, and point its checker adapter at `copper.keepout` once task 7.2 is done (design, "Relation to c0096"); `Keepout.intent` and `MechanicalIntent` stay. Proof: `uv run pytest tests/unit/dsl/test_rule_areas.py tests/unit/dsl tests/unit/test_import_graph.py`; `uv run pyright src`.
  - 2026-10-08: `uv run pytest tests/unit/dsl/test_rule_areas.py tests/unit/dsl tests/unit/test_import_graph.py` 525 passed, exit 0; `uv run pyright src` 0 errors. c0096 is not on this base: nothing was removed.
- [x] 5.2 Add `Design.text`, `line`, `rect`, `circle`, `arc`, `polygon` and `dimension`, `Design.drawings`, their entities in `to_model`, and the `KEYS` rows (scenarios of "Board drawings in the DSL" and "Area and drawing ids from names and keys"). Proof: `uv run pytest tests/unit/dsl/test_drawings.py tests/unit/dsl/test_ids.py tests/unit/dsl/test_to_model.py`.
  - 2026-10-08: `uv run pytest tests/unit/dsl/test_drawings.py tests/unit/dsl/test_ids.py tests/unit/dsl/test_to_model.py` 17 passed, exit 0. The DSL holds the non-copper layers of a created board with their kinds (`dsl.items.BOARD_LAYER_KINDS`); a test keeps it equal to the backend's table.
- [x] 5.3 Add `select.area` (scenarios of "Area selectors in the DSL"). Proof: `uv run pytest tests/unit/dsl/test_select.py tests/unit/dsl/test_rule_constructor.py`.
  - 2026-10-08: `uv run pytest tests/unit/dsl/test_select.py tests/unit/dsl/test_rule_constructor.py` 44 passed, exit 0.

## 6. Build and lens

- [x] 6.1 Call `mark_items` in `build_design`, check area leaves after the merge (`build.area-unknown`), and add `result.board_items` to the reply of `cmd_build` (scenarios of "Board items in a build"). Proof: `uv run pytest tests/unit/lens/test_build_board_items.py tests/unit/lens/test_build_issues.py tests/unit/lens/test_build_determinism.py`.
  - 2026-10-08: `uv run pytest tests/unit/lens/test_build_board_items.py tests/unit/lens/test_build_issues.py tests/unit/lens/test_build_determinism.py` 26 passed, exit 0.
- [x] 6.2 Call `merge_items` in `merge_layout` and report `result.preserved.board_items` (scenarios of "Board items declared in the script"). Proof: `uv run pytest tests/unit/lens/test_preserve_board.py tests/unit/lens/test_build_preserve.py tests/unit/lens/test_build_board_items.py -k rebuild`.
  - 2026-10-08: the proof command 4 passed, exit 0 (the four rebuild scenarios); the merge-level tests of `tests/unit/lens/test_preserve_board.py` run with the whole file (10 passed with `test_build_preserve.py`).
- [x] 6.3 Apply "Rule areas, board items and area rules in an Altium build": add `dimension` to `lens.altium_copper.KINDS` and the row `dimensions` to `BOARD_KINDS`; in `lower_items` report each dimension, the name of each named keep-out and each text that is not centred; pin with a test that `backends.altium.rulemap.lower` gives `scope-unsupported` for a rule with an `area` leaf and that the build reports it; pin that `copper.keepout` is a warning in the copper guard of an Altium build. Describe the rules in `docs/altium.md`. Proof: `uv run pytest tests/unit/lens/test_altium_issues.py tests/unit/lens/test_altium_build.py tests/unit/lens/test_altium_pcb_complete.py tests/unit/lens/test_altium_rules.py tests/unit/cli/test_build_altium_guard.py`; every committed Altium sample keeps its bytes (`uv run pytest tests/unit/lens/test_altium_pcb_golden.py tests/unit/lens/test_altium_copper_golden.py`).
  - 2026-10-08: the five files and `tests/unit/lens/test_altium_board_items.py` 158 passed, exit 0; the two golden files 12 passed, exit 0 (every committed sample keeps its bytes). `backends.altium.lower.KINDS` gained `dimension` too, because a test keeps it equal to `lens.altium_copper.KINDS`; the model write counts a justified text and a dimension as not written. The Altium reader models no keep-out, so the guard of an Altium build cannot find `copper.keepout` in a document it reads back: the test gives the guard such a finding and pins that it becomes a warning.

## 7. Copper check

- [x] 7.1 Add `areas` to `ClearanceResolver.subject`, compare `area` leaves with letter case, and compute area membership in `check_copper`, with `rule-area` in `summary.unsupported` (scenarios of "Clearance in force" and "Rule areas in the copper check"). Proof: `uv run pytest tests/unit/checks/test_clearance.py tests/unit/checks/test_copper.py -k "area or brute_force"`.
  - 2026-10-08: `uv run pytest tests/unit/checks/test_clearance.py tests/unit/checks/test_copper.py -k "area or brute_force"` 14 passed, exit 0.
- [x] 7.2 Report `copper.keepout`, add `keepout` to `CopperKind` and the key to `checks.codes.ISSUE_CODES` (scenarios of "Keep-out findings" and "Keep-out issue code"). Proof: `uv run pytest tests/unit/checks -k "keepout or codes"`; `uv run pytest tests/unit/lens/test_build_board_items.py -k guard`.
  - 2026-10-08: `uv run pytest tests/unit/checks -k "keepout or codes"` 31 passed, exit 0; `uv run pytest tests/unit/lens/test_build_board_items.py -k guard` 3 passed, exit 0.
- [x] 7.3 Add the keep-out and area benches to `tests/kicad/copper/_copperparity.py`, the hermetic half to `test_parity_bench.py`, and the probes `copper-keepout-parity` and `copper-area-parity` (scenarios of "Keep-outs and area rules agree with the copper check"). Proof: `uv run pytest tests/kicad/copper/test_parity_bench.py -k "keepout or area"` without `kicad-cli`; `uv run pytest tests/kicad/copper/test_copper_parity.py -k "keepout or area" -rA` on the local KiCad 10.0.6 and in the pinned 9.0.9 image.
  - Open: the 9.0.9 half was not run. Done on 2026-10-08: the benches are in `tests/kicad/rules/_areacases.py` (`_copperparity.py` is not touched: its rows compare gaps, these compare sets of items); `uv run pytest tests/kicad/copper/test_parity_bench.py -k "keepout or area"` 4 passed, exit 0, without `kicad-cli`; on 10.0.6 `tests/kicad/copper/test_copper_parity.py -k "keepout or area"` 2 passed, exit 0, both probes `equal`.
  - 2026-10-08: ticked by the second local run of 2026-10-08 in the pinned 9.0.9 image (`kicad/kicad:9.0.9@sha256:e638b79b…`, linux/amd64, branch `v04-k9-probes-2`; whole `tests/kicad` without the corpus: 998 passed, 2 failed, 806 skipped, 1 xfailed; `tests/kicad/test_probe_results.py` passed on the 723 probes of major 9): `copper-keepout-parity` and `copper-area-parity` = `equal` on 9.0.9, recorded in `9.0.9.json`; `tests/kicad/copper/test_copper_parity.py` 30 passed, 2 skipped.
- [x] 7.4 Only if c0097 is on `dev`: give its explanation the area leaf (the subject shows `areas`; a candidate row prints `area <name>`), give a `copper.keepout` finding an explanation without candidate rows that names the keep-out, the setting and the layer, and put the finding in c0097's grouping by its item (a pad `inter-component`; a track, arc or via `routed`), as the design states under "Relation to c0097". Otherwise write "c0097 not on dev" under this task. Proof: the unit tests of c0097's explanation module pass with the new cases (`uv run pytest tests/unit/checks -k "explain or keepout or area"`), or the note is present.
  - 2026-10-08: c0097 not on dev (nor on this base).

## 8. Oracle and documentation

- [x] 8.1 Write `tests/kicad/board/test_board_items_oracle.py` (scenarios of "Board texts and dimensions are probed"), and build the blink variant with a keep-out, a label and a dimension through DRC on both majors (scenario "Blink with a keep-out, a label and a dimension", and "Check fails on copper in a keep-out"). Proof: `uv run pytest tests/kicad/board/test_board_items_oracle.py tests/kicad/build -k board_items -rA` on the local KiCad 10.0.6 and in the pinned 9.0.9 image; both probe files updated.
  - Open: the 9.0.9 half was not run. Done on 2026-10-08 with `kicad-cli` 10.0.6: `tests/kicad/board/test_board_items_oracle.py` 7 passed and `tests/kicad/build/test_board_items_build.py` 3 passed, exit 0 (the variant built for targets 9 and 10 loads and its DRC holds no error; `check` exits 5 with `copper.keepout` and `kicad.drc.items-not-allowed` for the same track). KiCad warns with `silk_edge_clearance` for the centred label at (2 mm, 2 mm) of the scenario, which reaches the board edge.
  - 2026-10-08: ticked by the second local run of 2026-10-08 in the pinned 9.0.9 image (`kicad/kicad:9.0.9@sha256:e638b79b…`, linux/amd64, branch `v04-k9-probes-2`; whole `tests/kicad` without the corpus: 998 passed, 2 failed, 806 skipped, 1 xfailed; `tests/kicad/test_probe_results.py` passed on the 723 probes of major 9): `tests/kicad/board/test_board_items_oracle.py` 6 passed, 1 skipped (the re-save is 10.0 only) and `tests/kicad/build/test_board_items_build.py` 2 passed, 1 skipped (the target-9 blink builds clean; the target-10 one needs `kicad-cli` 10); `text-board-load` `absent`, `text-height` and `text-copper-short` `present`, `graphic-copper-silent` `absent`, `dim-load` `present` and `dim-recompute` `equal` are in `9.0.9.json`.
- [x] 8.2 Update `docs/dsl.md` ("Rule areas", "Board drawings", and `select.area` under "Design rules"), `docs/lens.md` (script board items are regenerated), `docs/altium.md` (what an Altium build writes and what it reports of rule areas, texts, dimensions and area rules), `docs/cli-contract.md` (`copper.keepout`, `build.area-unknown`, `kicad.board-item.*`, `result.board_items`, `result.preserved.board_items`), `docs/design-model.md` (`Dimension`, `Keepout.name`, `area`, with the sentence "Release 0.2.x cannot read a model document that carries one of the new keys"), `docs/formats/kicad/board.md` (fact rows: the area name, the children a re-save adds, dimension children and recomputation, text justification), `rules.md` (the `area` row and its facts), `drc.md` (`items_not_allowed` per setting) and `copper.md` (supported cases for area rules and keep-outs). If c0080 is archived, add one tested line for `rule_area` and `select.area` to its guide page. Proof: `grep -n "0.2.x cannot read" docs/design-model.md` prints the sentence; `uv run pytest tests/consistency tests/unit/test_format_facts.py tests/unit/test_repo_layout.py tests/residue`.
  - 2026-10-08: the grep prints the sentence (line 318); `uv run pytest tests/consistency tests/unit/test_format_facts.py tests/unit/test_repo_layout.py tests/residue` 366 passed, 19 skipped, exit 0. The fact rows are `INFERRED` and say that they are recorded for 10.0.6. c0080 is not archived.
- [x] 8.3 Add an entry to `src/fenolite/cli/data/explain.toml` for each of the four new codes (`copper.keepout`, `build.area-unknown`, `kicad.board-item.regenerated`, `kicad.board-item.stale`). Proof: `uv run pytest tests/unit/cli/test_explain_cmd.py tests/consistency`.
  - 2026-10-08: `uv run pytest tests/unit/cli/test_explain_cmd.py tests/consistency` 301 passed, 19 skipped, exit 0; `explain.TABLES` names `boarditems.MERGE_ISSUE_CODES`.

## 9. Closing

- [x] 9.1 Run the residue and the test suites. Proof: `uv run pytest tests/residue` and `uv run python tools/residue/scan.py` exit 0; `uv run python tools/gen_schemas.py --check` exits 0; `make check-fast` passes; the whole unit suite passes on Python 3.11, `uv run --isolated --python 3.11 --extra dev pytest tests/unit -q -n 6 -p no:cacheprovider`; `openspec validate c0103-dsl-keepouts-board-items --strict --no-interactive` passes. This change adds no file under `tests/data`; if one is added after all, declare it in `tests/data/MANIFEST.toml` and run `uv run pytest tests/corpus/test_manifest.py`. The full `make check` and `gh pr checks` (`unit`, `kicad-9`, `kicad-10`) are the coordinator's run at the merge, not this task's.
  - Open: no Python 3.11 is installed on this machine and getting one is a download, so the 3.11 unit run was not made. Done on 2026-10-08: `uv run pytest tests/residue` and `tools/residue/scan.py` exit 0; `tools/gen_schemas.py --check` exit 0; `openspec validate --all --strict --no-interactive` 101 passed; `make check-fast PYTEST_WORKERS=3`: see the commit's report (the four tests about `examples/yardstick` and `tools/yardstick.py` fail on the base `15964cc3` too). No file was added under `tests/data`.
  - 2026-10-08, branch `v04-close-a` on `04ef42a`, with every edit of the closing pass of c0077 to c0103 in the tree (the gate of the release, run once for all of them): `make check-fast PYTEST_WORKERS=4` exits 0 (ruff check, the guide's `--check`, ruff format, pyright, the residue scan, and 12731 passed, 29 skipped); the whole unit suite on Python 3.11.15, `uv run --isolated --python 3.11 --extra dev pytest tests/unit -q -n 4 -p no:cacheprovider`: 12348 passed, 25 skipped, exit 0; after `git add -A`, `uv run pytest tests/residue tests/corpus/test_manifest.py -q`: 80 passed, 5 skipped (no `kicad-cli`, no KiCad libraries), exit 0; `uv run python tools/residue/scan.py`: 0 hits, exit 0; `openspec validate --all --strict --no-interactive` reports the same six errors as on `04ef42a` (c0084, c0085 twice, c0086, c0108, c0128) and none of this change, besides the long-requirement warnings. The full `make check` is the coordinator's. `uv run python tools/gen_schemas.py --check` exits 0; no file was added under `tests/data`.
- [x] 9.2 Update the evidence labels: the six new rows become `KICAD-VERIFIED` with their scope per major (`H-K-AREA-NAME` for 10.0.x on the re-save), or record what was refuted and the fallback taken; `checks.copper.EVIDENCE` and `boarditems.EVIDENCE` gain the hypothesis ids and stay `INFERRED`. Proof: `uv run pytest tests/unit/test_provenance.py tests/unit/test_hypotheses_register.py tests/kicad/test_probe_results.py`.
  - Open: the rows stay `INFERRED` until the probes are recorded for 9.0.9. Done on 2026-10-08: each of the six rows records the 10.0.6 outcomes; `boarditems.EVIDENCE` names four of the rows and `checks.copper.AREA_EVIDENCE` (`H-K-COPPER-AREA`, `H-K-AREA-KEEPOUT`) joins the report of a board that holds a rule area; both are `INFERRED`. `uv run pytest tests/unit/test_provenance.py tests/unit/test_hypotheses_register.py` 44 passed, exit 0.
  - 2026-10-08: after the image run named under task 1.2, the six rows `H-K-AREA-KEEPOUT`, `H-K-AREA-COND`, `H-K-AREA-NAME`, `H-K-BOARD-TEXT`, `H-K-DIM` and `H-K-COPPER-AREA` are `KICAD-VERIFIED (9.0.x, 10.0.x)`. Still open: the code-side evidence constants and the labels of the fact rows of `docs/formats/kicad/` were not raised by the commit that recorded the probes; CI has still to confirm the 9.0.9 half. (`boarditems.EVIDENCE` and `checks.copper.AREA_EVIDENCE` are `INFERRED`.)
  - 2026-10-08: ticked. CI run 37772583226 on `04ef42a` confirms the 9.0.9 half: its `kicad-9` job passes `test_keepout_settings.py`, `test_area_rules.py`, `test_board_items_oracle.py`, `test_board_items_build.py`, the keep-out and area cases of `test_copper_parity.py`, and `tests/kicad/test_probe_results.py`. The six rows are `KICAD-VERIFIED (9.0.x, 10.0.x)` (the re-save of `H-K-AREA-NAME` on 10.0.x), and `boarditems.EVIDENCE` and `checks.copper.AREA_EVIDENCE` hold the hypothesis ids and stay `INFERRED`, as the task says. The fact rows that cite them follow: `docs/formats/kicad/board.md` (area name, texts, dimensions), `copper.md` (`H-K-COPPER-AREA`), `drc.md` (`H-K-AREA-KEEPOUT`) and `rules.md` (`H-K-AREA-COND`) are `KICAD-VERIFIED (9.0.x, 10.0.x)` and say "recorded for 9.0.9 and 10.0.6", the re-saves and the refill 10.0.6 only. `uv run pytest tests/unit/test_provenance.py tests/unit/test_hypotheses_register.py tests/unit/test_format_facts.py` passes; `tests/kicad/test_probe_results.py` skips here without `kicad-cli` and passes in both `kicad-*` jobs of that run.
- [x] 9.3 Add to `CHANGELOG.md` under Unreleased: "Rule areas and keep-outs (`design.rule_area`), board texts, drawings and dimensions (`design.text`, `line`, `rect`, `circle`, `arc`, `polygon`, `dimension`) and rules scoped to an area (`select.area`, written as `intersectsArea`) from the script; script items are regenerated on every build. `check` and the copper guard of `build` apply area rules and report copper in a keep-out as `copper.keepout` (`--copper-check warn` writes anyway); a rule naming no rule area stops the build (`build.area-unknown`). With `--target altium` rule areas with a restriction and centred texts are written, and an area's name, an area for rules only, a justified text, a dimension and a rule with an area selector are reported. **Release 0.2.x cannot read a model document that carries the new keys** (`name` of a keep-out, `h_justify`, `v_justify`, `dimensions`, the selector `area`)." If task 5.1 removed c0096's keep-out call, name `Design.keepout(key, …)`, `Design.keepouts` and the key `keepout:<key>` as removed. Update the entry of c0103 in `docs/roadmap.md` ("v0.4: proposals on other branches"). Proof: `grep -n "0.2.x cannot read" CHANGELOG.md` prints the line; `git diff --stat CHANGELOG.md docs/roadmap.md` lists both files.
  - Open: `docs/roadmap.md` is the coordinator's to edit in this wave. Done on 2026-10-08: the entry is the last one of `## [Unreleased]`, with the 0.2.x sentence (`grep -n "0.2.x cannot read" CHANGELOG.md` prints line 53), the limit of area rules to KiCad 10 and the changed exit of `check`.
  - 2026-10-08, base `04ef42a`: ticked. The entry now says that a rule with an area selector is written for KiCad 9 too (the probe is recorded for 9.0.9), gives the raised evidence and the 8.0 check of the dimension names, and the row of c0103 in `docs/roadmap.md` says that it ships in 0.4. `grep -n "0.2.x cannot read" CHANGELOG.md` prints its line; `git diff --stat CHANGELOG.md docs/roadmap.md` lists both files.

## Corrections

- [x] C1 (2026-10-08). `Design.rule_area()` and the seven drawing calls (`text`, `line`, `rect`, `circle`, `arc`, `polygon`, `dimension`) refused a board declared with `board(outline=…)` of change c0102 ("call board() first"): they tested `Design.size`, which only `board(width, height)` sets. They now test `Design.outline_path`, which both forms set, as `zone()`, `cutout()` and the assembly features do. "Rule areas in the DSL" and "Board drawings in the DSL" say "in either of its forms" and gain the scenarios "A shaped board takes rule areas" and "A shaped board takes drawings"; a rectangle writes what it wrote before. Found while building `examples/yardstick` (c0119, task 0.2). Proof: `uv run pytest tests/unit/lens/test_build_outline_compose.py -q` (fails before the correction, passes after); `uv run pytest tests/unit/dsl/test_drawings.py tests/unit/lens/test_build_board_items.py -q`.
