lgili/Fenolite/openspec/changes/c0104-diff-pair-constraints/tasks.md

## 0. Entry check

- [ ] 0.1 Read the living `design-model`, `rules-model`, `kicad-file-backend`, `design-dsl`, `copper-check`, `kicad-oracle`, `altium-pcb-writer`, `altium-build` and `copper-rule-explanation` specs and `openspec list`. Check the prerequisites of the proposal: release `0.3.0` cut; c0084 archived (the living `altium-pcb-writer` holds "Rule lowering table"); c0097 on `dev` (`ClearanceResolver.explain` and `tests/unit/checks/test_copper_rule_review.py` exist); c0103 and c0107 landed. Regenerate every MODIFIED requirement of this change from the living text of that day, full text and every scenario, with this change's edits only: "Rule kinds and limits" and "Closed selector grammar" (after c0107 and c0103), "Net classes lower to the project file", "Net classes in the DSL", "Interfaces in the DSL", "Interface checks in a build", and "Rule lowering table" (after c0084 and c0107). Check that the five hypothesis ids and the code `build.diff-pair-gap-shadowed` are still free (`docs/hypotheses.md`, `src/fenolite/cli/data/explain.toml`). Write the outcome under this task, with the date and the commit of `dev`. Proof: `openspec validate c0104-diff-pair-constraints --strict --no-interactive` passes after the regeneration; `git diff --stat openspec/changes/c0104-diff-pair-constraints/specs` lists the regenerated files, and the word runs by which each MODIFIED block differs from the living text are written under this task.
  - Open, 2026-10-08, base `15964cc3` (the integration branch of v0.4): the prerequisites are not all on this base. Release `0.3.0` is not cut (`CHANGELOG.md` ends at 0.2.1); c0084 is implemented and not archived, so the living `altium-pcb-writer` holds no "Rule lowering table" and the MODIFIED copy was compared with c0084's own delta; c0097 is not on the base (no `ClearanceResolver.explain`, no `test_copper_rule_review.py`); c0103 and c0107 have no task done here. What was done: the seven MODIFIED blocks were compared word by word with the text of this base and need no regeneration, because they differ from it by this change's edits only: "twelve" to "seventeen", the five kind rows, the pair bullets and four scenarios ("Rule kinds and limits"); the `diff_pair` row, the grammar clause of the five kinds, the leaf bullet, the key and two scenarios ("Closed selector grammar"); "four" to "seven", the three keys, two bullets and one scenario ("Net classes lower to the project file"); the three keywords, one bullet and one scenario ("Net classes in the DSL"); the narrowed info and one scenario ("Interfaces in the DSL"); the third code, the name rule, the shadowed-gap bullet and two scenarios ("Interface checks in a build"); one bullet, one clause of the `lift` bullet, five words and one scenario ("Rule lowering table", against c0084's delta). The five hypothesis ids and `build.diff-pair-gap-shadowed` were free. `openspec validate c0104-diff-pair-constraints --strict --no-interactive`: exit 0; `git diff --stat` of the specs folder lists no file. Left for the coordinator: regenerate "Rule kinds and limits", "Closed selector grammar" and "Rule lowering table" once c0103, c0107 and the archive of c0084 are below this change.
  - 2026-10-08, integration onto `v04`: c0107 and c0103 are on the branch now, so two of the blocks were regenerated after all: "Rule kinds and limits" from c0107's delta and "Closed selector grammar" from c0103's delta, each with this change's edits; the kinds are eighteen, not seventeen (`no_tracks` is the thirteenth), and c0107's "Track layer rules in the Altium rule table" is carried as a MODIFIED delta for the same reason (design, "Found on 2026-10-08 (integration)"). The task stays open for the other prerequisites named above.
  - 2026-10-08, on `v04` at `09ee580` (branch `v04-close-b`): `CHANGELOG.md` holds `## [0.3.0] - 2026-10-08` and the release change c0150 is archived, but no tag `v0.3.0` is on `origin`; c0084, c0101, c0103 and c0107 are built on the branch and not archived; c0097 is still not on the branch (no `ClearanceResolver.explain`, no `tests/unit/checks/test_copper_rule_review.py`): another agent integrates it with task 5.3. `openspec validate c0104-diff-pair-constraints --strict --no-interactive` reports no ERROR (the long-requirement warnings only). Stays open for c0097 and the archive of c0084.

## 1. Probe and register

- [x] 1.1 Add the rows `H-K-DRU-PAIR`, `H-K-DRU-PAIRSEL`, `H-K-DIFFPAIR-NAMES-2`, `H-K-PRO-PAIR` and `H-K-COPPER-PAIR` to `docs/hypotheses.md` (backend `kicad`, level `INFERRED`, the tests and criteria of `design.md`, result `pending` with the measurements of the design as first record). Proof: `uv run pytest tests/unit/test_hypotheses_register.py tests/unit/test_provenance.py`.
  - Done 2026-10-08: the five rows are at the end of the table, with the design's measurements as first record; 44 passed, exit 0.
- [x] 1.2 Write `tests/kicad/rules/_pairbench.py` and `tests/kicad/rules/test_pair_rules.py` with the kind rows (`dru-kind-<kind>`), the cases (`dru-pair-<case>`) and the selector rows (`dru-pair-sel-<case>`), with the scoped canary; add the `diff_pair` op to the benches of `test_rule_conditions.py` (`dru-cond-diff_pair`); register the probes in `tests/kicad/_probes.py` and record them ("Differential pair rules are enforced by kicad-cli"). Proof: `uv run pytest tests/kicad/rules/test_pair_rules.py tests/kicad/rules/test_rule_conditions.py -rA` on the local KiCad 10.0.6 and inside the pinned 9.0.9 image; `FENOLITE_PROBES_WRITE=1` updates both probe files; `uv run pytest tests/kicad/test_probe_results.py`.
  - Open for the 9.0.9 half. Done 2026-10-08 on the local `kicad-cli` 10.0.6: `tests/kicad/rules/test_pair_rules.py` and `test_rule_conditions.py` give 37 passed, exit 0; the five `dru-kind-*` probes, `dru-cond-diff_pair`, the thirteen `dru-pair-<case>` probes, `dru-pair-order-gap`, `dru-pair-order-length` and the five `dru-pair-sel-*` probes are recorded in `10.0.6.json` with the outcomes of the design (a script ran the new probes through `_probes.run` and merged them into the file in the writer's form). The 9.0.9 half was not run (no container in this session): the probes are registered for both majors and are not in `9.0.9.json`, so `tests/kicad/test_probe_results.py` asks for them on the `kicad-9` job until the coordinator records them there.
  - 2026-10-08: ticked by the second local run of 2026-10-08 in the pinned 9.0.9 image (`kicad/kicad:9.0.9@sha256:e638b79b…`, linux/amd64, branch `v04-k9-probes-2`; whole `tests/kicad` without the corpus: 998 passed, 2 failed, 806 skipped, 1 xfailed; `tests/kicad/test_probe_results.py` passed on the 723 probes of major 9): `tests/kicad/rules/test_pair_rules.py` 25 passed and `tests/kicad/rules/test_rule_conditions.py` 12 passed; the five `dru-kind-*` probes and `dru-cond-diff_pair` are `present`, and the thirteen `dru-pair-<case>` probes, the two order probes and the five `dru-pair-sel-*` probes have the outcomes of 10.0.6 in `9.0.9.json`. `KIND_SUPPORT` of the five kinds and `SELECTOR_SUPPORT["diff_pair"]` gained 9 in the same commit, as `test_shipped_support_follows_the_probe_files` asks.
- [x] 1.3 Add the cases of `H-K-DIFFPAIR-NAMES-2` to `tests/kicad/rules/_paircases.py` and record them. Proof: `uv run pytest tests/kicad/rules/test_diffpair_names.py -rA` on both majors; `uv run pytest tests/kicad/test_probe_results.py`.
  - Open for the 9.0.9 half. Done 2026-10-08 on the local `kicad-cli` 10.0.6: 15 passed, exit 0; the seven `dru-diffpair-tail-*` probes are recorded in `10.0.6.json` (`tail-digit`, `tail-underscore`, `tail-bare` and `tail-base` `present`; `tail-differs`, `tail-letter` and `tail-base-short` `absent`), and the eight cases of c0073 keep their outcomes. The 9.0.9 half was not run (no container in this session): the probes are registered for both majors and are not in `9.0.9.json`, so `tests/kicad/test_probe_results.py` asks for them on the `kicad-9` job until the coordinator records them there.
  - 2026-10-08: ticked by the second local run of 2026-10-08 in the pinned 9.0.9 image (`kicad/kicad:9.0.9@sha256:e638b79b…`, linux/amd64, branch `v04-k9-probes-2`; whole `tests/kicad` without the corpus: 998 passed, 2 failed, 806 skipped, 1 xfailed; `tests/kicad/test_probe_results.py` passed on the 723 probes of major 9): `tests/kicad/rules/test_diffpair_names.py` 15 passed; the seven `dru-diffpair-tail-*` probes have the outcomes of 10.0.6 in `9.0.9.json`, and the eight cases of c0073 compared equal to their rows.
- [x] 1.4 Write `tests/kicad/project/test_pair_classes.py` with the class rows and the custom rule rows (`pro-pair-<case>`), and record them ("Net class pair values are probed"). Proof: `uv run pytest tests/kicad/project/test_pair_classes.py -rA` on both majors; `uv run pytest tests/kicad/test_probe_results.py`.
  - Open for the 9.0.9 half. Done 2026-10-08 on the local `kicad-cli` 10.0.6: 12 passed, exit 0; the eleven `pro-pair-<case>` probes are recorded in `10.0.6.json` with the outcomes of the design; the benches are in `tests/kicad/project/_pairclasses.py`, written through the triad path. The 9.0.9 half was not run (no container in this session): the probes are registered for both majors and are not in `9.0.9.json`, so `tests/kicad/test_probe_results.py` asks for them on the `kicad-9` job until the coordinator records them there.
  - 2026-10-08: ticked by the second local run of 2026-10-08 in the pinned 9.0.9 image (`kicad/kicad:9.0.9@sha256:e638b79b…`, linux/amd64, branch `v04-k9-probes-2`; whole `tests/kicad` without the corpus: 998 passed, 2 failed, 806 skipped, 1 xfailed; `tests/kicad/test_probe_results.py` passed on the 723 probes of major 9): `tests/kicad/project/test_pair_classes.py` 12 passed; the eleven `pro-pair-<case>` probes have the outcomes of 10.0.6 in `9.0.9.json`.
- [x] 1.5 Write the facts of tasks 1.2 to 1.4 to `docs/formats/kicad/rules.md` and `docs/formats/kicad/project.md`, with sources S-0010, S-0038, S-0020 and S-0029 and their labels. When an outcome differs from the design's measurements, write it under this task and correct the design, the specs and the tables that depend on it before group 2. Proof: `uv run pytest tests/unit/test_format_facts.py tests/consistency`.
  - Done 2026-10-08: the facts are in `rules.md` and `project.md` with their sources; their label is `KICAD-VERIFIED (10.0.x)`, because only 10.0.6 is recorded, and the via length is `INFERRED` (the design's scratch bench, no committed probe). No outcome on 10.0.6 differs from the design's measurements. 315 passed, 19 skipped, exit 0.

## 2. Model

- [x] 2.1 Write `src/fenolite/model/pairs.py` and `tests/unit/model/test_pairs.py` (scenarios "Names that pair", "Names that do not pair" and "Nets of a USB interface"). Proof: `uv run pytest tests/unit/model/test_pairs.py tests/unit/test_import_graph.py`; `uv run pyright src`.
  - Done 2026-10-08: 39 passed, exit 0; `uv run pyright src`: 0 errors, exit 0.
- [x] 2.2 Add the three `NetClass` fields, the five kinds, the `diff_pair` op and `RuleSubject.diff_pair` with its match, and regenerate the schemas (scenarios "Pair leaf matches by base" and "Older circuit document loads"). Add to `docs/design-model.md` the three class keys, the five kinds, the leaf and the sentence "0.2.x and 0.3.0 cannot read a `circuit.json` or a `rules.json` that carries them". Proof: `uv run pytest tests/unit/model tests/unit/test_schema_drift.py`; `uv run python tools/gen_schemas.py --check` exits 0; `grep -n "cannot read" docs/design-model.md` shows the sentence.
  - Done 2026-10-08: 236 passed, 1 skipped, exit 0; `tools/gen_schemas.py --check` exit 0 (`circuit.json` and `rules.json` regenerated with the tool); the sentence is in `docs/design-model.md`, "Differential pairs".
- [x] 2.3 Add the five rows to `backends/altium/rulemap.TABLE` (reason `no-counterpart`, a note each, no kind number and no key) and to the table "The lowering table" of `docs/formats/altium/pcb-copper.md`, in the same commit as task 2.2, so that no commit holds a `RuleKind` without a row (scenarios "Every kind has a row" and "Pair and length rules are named, not written"). Proof: `uv run pytest tests/unit/backends/altium/test_rulemap.py -k "complete or pair or roundtrip" tests/unit/test_format_facts.py`.
  - Done 2026-10-08, in the one commit of this change: 9 passed, exit 0.

## 3. Rules

- [x] 3.1 Add the five kinds to `KIND_MAP`, `LIMITS`, `KIND_SELECTORS` and `KIND_SUPPORT` (pinned to the probe files), and write and lift the list `(within_diff_pairs)` of `diff_pair_skew` (scenarios of "Rule kinds and limits"). Proof: `uv run pytest tests/unit/backends/kicad/test_rulemap.py tests/unit/backends/kicad/test_rulemap_kinds.py tests/unit/backends/kicad/test_rulemap_pairs.py`; `uv run pyright src`.
  - Done 2026-10-08: 126 passed, exit 0; pyright exit 0. `KIND_SUPPORT` holds 10 only for the five kinds, which is what the probe files say today; the unit scenarios set both majors.
- [x] 3.2 Add the `diff_pair` leaf: the `inDiffPair` writer and reader, the `SELECTOR_SUPPORT` key pinned to `dru-cond-diff_pair`, and the grammars of the kinds (scenarios of "Closed selector grammar"). Proof: `uv run pytest tests/unit/backends/kicad/test_rulemap_pairs.py tests/unit/backends/kicad/test_rulemap.py -k "support or pair"`.
  - Done 2026-10-08: 31 passed, exit 0. `SELECTOR_SUPPORT["diff_pair"]` holds 10 only, as `dru-cond-diff_pair` is recorded.
- [x] 3.3 Read hand-written pair rules: lift the kinds, their `opt`, the list, the leaf and a layer clause on `diff_pair_gap`; keep a limit outside a kind's row, a bare `within_diff_pairs` atom, a time unit and a layer clause on another pair kind opaque with `rules.kept-opaque`; check the self-check of `write_rules` and the rebuild of a rules file holding a hand-written pair rule. Proof: `uv run pytest tests/unit/backends/kicad/test_dru.py -k pair tests/unit/backends/kicad/test_lowering.py -k "self_check or codes"`.
  - Done 2026-10-08: `test_dru.py -k pair` 3 passed, exit 0; `test_lowering.py -k "self_check or codes"` 2 passed, exit 0.

## 4. Project file

- [x] 4.1 Add the three keys to `NETCLASS_KEYS` and write them in synthesis and update (scenarios "Pair values lowered", "Synthesis writes pair values" and "Update keeps an equal spelling"). Proof: `uv run pytest tests/unit/backends/kicad/test_lowering_netclass.py tests/unit/backends/kicad/test_pro_synth.py tests/unit/backends/kicad/test_pro_update.py`.
  - Done 2026-10-08: 33 passed, exit 0.
- [x] 4.2 Read the three values into `ProjectClass` and apply them (scenario "Pair values read back"). Proof: `uv run pytest tests/unit/backends/kicad/test_pro_read.py tests/unit/backends/kicad/test_pro.py`.
  - Done 2026-10-08: 19 passed, exit 0.

## 5. Copper check

- [x] 5.1 Set the subject's `diff_pair`, match the leaf with its letter case, and apply the pair gap as class value with the source `pair-gap:<class>` (scenarios "Pair below its class clearance", "Rules over the pair gap", "Board minimum above the pair gap" and "Letter case of the pair leaf"). Proof: `uv run pytest tests/unit/checks`.
  - Done 2026-10-08: 499 passed, exit 0.
- [x] 5.2 Add the pair cases to `tests/kicad/copper/_copperparity.py`, record `copper-resolve-pair-<case>`, and add the pair row to the supported-cases table of `docs/formats/kicad/copper.md` ("Differential pair clearance parity"). Proof: `uv run pytest tests/kicad/copper/test_copper_parity.py -k pair -rA` on both majors; `uv run pytest tests/kicad/copper/test_parity_bench.py tests/unit/test_format_facts.py -k copper`.
  - Open for the 9.0.9 half. Done 2026-10-08 on the local `kicad-cli` 10.0.6: `test_copper_parity.py -k pair` 11 passed, exit 0; the four `copper-resolve-pair-*` probes are `equal` in `10.0.6.json`; the row is in `docs/formats/kicad/copper.md`; `test_parity_bench.py` and `test_format_facts.py -k copper` 35 passed, exit 0 (the Fenolite half of the rows for targets 9 and 10). The 9.0.9 half was not run (no container in this session): the probes are registered for both majors and are not in `9.0.9.json`, so `tests/kicad/test_probe_results.py` asks for them on the `kicad-9` job until the coordinator records them there.
  - 2026-10-08: ticked by the second local run of 2026-10-08 in the pinned 9.0.9 image (`kicad/kicad:9.0.9@sha256:e638b79b…`, linux/amd64, branch `v04-k9-probes-2`; whole `tests/kicad` without the corpus: 998 passed, 2 failed, 806 skipped, 1 xfailed; `tests/kicad/test_probe_results.py` passed on the 723 probes of major 9): the four `copper-resolve-pair-*` probes are `equal` in `9.0.9.json`; `tests/kicad/copper/test_copper_parity.py` 30 passed, 2 skipped.

- [x] 5.3 Add the `pair-gap:<class>` candidate row to `ClearanceResolver.explain` (c0097), from the resolver's own candidate, and `diff_pair` to the explained subjects (scenario "Pair gap in the explanation"); add the row to `docs/copper-rule-explanations.md`. Proof: `uv run pytest tests/unit/checks/test_copper_rule_review.py tests/unit/checks/test_clearance.py`.
  - Open, 2026-10-08: c0097 is not on this base (`ClearanceResolver.explain` and `test_copper_rule_review.py` do not exist). The resolver already gives the source `pair-gap:<class>` and the subjects carry `diff_pair`, so the row is a candidate of the resolver when c0097 lands.
  - 2026-10-08, on `v04-codex` with c0097: `ClearanceResolver.explain` adds the row `pair-gap:<class>` from the resolver's own `_pair_gap`, before the class rows; the subjects already carry `diff_pair`. `test_pair_gap_in_the_explanation` in `tests/unit/checks/test_copper_rule_review.py` holds the scenario; the row is in `docs/copper-rule-explanations.md`. Proof: `uv run pytest tests/unit/checks/test_copper_rule_review.py tests/unit/checks/test_clearance.py` 50 passed.

## 6. DSL and build

- [x] 6.1 Add the pair keywords to `design.rules.netclass` and to `to_model` (scenario "Class with pair values"). Proof: `uv run pytest tests/unit/dsl/test_to_model.py tests/unit/dsl/test_minimums.py`.
  - Done 2026-10-08: 31 passed, exit 0 (the scenario "Class with pair values" is in `tests/unit/dsl/test_pair_rules.py`, run with the two files).
- [x] 6.2 Add `select.pair` (scenarios of "Pair selectors in the DSL"). Proof: `uv run pytest tests/unit/dsl/test_select.py`.
  - Done 2026-10-08: 21 passed, exit 0.
- [x] 6.3 Add `design.rules.pair` (scenarios of "Pair rules in the DSL"). Proof: `uv run pytest tests/unit/dsl/test_pair_rules.py tests/unit/cli/test_build_rules_command.py`.
  - Done 2026-10-08: 12 passed, exit 0.
- [x] 6.4 Move `is_pair` and `pair_hint` onto `model.pairs`, narrow `build.interface-not-lowered`, add `build.diff-pair-gap-shadowed` to `BUILD_ISSUE_CODES`, and add its `explain` entry and the new meaning of `build.interface-not-lowered` to `cli/data/explain.toml` (scenarios of "Interfaces in the DSL" and "Interface checks in a build"). Proof: `uv run pytest tests/unit/lens/test_interface_checks.py tests/unit/lens/test_build_issues.py tests/unit/cli/test_explain_cmd.py`.
  - Done 2026-10-08: 29 passed, exit 0. `lens` may not import `checks` (package layering), so the shadowed-gap check matches the clearance rules with a small matcher of its own in `lens/build.py` that folds names as the resolver does.
- [x] 6.5 Add the pair and a `pair()` call to the rules design of `tests/_rulesdesign.py` and build it for each major (scenario "Built pair rules load"). Proof: `uv run pytest tests/kicad/rules/test_rule_design.py -rA` on both majors.
  - Open for the 9.0.9 half. Done 2026-10-08 on the local `kicad-cli` 10.0.6: 2 passed, exit 0; the built file holds the five pair rules and loads. On a major outside `KIND_SUPPORT` the pair test skips with that reason, so on 9 it runs once the probes are recorded there.
  - 2026-10-08: ticked by the second local run of 2026-10-08 in the pinned 9.0.9 image (`kicad/kicad:9.0.9@sha256:e638b79b…`, linux/amd64, branch `v04-k9-probes-2`; whole `tests/kicad` without the corpus: 998 passed, 2 failed, 806 skipped, 1 xfailed; `tests/kicad/test_probe_results.py` passed on the 723 probes of major 9): `tests/kicad/rules/test_rule_design.py` 2 passed; with the five kinds in `KIND_SUPPORT` for major 9 the pair test runs there and the built file loads.

- [x] 6.6 Altium build: give the info `altium.not-lowered` at `pair-values` for classes that hold a pair value, with and without a PCB document; check that a pair or length rule gives its warning at `design-rules/<kind>` and that a rule with a `diff_pair` leaf gives `scope-unsupported` (scenarios of "Differential pairs in an Altium build"). Say in `docs/altium.md` what an Altium build does with pair rules, pair values and pair interfaces. Proof: `uv run pytest tests/unit/lens/test_altium_rules.py -k pair tests/unit/lens/test_altium_golden.py tests/unit/cli/test_explain_cmd.py`.
  - Done 2026-10-08: `test_altium_rules.py -k pair` 4 passed, exit 0; `test_altium_golden.py` and `test_explain_cmd.py` 14 passed, exit 0; `docs/altium.md` has the bullet "Differential pairs" and the round-trip row of the three class fields.

## 7. Documentation

- [x] 7.1 Document the pair in `docs/dsl.md` ("Design rules": the `netclass` keywords, `select.pair`, `pair()` with an example and the name order; "Typed interfaces": the narrowed info and the name rule), `docs/formats/kicad/rules.md` (the kind table with its DRC types, the `diff_pair` row, the selectors per kind, uncoupled segments at any distance, vias in a length), `docs/formats/kicad/project.md` (the three class keys and their effect) and `docs/cli-contract.md` (`build.diff-pair-gap-shadowed`). Proof: `uv run pytest tests/consistency tests/unit/test_format_facts.py tests/residue`.
  - Done 2026-10-08: 353 passed, 19 skipped, exit 0.
- [x] 7.2 If c0080 is archived, add one tested `fenolite-design` line for `select.pair` and `design.rules.pair` to its guide page on design scripts; if not, write under this task that c0080's coverage test will ask for the line. Proof: `uv run pytest tests/unit/agent/test_pages.py` when c0080 is archived.
  - Done 2026-10-08: c0080 is not archived (no task of it is done on this base), so no line was added; c0080's coverage test will ask for one tested `fenolite-design` line for `select.pair` and `design.rules.pair`.

## 8. Closing

- [x] 8.1 Run the residue and fast suites. Proof: `uv run pytest tests/residue tests/corpus/test_manifest.py` (after `git add -A`) and `uv run python tools/residue/scan.py` exit 0; `uv run python tools/gen_schemas.py --check` exits 0; `make check-fast` passes; `openspec validate c0104-diff-pair-constraints --strict --no-interactive` and `openspec validate --all --strict --no-interactive` pass. The full `make check` and `gh pr checks` (`unit`, `kicad-9`, `kicad-10`) are the coordinator's, once, on the rebased branch at merge; this change's agent does not start a full suite.
  - Open, 2026-10-08: residue, manifest, `tools/residue/scan.py`, `gen_schemas.py --check`, `gen_evidence_matrix.py --check`, ruff, pyright and `openspec validate --all --strict --no-interactive` (101 passed) exit 0. `make check-fast PYTEST_WORKERS=3`, run once: 4 failed, 10900 passed, 24 skipped, exit 2. The four failures are not of this change: `test_altium_rta2.py` (three, on `yardstick/design.py`) and `test_spdx_headers.py` (`tools/yardstick.py`) fail the same way on a clean checkout of `15964cc3`.
  - 2026-10-08, on `v04` at `09ee580` with the edits of this pass (branch `v04-close-b`): `make check-fast PYTEST_WORKERS=3`: ruff check, ruff format, the guide check, pyright and the residue scan pass, 12761 passed, 30 skipped, exit 0 (no rerun needed: the two timing tests passed). `uv run --isolated --python 3.11 --extra dev pytest tests/unit -q -n 3 -p no:cacheprovider`: 12378 passed, 26 skipped, exit 0 (three workers, as the coordinator asked, for the four of the proof). After `git add -A`: `uv run pytest tests/residue tests/corpus/test_manifest.py` 82 passed, 3 skipped; `uv run python tools/residue/scan.py` 0 hits; `tools/gen_schemas.py --check` and `tools/gen_evidence_matrix.py --check` exit 0. `openspec validate --all --strict --no-interactive`: five ERRORs, all of other changes (c0084, c0085 twice, c0086, c0128; the one of c0108 is gone) and the long-requirement warnings that every change gives, which the coordinator accepts for this release; this change's own `--strict` run gives no ERROR. The full `make check` and the CI run are the coordinator's.
- [x] 8.2 Run the unit suite on Python 3.11 before handing over. Proof: `uv run --isolated --python 3.11 --extra dev pytest tests/unit -q -n 4 -p no:cacheprovider` exits 0.
  - Open, 2026-10-08: the command exits 1 with 4 failed, 10581 passed, 5 skipped. The four failures are not of this change: `test_altium_rta2.py` (three, on `yardstick/design.py`) and `test_spdx_headers.py` (`tools/yardstick.py`) fail the same way on a clean checkout of `15964cc3`, on 3.11 and 3.13.
  - 2026-10-08, on `v04` at `09ee580` with the edits of this pass (branch `v04-close-b`): `make check-fast PYTEST_WORKERS=3`: ruff check, ruff format, the guide check, pyright and the residue scan pass, 12761 passed, 30 skipped, exit 0 (no rerun needed: the two timing tests passed). `uv run --isolated --python 3.11 --extra dev pytest tests/unit -q -n 3 -p no:cacheprovider`: 12378 passed, 26 skipped, exit 0 (three workers, as the coordinator asked, for the four of the proof). After `git add -A`: `uv run pytest tests/residue tests/corpus/test_manifest.py` 82 passed, 3 skipped; `uv run python tools/residue/scan.py` 0 hits; `tools/gen_schemas.py --check` and `tools/gen_evidence_matrix.py --check` exit 0. `openspec validate --all --strict --no-interactive`: five ERRORs, all of other changes (c0084, c0085 twice, c0086, c0128; the one of c0108 is gone) and the long-requirement warnings that every change gives, which the coordinator accepts for this release; this change's own `--strict` run gives no ERROR. The full `make check` and the CI run are the coordinator's.
- [x] 8.3 Update the evidence: the five rows become `KICAD-VERIFIED (9.0.x, 10.0.x)` with their per-major outcomes, or record what failed; the result of `H-K-DIFFPAIR-NAMES` gains "partly refuted: a tail of digits and underscores may follow the polarity; extended by H-K-DIFFPAIR-NAMES-2"; `lowering.EVIDENCE` names `H-K-DRU-PAIR`. Proof: `uv run pytest tests/unit/test_provenance.py tests/unit/test_hypotheses_register.py`.
  - Open for the 9.0.9 half. Done 2026-10-08: the five rows are `KICAD-VERIFIED (10.0.x)` with their outcomes on 10.0.6; the result of `H-K-DIFFPAIR-NAMES` has the sentence; `lowering.EVIDENCE` names `H-K-DRU-PAIR`; 44 passed, exit 0. The rows become `(9.0.x, 10.0.x)`, and `KIND_SUPPORT` and `SELECTOR_SUPPORT["diff_pair"]` gain 9, when the probes are recorded on 9.0.9.
  - 2026-10-08: after the image run named under task 1.2, the five rows `H-K-DRU-PAIR`, `H-K-DRU-PAIRSEL`, `H-K-DIFFPAIR-NAMES-2`, `H-K-PRO-PAIR` and `H-K-COPPER-PAIR` are `KICAD-VERIFIED (9.0.x, 10.0.x)`, and `KIND_SUPPORT` and `SELECTOR_SUPPORT["diff_pair"]` hold 9 and 10. Still open: the code-side evidence constants and the labels of the fact rows of `docs/formats/kicad/` were not raised by the commit that recorded the probes; CI has still to confirm the 9.0.9 half.
  - 2026-10-08, on `v04` at `09ee580` (branch `v04-close-b`): the `kicad-9` job of CI run 37772583226 on `04ef42a` (all jobs green) passed on 9.0.9 `test_pair_rules.py` (25), `test_diffpair_names.py` (15), `test_pair_classes.py` (12), the pair cases of `test_copper_parity.py` (11), `test_rule_design.py` (2) and `test_probe_results.py`; the `kicad-10` job passed them on 10.0.6. The fact rows of `docs/formats/kicad/rules.md` (nine), `project.md` (four) and `copper.md` (the pair row's 9.0.9 column) now say `KICAD-VERIFIED (9.0.x, 10.0.x)`, as the five hypothesis rows do; `lowering.EVIDENCE` is `KICAD-VERIFIED` and names `H-K-DRU-PAIR`; the via-length row stays `INFERRED` (no probe). `uv run pytest tests/unit/test_provenance.py tests/unit/test_hypotheses_register.py`: 44 passed, exit 0.
- [x] 8.4 Add to `CHANGELOG.md` under Unreleased: "Differential pairs in KiCad: class pair width, gap and via gap; rule kinds for pair gap, uncoupled length, skew and length; `select.pair()` and `design.rules.pair()`; the copper check lowers the clearance inside a pair as KiCad does; pair names with digits after the P or N are recognised". The entry also says that 0.2.x and 0.3.0 cannot read a `circuit.json` or `rules.json` that carries the new keys and kinds, and that an Altium build names pair rules and pair values and writes none. Update the c0104 row of `docs/roadmap.md` (the table of "v0.4: proposals on other branches", or the milestone table if the section was folded into it by then). Proof: `git diff --stat CHANGELOG.md docs/roadmap.md` lists both files; `grep -n "c0104" docs/roadmap.md` shows the row.
  - Open, 2026-10-08: the entry is at the end of `## [Unreleased]`; the row of c0104 in `docs/roadmap.md` is left to the coordinator, who edits that file for the wave.
  - 2026-10-08: the row of c0104 in `docs/roadmap.md` says it is built on `v04` with its KiCad rows verified on both majors, and a paragraph "c0104 on `v04`" names what is left (the pair-gap row of `ClearanceResolver.explain`, with c0097); `CHANGELOG.md` gains a line under `### Changed` for the raised fact rows. `git diff --stat CHANGELOG.md docs/roadmap.md` lists both; `grep -n "c0104" docs/roadmap.md` shows the row.
