lgili/Fenolite/openspec/changes/c0105-impedance-targets/tasks.md

## 0. Entry check

- [x] 0.1 Read the living `design-model`, `design-dsl`, `kicad-file-backend`, `board-analyses`, `manufacturing-exports`, `cli-contract`, `kicad-oracle`, `altium-build`, `altium-pcb-writer` and `rules-model` specs, and `openspec list`. Check the prerequisites of the proposal: release `0.3.0` cut and c0084 archived (the living `altium-build` holds "Rules in an Altium build"); c0101 and c0104 archived. Write under this task, with the date and the commit of `dev`, where their archived names differ from the proposals the design names (Context): `Stackup.impedance_controlled`, `Stackup.between` and the rebuild rule (c0101); `NetClass.diff_pair_*`, the kind `diff_pair_gap` with `min`, `opt`, `max` and its layer clause, its Altium row, `select.pair` and `pair()` rule names (c0104); correct the derived rules and the checks on them where they differ (Decisions 4, 5, 9, 13, 14). Check whether c0114 sets `tuning_profile_track_geometries`; whether c0079, c0080 and c0116 are on `dev`; that no requirement of the living specs is named like one of this change's eleven; that the block S-0640 to S-0643, the five hypothesis ids and the fourteen new issue codes are still free (`docs/evidence/sources.md`, `docs/hypotheses.md`, `src/fenolite/cli/data/explain.toml`). Proof: `openspec validate c0105-impedance-targets --strict --no-interactive` passes after any rename; `grep -c "S-064[0-3]" docs/evidence/sources.md` prints 0 before task 1.1.
  - 2026-10-08, on `v04` `30bbffd` (the v0.4 integration branch): `0.3.0` is not cut; c0084, c0101 and c0104 are implemented on the branch and not archived. Their names hold as the design takes them: `Stackup.impedance_controlled`, `Stackup.between` and the rebuild rule (`stackup.merge_stackup`); `NetClass.diff_pair_*`, the kind `diff_pair_gap` with `min`, `opt`, `max` and a layer clause for both majors (`rulemap.KIND_SUPPORT`), its Altium row `no-counterpart`, `select.pair` and the names `pair:<name>:<group>`. Decision 4 stands without its fallback. c0114 sets no default for `tuning_profile_track_geometries` (the template's `ignore` stays). c0079, c0080 and c0116 are on the branch (task 8.2 applies). No living requirement is named like one of this change's. S-0640 to S-0643, the five hypothesis ids and the fourteen codes were free: `grep -c "S-064[0-3]" docs/evidence/sources.md` printed 0 before task 1.1.
  - Open: `openspec validate c0105-impedance-targets --strict --no-interactive` reports 0 ERROR and 11 WARNINGs ("Requirement text is very long") on the spec files of this change as they stand on the base, untouched here; strict mode counts the warnings, so the proof does not pass until the maintainer shortens or splits those requirements. `openspec validate --all --strict` names no ERROR of c0105 (its ERRORs are of c0084, c0085 and c0128).
  - 2026-10-08, on `v04` at `09ee580` (branch `v04-close-b`): checked again: `CHANGELOG.md` holds `## [0.3.0] - 2026-10-08` (c0150 archived; no tag `v0.3.0` on `origin`); c0084, c0101 and c0104 are built on the branch and not archived, and the names of the note above still hold (`Stackup.impedance_controlled`, `Stackup.between`, `NetClass.diff_pair_*`, `diff_pair_gap` with its layer clause, `select.pair`, `pair:<name>:<group>`). The maintainer's decision of 2026-10-08 closes this change for 0.4 without the archives. `openspec validate c0105-impedance-targets --strict --no-interactive`: no ERROR; it exits 1 on the long-requirement warnings that every change of the branch gives, which the coordinator accepts for this release.

## 1. Probe and register

- [x] 1.1 Register S-0641 to S-0643 in `docs/evidence/sources.md` (the block reserved for this group; the licence cells as the design's table states them, "facts only, no text copied" for the two encyclopedia pages), widen the "used for" cell of S-0038, and add the rows `H-K-PRO-TUNING-DRC`, `H-K-PRO-TUNING-KEYS`, `H-K-DRU-IMPEDANCE`, `H-G-AN-ZMS` and `H-G-AN-ZSL` to `docs/hypotheses.md` (level `INFERRED`, the tests and criteria of `design.md`, the measurements of 2026-10-05 as first record). Proof: `uv run pytest tests/unit/test_hypotheses_register.py tests/unit/test_provenance.py`.
  - 2026-10-08, after the maintainer's clean-room correction of 2026-10-08: the first id of the block, a page of KiCad's source code, is not registered (AGENTS.md); the facts that cited it rest on the measurements of 2026-10-05 and owe the probes `pro-tuning-width`, `pro-tuning-gap` and `pro-tuning-single-under-diff` (`docs/formats/kicad/project.md`, "Tuning profiles"). `uv run pytest tests/unit/test_hypotheses_register.py tests/unit/test_provenance.py` passed again.
  - 2026-10-08: the sources, the widened S-0038 cell and the five rows (`INFERRED`, first record the measurements of 2026-10-05) are in. `uv run pytest tests/unit/test_hypotheses_register.py tests/unit/test_provenance.py` 44 passed, exit 0.
- [x] 1.2 Write `tests/kicad/impedance/_zbench.py` (the bench of "Impedance targets pass the oracle", with the stack-up as c0101 writes it) and `test_tuning_drc.py` with the nine `pro-tuning-*` probes, registered in `tests/kicad/_probes.py`, and record them on 10.0.6. If a probe differs from the design's measurement, stop and correct Decision 4 or 7 first. Proof: `uv run pytest tests/kicad/impedance/test_tuning_drc.py -rA` on the local KiCad 10.0.6; `FENOLITE_PROBES_WRITE=1` updates the probe file; `uv run pytest tests/kicad/test_probe_results.py`.
  - 2026-10-08: written: `tests/kicad/impedance/_zbench.py` (the bench, the nine `pro-tuning-*` probes in `tuning_probes()`), `test_tuning_drc.py` (`needs_kicad`, 10.0 only) and the `impedance/` folder on the oracle path (`tests/kicad/conftest.py`). The bench writes and reads back hermetically for both majors (a scratch run with a stub runner). Not registered in `_probes.py` (design, "Found on 2026-10-08"). owed: needs kicad-cli; judged by GitHub CI.
  - 2026-10-08: ticked by CI run 37772583226 on `04ef42a` (all jobs green): in the `kicad-10` job (10.0.6) `tests/kicad/impedance/test_tuning_drc.py` passed all its cases: the eight probes `pro-tuning-width`, `-exact`, `-norow`, `-missing`, `-gap`, `-single-under-diff`, `-rule-governs` and `-gap-clearance` gave the outcomes of the design (each case asserts it, with the scoped canary), and `pro-tuning-gap-clearance-rule` ran and was recorded either way; on 9.0.9 the file skips (profiles exist in KiCad 10 only). The eight are registered in `tests/kicad/_probes.py` for major 10 and their outcomes are in `10.0.6.json` (written from that run, which asserted them; the next `kicad-10` job runs them again through `test_probe_results.py`). `pro-tuning-gap-clearance-rule` is not registered: the `kicad-10` job runs with `-q`, so its printed outcome is not in the log.
- [ ] 1.3 Write `test_impedance_rules.py` and record `dru-impedance-width` on both majors. If `pro-tuning-gap-clearance-rule` of task 1.2 recorded a clearance finding, extend `build.impedance-gap-clearance` to target 10 under a governing custom clearance rule (task 3.3). Proof: `uv run pytest tests/kicad/impedance/test_impedance_rules.py -rA` on the local KiCad 10.0.6 and inside the pinned 9.0.9 image; both probe files updated.
  - 2026-10-08: written: `test_impedance_rules.py` and `width_probes()` (`dru-impedance-width`, both majors), not registered. owed: needs kicad-cli; judged by GitHub CI.
  - 2026-10-08: `dru-impedance-width` is `present` on both majors (CI run 37772583226 on `04ef42a` (all jobs green): `test_width_rules_per_layer` passed in the `kicad-9` job, printing `present` with the types `clearance`, `track_dangling`, `track_width`, and in the `kicad-10` job), registered for both majors and written into both probe files. Open for its conditional half: whether `pro-tuning-gap-clearance-rule` records a clearance finding (and `build.impedance-gap-clearance` extends to target 10) needs that outcome, which the `-q` log of the `kicad-10` job does not show; written; awaits the CI run whose log prints it (`-rA`, as the `kicad-9` job runs).
  - 2026-10-08, CI run 37803522539 on `a105cc0`: still open. The `kicad-10` job reported no failure in `tests/kicad/impedance/test_tuning_drc.py` (its one failure was elsewhere, fixed by `38fecbd`), but it runs `-q`, so the outcome of `pro-tuning-gap-clearance-rule` is not printed; in the `kicad-9` job the file skips (tuning profiles exist in KiCad 10 only). Needs a run that prints it: `-rA` in the `kicad-10` job, or `uv run pytest tests/kicad/impedance/test_tuning_drc.py -rA` on a 10.0.6.
- [ ] 1.4 Settle `H-K-PRO-TUNING-KEYS`: on a copy of the bench project, create one single and one differential profile in the KiCad 10.0.6 GUI, save, and commit the authored save as `tests/data/kicad/project/tuning_10.kicad_pro` with its entry in `tests/data/MANIFEST.toml` (origin `authored`, the note naming KiCad 10.0.6 and the bench; no absolute path in the file); compare its key paths and value kinds with `lower_profile`. Proof: `uv run pytest tests/corpus/test_manifest.py -q` after `git add`; `uv run pytest tests/unit/backends/kicad/test_tuning_profiles.py -k gui_save` (written with task 4.1, failing until then).
  - 2026-10-08: owed: needs the KiCad 10.0.6 GUI. `test_tuning_profiles.py::test_gui_save` is written and skips while `tests/data/kicad/project/tuning_10.kicad_pro` does not exist.
  - 2026-10-08: deferred to the next release by the maintainer's decision of 2026-10-08 (the GUI save is the maintainer's own test). `tuning.EVIDENCE` stays `INFERRED` and names `H-K-PRO-TUNING-KEYS`, so no reply claims more than `INFERRED` for the profile keys; `test_tuning_profiles.py::test_gui_save` keeps skipping without the file.

## 2. Model

- [x] 2.1 Add `ImpedanceKind`, `TraceGeometry`, `ImpedanceTarget` and `RuleSet.impedance` to `src/fenolite/model/rules.py`, `model.impedance-invalid` to `Design.validate()`, and regenerate the rules schema (scenarios of "Impedance targets in the rules model"). Add `RuleSet.impedance` to `docs/design-model.md` with the sentence "0.2.x and 0.3.0 cannot read a `rules.json` that carries the key `impedance`", and the table of `model.impedance-invalid` to `cli/data/explain.toml`. Proof: `uv run pytest tests/unit/cli/test_explain_cmd.py`; `grep -n "cannot read" docs/design-model.md` shows the sentence; `uv run pytest tests/unit/model/test_impedance_model.py tests/unit/model/test_rules.py tests/unit/test_schema_drift.py`; `uv run python tools/gen_schemas.py --check`; `uv run pyright src`.
  - 2026-10-08: `tests/unit/cli/test_explain_cmd.py` 8 passed; the grep shows the sentence (line of "Impedance targets"); `tests/unit/model/test_impedance_model.py tests/unit/model/test_rules.py tests/unit/test_schema_drift.py` 61 passed; `gen_schemas.py --check` exit 0; `pyright src` 0 errors. `model.impedance-invalid` has no table in `explain.toml`: no `model.*` code is in an issue table, and the explain test refuses an entry without one (design, "Found on 2026-10-08").

## 3. DSL and build

- [x] 3.1 Write `src/fenolite/dsl/impedance.py` (`Trace`, `trace`) and `Rules.impedance` with every call-time check, and re-export `trace` (call scenarios of "Impedance targets in the DSL"). Proof: `uv run pytest tests/unit/dsl/test_impedance_dsl.py -k call tests/unit/test_import_graph.py`.
  - 2026-10-08: `uv run pytest tests/unit/dsl/test_impedance_dsl.py -k call tests/unit/test_import_graph.py` passed (the whole file 34 passed; `dsl` imports `model` only).
- [x] 3.2 Add the targets and the derived rules to `to_model`: classes from names and pairs, ohms and tolerance as text, stack order, rule names, limits and priority (the other scenarios of the requirement). Proof: `uv run pytest tests/unit/dsl/test_impedance_dsl.py tests/unit/dsl`.
  - 2026-10-08: `tests/unit/dsl/test_impedance_dsl.py` 34 passed; `tests/unit/dsl`, with `tests/unit/model`, 1006 passed, 3 skipped (files of c0126). The prefix `imp` joins `core.ids.PREFIXES` and `KEYS` gains `impedance`.
- [x] 3.3 Write `lens.build.impedance_checks` with its six codes in `BUILD_ISSUE_CODES`, called by `build_design`, and one table per code in `cli/data/explain.toml` (scenarios of "Impedance targets in a build"). Proof: `uv run pytest tests/unit/lens/test_impedance_checks.py tests/unit/lens/test_build_issues.py -k "impedance or closed_set"`; `uv run pytest tests/unit/cli/test_explain_cmd.py`.
  - 2026-10-08: `tests/unit/lens/test_impedance_checks.py tests/unit/lens/test_build_issues.py` 17 passed; `test_explain_cmd.py` 8 passed. The checks run in `build_design` before `Design.validate()`, on the merged board.
- [x] 3.4 Give `build.impedance-stackup` its scenario with c0101's `design.stackup()`, and the two-layer pair target its two gap rules (scenarios "Stack-up not marked" and "Pair target on two layers with two gaps"). Proof: `uv run pytest tests/unit/lens/test_impedance_checks.py -k stackup tests/unit/dsl/test_impedance_dsl.py -k two_gaps`.
  - 2026-10-08: `-k stackup` (`test_stackup_not_marked`, `test_no_stackup`) and `-k two_gaps` passed.

## 4. KiCad 10 profiles

- [x] 4.1 Write `src/fenolite/backends/kicad/tuning.py` (`lower_profile`, `apply_profile_keys`, `PROFILE_KEY_PATHS`), the call in `write_triad` and the row of `kicad.project.profile-reassigned` with its table in `cli/data/explain.toml` (scenarios of "Tuning profiles for impedance targets"). Proof: `uv run pytest tests/unit/cli/test_explain_cmd.py`; `uv run pytest tests/unit/backends/kicad/test_tuning_profiles.py tests/unit/backends/kicad/test_pro_synth.py tests/unit/backends/kicad/test_pro_update.py tests/unit/backends/kicad/test_write_triad.py`; `uv run pyright src`.
  - 2026-10-08: `test_explain_cmd.py` 8 passed; `test_tuning_profiles.py test_pro_synth.py test_pro_update.py test_write_triad.py` passed (with `test_pro_read.py`: 84 passed, 1 skipped, the GUI save of task 1.4); `pyright src` 0 errors.
- [x] 4.2 Read profiles: `read_profiles`, `lift_profiles`, `ProjectInfo.profiles` and `apply_project` (scenarios of "Tuning profiles are read into impedance targets"). Proof: `uv run pytest tests/unit/backends/kicad/test_tuning_profiles.py -k read tests/unit/backends/kicad/test_pro_read.py`.
  - 2026-10-08: `test_tuning_profiles.py -k read` and `test_pro_read.py` passed (`test_pro_read.py::test_codes` counts 22 codes).
- [x] 4.3 Build the design with both targets for each major in `tests/kicad/impedance/test_impedance_rules.py -k built`, with one track drawn 50 µm narrower (the last two clauses of "Impedance targets pass the oracle"). Proof: `uv run pytest tests/kicad/impedance -rA -k built` on the local KiCad 10.0.6 and inside the pinned 9.0.9 image.
  - 2026-10-08: written: `test_impedance_rules.py::test_built` and `_zbench.built_run` (the design of `tests/_zdesign.py` built for the running major, its tracks at the targets' geometry, `LED_A` 50 µm narrower in one run, the scoped canary). owed: needs kicad-cli; judged by GitHub CI.
  - 2026-10-08: ticked by CI run 37772583226 on `04ef42a` (all jobs green): `tests/kicad/impedance/test_impedance_rules.py::test_built[False]` and `[True]` passed in the `kicad-9` job (9.0.9: "built exact" without a width finding, "built narrow" with `track_width`) and in the `kicad-10` job (10.0.6).

## 5. Table and command

- [x] 5.1 Write `src/fenolite/exports/impedance.py` (`ImpedanceRow`, `impedance_table`, `COLUMNS`, `render_csv`, `ISSUE_CODES`, `issue`, `EVIDENCE`) and one table per `impedance.*` code (six) in `cli/data/explain.toml` (scenarios of "Impedance table for the fabricator"). Proof: `uv run pytest tests/unit/exports/test_impedance_table.py tests/unit/test_import_graph.py tests/unit/cli/test_explain_cmd.py`.
  - 2026-10-08: `tests/unit/exports/test_impedance_table.py` 6 passed; `test_import_graph.py` and `test_explain_cmd.py` passed. `exports.impedance.ISSUE_CODES` joins `explain.TABLES`.
- [x] 5.2 Write `src/fenolite/cli/cmd_impedance.py` without `--estimate`, and its section in `docs/cli-contract.md` (scenarios "Built project", "Confirmation required" and "Project without targets"); register it so that the consistency test, the contract page and `fenolite capabilities` name it, and refuse an Altium document as `bom` does. Proof: `uv run pytest tests/unit/cli/test_impedance_cmd.py tests/consistency tests/unit/cli -k "impedance or capabilities or contract"`.
  - 2026-10-08: `tests/unit/cli/test_impedance_cmd.py` 8 passed; `tests/consistency` and `tests/unit/cli -k "impedance or capabilities or contract"` passed (54); an Altium document gets the error `bom` gives.

## 6. Estimates

- [x] 6.1 Write the three forms of `src/fenolite/analysis/impedance.py` with their named constants, the range test and the rounding, and the independent `math` computations and cross-checks of the tests (scenarios "Microstrip of the bench", "Stripline against the exact thin strip", "Offset form at equal heights"). Proof: `uv run pytest tests/unit/analysis/test_impedance.py tests/unit/analysis/test_report.py -k "impedance or no_float"`.
  - 2026-10-08: `tests/unit/analysis/test_impedance.py tests/unit/analysis/test_report.py` 42 passed (the bench microstrip 50 763 mΩ; the stripline within 1 % of the exact thin strip for w/b 0.1 to 2; the offset form equal at equal heights).
- [x] 6.2 Add `dielectric_between`, `estimate` and `solve_width`, and `--estimate` to the command with its codes and evidence (scenarios "No estimate for a pair" and "Estimates"). Proof: `uv run pytest tests/unit/analysis/test_impedance.py tests/unit/cli/test_impedance_cmd.py -k estimate`.
  - 2026-10-08: `test_impedance.py` and `test_impedance_cmd.py -k estimate` passed.
- [x] 6.3 Write the table "Impedance formulas" of `docs/analyses.md` and the rows of `src/fenolite/analysis/PROVENANCE.md` (scenario of "Impedance formula sources are recorded"). Proof: `uv run pytest tests/unit/analysis/test_facts_page.py tests/unit/test_provenance.py`.
  - 2026-10-08: `tests/unit/analysis/test_facts_page.py tests/unit/test_provenance.py` 17 passed (18 constants, one row each).

## 7. Altium

- [x] 7.1 Report targets in the Altium build with the info at `impedance`; check that each derived rule gets c0084's warning and its entry of `result.rules.not_lowered`, that no planned file outside `.fenolite/` changes, and that `build.impedance-layer` is given as in a KiCad build (scenarios "Target in an Altium build" and "Pair target in an Altium build"). Add the `where` value `impedance` to the text of `altium.not-lowered` in `cli/data/explain.toml` and one paragraph to `docs/altium.md`. Proof: `uv run pytest tests/unit/lens/test_altium_rules.py tests/unit/lens/test_altium_issues.py tests/unit/lens/test_altium_build.py -k impedance tests/unit/cli/test_explain_cmd.py`.
  - 2026-10-08: `tests/unit/lens/test_altium_rules.py -k impedance` 3 passed; `tests/unit/lens` passed in full (part of 6015 passed, 34 skipped); `test_explain_cmd.py` 8 passed.

## 8. Documentation

- [x] 8.1 Write `docs/impedance.md` (targets, what each major gets, the table, the estimates and their limits), the "Design rules" part of `docs/dsl.md`, the fact rows of `docs/formats/kicad/project.md`, `rules.md` and `drc.md`, and `docs/evidence/impedance.md` with the probe outcomes. Proof: `uv run pytest tests/consistency tests/unit/test_format_facts.py tests/residue`.
  - 2026-10-08: `tests/consistency tests/unit/test_format_facts.py tests/residue` passed. `docs/evidence/impedance.md` holds the design's measurements as first record; the probes' own outcomes are owed (tasks 1.2, 1.3).
- [x] 8.2 If c0079 or c0080 is on `dev`: add `fenolite impedance` to the command list of the agent guide (c0079) and one tested line for `design.rules.impedance()` and one for `fenolite impedance` to the guide page (c0080), as their coverage tests ask; if neither is, write under this task that their coverage tests will ask for the lines. Proof: the guide tests those changes name (on the day: `uv run pytest tests/unit/agent -q`), or the note under this task.
  - 2026-10-08: c0079 and c0080 are on the branch: `commands.md` and `dsl-reference.md` regenerated (`tools/gen_agent_guide.py`), a section "Impedance targets" with a `fenolite-design` block and a `fenolite-cmd` line in `references/rules.md`, and `Trace` in `DSL_NOT_TAUGHT`. `uv run pytest tests/unit/agent tests/unit/test_agent_skill.py` 93 passed, 10 skipped (no kicad-cli).

## 9. Closing

- [x] 9.1 Run the residue and the fast suite. Proof: `uv run pytest tests/residue tests/corpus/test_manifest.py` (after `git add -A`) and `uv run python tools/residue/scan.py` exit 0; `uv run python tools/gen_schemas.py --check` exits 0; `make check-fast` passes; `openspec validate c0105-impedance-targets --strict --no-interactive` and `openspec validate --all --strict --no-interactive` pass. The full `make check` and the CI run are the coordinator's, once, on the rebased branch at merge; this change's agent does not start a full suite.
  - 2026-10-08: `uv run pytest tests/residue tests/corpus/test_manifest.py` 80 passed, 5 skipped, exit 0 (after `git add -A`); `tools/residue/scan.py` exit 0; every `tools/gen_*.py --check` exits 0; `ruff check`, `ruff format --check` and `pyright src` pass. Open: `make check-fast` was not run (machine shared with release tests; targeted suites ran instead), and the strict openspec validation is open as under task 0.1.
  - 2026-10-08, on `v04` at `09ee580` with the edits of this pass (branch `v04-close-b`): `make check-fast PYTEST_WORKERS=3`: ruff check, ruff format, the guide check, pyright and the residue scan pass, 12761 passed, 30 skipped, exit 0 (no rerun needed: the two timing tests passed). `uv run --isolated --python 3.11 --extra dev pytest tests/unit -q -n 3 -p no:cacheprovider`: 12378 passed, 26 skipped, exit 0 (three workers, as the coordinator asked, for the four of the proof). After `git add -A`: `uv run pytest tests/residue tests/corpus/test_manifest.py` 82 passed, 3 skipped; `uv run python tools/residue/scan.py` 0 hits; `tools/gen_schemas.py --check` and `tools/gen_evidence_matrix.py --check` exit 0. `openspec validate --all --strict --no-interactive`: five ERRORs, all of other changes (c0084, c0085 twice, c0086, c0128; the one of c0108 is gone) and the long-requirement warnings that every change gives, which the coordinator accepts for this release; this change's own `--strict` run gives no ERROR. The full `make check` and the CI run are the coordinator's.
- [x] 9.2 Run the unit suite on Python 3.11 before handing over. Proof: `uv run --isolated --python 3.11 --extra dev pytest tests/unit -q -n 4 -p no:cacheprovider` exits 0.
  - 2026-10-08: owed: the unit suite on Python 3.11 is the coordinator's run (this machine runs targeted tests only).
  - 2026-10-08, on `v04` at `09ee580` with the edits of this pass (branch `v04-close-b`): `make check-fast PYTEST_WORKERS=3`: ruff check, ruff format, the guide check, pyright and the residue scan pass, 12761 passed, 30 skipped, exit 0 (no rerun needed: the two timing tests passed). `uv run --isolated --python 3.11 --extra dev pytest tests/unit -q -n 3 -p no:cacheprovider`: 12378 passed, 26 skipped, exit 0 (three workers, as the coordinator asked, for the four of the proof). After `git add -A`: `uv run pytest tests/residue tests/corpus/test_manifest.py` 82 passed, 3 skipped; `uv run python tools/residue/scan.py` 0 hits; `tools/gen_schemas.py --check` and `tools/gen_evidence_matrix.py --check` exit 0. `openspec validate --all --strict --no-interactive`: five ERRORs, all of other changes (c0084, c0085 twice, c0086, c0128; the one of c0108 is gone) and the long-requirement warnings that every change gives, which the coordinator accepts for this release; this change's own `--strict` run gives no ERROR. The full `make check` and the CI run are the coordinator's.
- [ ] 9.3 Update the evidence: `H-K-PRO-TUNING-DRC` becomes `KICAD-VERIFIED (10.0.x)`, `H-K-DRU-IMPEDANCE` `KICAD-VERIFIED (9.0.x, 10.0.x)` and `H-K-PRO-TUNING-KEYS` per task 1.4, each with its run, or the case that differed; `H-G-AN-ZMS` and `H-G-AN-ZSL` stay `INFERRED`. Proof: `uv run pytest tests/unit/test_provenance.py tests/unit/test_hypotheses_register.py`.
  - 2026-10-08: owed: needs kicad-cli; judged by GitHub CI; the rows stay `INFERRED` until the probes are recorded; `H-G-AN-ZMS` and `H-G-AN-ZSL` stay `INFERRED` with the results of 2026-10-08.
  - 2026-10-08: `H-K-DRU-IMPEDANCE` is `KICAD-VERIFIED (9.0.x, 10.0.x)` from CI run 37772583226 on `04ef42a` (all jobs green), and its fact row in `docs/formats/kicad/rules.md` follows. `H-K-PRO-TUNING-DRC` stays `INFERRED`: its eight probes passed on 10.0.6, but its criterion also asks for `pro-tuning-gap-clearance-rule` recorded (task 1.3). `H-K-PRO-TUNING-KEYS` stays `INFERRED`: task 1.4 is deferred to the next release by the maintainer's decision of 2026-10-08. `H-G-AN-ZMS` and `H-G-AN-ZSL` stay `INFERRED`. `uv run pytest tests/unit/test_provenance.py tests/unit/test_hypotheses_register.py`: 44 passed, exit 0.
- [x] 9.4 Add to `CHANGELOG.md` under Unreleased: "Impedance targets per net class or pair (`design.rules.impedance()`, `trace()`), checked by derived rules on KiCad 9 and 10 and written as KiCad 10 tuning profiles; build warnings for shadowed rules, class values, gaps and an unmarked stack-up; `fenolite impedance` with the table for the fabricator and `INFERRED` estimates of single-ended lines; an Altium build keeps targets in the model and names them; 0.2.x and 0.3.0 cannot read a `rules.json` that carries the key `impedance`". Update the c0105 row of `docs/roadmap.md` (the table of "v0.4: proposals on other branches", or the milestone table if the section was folded into it by then). Proof: `git diff --stat CHANGELOG.md docs/roadmap.md` lists both files; `grep -n "c0105" docs/roadmap.md` shows the row.
  - 2026-10-08: the CHANGELOG line is at the end of `[Unreleased]`. Open: the c0105 row of `docs/roadmap.md` holds its id and slug only, as every row of that table; its update is the coordinator's.
  - 2026-10-08: the CHANGELOG line of task 9.4 is in `[Unreleased]`, and a line under `### Changed` records the probes and the deferral; the row of c0105 in `docs/roadmap.md` says it is built and that the GUI save is deferred, with a paragraph "c0105 on `v04`". `git diff --stat CHANGELOG.md docs/roadmap.md` lists both; `grep -n "c0105" docs/roadmap.md` shows the row.
