lgili/Fenolite/openspec/changes/c0107-route-planes-layers/tasks.md

## 0. Entry check

- [x] 0.1 Read the living `specctra-dsn`, `routing`, `cli-contract`, `rules-model`, `kicad-file-backend`, `design-dsl` and `kicad-oracle` specs and `openspec list`. Write under this task, with the date: that `0.3.0` is released and c0084 archived (else stop: "Rule lowering table" must be living text); that c0100 and c0108 are archived (else stop; then regenerate the MODIFIED "Planes in a build" from c0100's text, keeping its hint and six-layer scenario, and re-apply Decision 2); whether any change archived since `9aba2dff` touched "Rule kinds and limits", "Rule constructor in the DSL", "Design files are written from the model" or "Specctra issue codes and facts" (then regenerate that delta from the living text, full text and every scenario, with only this change applied); whether `RuleKind` still holds twelve kinds and `docs/evidence/sources.md` still leaves S-0660 free. c0068 and c0071 are archived since 2026-10-05. Proof: `openspec validate c0107-route-planes-layers --strict --no-interactive` passes after any regeneration.
  - Done: 2026-10-08. `0.3.0` is not released, and c0084, c0100 and c0108 are implemented on the integration branch `v04` and not archived; the maintainer's instruction for this night replaces the two stops, and the deltas are written against the branch. "Planes in a build" is regenerated from c0100's delta (its hint and its six-layer scenario kept, Decision 2 applied). The four other MODIFIED requirements equal the living text with only this change applied (compared requirement by requirement); c0104 alone holds a delta of "Rule kinds and limits", and it lands later; c0109, which landed the same night, adds requirements beside "Design files are written from the model" and modifies none of these. `RuleKind` held twelve kinds and S-0660 was free. `openspec validate c0107-route-planes-layers --strict --no-interactive` passes.

## 1. Probe and register

- [x] 1.1 Add the rows `H-G-DSN-LAYERS`, `H-G-DSN-PLANE`, `H-G-DSN-CLEARANCE`, `H-G-DSN-EDGE`, `H-K-LAYER-POWER`, `H-K-DRU-NOTRACKS`, `H-K-FANOUT` and `H-K-KRT-PLANES` to `docs/hypotheses.md` (level `INFERRED`, the tests and criteria of `design.md`, the measurements of 2026-10-05 as first record). Proof: `uv run pytest tests/unit/test_hypotheses_register.py tests/unit/test_provenance.py`; `grep -cE '^\| (H-G-DSN-(LAYERS|PLANE|CLEARANCE|EDGE)|H-K-(LAYER-POWER|DRU-NOTRACKS|FANOUT|KRT-PLANES)) ' docs/hypotheses.md` prints `8`.
  - Done: 2026-10-08. The eight rows are in `docs/hypotheses.md` (the grep prints `8`), with a ninth, `H-G-DSN-EDGE-2`, the successor of the refuted edge row; `tests/unit/verify/test_register.py` counts 17 `H-G-DSN-*` rows.
- [x] 1.2 Author `tests/routing/_planebench.py`: the four-layer bench of the design (script, in-process build for targets 9 and 10, with and without `planes=`, and a variant with one hand-made dog-bone per SMD pad of `GND` and `VCC`), built from the offline catalog's `SOIC_8`, `Chip_0603`, `Header_1x4_P2.5` and `Header_1x2_P2.5` so that it needs no KiCad library; the two-layer edge bench whose shortest route runs along the edge; a row in `tests/data/MANIFEST.toml` for any stored file. Proof: `uv run pytest tests/unit/routing/test_planebench.py` (the bench builds, its pads and zones are those of the design) and `uv run pytest tests/residue`.
  - Done: 2026-10-08. `tests/routing/_planebench.py` (two 1x4 headers and two 1x2 headers of the catalog; `hv_near` for the class-to-class gate; the edge bench with a slot), no stored file; `tests/conftest.py` puts `tests/routing` on the import path. `uv run pytest tests/unit/routing/test_planebench.py`: 4 passed.
- [x] 1.3 Write `tests/kicad/board/test_layer_power.py` (probes `pcb-layer-power-t9`, `-t10`, `-resave`, with the `signal` board as control) and add the `dru-kind-no_tracks` bench to `tests/kicad/rules/test_rule_kinds_new.py` with a hand-written rule and the scoped canary; register both in `tests/kicad/_probes.py`. Proof: `uv run pytest tests/kicad/board/test_layer_power.py tests/kicad/rules/test_rule_kinds_new.py -k "power or no_tracks" -rA` on the local KiCad 10.0.6 and inside the pinned 9.0.9 image; `FENOLITE_PROBES_WRITE=1` records them in both probe files.
  - Open: the probes `pcb-layer-power-t9`, `-t10`, `-resave` and `dru-kind-no_tracks` are registered (`tests/kicad/board/_planecases.py`, `tests/kicad/rules/_kindcases.py`) and recorded in `10.0.6.json` from real runs on the local `kicad-cli` 10.0.6 (`equal`, `equal`, `equal`, `present`; 3 and 1 tests passed); the 9.0.9 half was not run on 2026-10-08 (no image run that night; the coordinator records every lane's probes for 9.0.9 in one image run). The `no_tracks` bench uses rules written by `lower_rules` from the start (task 3.5).
  - 2026-10-08: ticked by the local run of 2026-10-08 in the pinned 9.0.9 image (`kicad/kicad:9.0.9@sha256:e638b79b…`, linux/amd64, branch `v04-k9-probes`; whole `tests/kicad` without the corpus: 777 passed, 4 failed, 784 skipped, 1 xfailed; `tests/kicad/test_probe_results.py` passed on the 536 probes of major 9): `pcb-layer-power-t9` = `equal` and `dru-kind-no_tracks` = `present` on 9.0.9, recorded in `9.0.9.json`; `test_layer_power.py` 2 passed, 1 skipped (the re-save), `test_rule_kinds_new.py` 10 passed.
- [x] 1.4 Write `tests/routing/test_freerouting_planes.py` (marker `needs_freerouting`) with the variants of the Context, made by editing the tree that today's `write_dsn` gives: `dsn-power-layers`, `dsn-plane-alone`, `dsn-plane-fanout`, `dsn-use-layer`, `dsn-class-class` (judged by KiCad's DRC), `dsn-layer-rule`, `dsn-keepout`, `dsn-edge-band`. If an outcome differs from the Context, stop and write what Freerouting showed into the register row before any code. Proof: `FENOLITE_FREEROUTING_JAR=<jar> uv run pytest tests/routing/test_freerouting_planes.py -rA` with Java 25; outcomes recorded in `docs/evidence/routing/freerouting-2.4.1.json` and `docs/evidence/routing.md`.
  - Done: 2026-10-08 with the local jar of the routing image, 2.4.1 (sha256 `00ba5b87…`, not the pinned file), and Java 26.0.2: the proof with the pinned jar is left to the `routing` job. The variants are made with the writer's arguments from the start (the writer existed when the jar was at hand), but the edge bands, which the test adds to the file. Outcomes in `docs/evidence/routing/freerouting-2.4.1.json` and `docs/evidence/routing.md`: `dsn-power-layers`, `dsn-use-layer`, `dsn-plane-fanout`, `dsn-class-class`, `dsn-keepout` = `equal`; `dsn-plane-alone` = `open`; `dsn-layer-rule` = `different` (6 of 20 segments narrowed at pins) and `dsn-edge-band` = `different` (the route of a 2 mm passage is lost): both are written into their register rows, and the second takes Decision 11's fallback. 9 passed.
- [x] 1.5 With a KiCadRoutingTools checkout at the pinned tag, extend `tests/routing/test_krt_gate.py -k planes` and record `H-K-KRT-PLANES`; without one, write "not run" into the row. Proof: `uv run pytest tests/routing/test_krt_gate.py -k planes -rA` with `FENOLITE_KRT` set, or the row's text.
  - Open: no KiCadRoutingTools checkout on this machine on 2026-10-08; the row of `H-K-KRT-PLANES` says "not run", and `tests/routing/test_krt_gate.py -k planes` is not written.
  - 2026-10-08: written and run: `tests/routing/test_krt_gate.py::test_planes` (marked `needs_router` only; the other tests of the file are now marked `needs_kicad` one by one) routes the plane bench through `fenolite route --router kicadroutingtools`, with a `no_tracks` rule that keeps `SIG` off `B.Cu`, and as controls without the rule and without `planes=`. Run with a checkout of the tag `v0.22.1` (commit `023d3f79`; `grid_router` built from the tag with `build_router.py`, because the release asset could not be downloaded in this session; Linux x86_64, CPython 3.12): `FENOLITE_KRT=… uv run pytest tests/routing/test_krt_gate.py -k planes -rA`: 2 passed; `krt-planes-t9` and `krt-planes-t10` = `inconclusive`: all 23 router tracks on `F.Cu` with the rule, 23 without it and 22 without `planes=`, so the bench never tempts the tool onto the plane layers or `B.Cu`. Recorded in `H-K-KRT-PLANES` (stays `INFERRED`) and `docs/evidence/routing.md`; the `routing` jobs of CI run the test too.

## 2. Plane layers

- [x] 2.1 Add `plane_layers` and `with_plane_types` to `src/fenolite/backends/kicad/layers.py` with `tests/unit/backends/kicad/test_layers.py -k plane` (scenarios of "Plane layers of a board"). Proof: `uv run pytest tests/unit/backends/kicad/test_layers.py tests/unit/test_import_graph.py`; `uv run pyright src`.
  - Done: 2026-10-08. `plane_layers`, `with_plane_types` and three tests in `tests/unit/backends/kicad/test_layers.py`; pyright clean.
- [x] 2.2 Lower `planes=` for KiCad: `build_design(…, planes=…)` sets the row types after the merge, `plane_issues(planes, design)` gives `build.plane-zone-missing`, `build.plane-not-lowered` leaves the table, `cmd_build` passes the mapping; in `src/fenolite/cli/data/explain.toml` remove the entry `build.plane-not-lowered` and add `build.plane-zone-missing` (meaning, fix naming `design.zone`, see); tests in `tests/unit/lens/test_build_planes.py` (scenarios of "Planes in a build", the Altium one included). Proof: `uv run pytest tests/unit/lens tests/unit/cli -k "plane or build or explain" tests/consistency`.
  - Done: 2026-10-08. The scenarios are in `tests/unit/cli/test_build_command.py` (five plane tests, on the command, which is where the board is written and merged) and `tests/unit/lens/test_build_issues.py`, not in a new `test_build_planes.py`. A design without planes builds the same bytes: `examples/blink_2layer` and `examples/board_40parts`, built for KiCad 9 and 10 with the code of the base and with this change, are equal file by file (18 and 20 files per target).
- [x] 2.3 Write the row-type facts into `docs/formats/kicad/board.md` with `H-K-LAYER-POWER`, and the KiCad target of `planes=` into `docs/dsl.md`. Proof: `uv run pytest tests/unit/test_format_facts.py tests/consistency`.
  - Done: 2026-10-08. `docs/formats/kicad/board.md` (two fact rows and "Plane layers"), `docs/dsl.md`, `docs/lens.md` ("Plane layers across rebuilds").

## 3. Track layer rules

- [x] 3.1 Add `no_tracks` to `RuleKind`, last, and regenerate the rules schema; in the same commit add its rows to the KiCad tables (`KIND_SUPPORT`, `KIND_SELECTORS`, empty support until task 3.2) and to the Altium table (task 3.6), and change the count in `tests/unit/dsl/test_minimums.py` from 12 to 13, so no suite is red between tasks. Write into `docs/design-model.md` the sentence "Releases 0.2.x and 0.3.x cannot read a model document that holds a `no_tracks` rule". Proof: `uv run pytest tests/unit/model tests/unit/test_schema_drift.py tests/unit/dsl/test_minimums.py tests/unit/backends/altium/test_rulemap.py tests/unit/backends/kicad/test_rulemap_kinds.py`; `uv run python tools/gen_schemas.py --check` exits 0; `grep -n "cannot read a model document that holds a .no_tracks. rule" docs/design-model.md` prints the line.
  - Done: 2026-10-08. `no_tracks` is last in `RuleKind`; `schemas/fenolite.model.v0/rules.json` regenerated; the old document `tests/data/model/v0.2.1/twelve_kinds.rules.json`, written by the code before the change, keeps its bytes.
- [x] 3.2 Add the `no_tracks` row to `rulemap` and `lowering`: `disallow track`, no limit, its grammar, `KIND_SUPPORT` pinned to the probe files (scenarios of "Track layer rules"). Proof: `uv run pytest tests/unit/backends/kicad/test_rulemap.py tests/unit/backends/kicad/test_lowering.py -k "no_tracks or kind_support or codes"`.
  - Done: 2026-10-08. `KIND_SUPPORT["no_tracks"]` is `{10}`: it follows the probe files, and the probe of 9.0.9 is not recorded yet (design, "Found on 2026-10-08", 5). Tests in `tests/unit/backends/kicad/test_rulemap_no_tracks.py` and `test_rulemap_kinds.py`.
- [x] 3.3 Lift `disallow track` with one layer name in `read_rules`, and keep the other `disallow` forms opaque (scenario "Lift and opaque forms"). Proof: `uv run pytest tests/unit/backends/kicad/test_dru.py -k no_tracks`.
  - Done: 2026-10-08. `test_rulemap_no_tracks.py -k lift` (the proof's `test_dru.py -k no_tracks` selects nothing: the tests of the kind are in the new file).
- [x] 3.4 Accept `no_tracks` in `design.rules.rule()` without a limit and with layers (scenarios of "Track layer rules in the DSL"). Proof: `uv run pytest tests/unit/dsl/test_rule_constructor.py -k no_tracks tests/unit/dsl`.
  - Done: 2026-10-08. `tests/unit/dsl/test_rule_constructor.py -k no_tracks`: 6 passed.
- [x] 3.5 Switch the `dru-kind-no_tracks` bench of task 1.3 to rules written by `lower_rules`. Proof: `uv run pytest tests/kicad/rules/test_rule_kinds_new.py -k no_tracks -rA` on the local KiCad 10.0.6 and inside the pinned 9.0.9 image; the probe stays `present` in both files.
  - Open: the bench is written by `lower_rules` and `dru-kind-no_tracks` is `present` on the local `kicad-cli` 10.0.6; the 9.0.9 half was not run on 2026-10-08 (no image run that night; the coordinator records every lane's probes for 9.0.9 in one image run).
  - 2026-10-08: ticked: `test_no_tracks_rule` passes inside the pinned 9.0.9 image with the rules written by `lower_rules`, and the probe is `present` in both files. `KIND_SUPPORT["no_tracks"]` gained 9 in the same commit, so a target-9 build writes the kind.

- [x] 3.6 The Altium side, fact row first. Open Altium's public documentation of its routing-layers rule, add the row S-0660 to `docs/evidence/sources.md` (address, licence, what was read, date) and the row of `no_tracks` to "The lowering table" of `docs/formats/altium/pcb-copper.md` (status `no-counterpart`, source S-0660, label `INFERRED`); then add `RuleRow("no_tracks", "no-counterpart", note=…)` to `backends/altium/rulemap.TABLE`, and the test of the scenario "A track layer rule in an Altium build" to `tests/unit/lens/test_altium_rules.py`. Proof: `uv run pytest tests/unit/backends/altium/test_rulemap.py tests/unit/lens/test_altium_rules.py -k "complete or no_tracks" tests/unit/test_format_facts.py tests/unit/test_provenance.py`; `grep -c '^| S-0660 ' docs/evidence/sources.md` prints `1`.
  - Done: 2026-10-08. S-0660 is Altium's page "Routing Rule Types" (section "Routing Layers"), read through the fetch tool; the row and its paragraph are in `docs/formats/altium/pcb-copper.md`; the test is `test_no_tracks_rule_is_reported_and_not_written`.

## 4. Routing job

- [x] 4.1 Add `RoutingJob.plane_layers` and `JobNet.layers`, and write `src/fenolite/routing/layers.py` with `tests/unit/routing/test_layers.py` (scenarios "Allowed layers from track layer rules" and "Ignored rule"). Proof: `uv run pytest tests/unit/routing tests/unit/test_import_graph.py`; `uv run pyright src`.
  - Done: 2026-10-08. `layers` and `plane_layers` come before c0109's `tier` and `budget`.
- [x] 4.2 Make the direct router skip plane layers and keep to `layers`; give the KiCadRoutingTools plugin `route.constraint-not-sent`; add the four codes (`route.plane-net`, `route.no-layer`, `route.constraint-not-sent`, `route.project-unread`) to `routing.codes.ISSUE_CODES`, to `docs/cli-contract.md` and, each with meaning, fix and see, to `src/fenolite/cli/data/explain.toml` (scenarios "Direct router off a plane layer" and "KiCadRoutingTools told nothing"). Proof: `uv run pytest tests/unit/routing/test_direct.py tests/unit/routing/test_routingtools.py tests/unit/cli/test_explain_cmd.py tests/consistency`.
  - Done: 2026-10-08. The KiCadRoutingTools plugin also writes a rule set that `route` read from a rules file with `write_rules` (found when c0109's budget test met the rules that `route` now reads).

## 5. Specctra writer

- [x] 5.1 Before the first edit of `dsn.py`, record the texts of the bench without rules and of the blink with today's writer under `tests/data/specctra/`; then write power layers and planes, and `specctra.plane-skipped` (scenarios of "Plane layers in design files" and "Same text without planes, layers and rules"). Proof: `uv run pytest tests/unit/backends/specctra/test_dsn_planes.py tests/unit/backends/specctra/test_dsn.py`.
  - Done: 2026-10-08. `tests/data/specctra/c0107_before_planebench_norules.dsn` and `c0107_before_blink_t10.dsn` were recorded before the first edit of `dsn.py`.
- [x] 5.2 Write `use_layer` and the class splits (scenarios of "Routing layers in design files"). Proof: `uv run pytest tests/unit/backends/specctra/test_dsn_planes.py -k "use_layer or split or plane_layer"`.
  - Done: 2026-10-08. The group that may use every signal layer keeps the class's name (design, "Found on 2026-10-08", 4).
- [x] 5.3 Lower the rules table: raised clearances, `class_class`, widths and `layer_rule`, `specctra.rule-widened`, `specctra.rule-not-sent` (scenarios of "Routing rules in design files" but the edge bands). Proof: `uv run pytest tests/unit/backends/specctra/test_dsn_rules.py`.
  - Done: 2026-10-08. `tests/unit/backends/specctra/test_dsn_rules.py`.
- [x] 5.4 Write the edge bands (scenario "Edge bands"). If `dsn-edge-band` of task 1.4 was not `equal`, apply the fallback of Decision 11 instead and record it under this task. Proof: `uv run pytest tests/unit/backends/specctra/test_dsn_rules.py -k edge`.
  - Done: 2026-10-08 by the fallback of Decision 11: `dsn-edge-band` was `different` (the route of the 2 mm passage is lost with bands; with 4 mm they hold), so no band is written and an `edge_clearance` rule gives `specctra.rule-not-sent`; the requirement and its scenario are corrected. `uv run pytest tests/unit/backends/specctra/test_dsn_rules.py -k edge` passes.
- [x] 5.5 Extend `ISSUE_CODES` and the closed-table test, add the entries of `specctra.plane-skipped`, `specctra.rule-not-sent` and `specctra.rule-widened` to `src/fenolite/cli/data/explain.toml`, record the one-pad `unconnected-(` rule of the Network bullet as a row (with the test `-k unconnected`, which exists), and add the rows of the measured facts to `docs/formats/specctra/dsn.md` (power layers, planes, `use_layer`, `class_class`, `layer_rule`, keep-out paths, the boundary margin) with S-0224 or S-0221/S-0222 and their hypotheses. Proof: `uv run pytest tests/unit/backends/specctra -k "codes or unconnected" tests/unit/cli/test_explain_cmd.py tests/unit/test_format_facts.py`.
  - Done: 2026-10-08.

## 6. Freerouting plugin

- [x] 6.1 Pass `plane_layers` and `net_layers` from the job to `write_dsn` (scenario "Recorded design file"). Proof: `uv run pytest tests/unit/routing/test_freerouting.py`.
  - Done: 2026-10-08. The plugin of c0109 writes one file per tier: each gets the plane layers and the layer sets.
- [x] 6.2 Switch `tests/routing/test_freerouting_planes.py` from tree edits to the writer's arguments; each outcome must equal the one of task 1.4. Proof: `FENOLITE_FREEROUTING_JAR=<jar> uv run pytest tests/routing/test_freerouting_planes.py tests/routing/test_freerouting_gate.py -rA`.
  - Done: 2026-10-08 with the local jar of the routing image, 2.4.1 (sha256 `00ba5b87…`, not the pinned file), and Java 26.0.2; the planes file used the writer's arguments from the start. `tests/routing/test_freerouting_planes.py`: 9 passed; `tests/routing/test_freerouting_gate.py`, the gate of c0023 and c0109 on the changed writer and plugin: 9 passed.

## 7. Plane fan-out

- [x] 7.1 Write the candidate search of `src/fenolite/backends/kicad/fanout.py`: directions, distances, the via and track tests, the zone, edge, keep-out and hole tests, with unit tests on the bench (scenarios "One dog-bone per SMD pad" and "A pad without room"). Proof: `uv run pytest tests/unit/backends/kicad/test_fanout.py -k "bench or room"`; `uv run pyright src`.
  - Done: 2026-10-08.
- [x] 7.2 Add joined pads, `plane_nets`, `FanoutPlan`, ids, `FANOUT_ISSUE_CODES` and `EVIDENCE`; name `("fenolite.backends.kicad.fanout", "FANOUT_ISSUE_CODES")` in `cli.explain.TABLES` and add the entry `kicad.fanout.failed` to `explain.toml` (scenarios "Pads already joined" and "Deterministic"). Proof: `uv run pytest tests/unit/backends/kicad/test_fanout.py tests/unit/cli/test_explain_cmd.py tests/unit/test_import_graph.py`.
  - Done: 2026-10-08. `tests/unit/backends/kicad/test_fanout.py`: 12 passed; the two-process run with `PYTHONHASHSEED` 1 and 2 gives equal ids.
- [x] 7.3 Change `cli/cmd_route.py`: rules from `design_rules`, the edge minimum as a rule, plane layers and nets, the fan-out step, `--no-plane-fanout`, `JobNet.layers` and `route.no-layer`, the write rule and the two result keys (scenarios of "Plane nets in the route command"). Proof: `uv run pytest tests/unit/cli/test_route_cmd.py tests/unit/cli/test_hermetic_examples.py tests/consistency`.
  - Done: 2026-10-08. `tests/unit/cli/test_route_cmd.py`: eight plane tests beside those of c0108 and c0109.
- [x] 7.4 Write `tests/kicad/routing/test_fanout_oracle.py` with the probes `route-fanout-t9` and `route-fanout-t10`. If a probe is not `equal`, stop and write what KiCad showed into the row of `H-K-FANOUT`. Proof: `uv run pytest tests/kicad/routing/test_fanout_oracle.py -rA` on the local KiCad 10.0.6 and, for the target-9 board filled locally, inside the pinned 9.0.9 image.
  - Open: `route-fanout-t10` is `equal` on the local `kicad-cli` 10.0.6 (1 passed; the plane nets alone are selected, design "Found on 2026-10-08", 7); `route-fanout-t9` is registered and the 9.0.9 half was not run on 2026-10-08 (no image run that night; the coordinator records every lane's probes for 9.0.9 in one image run).
  - 2026-10-08: still open. Inside the pinned 9.0.9 image `route-fanout-t9` is `inconclusive` and the test skips: the container holds no `kicad-cli` 10 for `fenolite fill`. That outcome is recorded in `9.0.9.json`, because the `kicad-9` job runs the same way. With the host's Python, the local 10.0.6 for the fill and `FENOLITE_KICAD_CLI=docker:<the pinned image>` as the judge, `tests/kicad/routing/test_fanout_oracle.py` passes (`equal`). The outcome of the probe depends on the machine: it needs a decision (a committed filled fixture, as c0100 did, or a probe that is not pinned).
  - Done: 2026-10-08, by the committed filled fixtures (design, "Found on 2026-10-08", 12). `uv run pytest tests/kicad/routing/test_fanout_oracle.py -rA` on the local 10.0.6: 3 passed (the target-10 fan-out, and the two fixtures equal to this run's fill of the target-9 boards); inside the pinned 9.0.9 image: 1 passed, 2 skipped (the two fixture tests need 10.0), `route-fanout-t9` = `equal` on the fixtures and recorded so in `9.0.9.json`. The row of `H-K-FANOUT` is `KICAD-VERIFIED (9.0.x, 10.0.x)`; the `kicad-9` job of CI has still to confirm it.

## 8. Documentation

- [x] 8.1 Update `docs/routing.md` (plane layers, the fan-out rules, what each router is given, the rules sent and not sent, the 100-part record), `docs/cli-contract.md` (`--no-plane-fanout`, `result.plane_layers`, `result.plane_fanout`, the codes), `docs/dsl.md` (`no_tracks`, and one sentence that tells the rule kind from the `no_tracks` flag of a keep-out) and `docs/formats/kicad/rules.md` (the `disallow track` row); in `docs/routing.md` one paragraph tells the plane fan-out of this change from Freerouting's own fanout stage. Proof: `uv run pytest tests/consistency tests/unit/test_repo_layout.py tests/residue`.
  - Done: 2026-10-08. Also `docs/lens.md`, `docs/altium.md`, `docs/design-model.md`, `docs/formats/specctra/dsn.md` and `docs/evidence/routing.md`.
- [x] 8.2 If c0080 is archived, add one tested line to its routing guide page: `route` on a board with `planes=` and how to read `result.plane_fanout.failed`. Proof: the guide's tested-recipe test of c0080, run on that page.
  - Open: c0080 is not archived on 2026-10-08, so its routing guide page gets no line from this change.
  - 2026-10-08: c0080 is on the branch (not archived; it counts as available): the routing page of the guide (`src/fenolite/agent/skill/references/routing.md`) gains the tested command line `fenolite route board4/build --router freerouting --confirm --json --fields result.plane_fanout` and the bullet "Planes" (a board with `planes=`, the fan-out, how to read `result.plane_fanout.failed`). `uv run pytest tests/unit/agent tests/unit/test_agent_skill.py`: 93 passed, 10 skipped (no `kicad-cli`), exit 0.

## 9. Closing

- [x] 9.1 Run the residue and the tests of every touched package, and the unit suite on Python 3.11. Proof: `make check-fast`; `uv run pytest tests/unit/routing tests/unit/backends/specctra tests/unit/backends/kicad tests/unit/backends/altium tests/unit/cli tests/unit/lens tests/unit/dsl -q`; `uv run --isolated --python 3.11 --extra dev pytest tests/unit -q -n 4 -p no:cacheprovider` exits 0; after `git add -A`, `uv run pytest tests/corpus/test_manifest.py tests/residue`; `uv run python tools/residue/scan.py` exits 0; `openspec validate c0107-route-planes-layers --strict --no-interactive` passes. The full `make check` is the coordinator's, once, at the merge.
  - Open in one part: the unit suite on Python 3.11 was not run on 2026-10-08 (the rules of the night leave the whole-suite runs to the coordinator). The rest ran on the rebased commit; the counts are in the hand-over report of the change.
  - 2026-10-08, on `v04` at `09ee580` with the edits of this pass (branch `v04-close-b`): `make check-fast PYTEST_WORKERS=3`: ruff check, ruff format, the guide check, pyright and the residue scan pass, 12761 passed, 30 skipped, exit 0 (no rerun needed: the two timing tests passed). `uv run --isolated --python 3.11 --extra dev pytest tests/unit -q -n 3 -p no:cacheprovider`: 12378 passed, 26 skipped, exit 0 (three workers, as the coordinator asked, for the four of the proof). After `git add -A`: `uv run pytest tests/residue tests/corpus/test_manifest.py` 82 passed, 3 skipped; `uv run python tools/residue/scan.py` 0 hits; `tools/gen_schemas.py --check` and `tools/gen_evidence_matrix.py --check` exit 0. `openspec validate --all --strict --no-interactive`: five ERRORs, all of other changes (c0084, c0085 twice, c0086, c0128; the one of c0108 is gone) and the long-requirement warnings that every change gives, which the coordinator accepts for this release; this change's own `--strict` run gives no ERROR. The full `make check` and the CI run are the coordinator's.
- [x] 9.2 Update the evidence labels: the eight rows rise to the levels of the design's table with their scope, or record what was refuted and the fallback taken; the fact rows of `docs/formats/specctra/dsn.md` and `docs/formats/kicad/board.md` follow; `dsn.EVIDENCE` names the new hypotheses. Proof: `uv run pytest tests/unit/test_provenance.py tests/unit/test_hypotheses_register.py tests/kicad/test_probe_results.py tests/unit/test_format_facts.py`.
  - Open: the rows of the Freerouting hypotheses hold their levels (`H-G-DSN-LAYERS`, `-PLANE` and `-EDGE-2` `ORACLE-VERIFIED`, local run; `-CLEARANCE` `INFERRED`, partly refuted; `-EDGE` refuted), the fact rows follow and `dsn.EVIDENCE` names them; the three KiCad rows stay `INFERRED` because the 9.0.9 half was not run on 2026-10-08 (no image run that night; the coordinator records every lane's probes for 9.0.9 in one image run); `H-K-KRT-PLANES` is not run.
  - 2026-10-08: the eight rows hold their levels: `H-K-LAYER-POWER`, `H-K-DRU-NOTRACKS` and `H-K-FANOUT` `KICAD-VERIFIED (9.0.x, 10.0.x)` (the `kicad-9` job of CI run 37772583226 on `04ef42a` (all jobs green) passed `test_layer_power.py`, `test_rule_kinds_new.py` and `test_fanout_oracle.py` on 9.0.9), the Freerouting rows as recorded under task 1.4, `H-K-KRT-PLANES` `INFERRED` with the outcome `inconclusive` of task 1.5. The 9.0.9 fact rows of `docs/formats/kicad/board.md` and `rules.md` name that CI run; `dsn.EVIDENCE` names the new hypotheses; `backends.kicad.fanout.EVIDENCE` is `KICAD-VERIFIED` (with `docs/evidence/matrix.md` regenerated). `uv run pytest tests/unit/test_provenance.py tests/unit/test_hypotheses_register.py tests/kicad/test_probe_results.py tests/unit/test_format_facts.py`: 66 passed, 1 skipped (no `kicad-cli` here; the probe test passed in both CI jobs).
- [x] 9.3 Add to `CHANGELOG.md` under Unreleased: "`route` joins the SMD pads of plane nets to their planes with fan-out vias before the router runs, and never traces a plane net; copper layers of type `power` are plane layers, and `board(planes=…)` now sets that type on KiCad boards; the Specctra file declares plane layers and planes, keeps classes to their layers, and carries class-to-class clearance, per-layer widths and the edge clearance; new rule kind `no_tracks`, which an Altium build reports as not lowered. **Releases 0.2.x and 0.3.x cannot read a model document that holds a `no_tracks` rule.** `build.plane-not-lowered` is no longer given." In `docs/roadmap.md`, section "v0.4", say that c0107 is built (the page has an id and slug table, no status row). Proof: `grep -n "cannot read a model document that holds" CHANGELOG.md` prints the line; `git diff --stat CHANGELOG.md docs/roadmap.md` lists both files.
  - Open in one part: the changelog line is at the end of `[Unreleased]`; `docs/roadmap.md` is not edited (the rules of the night leave it to the coordinator).
  - 2026-10-08: the changelog line of task 9.3 is in `[Unreleased]` (the `grep` prints it), and a line under `### Changed` records `test_planes`, the fan-out level and the guide line; `docs/roadmap.md`: the row of c0107 says it is built on `v04`, with a paragraph "c0107 on `v04`". `git diff --stat CHANGELOG.md docs/roadmap.md` lists both.
