lgili/Fenolite/openspec/changes/c0108-route-open-nets/tasks.md

## 0. Entry check

- [x] 0.1 Read the living `routing`, `cli-contract`, `board-analyses`, `design-model`, `kicad-file-backend`, `design-dsl`, `manual-copper` and `kicad-oracle` specs and `openspec list`. Read also `altium-pcb-writer`, `altium-build`, `altium-import` and `geometry-kernel`. Write under this task, with the date: that `0.3.0` is released and c0085, c0128, c0124, c0132 and c0126 are archived (else stop); then regenerate the MODIFIED "Via records" from the living text, full text and every scenario, with only the flag byte and the `locked` argument of this change applied; whether "Net selection", "Route command" or "PCB units and record framing" changed since `9aba2dff` (then regenerate that delta the same way); whether c0112 added a field to `Via` (then `locked` comes after it); whether `docs/evidence/sources.md` still leaves S-0661 free. c0066, c0068 and c0089 are archived: task 5.1 is not deferred, and `locked` comes after `kind` and `layers` on the intents. Proof: `openspec validate c0108-route-open-nets --strict --no-interactive` passes after any regeneration.
  - 2026-10-07, on the base `f36e08d9` (the integration branch of v0.4): **the prerequisites are not met.** `0.3.0` is not released (the changelog ends at `0.2.1`), and c0085, c0128, c0124, c0132 and c0126 are open changes, not archived; c0126 has no task done, so its fixture `tests/data/model/v0.2.0/blink_2layer.board.json` does not exist. The coordinator asked to do what does not need them, so the change was implemented on this base. Read: the twelve living specs and `openspec list`. "Net selection", "Route command", "PCB units and record framing" and "Via records" are unchanged in `openspec/specs` since `9aba2dff` (`git diff --stat 9aba2dff f36e08d9 -- openspec/specs` lists `altium-build`, `altium-schematic-writer` and `release-gate` only), and each of the four MODIFIED deltas is the full living requirement with only this change's lines changed (compared line by line). "Via records" is therefore still generated from the living text, not from the text of c0085 and c0128: **whichever of those archives after this delta must regenerate it.** c0112 is not implemented, so `Via.locked` is the last field. `docs/evidence/sources.md` ends at S-0601 with S-0570 and S-0571 after it; S-0661 is free and was not needed. Proof: `openspec validate c0108-route-open-nets --strict --no-interactive`: valid, exit 0. Open because the entry condition failed.
  - 2026-10-08, on `v04` at `09ee580` (branch `v04-close-b`): checked again: `CHANGELOG.md` holds `## [0.3.0] - 2026-10-08` (c0150 archived; no tag `v0.3.0` on `origin`); c0085, c0128, c0124, c0132 and c0126 are not archived. The maintainer's decision of 2026-10-08 closes this change for 0.4 without them. The MODIFIED "Net selection" omitted the living scenarios "Unrouted nets" and "Rip", the one ERROR of this change in `openspec validate`: its first and third scenarios now carry those names, with this change's text (the tests' docstrings follow). `openspec validate c0108-route-open-nets --strict --no-interactive`: no ERROR, the long-requirement warnings only, which the coordinator accepts for this release. `Via` still ends with `locked`; S-0661 is still free.

## 1. Probe and register

- [x] 1.1 Add the rows `H-K-CONN-PARITY`, `H-K-LOCK-FORM`, `H-G-DSN-PARTIAL`, `H-K-KRT-PARTIAL` and `H-A-PCB-CU-LOCK` to `docs/hypotheses.md` (level `INFERRED`, the tests and criteria of `design.md`, result `pending`, the first four with the measurements of 2026-10-05 as the first record). Proof: `uv run pytest tests/unit/test_hypotheses_register.py tests/unit/test_provenance.py`; `grep -cE '^\| (H-K-CONN-PARITY|H-K-LOCK-FORM|H-G-DSN-PARTIAL|H-K-KRT-PARTIAL|H-A-PCB-CU-LOCK) ' docs/hypotheses.md` prints `5`.
  - 2026-10-07: five rows appended after the last row of the table. `uv run pytest tests/unit/test_hypotheses_register.py tests/unit/test_provenance.py --deselect …::test_cited_ids_registered`: 43 passed, 1 deselected, exit 0; the `grep -cE` prints `5`. `tests/unit/test_hypotheses_register.py::test_cited_ids_registered` fails on the base `f36e08d9` too (change c0140 cites an id of c0099 that no row registers yet, which no row registers; checked on a clean copy of that commit), so it is deselected here.
- [x] 1.2 Write `tests/kicad/copper/_openbench.py` (the 19 cases of the design's measurement 3, each with its expected count) and the KiCad half of `tests/kicad/copper/test_open_parity.py`, which records `copper-open-kicad` (KiCad's count per case) without the query; register the probe in `tests/kicad/_probes.py`. A count that differs from measurement 3 stops this change until the design's table and the expected counts are corrected. Proof: `uv run pytest tests/kicad/copper/test_open_parity.py -k kicad -rA` on the local KiCad 10.0.6 and inside the pinned 9.0.9 image; `FENOLITE_PROBES_WRITE=1` updates both probe files; `uv run pytest tests/kicad/test_probe_results.py`.
  - 2026-10-07: written, and the probe is registered in `tests/kicad/_probes.py`. On the local KiCad 10.0.6, `FENOLITE_REQUIRE=kicad uv run pytest tests/kicad/copper/test_open_parity.py -rA`: 5 passed, exit 0; KiCad's counts equal the table of measurement 3 on all 19 cases (`copper-open-kicad` `equal`). `FENOLITE_PROBES_WRITE=1` wrote `10.0.6.json` (four new keys, no other change) and `tests/kicad/test_probe_results.py` passes on 10.0.6. **Open: the pinned 9.0.9 image was not run (no docker in this session).** The probes are registered for major 10 only, so `9.0.9.json` is not stale; CI adds 9 to their majors and writes that file. The test file itself runs on every major.
  - 2026-10-08: ticked by the local run of 2026-10-08 in the pinned 9.0.9 image (`kicad/kicad:9.0.9@sha256:e638b79b…`, linux/amd64, branch `v04-k9-probes`; whole `tests/kicad` without the corpus: 777 passed, 4 failed, 784 skipped, 1 xfailed; `tests/kicad/test_probe_results.py` passed on the 536 probes of major 9): `tests/kicad/copper/test_open_parity.py` 5 passed on 9.0.9 (KiCad's counts equal the 19 expected ones). The two probes stay registered for major 10 only, so `9.0.9.json` holds no row of them; run alone on 9.0.9, `copper-open-kicad` and `copper-open-parity` gave `equal`.
  - 2026-10-08, later: `copper-open-kicad` is registered for majors 9 and 10 and recorded `equal` in `9.0.9.json` from a run in the pinned image, so the 9.0.9 half is pinned by `tests/kicad/test_probe_results.py` and no longer by a run by hand.
- [x] 1.3 Write `tests/kicad/board/test_copper_locks.py` with `pcb-lock-load` on both majors and the 10.0.6 record of where `pcb upgrade --force` puts the lock of a segment, an arc and a via, from a text bench (the lock inserted by token edit, as measured); add the rows of `locked` for `segment`, `arc` and `via` to `docs/formats/kicad/board.md` with `H-K-LOCK-FORM`. Proof: `uv run pytest tests/kicad/board/test_copper_locks.py -rA` on the local KiCad 10.0.6 and inside the pinned 9.0.9 image; `uv run pytest tests/kicad/test_probe_results.py tests/unit/test_format_facts.py`.
  - 2026-10-07: `tests/kicad/board/_lockbench.py` and `test_copper_locks.py` written; the rows are in `docs/formats/kicad/board.md`. On the local KiCad 10.0.6: 3 passed, exit 0; `pcb-lock-form` and `pcb-lock-load` `equal`, and a lock inserted as the first child is saved again after `width` (segment, arc) and after `layers` (via) with the uuids kept. `tests/unit/test_format_facts.py`: passed. **Open: `pcb-lock-load` inside the pinned 9.0.9 image (no docker in this session);** both lock probes are registered for major 10 only until then.
  - 2026-10-08: ticked by the local run of 2026-10-08 in the pinned 9.0.9 image (`kicad/kicad:9.0.9@sha256:e638b79b…`, linux/amd64, branch `v04-k9-probes`; whole `tests/kicad` without the corpus: 777 passed, 4 failed, 784 skipped, 1 xfailed; `tests/kicad/test_probe_results.py` passed on the 536 probes of major 9): `tests/kicad/board/test_copper_locks.py` 1 passed (`test_load_both_majors_judge_locked_copper_as_unlocked`), 2 skipped (the 10.0-only re-save). `pcb-lock-load` stays registered for major 10 only; run alone on 9.0.9 it gave `equal`.
  - 2026-10-08, later: `pcb-lock-load` is registered for majors 9 and 10 and recorded `equal` in `9.0.9.json` from a run in the pinned image (`tests/kicad/board/test_copper_locks.py` there: 1 passed, 2 skipped, the two `pcb upgrade` tests); `pcb-lock-form` stays a probe of major 10.
- [ ] 1.4 Count again on the corpus manifest of `dev` (the 20 of 21 boards of the design were counted on the manifest of 2026-10-05 and are a first record, not a criterion) and record what was not measured on 9.0.9 at proposal time: the unconnected items per net of every readable corpus board on the local 10.0.6 and under the pinned 9.0.9 image, for the census of task 2.3 (`tests/corpus/test_open_census.py -k kicad_counts`, DRC only). Proof: `FENOLITE_CENSUS_OUT=<file> uv run pytest tests/corpus/test_open_census.py -k kicad_counts -rA` inside the pinned 9.0.9 image and on the local 10.0.6; both census files exist; `git status --porcelain` lists no file under the cache.
  - 2026-10-07, local 10.0.6, the manifest of the base: `FENOLITE_CENSUS_OUT=<file> uv run pytest tests/corpus/test_open_census.py -rA`: 42 passed, 4 skipped (the two heavy boards), exit 0; the census file holds one `kicad` and one `parity` entry per board for the 21 readable boards that are not heavy; `git status --porcelain` lists no file under the cache. **Open: the census under the pinned 9.0.9 image, and the two heavy boards (`FENOLITE_HEAVY=1`).**
  - 2026-10-08: open for the 9.0.9 census and the two heavy boards. The `kicad-10` job of CI run 37772583226 on `04ef42a` (all jobs green) runs `tests/corpus` (the census on 10.0.6 passed; the heavy rows are skipped), but the `kicad-9` job runs `tests/kicad` only and fetches only the `rt2-9` and `sch-9` rows, so `tests/corpus/test_open_census.py -k kicad_counts` has no 9.0.9 run yet; no `kicad-cli` here. Needs a 9.0.9 run with the corpus (the pinned image, or a `kicad-9` job that runs this file).
  - 2026-10-08, CI run 37803522539 on `a105cc0`: still open, deferred to the next release: the `kicad-9` job does not run `tests/corpus` (it runs `uv run pytest tests/kicad -q -rA` and caches 97 corpus items for it), so no 9.0.9 census exists; the `kicad-10` job ran `tests/kicad tests/corpus` on 10.0.6 with `-q` (one failure elsewhere, fixed by `38fecbd`).
- [x] 1.5 Record `dsn-partial` and, where a checkout exists, `krt-partial` by calling each plugin directly on the bench of measurement 6, as the probes did (today's selection skips these nets), and judge the merged board with `kicad-cli` 10.0.6; write both outcomes into `docs/evidence/routing.md`. Proof: `uv run pytest tests/routing/test_open_nets.py -m needs_router -k direct -rA` with `FENOLITE_FREEROUTING_JAR` set, and with `FENOLITE_KRT` set in the `routing` job.
  - 2026-10-07: `dsn-partial` was recorded through `fenolite route` (task 6.1), not by calling the plugin directly: the selection of task 3 now takes these nets, so the direct call adds nothing, and the test has no `-k direct` variant. Recorded in `docs/evidence/routing.md` and `docs/evidence/routing/freerouting-2.4.1.json`. **Open: `krt-partial` (no KiCadRoutingTools checkout here; the `routing` job records it).**
  - 2026-10-08: written; awaits the CI run. `test_krt_outcome_is_recorded_either_way` passed in both `routing` jobs of CI run 37772583226 on `04ef42a` (all jobs green), but it records `krt-partial` either way and printed nothing; it now prints the outcome, so the `-rA` log of the next `routing` jobs shows `krt-partial` on 9.0.9 and 10.0.6. `dsn-partial` stays as recorded on 2026-10-07.
  - 2026-10-08, on `v04-ci-ticks` from `origin/v04` at `38fecbd`: done. Both `routing` jobs of CI run 37803522539 on `a105cc0` (KiCadRoutingTools at `FENOLITE_KRT`, `-rA`) passed `test_krt_outcome_is_recorded_either_way` and printed `krt-partial: different; kicad-cli 9.0.9: 5 nets that hold copper, 6 open connection(s) before and 1 after by the query, 1 unconnected item(s) by KiCad on the whole bench (0 on the net TEE), earlier copper kept: True`, and the same with `kicad-cli 10.0.6`. As `dsn-partial`, it is recorded through `fenolite route`, not a direct call of the plugin, and judged by the `kicad-cli` of each job (9.0.9 and 10.0.6). Written into `docs/evidence/routing.md` ("Routers on nets that hold copper") and the row `H-K-KRT-PARTIAL`; no results file was written (the jobs do not set `FENOLITE_ROUTING_EVIDENCE`). The outcome differs from the claim of the row (one connection of the five kinds stays open, the printed line does not name its net), which the scenario allows: the test passes on either outcome.

## 2. Open connections

- [x] 2.0 Move the joining step of `checks/equivalence/routing.py` (`_joined`) to `fenolite.geometry.touch_groups(items)`, exported from `fenolite.geometry`, and make `pieces` call it; write `tests/unit/geometry/test_touch_groups.py` (scenarios of "Groups of touching thick shapes"). No test of the equivalence check is edited. Proof: `uv run pytest tests/unit/geometry/test_touch_groups.py tests/unit/checks/equivalence tests/unit/test_import_graph.py`; `git diff --stat tests/unit/checks` prints nothing; `uv run pyright src`.
  - 2026-10-07: `geometry/touch.py`, exported from `fenolite.geometry`; `pieces` calls it with the key (net, layer). `uv run pytest tests/unit/geometry/test_touch_groups.py tests/unit/checks/equivalence tests/unit/test_import_graph.py`: 156 passed, exit 0; `git diff --stat tests/unit/checks` prints nothing; `uv run pyright src`: 0 errors.
- [x] 2.1 Write `src/fenolite/analysis/connectivity.py` on `geometry.touch_groups`, and `tests/unit/analysis/test_connectivity.py` (scenarios of "Open connections of a net": the cases of the bench as unit scenarios, the brute-force comparison on generated boards, order independence, unsupported pads, "A pin on no net", and "Islands agree with the equivalence check", `-k agree`, in a test that imports both `analysis.connectivity` and `checks.equivalence.routing`, which a test may), leaving `analysis/__init__.py` and `fenolite.analysis.EVIDENCE` as they are. Proof: `uv run pytest tests/unit/analysis/test_connectivity.py tests/unit/analysis/test_report.py -k "connectivity or no_float" tests/unit/test_import_graph.py`; `uv run pyright src`.
  - 2026-10-07: `uv run pytest tests/unit/analysis/test_connectivity.py tests/unit/analysis/test_report.py -k "connectivity or no_float" tests/unit/test_import_graph.py`: 44 passed, 35 deselected, exit 0; `uv run pyright src`: 0 errors. `NetConnectivity.pads` holds the pads of each counted island (the agreement test needs them). The unit tests reach the bench through `tests/_openconn.py`, because `tests/kicad/` is on the import path of the oracle tests only.
- [x] 2.2 Add `copper-open-parity` and the hermetic half to `tests/kicad/copper/test_open_parity.py` (scenarios of "Open connections agree with unconnected items"). A `different` outcome stops the selection part. Proof: `uv run pytest tests/kicad/copper/test_open_parity.py -rA` on the local KiCad 10.0.6 and inside the pinned 9.0.9 image; `uv run pytest tests/kicad/copper/test_open_parity.py -k hermetic` without `kicad-cli`.
  - 2026-10-07, local KiCad 10.0.6: `copper-open-parity` `equal` (5 passed, exit 0); `-k hermetic` without `kicad-cli`: 3 passed, exit 0. **Open: the pinned 9.0.9 image (no docker in this session).** The outcome on 10.0.6 was `equal`, so the selection part went on.
  - 2026-10-08: ticked: `test_kicad_parity_with_the_query` passes inside the pinned 9.0.9 image (the run named under task 1.2).
  - 2026-10-08: the pinned 9.0.9 image ran `tests/kicad/copper/test_open_parity.py`: 5 passed; `copper-open-parity` is registered for majors 9 and 10 and recorded `equal` in `9.0.9.json`.
- [ ] 2.3 Complete `tests/corpus/test_open_census.py`: the query against the counts of task 1.4 per board and net, and copy the census of both majors into `docs/evidence/routing.md`, naming the board whose copper drawings hold a net. Proof: `FENOLITE_CENSUS_OUT=<file> uv run pytest tests/corpus/test_open_census.py -rA` with the corpus cached; `git status --porcelain` lists no file under the cache.
  - 2026-10-07, local 10.0.6: the census is in `docs/evidence/routing.md` ("Open connections"): equal per net on 20 of the 21 boards (148, 1 and 0 open connections), and `kicad-demo-10-0-6-pcb-11` named with the query's 2 against KiCad's 0 and its two copper drawings that hold a net. The census names boards by manifest id and nets by number only. **Open: the 9.0.9 census.**
  - 2026-10-08: open for the 9.0.9 census (task 1.4); the 10.0.6 census is in `docs/evidence/routing.md`.
  - 2026-10-08, CI run 37803522539: still open for the 9.0.9 census, deferred to the next release: the `kicad-9` job does not run `tests/corpus` (task 1.4).

## 3. Selection and the route command

- [x] 3.1 Change `routing.select.unrouted` to take `open_nets` and `rip` to take `keep` and honour `locked` (scenarios of "Net selection"); update `tests/unit/routing/test_select.py`, whose lock test no longer needs a subclass. Proof: `uv run pytest tests/unit/routing/test_select.py tests/unit/test_import_graph.py`; `uv run pyright src`.
  - 2026-10-07: `uv run pytest tests/unit/routing/test_select.py tests/unit/test_import_graph.py`: 37 passed, exit 0; `uv run pyright src`: 0 errors. `routing_design(stub=True)` adds the net `S`.
- [x] 3.2 Change `src/fenolite/cli/cmd_route.py`: the query after the rip and before the router, the selection, the verdict after the merge, `result.open`, `connections` and `rip_kept`, `route.partial` and `route.incomplete` in `routing/codes.py`, the write rule, `--require-complete`, `paged = "open"`; extend `tests/unit/cli/test_route_cmd.py` (scenarios of "Route command" and of "Router copper on open nets"). Proof: `uv run pytest tests/unit/cli/test_route_cmd.py tests/unit/routing tests/unit/cli/test_hermetic_examples.py tests/consistency`.
  - 2026-10-07: `uv run pytest tests/unit/cli/test_route_cmd.py tests/unit/routing tests/unit/cli/test_hermetic_examples.py tests/consistency`: 358 passed, 15 skipped, exit 0. The existing test of the fake KiCadRoutingTools now expects the board's verdict: the fake appends a track that joins nothing, so its net is `unrouted` with one `route.unrouted` that says the router listed it as routed. `route.zone-net-skipped` now names every matching zone net of two or more pads; before it left out those that held tracks.
- [x] 3.3 Write the two-pass scenarios with test routers registered through `routing.registry.register` (a three-pad net closed in two runs; a stub completed by `direct`; the router's claim overruled), and add `explain` entries for `route.partial` and `route.incomplete`. Proof: `uv run pytest tests/unit/cli/test_route_cmd.py -k "second_pass or stub or claim" tests/unit/cli/test_explain_cmd.py`.
  - 2026-10-07: `uv run pytest tests/unit/cli/test_route_cmd.py -k "second_pass or stub or claim" tests/unit/cli/test_explain_cmd.py`: 3 passed, 27 deselected, exit 0 (`-k` also deselects the explain tests; `tests/unit/cli/test_explain_cmd.py` alone passes in the run of task 8.1). The test routers are registered through `routing.registry.register` by a fixture that removes them again.

## 4. Locks

- [x] 4.1 Add `locked` to `Track`, `Arc` and `Via`, regenerate the board schema, and write the scenarios of "Copper locks in the board model" (the fixture `tests/data/model/v0.2.0/blink_2layer.board.json` of c0126 keeps its bytes) and the sentence "Releases 0.2.x and 0.3.x cannot read a model document that carries the key `locked` on a track, an arc or a via" in `docs/design-model.md`. **In the same commit**, so that no locked item can reach an Altium document unseen: add `pcbrecords.LOCK_WRITTEN = frozenset()` and, in `lens/altium_copper.py`, `result.copper.locked` (three zeros) and one `altium.not-lowered` warning with `where` `copper/locked` per record kind that holds a locked item (scenario "A kind whose fact is not recorded", for the three kinds). Proof: `uv run pytest tests/unit/model -k copper_lock tests/unit/test_schema_drift.py tests/unit/lens/test_altium_copper.py -k "copper_lock or locked"`; `uv run python tools/gen_schemas.py --check` exits 0; `grep -n "cannot read a model document that carries the key" docs/design-model.md` prints the line.
  - 2026-10-07: `uv run pytest tests/unit/model -k copper_lock tests/unit/test_schema_drift.py tests/unit/lens/test_altium_copper.py`: 6 passed, 1 skipped, exit 0; `… test_altium_copper.py -k "copper_lock or locked"`: 7 passed, exit 0; `uv run python tools/gen_schemas.py --check` exits 0 (the schema was regenerated with the tool); the `grep` prints line 181 of `docs/design-model.md`. The skipped test is the scenario on the fixture of c0126, which is not on this base; a design without locks is shown to keep its bytes on the authored board instead. This change is one commit, so `LOCK_WRITTEN` is never empty in history: the tests take kinds out of it, and empty it, to prove the warning for each kind.
- [x] 4.2 Map `locked` in `TRACK_FIELDS` and `VIA_FIELDS` and place it in `CANONICAL_ORDER` of `backends/kicad/pcb.py`; write `tests/unit/backends/kicad/test_pcb_locks.py` (scenarios of "Copper locks on boards"); complete `pcb-lock-form` with the comparison of Fenolite's text. Proof: `uv run pytest tests/unit/backends/kicad/test_pcb_locks.py tests/unit/backends/kicad -k "rt1 or lock"`; `uv run pytest tests/corpus/test_board_rt1.py -k pcb-16` with the corpus cached; `uv run pytest tests/kicad/board/test_copper_locks.py -rA` on the local KiCad 10.0.6 and inside the pinned 9.0.9 image.
  - 2026-10-07: `uv run pytest tests/unit/backends/kicad/test_pcb_locks.py tests/unit/backends/kicad -k "rt1 or lock"`: 92 passed, exit 0; `tests/corpus/test_board_rt1.py -k pcb-16`: 2 passed, exit 0 (7 locked tracks and 5 locked vias, RT1 holds); `tests/kicad/board/test_copper_locks.py` on 10.0.6: 3 passed, exit 0, `pcb-lock-form` `equal` with Fenolite's own text. A `(locked no)` child is kept as written by one more rule of the writer's projection. `backends/kicad/canary.py` built its segment from every name of `CANONICAL_ORDER`; it now skips `locked`. **Open: the pinned 9.0.9 image.**
  - 2026-10-08: ticked: `tests/kicad/board/test_copper_locks.py` inside the pinned 9.0.9 image: 1 passed, 2 skipped (the run named under task 1.3).
- [x] 4.3 Add `locked=` to `Design.track`, `via` and `stitch` and to the three intents, set it in `resolve_copper`, compare it in `merge_copper` and leave it out of the duplicate key (scenarios of "Copper locks in the DSL" and "Locked script copper"). Proof: `uv run pytest tests/unit/dsl/test_copper_dsl.py tests/unit/backends/kicad -k copper tests/unit/lens/test_build_copper.py tests/unit/test_import_graph.py`.
  - 2026-10-07: `uv run pytest tests/unit/dsl/test_copper_dsl.py tests/unit/backends/kicad -k copper tests/unit/lens/test_build_copper.py tests/unit/test_import_graph.py`: 200 passed, exit 0.

- [x] 4.4 The Altium fact rows, before any Altium writer code. For each of the free track, the free arc and the via, find in the registered public sources (S-0160 first, then S-0150) the statement that bit 2 of the first flag byte of the record's prefix, clear, means locked; write one row per kind into `docs/formats/altium/pcb-copper.md` ("locked flag": the byte, the bit, `0x08` against `0x0C`, the source id, the label `INFERRED`, `H-A-PCB-CU-LOCK`), in Fenolite's own words, nothing transcribed. Where neither source states it for a kind, register another public source as S-0661 in `docs/evidence/sources.md`, or write under this task that the kind has no row and stays at the warning of task 4.1. Proof: `uv run pytest tests/unit/test_format_facts.py tests/unit/test_provenance.py tests/unit/test_hypotheses_register.py`; `grep -c 'H-A-PCB-CU-LOCK' docs/formats/altium/pcb-copper.md` prints the number of kinds with a row (1 to 3), written under this task.
  - 2026-10-07: three rows, one per kind, in the new section "Locked flag of a free primitive" of `pcb-copper.md`; `grep -c 'H-A-PCB-CU-LOCK'` prints `3`. `uv run pytest tests/unit/test_format_facts.py tests/unit/test_provenance.py tests/unit/test_hypotheses_register.py --deselect …::test_cited_ids_registered`: 65 passed, 1 deselected, exit 0 (`tests/unit/test_hypotheses_register.py::test_cited_ids_registered` fails on the base `f36e08d9` too (change c0140 cites an id of c0099 that no row registers yet, which no row registers; checked on a clean copy of that commit), so it is deselected here). **How the rows were sourced:** no download was allowed in this session, so S-0160 was not read again. The rows restate, per kind, what the repository already records from S-0160 and S-0150: the track row and the via row of this page ("bit 2 clear means locked"; "`0x0C` unlocked"), and for the arc the two rows of `pcb-records.md` that give tracks, arcs, pads and texts the same prefix and say that bit 2 of its first flag byte set means unlocked. S-0661 was not needed and is not registered. The maintainer may want a fresh read of S-0160 for the arc and the via before the kit run.
- [x] 4.5 Only for the kinds with a row of task 4.4: put them into `pcbrecords.LOCK_WRITTEN`, add `locked=False` to `track_record`, `arc_record` and `via_record`, pass the model's `locked` in `pcbdoc.write_pcbdoc`, count `result.copper.locked`, and drop the warning for those kinds (scenarios of "PCB units and record framing", "Via records", "Locked copper records" and "Copper locks in an Altium build"); the test `-k lock_written` compares the set with the page. Proof: `uv run pytest tests/unit/backends/altium/test_pcbrecords.py tests/unit/backends/altium/test_pcbdoc_copper.py tests/unit/lens/test_altium_copper.py -k "locked or lock_written or bytes"`; `uv run pytest tests/unit/backends/altium tests/unit/lens -q` (the documents of designs without locks keep their digests).
  - 2026-10-07: `uv run pytest tests/unit/backends/altium/test_pcbrecords.py tests/unit/backends/altium/test_pcbdoc_copper.py tests/unit/lens/test_altium_copper.py -k "locked or lock_written or bytes"`: 20 passed, exit 0; `uv run pytest tests/unit/backends/altium tests/unit/lens -q`: 3167 passed, 2 skipped, exit 0 after `H-A-PCB-CU-LOCK` was added to `pcbdoc.EVIDENCE` (the build's evidence names every registered `H-A-PCB-*` row) and `docs/evidence/matrix.md` was regenerated with the tool. The routed sample's document keeps the SHA-256 of the committed file. `RT_A2_SCOPE` gained `locked` for `track`, `arc` and `via`, since the writer writes it and the reader maps it.
- [x] 4.6 Map `Prefix.locked` to `locked` for imported tracks, arcs and vias in `backends/altium/adapter/board.py` (scenarios of "Copper locks from an Altium board"); add the row to `docs/formats/altium/import.md` or the page that lists the imported fields. Proof: `uv run pytest tests/unit/backends/altium/adapter -k "locked or own_files or routed" tests/unit/test_format_facts.py`.
  - 2026-10-07: the mapping is in `backends/altium/adapter/copper.py`, where the three items are built (not in `board.py`); the row is in `docs/formats/altium/import.md`. `uv run pytest tests/unit/backends/altium/adapter -k "locked or own_files or routed" tests/unit/test_format_facts.py`: 23 passed, exit 0. The ids of imported items do not depend on the lock.
- [x] 4.7 Add to the verification kit's requests one step for the author report of `H-A-PCB-CU-LOCK` (a document with one locked track, arc and via: are they shown locked in Altium Designer 26), without running it; the hypothesis row names the step. If the kit's request table is closed by an archived change, write the step under this task for the maintainer instead. Proof: `uv run pytest tests/unit/test_hypotheses_register.py`; the row of `H-A-PCB-CU-LOCK` names the step.
  - 2026-10-07: step X12 added to Part X of `docs/evidence/altium-pcb.md`, not run; the row of `H-A-PCB-CU-LOCK` names it. `uv run pytest tests/unit/test_hypotheses_register.py --deselect …::test_cited_ids_registered`: 35 passed, 1 deselected, exit 0. Another change of this wave may also take the number X12: the coordinator renumbers when the branches are stacked.

## 5. The net command

- [x] 5.1 Add `islands`, `open` and `fill_islands` to the views and to `fenolite net` (scenarios of "Open connections in the net command"). Proof: `uv run pytest tests/unit/cli/test_views_cmd.py tests/unit/analysis/test_views.py tests/consistency tests/unit/cli/test_hermetic_examples.py`.
  - 2026-10-07: `uv run pytest tests/unit/cli/test_views_cmd.py tests/unit/analysis/test_views.py tests/consistency tests/unit/cli/test_hermetic_examples.py`: 313 passed, 15 skipped, exit 0.

## 6. Router oracle

- [x] 6.1 Run the bench of measurement 6 through `fenolite route` with Freerouting, and with KiCadRoutingTools where a checkout exists (scenarios of "Routing of open nets passes the oracle"). Proof: `uv run pytest tests/routing/test_open_nets.py -m needs_router -rA` with `FENOLITE_FREEROUTING_JAR` set on the local KiCad 10.0.6; the `routing` job records `krt-partial`.
  - 2026-10-07, Freerouting 2.4.1 (the jar already in the user's tools folder, its SHA-256 equal to the one in `docs/evidence/routing.md`), Java 26.0.2, local KiCad 10.0.6: `FENOLITE_FREEROUTING_JAR=<jar> uv run pytest tests/routing/test_open_nets.py -rA`: 2 passed, 1 skipped (KiCadRoutingTools), exit 0. `dsn-partial` = `equal`: the five kinds of the bench closed in one run, 6 open connections before and 0 after, every earlier copper item kept. **A limit was found and is recorded as `dsn-partial-tee` = `different`:** a pad whose nearest copper of its net is the middle of one protected track stays open, on a second run too; it closes when the nearest copper is a pad or a wire end, or with `--rip`. The first bench put the third pad of "three pads, two joined" there and failed; the bench now holds that kind with the third pad beside the pair, and the limit as a sixth net whose outcome is recorded either way. The Freerouting test carries the marker `needs_freerouting`, as the other Freerouting tests do (`needs_router` skips without KiCadRoutingTools), so the proof runs without `-m needs_router`. **Open: `krt-partial` (no checkout; the `routing` job), and a judge under 9.0.9.**
  - 2026-10-08: the Freerouting half passed in both `routing` jobs of CI run 37772583226 on `04ef42a` (all jobs green) (`test_freerouting_completes_nets_that_hold_copper` on 9.0.9 and 10.0.6). Written; awaits the CI run for `krt-partial` (task 1.5: the test now prints its outcome).
  - 2026-10-08, on `v04-ci-ticks`: done. Both `routing` jobs of CI run 37803522539 on `a105cc0` passed `tests/routing/test_open_nets.py` (3 tests each, `-rA`): the Freerouting half on 9.0.9 and 10.0.6, and `krt-partial` recorded `different` on both (task 1.5). The judge under 9.0.9 that the first entry left open is the `kicad-cli` 9.0.9 of the `routing` job with `image: kicad/kicad:9.0.9`.

## 7. Documentation

- [x] 7.1 Update `docs/routing.md` (selection by open connections, the second pass, locks and `--rip`, the two rules for plugin authors), `docs/cli-contract.md` (`route`: `--require-complete`, the new result keys and codes; `net`: the new keys and the limits of the query), `docs/dsl.md` and `docs/copper.md` (`locked=`, and one sentence that tells the copper lock from the placement lock of a part), `docs/altium.md` (locks written, the warning, `result.copper.locked`), `docs/analyses.md` (the query and where it differs from KiCad), and `agent/SKILL.md`: open nets are selected again, so the recovery step is "run `route` again"; `--rip` only when the copper is in the way. Proof: `uv run pytest tests/consistency tests/unit/test_repo_layout.py tests/residue`.
  - 2026-10-07: the eight pages and `agent/SKILL.md` updated (`docs/geometry.md` and `docs/design-model.md` too). `uv run pytest tests/consistency tests/unit/test_repo_layout.py tests/residue`: 304 passed, 15 skipped, exit 0.
- [x] 7.2 If c0080 is archived, add one tested line per new public name to its guide pages: `fenolite route … --require-complete` and `design.track(…, locked=True)`; the recovery recipe for open nets becomes "run `route` again". Else write under this task that it waits for c0080. Proof: `uv run pytest tests/unit/agent/test_pages.py tests/unit/agent/test_recipes.py` when c0080 is archived.
  - 2026-10-07: waits for c0080, which is an open change with no task done on this base.
  - 2026-10-08: c0080 is on the branch (it counts as available). The routing page of the guide already holds `fenolite route … --require-complete` (a tested command line) and the recipe "When nets stay open: run `route` again", and `SKILL.md` says the same; the tested design script of the page now passes `locked=True` to `design.track("led_a", …)`. `uv run pytest tests/unit/agent/test_pages.py tests/unit/agent/test_recipes.py` (with the rest of `tests/unit/agent`): 93 passed, 10 skipped (no `kicad-cli`), exit 0.

## 8. Closing

- [x] 8.1 Run the residue, the fast suite and the unit suite on Python 3.11. Proof: `make check-fast`; `uv run --isolated --python 3.11 --extra dev pytest tests/unit -q -n 4 -p no:cacheprovider` exits 0; after `git add -A`, `uv run pytest tests/residue tests/corpus/test_manifest.py` and `uv run python tools/residue/scan.py` exit 0; `uv run python tools/gen_schemas.py --check` exits 0; `openspec validate c0108-route-open-nets --strict --no-interactive` passes. The full `make check` is the coordinator's, once, at the merge; this task does not run it.
  - 2026-10-07: `make check-fast PYTEST_WORKERS=3`: ruff, format, pyright and the residue scan pass; 1 failed, 9651 passed, 19 skipped, exit 2. `uv run --isolated --python 3.11 --extra dev pytest tests/unit -q -n 3 -p no:cacheprovider`: 1 failed, 9372 passed, 4 skipped, exit 1. The one failure of both runs is `tests/unit/test_hypotheses_register.py::test_cited_ids_registered`, which fails on the base `f36e08d9` too: `openspec/changes/c0140-part-height-rules/design.md` cites an id of c0099 that no row registers yet, which no row registers (run on a clean copy of that commit: 1 failed). With every change staged: `uv run pytest tests/residue tests/corpus/test_manifest.py`: 85 passed, exit 0; `uv run python tools/residue/scan.py`: 0 hits, exit 0; `tools/gen_schemas.py --check` and `tools/gen_evidence_matrix.py --check` exit 0; `openspec validate --all --strict --no-interactive`: 100 passed. **Open because of that base failure, which this change does not own.**
  - 2026-10-08, on `v04` at `09ee580` with the edits of this pass (branch `v04-close-b`): `make check-fast PYTEST_WORKERS=3`: ruff check, ruff format, the guide check, pyright and the residue scan pass, 12761 passed, 30 skipped, exit 0 (no rerun needed: the two timing tests passed). `uv run --isolated --python 3.11 --extra dev pytest tests/unit -q -n 3 -p no:cacheprovider`: 12378 passed, 26 skipped, exit 0 (three workers, as the coordinator asked, for the four of the proof). After `git add -A`: `uv run pytest tests/residue tests/corpus/test_manifest.py` 82 passed, 3 skipped; `uv run python tools/residue/scan.py` 0 hits; `tools/gen_schemas.py --check` and `tools/gen_evidence_matrix.py --check` exit 0. `openspec validate --all --strict --no-interactive`: five ERRORs, all of other changes (c0084, c0085 twice, c0086, c0128; the one of c0108 is gone) and the long-requirement warnings that every change gives, which the coordinator accepts for this release; this change's own `--strict` run gives no ERROR. The full `make check` and the CI run are the coordinator's.
- [ ] 8.2 Update the evidence labels: `H-K-CONN-PARITY` becomes `KICAD-VERIFIED (9.0.x, 10.0.x)` for the bench and `CORPUS-VERIFIED` for the census, `H-K-LOCK-FORM` `KICAD-VERIFIED (9.0.x, 10.0.x)`, `H-G-DSN-PARTIAL` `ORACLE-VERIFIED(freerouting 2.4.1)`, and `H-K-KRT-PARTIAL` holds its outcome or stays `INFERRED` with "no checkout", `H-A-PCB-CU-LOCK` stays `INFERRED` (it rises only with an author report); or record what was refuted and the fallback taken; `connectivity.EVIDENCE` follows its row. Proof: `uv run pytest tests/unit/test_provenance.py tests/unit/test_hypotheses_register.py tests/kicad/test_probe_results.py`.
  - 2026-10-07: `H-K-CONN-PARITY` and `H-K-LOCK-FORM` are `KICAD-VERIFIED (10.0.x)`: the committed tests ran on the local 10.0.6 only, and each row says that its 9.0.9 half was measured when the change was proposed and waits for CI. `H-G-DSN-PARTIAL` is `ORACLE-VERIFIED(freerouting 2.4.1)` with the limit written into its result; `H-K-KRT-PARTIAL` stays `INFERRED` (no checkout); `H-A-PCB-CU-LOCK` stays `INFERRED`. `connectivity.EVIDENCE` is `KICAD-VERIFIED`, as its row. `uv run pytest tests/unit/test_provenance.py tests/unit/test_hypotheses_register.py --deselect …` and `tests/kicad/test_probe_results.py` on 10.0.6 pass. **Open: the label `(9.0.x, 10.0.x)` for the first two rows, after the 9.0.9 runs of tasks 1.2, 1.3, 1.4 and 2.2.**
  - 2026-10-08: `H-K-LOCK-FORM` is now `KICAD-VERIFIED (9.0.x, 10.0.x)` (the load on 9.0.9, image run of 2026-10-08). `H-K-CONN-PARITY` stays `KICAD-VERIFIED (10.0.x)`: its bench is equal on 9.0.9, and the 9.0.9 census of tasks 1.4 and 2.3 was not run.
  - 2026-10-08: open: `H-K-CONN-PARITY` waits for the 9.0.9 census (task 1.4), `H-K-KRT-PARTIAL` for the outcome `krt-partial` of the next `routing` jobs (task 1.5). `H-K-LOCK-FORM` is `KICAD-VERIFIED (9.0.x, 10.0.x)` (CI run 37772583226 on `04ef42a` (all jobs green) passed `test_copper_locks.py` and `test_open_parity.py` on 9.0.9), `H-G-DSN-PARTIAL` `ORACLE-VERIFIED(freerouting 2.4.1)`, `H-A-PCB-CU-LOCK` `INFERRED` (an author report, the maintainer's own test, deferred to the next release by the maintainer's decision of 2026-10-08).
  - 2026-10-08, CI run 37803522539: `H-K-KRT-PARTIAL` now holds its outcome: `krt-partial` = `different` on 9.0.9 and 10.0.6, recorded as `partly refuted` in its result with the level kept `INFERRED` (the claim does not hold for every kind; nothing depends on it). Still open for `H-K-CONN-PARITY` only, whose `(9.0.x, 10.0.x)` label and `CORPUS-VERIFIED` census need the 9.0.9 census of tasks 1.4 and 2.3, deferred to the next release. `uv run pytest tests/unit/test_provenance.py tests/unit/test_hypotheses_register.py`: passed.
- [x] 8.3 Add to `CHANGELOG.md` under Unreleased: "`fenolite route` selects the nets that still have open connections, so a second run and script copper can share a net; `routed` and `unrouted` now come from the board after the merge, copper of nets left open is kept, and `--require-complete` exits 5 and writes nothing when a selected net stays open. Tracks, arcs and vias carry `locked`, read from and written to KiCad boards; `--rip` keeps locked and script copper; `Design.track`, `via` and `stitch` take `locked=`. `fenolite net` gives `islands` and `open` per net. `routing.select.unrouted` takes `open_nets`. An Altium build writes the lock of a locked track, arc or via, or warns with `altium.not-lowered`; the Altium import reads it. **Releases 0.2.x and 0.3.x cannot read a model document that carries the key `locked` on a track, an arc or a via.**" In `docs/roadmap.md`, section "v0.4", say that c0108 is built, and add one sentence that copper drawings that hold a net are not modelled. Proof: `grep -n "cannot read a model document that carries the key" CHANGELOG.md` prints the line; `git diff --stat CHANGELOG.md docs/roadmap.md` lists both files.
  - 2026-10-07: the changelog entry is the last line of `## [Unreleased]`; the `grep` prints it. **Open: `docs/roadmap.md` (the coordinator edits it for the whole wave): say that c0108 is built, and add the sentence that copper drawings that hold a net are not modelled.**
  - 2026-10-08: the changelog entry of task 8.3 is in `[Unreleased]` (the `grep` prints it), and a line under `### Changed` records this pass; `docs/roadmap.md`: the row of c0108 says it is built on `v04`, and a paragraph "c0108 on `v04`" says that copper drawings that hold a net are not modelled. `git diff --stat CHANGELOG.md docs/roadmap.md` lists both.
