lgili/Fenolite/openspec/changes/c0109-routing-scale-control/tasks.md

## 0. Entry check

- [x] 0.1 Read the living `routing`, `specctra-dsn`, `cli-contract` and `kicad-oracle` specs and `openspec list`. Write under this task, with the date: that `0.3.0` is released and that c0108 and c0107 are archived (else stop: this change is written on their text); whether c0078 is archived (the order for "Freerouting plugin" is c0078, c0109, c0110): if so, regenerate the MODIFIED "Freerouting plugin" from the living text, full text and every scenario, and re-apply only this change's edits (run, tiers, optimizer, result); if c0078 is still open, write that it regenerates after this change; whether "KiCadRoutingTools plugin" changed since `9aba2dff` (then regenerate it the same way: groups, run, failure); that the Network bullet of "Design files are written from the model" states the one-pad `unconnected-(` rule. Proof: `openspec validate c0109-routing-scale-control --strict --no-interactive` passes after any regeneration.

  - 2026-10-08, on the integration branch `v04` at `7392159d` (`dev` with c0138 and c0123, the v0.4 proposals, and the built changes c0141, c0077, c0078, c0100, c0108, c0116). `0.3.0` is not released (the last tag is `v0.2.1`) and no prerequisite is archived: c0108 and c0078 are built on this base and still open (`openspec list`: 14/27 and 10/15 tasks), c0107 is a proposal only. The coordinator of the v0.4 stack decided to build this change on that base instead of stopping; what that means for each text:
  - "Freerouting plugin": the living text is still the one of `9aba2dff`; the current text is c0078's MODIFIED delta (`openspec/changes/c0078-router-fetch/specs/routing/spec.md`). This change's delta was regenerated from it, full text and every scenario (the third Location, `jar_source`, the reason that names `fenolite fetch`, the Messages bullet, the last line that allows the download through `fetch`, and the scenarios "Fetched jar is found", "Missing jar names the command" and "No connection outside fetch"), and only this change's edits were applied again: Run (`others="netless"`, the optimizer switch, the time left of the budget, the option `optimize`), Tiers, Optimizer, Result, and the scenarios "Fake java", "Other nets left out of the design file" and "Optimizer run cut". c0078 archives first, then this change; c0110 regenerates from the text this change leaves.
  - "KiCadRoutingTools plugin": `openspec/specs/routing/spec.md` has not changed since `9aba2dff` (`git diff 9aba2dff 7392159d -- openspec/specs/routing/spec.md` is empty) and no other open change holds a delta of it; the delta is kept.
  - c0108 is built on this base: `route` selects by open connections, an issue of severity error plans no write, and `--require-complete` exists; this change builds on that code and modifies none of c0108's requirements.
  - c0107 is not on this base. The living Network bullet of "Design files are written from the model" does not state the one-pad `unconnected-(` rule yet (c0107's delta adds the sentence; the writer does it since c0061). The parts of this change that are written against c0107's proposal text are marked "builds on c0107 (not on this base)" in the code: the plane exception of the netless mode (no plane is written into a design file here, so every net outside the job is left out) and the place of `budget` and `tier` after c0107's job fields.
  - Proof: `openspec validate c0109-routing-scale-control --strict --no-interactive` passes after the regeneration (2026-10-08).

## 1. Probe and register

- [x] 1.1 Add the rows `H-G-DSN-NOOPT`, `H-G-DSN-NETLESS` and `H-K-KRT-GROUP` to `docs/hypotheses.md` (level `INFERRED`, the tests and criteria of `design.md`, result `pending` with the measurements of 2026-10-05 as the first record). Add to the rows S-0221 and S-0222 of `docs/evidence/sources.md` the tag pages read on 2026-10-05 (`blob/v2.4.1/docs/…`), and to S-0216 that `route.py --help` of the pinned checkout states the flags used. Proof: `uv run pytest tests/unit/test_hypotheses_register.py tests/unit/test_provenance.py`.
  - Open: the rows of `docs/evidence/sources.md` are not edited. 2026-10-08: the hypothesis rows are registered at the end of the table of `docs/hypotheses.md` (`H-G-DSN-NOOPT`, `H-G-DSN-NETLESS`, `H-G-DSN-NETLESS-2`, `H-K-KRT-GROUP`), with the measurements of 2026-10-05 as their first record, and the proof passes (44 passed). What stays: adding to S-0221 and S-0222 the tag pages read on 2026-10-05 and to S-0216 the `route.py --help` of the pinned checkout. The register is append-only for the changes built in parallel on this base, the pages were not read again when the change was built (no network access), and no KiCadRoutingTools checkout was at hand to run `--help`: needs KiCadRoutingTools (CI routing job) and the coordinator's edit of the three rows.
  - 2026-10-08: the three source rows are edited: S-0221 and S-0222 name the tag pages `blob/v2.4.1/docs/command_line_arguments.md` and `blob/v2.4.1/docs/settings.md` (read on 2026-10-05, opened again on 2026-10-08) and what c0109 and c0110 took from them; S-0216 says that `py_router/route.py --help` of the checkout at the tag commit `023d3f79` (run on 2026-10-08, `grid_router` built from the tag) states every flag the plugin passes (`--nets`, `--track-width`, `--via-size`, `--via-drill`, `--clearance`, `--json-out`, `--escalation {off,board,fab}`, `--no-fix-drc-settings`). `uv run pytest tests/unit/test_hypotheses_register.py tests/unit/test_provenance.py`: 44 passed, exit 0.
- [ ] 1.2 Write the measured record of 2026-10-05 into `docs/evidence/routing.md`, section "Scale": the bench, the five runs of `design.md` with their commands, times, CPU seconds, copper, tracks on plane layers, unconnected items, DRC findings by type and machine load, and the statement, checked against the generator script, that the bench is generated by a script written for Fenolite, that its net names and sizes are the generator's and come from no existing board, and that it is not committed (if the script cannot be shown to be so, the numbers are measured again on a bench authored under this task, and the record says which). Proof: `uv run pytest tests/consistency tests/residue`.
  - Open: large-board measurement owed (c0119 or a scheduled run). 2026-10-08: `docs/evidence/routing.md`, section "Scale (c0109)", holds the record of 2026-10-05 copied from the design, per run the command, the nets, the stage times and CPU seconds, the copper, the tracks on plane layers, KiCad's findings and the load. The generator script is not in the repository, so the statement about the bench could not be checked against it; the page says so, and says that the numbers were not measured again. `uv run pytest tests/consistency tests/residue` passes (307 passed, 17 skipped).
  - 2026-10-08: open: measuring the scale bench again needs `kicad-cli` to fill and judge, and Freerouting 2.4.1 needs Java 25 (this machine has `kicad-cli` neither and Java 21); KiCadRoutingTools alone can run here. The bench is to be authored for the purpose (the yardstick of c0119 is one); the record of 2026-10-05 stays marked as not measured again.
- [x] 1.3 Write `test_no_optimizer` and `test_netless` in `tests/routing/test_freerouting_gate.py`, with the netless bench (a left-out net of a class whose clearance is twice the default rule, between two routed nets) in `tests/_specctra.py`; record `dsn-noopt`, `dsn-mt0`, `dsn-netless` and `dsn-inc` in `docs/evidence/routing/freerouting-2.4.1.json`. If `dsn-netless` is `present`, apply the fallback of Decision 4 (`route.net-declared`) and write the measured gap under this task. Proof: `uv run pytest tests/routing/test_freerouting_gate.py -k "no_optimizer or netless" -rA` on the local KiCad 10.0.6.
  - 2026-10-08, jar 2.4.1 (SHA-256 `251101c3…6aa9`), OpenJDK 26.0.2, local `kicad-cli` 10.0.6: 2 passed in 30 s; recorded with `FENOLITE_ROUTING_EVIDENCE=1`. `dsn-noopt` = `absent`, `dsn-mt0` = `present`, `dsn-inc` = `present`.
  - `dsn-netless` = `present`: the fallback of Decision 4 is applied. Measured gap: on `netless_bench` the left-out net B (class clearance 0.4 mm, default rule 0.2 mm) got no session wire, and the straight routes of A and C pass 0.3 mm from its pads; KiCad reports 2 `clearance` violations (0.3 mm where 0.4 mm is required). The same copper judged with B in the default class: 0 violations. So Freerouting 2.4.1 keeps the default rule, and no more, from pins and wiring without a net.
  - The fallback as built: `write_dsn(..., others="netless")` keeps a net outside the job declared when its class clearance is larger than `defaults.clearance`; the plugin names such nets with one `route.net-declared` (info), with its `explain` entry. `dsn-netless-declared` = `absent` (the routes bend away, 0 violations). `H-G-DSN-NETLESS` is recorded as refuted and superseded by `H-G-DSN-NETLESS-2`; the deltas of `specctra-dsn`, `routing` and `kicad-oracle` state the exception and the outcomes as measured. Cost, not measured on a large board: Freerouting also routes a declared net that is still open, and that copper is not taken.
- [x] 1.4 Write `test_group` in `tests/routing/test_krt_gate.py` (the blink with two classes of equal sizes and different clearances) and record `krt-group-t10` locally and `krt-group-t9` inside the pinned 9.0.9 image with the Linux build of the pinned checkout, as `docs/evidence/routing.md` describes. If an outcome is `different`, stop the groups part and write what KiCad reported under this task. Proof: `uv run pytest tests/routing/test_krt_gate.py -k group -rA` on 10.0.6 and in the 9.0.9 image.
  - Open: needs KiCadRoutingTools (CI routing job); 9.0.9 image run owed to the coordinator's image run. 2026-10-08: `test_group` is written (it rewrites the classes of a copy of the built blink to equal sizes and different clearances, routes through `fenolite route --router kicadroutingtools`, asserts one `done` run for the whole selection and compares KiCad's DRC before and after); locally it skips (2 skipped: no checkout).
  - 2026-10-08: ticked by CI run 37772583226 on `04ef42a` (all jobs green): `tests/routing/test_krt_gate.py::test_group` passed for `t9` in the `routing` job of KiCad 9 (pinned 9.0.9 image) and for `t10` in the job of KiCad 10, with the pinned checkout `v0.22.1` and its release asset; the test asserts one `done` run for the whole selection and `equal` (no unconnected item, no new error type), so `krt-group-t9` and `krt-group-t10` are `equal`, recorded in `docs/evidence/routing.md`.

## 2. Protocol and budget

- [x] 2.1 Add `RoutingJob.budget`, `JobNet.tier`, `RouterRun`, `RoutingResult.runs` and `RoutingResult.not_attempted` to `src/fenolite/routing/protocol.py`, `src/fenolite/routing/budget.py` (`Budget`), and `route.budget-exhausted` and `route.optimizer-cut` to `routing/codes.py`, each with its entry (meaning, fix, see) in `src/fenolite/cli/data/explain.toml`, and `route.net-declared` with its entry if task 1.3 took the fallback; write `tests/unit/routing/test_budget.py` for the clock, the kill and `left()` (with a sleeping child process). Proof: `uv run pytest tests/unit/routing -k "budget or protocol or codes" tests/unit/cli/test_explain_cmd.py`; `uv run pyright src`; `uv run pytest tests/unit/test_import_graph.py`.
  - 2026-10-08: 22 passed; `pyright src` 0 errors; import graph 31 passed. `route.net-declared` is in `routing/codes.py` with its entry, because task 1.3 took the fallback.

## 3. KiCadRoutingTools in groups

- [x] 3.1 Extend `tests/_fakerouter.py`: record every run's arguments and input board in a list file; sleep or fail when `--nets` names a given net. Proof: `uv run pytest tests/unit/routing/test_routingtools.py` (the existing scenarios still pass with the extended fake).
  - 2026-10-08: `FAKE_ROUTER_RUNS`, `FAKE_ROUTER_SLEEP_NET`, `FAKE_ROUTER_FAIL_NET`; the appended track's id now derives from the net name, so two runs add two tracks. 13 passed in `test_routingtools.py`.
- [x] 3.2 Route by groups, tiers and `group-nets` with `--escalation off`, `--no-fix-drc-settings` and without `--clearance`; give each run the time left; ignore `nets`, `output` and `overwrite` options; `DEFAULT_BUDGET = 900` (scenarios of "KiCadRoutingTools plugin", "Routing time budget" and "Routing tiers" for this router). Proof: `uv run pytest tests/unit/routing/test_routingtools.py tests/unit/routing/test_budget.py`; `uv run pyright src`.
  - 2026-10-08: 28 passed (`test_routingtools.py`, `test_budget.py`); `pyright src` 0 errors. Two existing tests changed with the behaviour: the recorded arguments hold no `--clearance`, and reaching the limit gives `route.budget-exhausted` where it gave `route.tool-failed`. The plugin always passes `--escalation off --no-fix-drc-settings` and appends the router options after them, so `escalation=board` reaches the tool as a later `--escalation` (that the tool takes the later one is not measured here: no checkout).

## 4. Design files

- [x] 4.1 Add `others` to `write_dsn` in `src/fenolite/backends/specctra/dsn.py` (scenarios of "Nets outside the routing job in design files", the one-pad `unconnected-(` net in both modes included), and a fact row to `docs/formats/specctra/dsn.md` citing `H-G-DSN-NETLESS`. Proof: `uv run pytest tests/unit/backends/specctra/test_dsn.py tests/unit/test_format_facts.py`.
  - 2026-10-08: 79 passed. builds on c0107 (not on this base): `_Writer.plane_nets()` returns no net here, because the writer of this base writes no plane; c0107 fills it. The fact row cites `H-G-DSN-NETLESS-2`, which supersedes `H-G-DSN-NETLESS`.

## 5. Freerouting

- [x] 5.1 Extend `tests/_fakefreerouting.py`: keep the design file of each run; sleep only when the optimizer switch is absent; sleep on a given run. Proof: `uv run pytest tests/unit/routing/test_freerouting.py` (the existing scenarios still pass).
  - 2026-10-08: `FAKE_JAVA_RUNS`, `FAKE_JAVA_SESSION_<n>`, `FAKE_JAVA_SLEEP_RUN`, mode `sleep-optimizer`. 39 passed in `test_freerouting.py`.
- [x] 5.2 Pass `others="netless"` and `--router.optimizer.enabled=false`; one run per tier with earlier copper protected; the budget and `DEFAULT_BUDGET = 900` (scenarios of "Freerouting plugin", "Routing time budget" and "Routing tiers" for this router). Proof: `uv run pytest tests/unit/routing/test_freerouting.py`; `uv run pyright src`.
  - 2026-10-08: 39 passed; `pyright src` 0 errors. Every run has a fresh temporary folder that is its `HOME`. `test_timeout` became `test_budget_cut`: the limit gives `route.budget-exhausted`.
- [x] 5.3 Add `optimize=on` (scenario "Optimizer run cut"). Proof: `uv run pytest tests/unit/routing/test_freerouting.py -k optimize`.
  - 2026-10-08: 4 passed. The optimizer run is a second run of the same design text in a fresh folder; when it is cut, fails or cannot start, the first session is kept and `route.optimizer-cut` is reported.

## 6. Command

- [x] 6.1 Make `--timeout` the budget (no sentinel, a positive value), add `--order`, and add `result.budget`, `result.runs` and `result.not_attempted` in `src/fenolite/cli/cmd_route.py` (scenarios of "Route command budget and tiers"). Proof: `uv run pytest tests/unit/cli/test_route_cmd.py tests/unit/cli/test_hermetic_examples.py tests/consistency`.
  - 2026-10-08: 336 passed, 17 skipped. `result.budget.seconds` is `--timeout`, else the router's `default_budget` (900 for both external routers), else `null`; `spent` is measured only for a router that has a budget, so the reply of `direct` stays the same bytes.

## 7. Oracle

- [x] 7.1 Run both gates and the release acceptance loop with the command lines of this change; the loop is the proof that the two new defaults of Freerouting (optimizer off, other nets netless) still give a board that passes `check`: `test_route` of `tests/routing/test_krt_gate.py` and of `tests/routing/test_freerouting_gate.py` still record `equal` on 10.0.6 and in the 9.0.9 image, and `tests/routing/test_acceptance_loop.py` passes on 10.0.6. Proof: `uv run pytest tests/routing -rA` on the local KiCad 10.0.6 and inside the pinned 9.0.9 image.
  - Open: needs KiCadRoutingTools (CI routing job) for `tests/routing/test_krt_gate.py`; 9.0.9 image run owed to the coordinator's image run for `dsn-route-t9` and the gates under 9.0.9. 2026-10-08, local `kicad-cli` 10.0.6, jar 2.4.1, OpenJDK 26.0.2: `test_route[t10]` of the Freerouting gate passes and records `dsn-route-t10` = `equal` (7 s); `tests/routing/test_acceptance_loop.py` passes, 5 passed in 127 s (blink and `board_40parts` for KiCad 9 and 10 with the optimizer off and the other nets left out: 3 of 3 and 39 of 39 nets closed, no violation, no unconnected item).
  - 2026-10-08: ticked by CI run 37772583226 on `04ef42a` (all jobs green): in both `routing` jobs `tests/routing` passed: `test_route[t9]` of the Freerouting gate and `test_route[t9]` of the KiCadRoutingTools gate under 9.0.9, `test_route[t10]` of both under 10.0.6, `test_no_optimizer`, `test_netless` and the five cases of `tests/routing/test_acceptance_loop.py` (3 of 3 and 39 of 39 nets closed by Freerouting with the optimizer off and the other nets left out).

## 8. Documentation

- [x] 8.1 Update `docs/routing.md` (the budget of the step, kept runs, groups, tiers, the netless design file, the optimizer switch and `optimize=on`, how to continue a cut job with `route` again) and `docs/cli-contract.md` (`--timeout`, `--order`, `result.budget`, `result.runs`, `result.not_attempted`, `route.budget-exhausted`, `route.optimizer-cut`). Proof: `uv run pytest tests/consistency tests/unit/routing -k codes tests/residue`.
  - 2026-10-08: 4 passed (`-k codes`), and `tests/consistency tests/residue` 307 passed, 17 skipped.
- [x] 8.2 If c0080 is archived: add to its guide page one tested line, "`fenolite route --timeout S` bounds the whole step; on `route.budget-exhausted`, run `route` again to continue with the nets still open", with the recipe test c0080 defines. Proof: the guide test of c0080 passes.
  - Open: c0080 is not archived on this base (it is a proposal), so its guide page and its recipe test do not exist. 2026-10-08: one line was added to the guide, which c0079 moved to `src/fenolite/agent/skill/SKILL.md` (the line was written for `agent/SKILL.md` and carried over when this change was rebased onto the stack), "When a step fails" (`route.budget-exhausted`); `tests/unit/test_agent_skill.py` passes (12 passed). Another change moves that guide into the package: the line moves with it.
  - 2026-10-08: c0080 is on the branch (it counts as available): its routing page holds the tested command line `fenolite route blink/build --router freerouting --require-complete --timeout 600 --confirm --json` and the bullet "`--timeout SECONDS` bounds the whole step. When it ends, the copper of the finished runs is written with `route.budget-exhausted` (warning); run `route` again to go on." `uv run pytest tests/unit/agent`: 93 passed, 10 skipped (no `kicad-cli`), exit 0.

## 9. Closing

- [x] 9.1 Run the residue, the fast suite and the unit suite on Python 3.11. Proof: `make check-fast`; `uv run --isolated --python 3.11 --extra dev pytest tests/unit -q -n 4 -p no:cacheprovider` exits 0; after `git add -A`, `uv run pytest tests/residue tests/corpus/test_manifest.py` and `uv run python tools/residue/scan.py` exit 0; `openspec validate c0109-routing-scale-control --strict --no-interactive` passes. The full `make check` is the coordinator's, once, at the merge; this task does not run it.
  - Open: the whole unit suite on Python 3.11 was not run (load rule of the parallel build: focused files only); the coordinator's hand-over run owes it. 2026-10-08: `make check-fast PYTEST_MAX_WORKERS=3` ran once: lint, format, types and residue passed, and 10124 tests passed, 22 skipped, 1 failed (`tests/unit/verify/test_register.py::test_families_of_the_live_register`, which counts the `H-G-DSN-*` rows: 8 became 11 with this change's three rows); the count was corrected and `tests/unit/verify` passes, without a second run of the suite. On Python 3.11 the touched test files pass (253 passed). After `git add -A`: `tests/residue tests/corpus/test_manifest.py` 85 passed, `tools/residue/scan.py` 0 hits, `openspec validate --all --strict` 101 passed.
  - 2026-10-08, on `v04` at `09ee580` with the edits of this pass (branch `v04-close-b`): `make check-fast PYTEST_WORKERS=3`: ruff check, ruff format, the guide check, pyright and the residue scan pass, 12761 passed, 30 skipped, exit 0 (no rerun needed: the two timing tests passed). `uv run --isolated --python 3.11 --extra dev pytest tests/unit -q -n 3 -p no:cacheprovider`: 12378 passed, 26 skipped, exit 0 (three workers, as the coordinator asked, for the four of the proof). After `git add -A`: `uv run pytest tests/residue tests/corpus/test_manifest.py` 82 passed, 3 skipped; `uv run python tools/residue/scan.py` 0 hits; `tools/gen_schemas.py --check` and `tools/gen_evidence_matrix.py --check` exit 0. `openspec validate --all --strict --no-interactive`: five ERRORs, all of other changes (c0084, c0085 twice, c0086, c0128; the one of c0108 is gone) and the long-requirement warnings that every change gives, which the coordinator accepts for this release; this change's own `--strict` run gives no ERROR. The full `make check` and the CI run are the coordinator's.
- [x] 9.2 Update the evidence labels: `H-G-DSN-NOOPT` and `H-G-DSN-NETLESS` become `ORACLE-VERIFIED(freerouting 2.4.1)` and `H-K-KRT-GROUP` `KICAD-VERIFIED (9.0.x, 10.0.x)`, or record what was refuted and the fallback taken; `routingtools.EVIDENCE` and `freerouting.EVIDENCE` name their new rows. Proof: `uv run pytest tests/unit/test_provenance.py tests/unit/test_hypotheses_register.py`.
  - Open: needs KiCadRoutingTools (CI routing job) for `H-K-KRT-GROUP`, which stays `INFERRED`. 2026-10-08: `H-G-DSN-NOOPT` is `ORACLE-VERIFIED(freerouting 2.4.1)`; `H-G-DSN-NETLESS` is recorded as refuted with the fallback taken, and its successor `H-G-DSN-NETLESS-2` is `ORACLE-VERIFIED(freerouting 2.4.1)`; `freerouting.EVIDENCE` names `H-G-DSN-NOOPT` and `H-G-DSN-NETLESS-2`, `routingtools.EVIDENCE` names `H-K-KRT-GROUP`. Proof: 44 passed.
  - 2026-10-08: `H-K-KRT-GROUP` is `KICAD-VERIFIED (9.0.x, 10.0.x)` (CI run 37772583226 on `04ef42a` (all jobs green), task 1.4); `H-G-DSN-NOOPT` is `ORACLE-VERIFIED(freerouting 2.4.1)`, `H-G-DSN-NETLESS` refuted with its successor `H-G-DSN-NETLESS-2` `ORACLE-VERIFIED(freerouting 2.4.1)` (`test_no_optimizer` and `test_netless` passed in both `routing` jobs too); `freerouting.EVIDENCE` names `H-G-DSN-NOOPT` and `H-G-DSN-NETLESS-2`, `routingtools.EVIDENCE` names `H-K-KRT-GROUP` and its docstring says the level. `uv run pytest tests/unit/test_provenance.py tests/unit/test_hypotheses_register.py`: 44 passed, exit 0.
- [x] 9.3 Add to `CHANGELOG.md` under Unreleased: "`fenolite route --timeout` now bounds the whole routing step for every router (it bounded each net for KiCadRoutingTools), keeps the copper of every router run that finished in time and reports the rest with `route.budget-exhausted`; KiCadRoutingTools routes groups of nets of equal sizes in one process; Freerouting is given only the nets of the job and runs without its optimizer unless `--router-option optimize=on`; new `--order GLOB`; no model or schema change". In `docs/roadmap.md`, section "v0.4", say that c0109 is built. Proof: `git diff --stat CHANGELOG.md docs/roadmap.md` lists both files.
  - Open: roadmap/README edited by the coordinator. 2026-10-08: the entry is at the end of `## [Unreleased]` of `CHANGELOG.md`; `docs/roadmap.md` is not touched.
  - 2026-10-08: the changelog entry of task 9.3 is in `[Unreleased]`, and a line under `### Changed` records this pass; `docs/roadmap.md`: the row of c0109 says it is built on `v04`, with a paragraph "c0109 on `v04`". `git diff --stat CHANGELOG.md docs/roadmap.md` lists both.
