lgili/Fenolite/openspec/changes/c0110-route-pairs-fanout/tasks.md

## 0. Entry check

- [x] 0.1 Read the living `routing`, `specctra-dsn`, `cli-contract` and `kicad-oracle` specs, `openspec list` and the archived c0104 and c0107. Write under this task, with the date: that `0.3.0` is released; that c0104 (`model.pairs`, the class pair values, `diff_pair_skew`) and c0107 (`RoutingJob.plane_layers`, `JobNet.layers`, `design_rules` in `route`, the plane fan-out) are archived, else stop; that c0108 and c0109 are archived, else stop (Decision 14: candidates from c0108's selection, the steps inside c0109's budget and tiers); then regenerate the MODIFIED "Freerouting plugin" from the living text, full text and every scenario, and re-apply only this change's two edits (`--router.automatic_neckdown=false` always, the option `fanout`); that `docs/evidence/sources.md` still leaves S-0662 to S-0665 free; which fields `RoutingJob` holds last, so that `pairs` and `escape` come after them; and whether `PINNED_TAG` and `PINNED_VERSION` are still `v0.22.1` and `2.4.1` (else the gate runs on the new pins and the hypotheses name them). Proof: `openspec validate c0110-route-pairs-fanout --strict --no-interactive` passes.
  - 2026-10-08, on `v04` at `30bbffd`: `0.3.0` is not released (the last tag is `v0.2.1`), and c0104, c0107, c0108 and c0109 are not archived but are built and stacked on `v04` (commits `775a85d`, `6d47d06`, `98db1be`, `ae4e868`), which this line takes as their state; c0078 is stacked too (`b6dd44d`). `RoutingJob` ends with `budget`, `on_run` and `progress` (c0109, c0120), so `pairs` and `escape` come after them. The MODIFIED "Freerouting plugin" is regenerated from the text c0109's delta leaves (location with `jar_source`, `others="netless"`, Tiers, Optimizer, Messages and its twelve scenarios) with only this change's two edits (`--router.automatic_neckdown=false` always, the option `fanout`) and the scenario "Fanout stage off, neck-down never on". `docs/evidence/sources.md` left S-0662 to S-0665 free. `PINNED_TAG` is `v0.22.1` and `PINNED_VERSION` `2.4.1`. `openspec validate c0110-route-pairs-fanout --strict --no-interactive` reports no ERROR; it exits 1 on nine requirement-length WARNINGs that the unchanged change on `origin/v04` gives alike.

## 1. Probe and register (the feasibility gate)

- [x] 1.1 Add the rows `H-K-KRT-PAIR`, `H-K-KRT-PAIRNAMES`, `H-K-KRT-ESCAPE`, `H-G-DSN-PAIR`, `H-G-DSN-NARROW`, `H-G-DSN-FANOUT` and `H-K-DRU-PAIRCOUPLE` to `docs/hypotheses.md` (level `INFERRED`, the tests and criteria of `design.md`, result `pending` with the measurements of Context as the first record), and S-0662 to S-0665 to `docs/evidence/sources.md` after opening each at its tag (address, licence, what was read, date). Proof: `uv run pytest tests/unit/test_hypotheses_register.py tests/unit/test_provenance.py`; `grep -cE '^\| S-066[2-5] ' docs/evidence/sources.md` prints `4`; `grep -cE '^\| (H-K-KRT-PAIR|H-K-KRT-PAIRNAMES|H-K-KRT-ESCAPE|H-G-DSN-PAIR|H-G-DSN-NARROW|H-G-DSN-FANOUT|H-K-DRU-PAIRCOUPLE) ' docs/hypotheses.md` prints `7`.
  - 2026-10-08: the seven rows are at the end of `docs/hypotheses.md` (`INFERRED`, result pending with the measurements of 2026-10-05), S-0662 to S-0665 at the end of `docs/evidence/sources.md`; S-0662, S-0663 and S-0664 were opened again on 2026-10-08 (the maintainer's answer on S-0664 is not shown to a reader without an account). Proof: the two tests pass (66 with `test_format_facts.py`); the greps print 4 and 7.
- [x] 1.2 Write `tests/kicad/rules/test_pair_coupling.py`: an authored bench of script copper with one pair 0.15 mm apart and one 1.07 mm apart, judged with the four rules files of measurement 2; register the probes `dru-pair-couple-<case>` for majors 9 and 10 (requirement "Pair coupling in KiCad's DRC is probed"). If an outcome differs from measurement 2, correct Decision 11 and the gate criteria before task 1.4. Proof: `uv run pytest tests/kicad/rules/test_pair_coupling.py -rA` on the local KiCad 10.0.6 and inside the pinned 9.0.9 image; both probe files hold the outcomes.
  - 2026-10-08: `tests/kicad/rules/_couplebench.py` (the bench: `CA` 0.15 mm apart, `CB` 1.07 mm apart, 20 mm, four rules files) and `tests/kicad/rules/test_pair_coupling.py` (marked `needs_kicad`) are written; the probe functions are `_couplebench.couple_probes()`. They are not added to `_probes.PROBES` yet: an id there without its outcome in the probe files of both majors fails `tests/kicad/test_probe_results.py`. Open: owed: needs kicad-cli/router; judged by GitHub CI (routing job); then add `couple_probes()` to `_probes.PROBES` and write both probe files with `FENOLITE_PROBES_WRITE=1`.
  - 2026-10-08: ticked by CI run 37772583226 on `04ef42a` (all jobs green): `tests/kicad/rules/test_pair_coupling.py` passed its four cases in the `kicad-9` job (pinned 9.0.9 image) and in the `kicad-10` job (10.0.6); each asserts the outcome of measurement 2 with the scoped canary, so Decision 11 and the gate criteria stand. `couple_probes()` is in `_probes.PROBES` for both majors, and the four `dru-pair-couple-<case>` outcomes (`present`) are written into `9.0.9.json` and `10.0.6.json` from that run; `tests/kicad/test_probe_results.py` runs them again in the next CI run. `H-K-DRU-PAIRCOUPLE` is `KICAD-VERIFIED (9.0.x, 10.0.x)`.
- [x] 1.3 Author the benches `tests/routing/_pairbench.py`, `_namebench.py` and `_escapebench.py` (the pair, name, QFN and BGA benches of Context; the QFN and BGA benches with c0107's plane layers and fan-out, and a board-wide `hole_clearance` rule of 0.15 mm on the BGA bench, Context 6), each built through the DSL for targets 9 and 10 into a temporary folder; the pair bench carries c0104's `pair(gap_min=0.13mm, gap_max=0.17mm, uncoupled_max=6mm, skew_max=0.1mm)` and a board minimum width of 0.15 mm (Context 3). Proof: `uv run pytest tests/routing -k bench_builds` builds the eight projects and `kicad-cli` 10.0.6 loads each target-10 board; `uv run pytest tests/residue`.
  - Open: owed: needs kicad-cli/router; judged by GitHub CI (routing job). Not written on 2026-10-08: the QFN-48 and BGA-121 benches need fine-pitch footprints that the built-in catalog does not hold (it has no QFN, BGA or 1.27 mm header), and nothing here can load a board in `kicad-cli`.
  - 2026-10-08: written; awaits the CI run. The benches are `tests/routing/_routepairbench.py` (the task's `_pairbench.py`: that name is taken by c0104's `tests/kicad/rules/_pairbench.py`, which shares the import path of a whole run), `_namebench.py` and `_escapebench.py`, with footprints and symbols authored in `_gateparts.py` (headers of 1.27 mm, a QFN-48, an 11 by 11 BGA; the catalog holds none of them), each built through the DSL by `fenolite build`. `uv run pytest tests/routing -k bench_builds`: 8 passed (the four benches for targets 9 and 10, their nets, pads and four copper layers); `tests/routing/test_gate_benches.py::test_bench_loads` (the board of the running major in `kicad-cli`) skips here and runs in the `routing` jobs. `uv run pytest tests/residue`: passed.
  - 2026-10-08, on `v04-ci-ticks` from `origin/v04` at `38fecbd`: done. Both `routing` jobs of CI run 37803522539 on `a105cc0` (images `kicad/kicad:9.0.9` and `kicad/kicad:10.0.6`, `uv run pytest tests/routing -q -rA`) passed `test_bench_builds` for the eight projects (`pair`, `name`, `qfn`, `bga`, targets 9 and 10) and `test_bench_loads` for the board of the running major, with the same counts on both: `pair` 2 violations and 8 unconnected items, `name` 2 and 10, `qfn` 2 and 47, `bga` 3 and 119 (unrouted benches). The residue run of task 8.1 covers the bench files.
- [x] 1.4 Write `tests/routing/test_pair_gate.py` (`test_krt_pair`, `test_krt_names`, `test_dsn_pair_ignored`), using only the calls named in Decision 1, and a helper that appends each outcome to `docs/evidence/routing.md` and to the tools' result files when `FENOLITE_ROUTING_EVIDENCE=1`. Run it on 10.0.6 for target 10 and inside the 9.0.9 image, with the tool mounted, for target 9. Write the pair verdict under this task. Proof: `FENOLITE_REQUIRE=kicad,router,freerouting uv run pytest tests/routing/test_pair_gate.py -rA` on both majors; `docs/evidence/routing.md` holds `krt-pair-t9`, `krt-pair-t10`, `krt-pair-names` and `dsn-pair-ignored`.
  - Open: owed: needs kicad-cli/router; judged by GitHub CI (routing job); it needs the benches of task 1.3. Verdict: pending.
  - 2026-10-08: written; awaits the CI run. `tests/routing/test_pair_gate.py` (`test_krt_pair`, `test_krt_names`, `test_dsn_pair_ignored`) uses the calls of Decision 1 (`fenolite build`, `read_board`, `write_board`, `write_dsn`, `read_session`, `routing.merge.apply`, `subprocess`, `kicad-cli`) through `_gate.py` and `_pairgate.py`; each test prints its outcome and, with `FENOLITE_ROUTING_EVIDENCE=1`, appends it to `docs/evidence/routing.md` and the tool's results file. `krt-pair-names` = `equal`, recorded with a local checkout of `v0.22.1` (`test_krt_names` needs no `kicad-cli`): the four forms of `PAIR_NAME_FORMS` routed as pairs, `DP1`/`DN1` given no copper. The steps of `test_krt_pair` ran here to their end (both pairs "coupled" by the tool's own report, the four single nets routed); its judge and `test_dsn_pair_ignored` (Java 25) run in the `routing` jobs. Verdict: pending.
  - 2026-10-08, on `v04-ci-ticks`: done. Both `routing` jobs of CI run 37803522539 passed `test_pair_gate.py` (`-rA`): `krt-pair-t9` = `equal` (9.0.9: unconnected 0; pair findings none; new error types none; skew none; `route_diff.py` 0.7 s, `route.py` 0.9 s), `krt-pair-t10` = `equal` (10.0.6: the same, 0.6 s and 0.8 s), `krt-pair-names` = `equal` in both, `dsn-pair-ignored` = `equal` in both (p00, p01, p02: exit 0, 3.2 s, session). **Pair verdict: pass** (both `krt-pair-t<M>` `equal`, Decision 1). The outcomes are in `docs/evidence/routing.md` ("Pairs and escape (c0110)"), and in `docs/evidence/routing/krt-v0.22.1.json` and `freerouting-2.4.1.json`, written from the printed lines in the form of `_gate.record` (the jobs do not set `FENOLITE_ROUTING_EVIDENCE`).
- [x] 1.5 Write `tests/routing/test_escape_gate.py` (`-k krt`, `-k dsn`, `-k narrow`): the QFN and BGA benches with and without the escape, at most 900 s per run, recording open signal connections, new error types, wall time and vias inside pads. Run it on 10.0.6 for target 10 and judge the target-9 boards inside the 9.0.9 image. Write the escape verdict under this task. Proof: `FENOLITE_REQUIRE=kicad,router,freerouting uv run pytest tests/routing/test_escape_gate.py -rA`; `docs/evidence/routing.md` holds the eight `*-escape-*` outcomes per major, `dsn-narrow-fanout` and `dsn-narrow-off`.
  - Open: owed: needs kicad-cli/router; judged by GitHub CI (routing job); it needs the benches of task 1.3. Verdict: pending.
  - 2026-10-08: written; awaits the CI run. `tests/routing/test_escape_gate.py` (`-k krt`, `-k dsn`, `-k narrow`) with `_escapegate.py`: the QFN and BGA benches with c0107's fan-out, with and without the escape step, every tool run bounded by `FENOLITE_GATE_SECONDS` (900 by default), recording open signal connections, new error types, seconds and vias inside a pad. Here, without `kicad-cli`, the KiCadRoutingTools steps ran to their end (QFN: 40 of 40 pins escaped, `route.py` in 55 s, 63 s without the escape; BGA: 96 of 96 balls escaped, `route.py` in 225 s, stopped at a 300 s limit without the escape); the verdict is KiCad's, in the `routing` jobs. Verdict: pending.
  - 2026-10-08, on `v04-ci-ticks`: done. Both `routing` jobs of CI run 37803522539 passed `test_escape_gate.py` (`-rA`; `test_narrow` in the 10.0.6 job only, as written). 9.0.9 and 10.0.6 alike: `krt-escape-qfn-t<M>` = `equal` (with `qfn_fanout.py` 0 open, 0 vias in a pad; `route.py` alone 4 open, 1 via in a pad), `krt-escape-bga-t<M>` = `different` (with `bga_fanout.py --escape-method dogbone` 22 open, 7 vias in a pad; alone 16 open, 17 vias in a pad), `dsn-escape-qfn-t<M>` = `equal` (fanout stage 0 open; off 1), `dsn-escape-bga-t<M>` = `improved` (stage 10 open; off 11; sessions in 429 s to 471 s); no new error type anywhere; every run under 900 s. 10.0.6: `dsn-narrow-fanout` = `present` (13 wires under 0.15 mm, the narrowest 0.1124 mm), `dsn-narrow-off` = `absent`. **Escape verdict: fail for KiCadRoutingTools** (`krt-escape-bga-t<M>` `different` on both majors). The two BGA outcomes differ from this design's Context (measurement 6: dog-bones 7 open against 96, no via in a pad; e40 to e42: no Freerouting session within 900 s); they are recorded as observed (design, "Gate outcomes and verdict"). Written into `docs/evidence/routing.md` and the two results files.
- [x] 1.6 Apply the verdict (Decision 1): make `fanout=off` Freerouting's default if the gate shows it better on both benches and majors (Decision 10); for each step whose gate failed, delete its requirement from `specs/routing/spec.md`, its scenarios and tasks here, and refute the register row with a successor that names the open connections or violations; record the verdict and its consequence in `docs/evidence/routing.md` and `docs/roadmap.md`. Proof: `openspec validate c0110-route-pairs-fanout --strict --no-interactive` passes; `git diff --stat docs/evidence/routing.md docs/roadmap.md` lists both files.
  - Open: waits for the verdicts of tasks 1.4 and 1.5. Until then `kicadroutingtools` declares no feature (`GATED_FEATURES` names what it implements), `fanout` stays on by default, and the requirements stay as written.
  - 2026-10-08: waits for the verdicts of tasks 1.4 and 1.5, which the next `routing` jobs print.
  - 2026-10-08, on `v04-ci-ticks`: done. Verdict of Decision 1: pairs pass, escape fails. `fanout=off` is not better (QFN 1 open against 0, BGA 11 against 10, on both majors), so the fanout stage stays on by default (Decision 10). For the failed escape step: the requirement "KiCadRoutingTools escapes parts" and its two scenarios are deleted from `specs/routing/spec.md` (and its name from `proposal.md`; the `kicad-oracle` delta names the scripts instead and its loop routes pairs only); `H-K-KRT-ESCAPE` is refuted by `H-K-KRT-ESCAPE-2`, which states the open connections and vias in pads; `H-G-DSN-FANOUT`, whose BGA clause also failed, by `H-G-DSN-FANOUT-2`. Task 4.2 is kept, with a note, since its code stays (default taken, design "Gate outcomes and verdict": `--escape`, `routing.escape` and the escape steps were built before the gate; no router declares `escape`, so a request gives `route.escape-skipped`; removing them is left to the maintainer). The verdict and its consequence are in `docs/evidence/routing.md` and `docs/roadmap.md`; `git diff --stat docs/evidence/routing.md docs/roadmap.md` lists both. `openspec validate` was not run: no `openspec` binary on this machine.

## 2. Protocol, pairs and escape requests

- [x] 2.1 Add `JobPair`, `JobEscape`, `RoutingJob.pairs`, `RoutingJob.escape`, `ROUTER_FEATURES` and `router_features` to `src/fenolite/routing/protocol.py`, the four codes (`route.pair-skipped`, `route.pair-uncoupled`, `route.escape-skipped`, `route.width-below-job`) to `routing/codes.py`, each with its entry (meaning, fix, see) in `src/fenolite/cli/data/explain.toml`, and extend `tests/unit/routing/test_protocol.py` (scenarios of "Pairs and escape in a routing job"). Proof: `uv run pytest tests/unit/routing/test_protocol.py tests/unit/routing -k codes tests/unit/cli/test_explain_cmd.py tests/unit/test_import_graph.py`; `uv run pyright src`.
  - 2026-10-08: `JobPair`, `JobEscape`, `RoutingJob.pairs` and `.escape` (after `progress`), `ROUTER_FEATURES`, `router_features`; the four codes with their `explain.toml` entries. Proof: the named tests pass (44 and 1 with `-k codes`); `uv run pyright src` 0 errors.
- [x] 2.2 Write `src/fenolite/routing/pairs.py` (`job_pairs`) and `tests/unit/routing/test_pairs.py` (scenarios of "Pair selection for routing", plus two classes and a rule of severity `ignore`). Proof: `uv run pytest tests/unit/routing/test_pairs.py tests/unit/test_import_graph.py`.
  - 2026-10-08: `routing/pairs.py`; `tests/unit/routing/test_pairs.py` 8 passed with the import graph.
- [x] 2.3 Write `src/fenolite/routing/escape.py` (`escape_kind`, `pitch`, `requests`) and `tests/unit/routing/test_escape.py` (scenarios of "Escape requests for routing", with pad centres written in the test: an 11 × 11 grid of 0.8 mm, a QFN-48 of 0.5 mm with a centre pad, a 2 × 20 header, each at 0°, 45° and 90°). Proof: `uv run pytest tests/unit/routing/test_escape.py`.
  - 2026-10-08: `routing/escape.py` (`escape_kind`, `pitch`, `parse`, `requests`, `PartPad`); `tests/unit/routing/test_escape.py` 11 passed.

## 3. Command and capabilities

- [x] 3.1 Add `--escape` and `--pairs-as-nets`, the pair and escape stages, the feature check, the width guard and `result.pairs`, `result.escape` to `src/fenolite/cli/cmd_route.py` (Decisions 5, 10, 12, 13); author `tests/data/kicad/routing/pair_two_headers.kicad_pcb` through the model API with its row in `tests/data/MANIFEST.toml`; extend `tests/unit/cli/test_route_cmd.py` (scenarios of "Pairs and escape in the route command"). Proof: `uv run pytest tests/unit/cli/test_route_cmd.py tests/unit/cli/test_hermetic_examples.py tests/consistency`; after `git add -A`, `uv run pytest tests/corpus/test_manifest.py`.
  - 2026-10-08: the board `pair_two_headers.kicad_pcb` comes with its project file (`pair_two_headers.kicad_pro`: the class `HS` and its pair values, which a KiCad board does not hold); both are written by `pair_triad` of `test_route_cmd.py`, which checks the committed files, and have their manifest rows. Proof: the named tests pass (417 passed, 19 skipped); `tests/corpus/test_manifest.py` 47 passed after `git add -A`.
- [x] 3.2 Add `features` to each router entry of `capabilities` and extend `tests/unit/cli/test_capabilities.py` (scenario "Features listed"). Proof: `uv run pytest tests/unit/cli -k capabilities tests/consistency`.
  - 2026-10-08: `features` in the default view only (the brief view keeps `name`, `available`, `reason`). Proof: 50 passed.

## 4. KiCadRoutingTools steps (only those the verdict of task 1.6 keeps)

- [x] 4.1 Add the pair steps as runs of c0109's budget (each listed in `RoutingResult.runs`, before the groups of its tier), `PAIR_NAME_FORMS` (equal to `krt-pair-names`) and the refused options to `src/fenolite/routing/plugins/kicad/routingtools.py`, a fake `route_diff.py` to `tests/_fakerouter.py`, and the scenarios of "KiCadRoutingTools routes pairs" to `tests/unit/routing/test_routingtools.py`. Proof: `uv run pytest tests/unit/routing/test_routingtools.py -k "pair or option"`; `uv run pyright src`.
  - 2026-10-08: the pair steps, `PAIR_NAME_FORMS`, `tool_pairs`, `REFUSED_OPTIONS`; the fake writes `route_diff.py` too. `PAIR_NAME_FORMS` is the measurement of 2026-10-05 until `krt-pair-names` is recorded (task 1.4). Proof: `test_routingtools.py` 24 passed; pyright 0 errors.
- [x] 4.2 Add the escape steps (Decision 9), as runs of c0109's budget before the first tier, and fake `bga_fanout.py` and `qfn_fanout.py`, with the scenarios of "KiCadRoutingTools escapes parts". Proof: `uv run pytest tests/unit/routing/test_routingtools.py -k escape`.
  - 2026-10-08: the escape steps before every pair and net step; fakes `bga_fanout.py` and `qfn_fanout.py` (`FAKE_ESCAPE_FAIL`). Proof: `-k escape` passes (in the 24 above).
  - 2026-10-08: the requirement this task implements was removed by the verdict of task 1.6 (`krt-escape-bga-t<M>` `different`); the escape steps and their unit tests stay in the plugin, undeclared (`DECLARED_FEATURES` holds `pairs` only), as recorded probes for a later pin of the tool.
- [x] 4.3 Declare `features` as the verdict allows, and check that `capabilities` lists them. Proof: `uv run pytest tests/unit/routing tests/unit/cli -k "features or capabilities"`.
  - Open: the verdict of task 1.6 is pending, so `KicadRoutingToolsRouter.features` stays empty and `capabilities` lists no feature for it (`test_capabilities.py::test_features`).
  - 2026-10-08: waits for the verdict of task 1.6.
  - 2026-10-08, on `v04-ci-ticks`: done. `KicadRoutingToolsRouter.features` is `DECLARED_FEATURES = frozenset({"pairs"})` (task 1.6), and `fenolite capabilities` lists `["pairs"]` for `kicadroutingtools` and none for `direct` and `freerouting` (`test_capabilities.py::test_features`, `test_routingtools.py::test_features_are_declared_only_after_the_gate` updated with the reason). `uv run pytest tests/unit/routing tests/unit/cli -k "features or capabilities"`: passed; the whole of `tests/unit/routing tests/unit/cli` passes.

## 5. Freerouting and the Specctra file

- [x] 5.1 Always pass `--router.automatic_neckdown=false`, take the option `fanout` (`fanout=off` adds `--router.fanout.enabled=false`), declare no feature (`src/fenolite/routing/plugins/specctra/freerouting.py`), and extend `tests/unit/routing/test_freerouting.py` (scenarios of "Freerouting plugin" and "Freerouting declares no router feature"). Proof: `uv run pytest tests/unit/routing/test_freerouting.py`.
  - 2026-10-08: `features = frozenset()`, `NECKDOWN_OFF` always, `FANOUT_OFF` for `fanout=off`. Proof: 44 passed.
- [x] 5.2 Add the scenario "No pair list" to `tests/unit/backends/specctra/test_dsn.py` and the fact row of the `pair` list to `docs/formats/specctra/dsn.md` with `H-G-DSN-PAIR`. Proof: `uv run pytest tests/unit/backends/specctra/test_dsn.py -k pair tests/unit/test_format_facts.py`.
  - 2026-10-08: the fact row cites S-0224 and S-0664 with `H-G-DSN-PAIR`, `INFERRED`. Proof: the `-k pair` test and `test_format_facts.py` pass.

## 6. Oracle through the command

- [ ] 6.1 Switch `test_krt_pair` and the escape tests to `fenolite route --router kicadroutingtools [--escape …] --confirm`, add `test_loop` for the pair bench (build, route, fill, build twice; routes kept, last build byte-equal), and run them. Proof: `FENOLITE_REQUIRE=kicad,router uv run pytest tests/routing/test_pair_gate.py tests/routing/test_escape_gate.py -rA` on the local KiCad 10.0.6 and in the `routing` CI job on 9.0.9.
  - Open: owed: needs kicad-cli/router; judged by GitHub CI (routing job); it needs tasks 1.3 to 1.5 and a declared feature.
  - 2026-10-08: waits for the verdict of task 1.6 and a declared feature.
  - 2026-10-08, CI run 37803522539: still open. The escape half is dropped by the verdict of task 1.6 (no `--escape` run of `kicadroutingtools` to switch to); the pair half needs `test_krt_pair` switched to `fenolite route --router kicadroutingtools --confirm`, now that `pairs` is declared, and `test_loop` for the pair bench, both run under `kicad-cli` with the tool (a `routing` job), which this machine cannot do.

## 7. Documentation

- [x] 7.1 Update `docs/routing.md` (one paragraph that tells c0107's plane fan-out, Freerouting's fanout stage and this change's escape apart; pairs: which nets, the class values, the forms the tool pairs, both rules to judge a pair; escape: `--escape`, the kinds, the steps, via-in-pad and hole clearance; features; Freerouting's neck-down and `fanout`; limits), `docs/cli-contract.md` (the options, `result.pairs`, `result.escape`, `features`, the four codes) and `docs/evidence/routing.md` (the gate tables). If c0080 is archived, add one tested line for `--escape` and one for `--pairs-as-nets` to its guide page. Proof: `uv run pytest tests/consistency tests/unit/test_repo_layout.py tests/residue`.
  - 2026-10-08: `docs/routing.md` (section "Differential pairs and escape"), `docs/cli-contract.md` (options, `result.pairs`, `result.escape`, `features`, the four codes, `fanout=off`) and `docs/evidence/routing.md` (section "Pairs and escape (c0110)", outcomes pending). c0080 is not archived, so no guide line is added; `tools/gen_agent_guide.py` regenerated `references/commands.md`. Proof: the three test paths pass.

## 8. Closing

- [x] 8.1 Run the residue, the fast suite and the unit suite on Python 3.11. Proof: `make check-fast`; `uv run --isolated --python 3.11 --extra dev pytest tests/unit -q -n 4 -p no:cacheprovider` exits 0; after `git add -A`, `uv run pytest tests/residue tests/corpus/test_manifest.py` and `uv run python tools/residue/scan.py` exit 0; `openspec validate c0110-route-pairs-fanout --strict --no-interactive` passes. The full `make check` is the coordinator's, once, at the merge; this task does not run it.
  - Open: not run here (an agent of this line runs targeted tests only). Run on 2026-10-08: `uv run ruff check .`, `uv run ruff format --check .`, `uv run pyright src`, every `tools/gen_*.py --check`, and `uv run pytest tests/residue tests/corpus/test_manifest.py` exit 0.
  - 2026-10-08, on `v04` at `09ee580` with the edits of this pass (branch `v04-close-b`): `make check-fast PYTEST_WORKERS=3`: ruff check, ruff format, the guide check, pyright and the residue scan pass, 12761 passed, 30 skipped, exit 0 (no rerun needed: the two timing tests passed). `uv run --isolated --python 3.11 --extra dev pytest tests/unit -q -n 3 -p no:cacheprovider`: 12378 passed, 26 skipped, exit 0 (three workers, as the coordinator asked, for the four of the proof). After `git add -A`: `uv run pytest tests/residue tests/corpus/test_manifest.py` 82 passed, 3 skipped; `uv run python tools/residue/scan.py` 0 hits; `tools/gen_schemas.py --check` and `tools/gen_evidence_matrix.py --check` exit 0. `openspec validate --all --strict --no-interactive`: five ERRORs, all of other changes (c0084, c0085 twice, c0086, c0128; the one of c0108 is gone) and the long-requirement warnings that every change gives, which the coordinator accepts for this release; this change's own `--strict` run gives no ERROR. The full `make check` and the CI run are the coordinator's.
- [x] 8.2 Update the evidence labels: the seven rows become `KICAD-VERIFIED (9.0.x, 10.0.x)` or `ORACLE-VERIFIED(<tool>)` with their scope and runs, or are refuted with a successor; `routingtools.EVIDENCE` and `freerouting.EVIDENCE` name the new rows; the fact row of the `pair` list takes the label of `dsn-pair-ignored`. Proof: `uv run pytest tests/unit/test_provenance.py tests/unit/test_hypotheses_register.py tests/kicad/test_probe_results.py tests/unit/test_format_facts.py`.
  - Open: waits for the gate; the seven rows stay `INFERRED`, and `routingtools.EVIDENCE` and `freerouting.EVIDENCE` name no new row until they are recorded.
  - 2026-10-08: `H-K-DRU-PAIRCOUPLE` is `KICAD-VERIFIED (9.0.x, 10.0.x)` (CI run 37772583226 on `04ef42a` (all jobs green)) and `H-K-KRT-PAIRNAMES` `ORACLE-VERIFIED(kicadroutingtools 0.22.1)` (local run of `test_krt_names`); the five other rows wait for the gate's outcomes in the next `routing` jobs, and `routingtools.EVIDENCE` and `freerouting.EVIDENCE` name no new row until then.
  - 2026-10-08, on `v04-ci-ticks`: done, from CI run 37803522539. `H-K-KRT-PAIR` is `KICAD-VERIFIED (9.0.x, 10.0.x)`; `H-K-KRT-PAIRNAMES` stays `ORACLE-VERIFIED(kicadroutingtools 0.22.1)` and records both jobs; `H-G-DSN-PAIR` is `ORACLE-VERIFIED(freerouting 2.4.1)` (both jobs) and `H-G-DSN-NARROW` `ORACLE-VERIFIED(freerouting 2.4.1)` (the 10.0.6 job); `H-K-KRT-ESCAPE` and `H-G-DSN-FANOUT` are refuted (level of the refuting runs, `KICAD-VERIFIED (9.0.x, 10.0.x)`) by `H-K-KRT-ESCAPE-2` and `H-G-DSN-FANOUT-2`, both `KICAD-VERIFIED (9.0.x, 10.0.x)`; `H-K-DRU-PAIRCOUPLE` was already `KICAD-VERIFIED (9.0.x, 10.0.x)`. `routingtools.EVIDENCE` names `H-K-KRT-PAIR` and `H-K-KRT-PAIRNAMES` (not the escape rows: the feature is not declared), `freerouting.EVIDENCE` names `H-G-DSN-PAIR`, `H-G-DSN-NARROW` and `H-G-DSN-FANOUT-2`; the fact row of the `pair` list in `docs/formats/specctra/dsn.md` is `ORACLE-VERIFIED`. `uv run pytest tests/unit/test_provenance.py tests/unit/test_hypotheses_register.py tests/unit/test_format_facts.py`: passed; `tests/kicad/test_probe_results.py` needs `kicad-cli` (skipped here; this change writes nothing to the probe files).
- [x] 8.3 Add to `CHANGELOG.md` under Unreleased: "`fenolite route` routes differential pairs with KiCadRoutingTools (`route_diff.py`) and escapes fine-pitch parts (`--escape`); a pair goes only to a router that routes pairs, or as single nets with `--pairs-as-nets` (`route.pair-skipped`); Freerouting runs without automatic neck-down and takes `fanout=off`; routed copper narrower than asked gives `route.width-below-job`", naming only the parts the verdict kept, and "no model or schema change". In `docs/roadmap.md`, section "v0.4", say that c0110 is built and what the gate's verdict was. Proof: `git diff --stat CHANGELOG.md docs/roadmap.md` lists both files.
  - 2026-10-08: one line at the end of Unreleased, naming that the steps are not declared until the gate holds, and a paragraph "c0110 on `v04`" under the v0.4 section of `docs/roadmap.md`. Proof: `git diff --stat CHANGELOG.md docs/roadmap.md` lists both.
