lgili/Fenolite/openspec/changes/c0111-copper-part-anchors/tasks.md

## 0. Entry check

- [x] 0.1 Read the living `board-frame`, `manual-copper`, `design-dsl` and `kicad-oracle` specs and `openspec list`. Write under this task, with the date: whether `0.3.0` is released and which of c0096 and c0080 are on `dev`; whether "Stitching vias" still reads as at `9aba2dff`, where c0068 and c0074 are archived (if a change has modified it since, regenerate the MODIFIED delta from the living text and re-apply this change's edits: the opening sentence, the first bullet, "Region", "Pad region", the exemption in "Clearance", the last sentence of "Keep-outs and the edge" and the four new scenarios); whether c0107 or c0112 holds a delta of a requirement this change extends; and whether another change has added public names to `frame.py`, `copper.py` or `fenolite.dsl` that clash with `PartFrame`, `part_frame`, `AnchorLike`, `AnchorRef` or `Anchor`. Proof: `openspec validate c0111-copper-part-anchors --strict --no-interactive` passes after any re-base; `grep -c "Keep-outs and the edge" openspec/changes/c0111-copper-part-anchors/specs/manual-copper/spec.md` prints `1`.
  - 2026-10-07, on the integration base of milestone v0.4 `f36e08d9` (`dev` plus the 28 proposals): `0.3.0` is not released (the tags end at `v0.2.1`); c0096 is not on the base, and c0080 is there as a proposal only (0 of 15 tasks), so neither is implemented. "Stitching vias" of the living `manual-copper` reads as at `9aba2dff`: a line diff of the living requirement against this change's delta shows only this change's edits (the opening sentence, the first bullet, "Region", the new "Pad region", the exemption in "Clearance", the last sentence of "Keep-outs and the edge" and the four new scenarios), so the delta was not regenerated. No other open change holds a delta of "Stitching vias", "Copper intents in the DSL", "Copper module", "Tracks from intents", "Single vias" or "Board-frame module"; c0107 and c0112 hold none (the "Copper issue codes" of c0085 is the requirement of `altium-build`). No public name of `frame.py`, `copper.py` or `fenolite.dsl` clashes with `PartFrame`, `part_frame`, `AnchorLike`, `AnchorRef` or `Anchor`. Proof: `openspec validate c0111-copper-part-anchors --strict --no-interactive` exit 0 (valid); the `grep -c` prints `1`.
  - 2026-10-07, at `origin/dev` `9aba2dff` (proposal repaired, nothing built): c0068 and c0074 are archived; no open change on `dev` holds a delta of "Stitching vias"; `frame.py` exports `COURTYARD_LAYERS`, `CURVE_GROWTH`, `EVIDENCE`, `FRAME_ISSUE_CODES`, `board_pads`, `copper_polygon`, `find_pads`, `placed_extent` and `placed_extents`, none of the new names; `0.3.0` is not released, and c0096 and c0080 are not on `dev`.

## 1. Probe and register

- [x] 1.1 Add the rows `H-G-FRAME-ANCHOR` and `H-K-VIA-IN-PAD` to `docs/hypotheses.md` (backend `kicad`, level `INFERRED`, the tests and criteria of `design.md`, result `pending` with measurement 4 of 2026-10-05 as the first record), and the two facts with their labels to `docs/formats/kicad/frame.md`: the map of an anchored point, and KiCad's verdicts on vias inside an SMD pad (own net joined: none; own net alone: `via_dangling`; another net: re-netted, no `shorting_items`). Proof: `uv run pytest tests/unit/test_hypotheses_register.py tests/unit/test_provenance.py tests/unit/test_format_facts.py`; `grep -cE '^\| (H-G-FRAME-ANCHOR|H-K-VIA-IN-PAD) ' docs/hypotheses.md` prints `2`.
  - 2026-10-07: both rows and both fact rows are written, with the level `INFERRED` and the 10.0.6 run of this day as their record. `grep -cE …` prints `2`. Open because the proof command exits 1: `uv run pytest tests/unit/test_hypotheses_register.py tests/unit/test_provenance.py tests/unit/test_format_facts.py` gives 65 passed, 1 failed, and the one failure, `test_cited_ids_registered`, names only `openspec/changes/c0140-part-height-rules/design.md` (line 116), which cites the body-height row of c0099 that `docs/hypotheses.md` does not hold: a file of the base `f36e08d9` that this change does not touch, so the test fails on the base too. It names no id of this change. Tick when that row is registered.
  - 2026-10-08, on `v04-close-c` from `origin/v04` at `d6e6a19`: ticked. `uv run pytest tests/unit/test_hypotheses_register.py tests/unit/test_provenance.py tests/unit/test_format_facts.py`: 66 passed, exit 0 (the row that c0140 cites is registered on `v04`); `grep -cE …` prints `2`.
- [x] 1.2 Author `tests/data/libs/Frame.pretty/Frame_Anchor.kicad_mod` (CC0, format 20241229: the pads and the courtyard of `design.md`) with its row in `tests/data/MANIFEST.toml`. Add to `tests/unit/backends/kicad/test_frame_pads.py` a test that reads it and finds pads `1` to `4` at those positions. Proof: `uv run pytest tests/corpus/test_manifest.py tests/residue tests/unit/backends/kicad/test_frame_pads.py -k frame_anchor`.
  - 2026-10-07: `Frame_Anchor.kicad_mod` authored (generated by a scratch script from the sizes of `design.md`, uuids `f8000000-…`), its row at the end of `tests/data/MANIFEST.toml`, and `test_frame_anchor_footprint_pads` added. Proof run without `-k` restricting the manifest and residue files: `uv run pytest tests/corpus/test_manifest.py tests/residue tests/unit/backends/kicad/test_frame_pads.py -k "frame_anchor or manifest or residue"`: 86 passed, 22 deselected, exit 0.
- [x] 1.3 Probes first, before any code of sections 2 to 4: write `tests/kicad/frame/_anchorbench.py` and `test_anchor_oracle.py` with the frame and thermal benches of "Anchored copper passes the oracle", every anchored point computed by the test with `Transform.placement(at, θ, mirror=side == "bottom")` and given to `Design.via` and `Design.track` as a board point, and the thermal array as nine such vias in pad `4`; register `copper-anchor-frame`, `copper-anchor-frame-control`, `copper-anchor-thermal` and `copper-anchor-thermal-alone` in `tests/kicad/_probes.py` for majors 9 and 10. If `copper-anchor-frame` is not `equal` or `copper-anchor-thermal` not `absent` on a major, stop the change and write the report into the register rows. Proof: `uv run pytest tests/kicad/frame/test_anchor_oracle.py -k "frame or thermal" -rA` on the local KiCad 10.0.6 and inside the pinned 9.0.9 image; `FENOLITE_PROBES_WRITE=1` updates both probe files.
  - 2026-10-07: open for KiCad 9.0.9 (no docker in this run; the `kicad-9` job runs it), and done out of order: the code of sections 2 to 4 was written before the bench, against the task's "probes first". The bench has the computed form (`frame_script(computed=True)`, `thermal_script(computed=True)`: every point computed with `Transform.placement` and given as a board point, the array as nine vias), and it was run on the local `kicad-cli` 10.0.6 before the anchored form: frame bench no problem (36 markers named with the net of their pad, no `shorting_items`), control `different`, joined thermal array nothing named, array alone 9 `via_dangling`, copper guard silent on both thermal builds. So measurement 4 of the proposal holds at this base on 10.0.6. The four probes are registered for majors 9 and 10. `docs/evidence/kicad/probes/10.0.6.json` holds the six `copper-anchor-*` outcomes, written by a script that calls `_probes.run` for these six and keeps the writer's format; the other 557 outcomes were not run again. `9.0.9.json` is untouched: `FENOLITE_PROBES_WRITE=1` in the pinned image must add the six rows, and until then `tests/kicad/test_probe_results.py` fails in the `kicad-9` job.
  - 2026-10-08: ticked by the second local run of 2026-10-08 in the pinned 9.0.9 image (`kicad/kicad:9.0.9@sha256:e638b79b…`, linux/amd64, branch `v04-k9-probes-2`; whole `tests/kicad` without the corpus: 998 passed, 2 failed, 806 skipped, 1 xfailed; `tests/kicad/test_probe_results.py` passed on the 723 probes of major 9): `tests/kicad/frame/test_anchor_oracle.py` 6 passed; the six rows are in `9.0.9.json`, merged by name (`copper-anchor-frame` `equal`, `-frame-control` `different`, `-moved` `absent`, `-moved-control` `present`, `-thermal` `absent`, `-thermal-alone` `present`). The order of the work stays as the note above says.

## 2. Board frame

- [x] 2.1 Add `PartFrame` and `part_frame` to `src/fenolite/backends/kicad/frame.py`, re-export `part_frame` from `fenolite.backends.kicad`, and write `tests/unit/backends/kicad/test_frame_anchor.py` (the five scenarios of "Anchor points in a part's frame", the every-pad sweep included). Proof: `uv run pytest tests/unit/backends/kicad/test_frame_anchor.py tests/unit/backends/kicad/test_frame_pads.py tests/unit/test_import_graph.py`; `uv run pyright src`.
  - 2026-10-07: `uv run pytest tests/unit/backends/kicad/test_frame_anchor.py tests/unit/backends/kicad/test_frame_pads.py tests/unit/test_import_graph.py`: 61 passed, exit 0; `uv run pyright src`: 0 errors, exit 0. `frame.py` also holds `frame_with_pads`, not in `__all__`: `part_frame` over pad records the caller already has, which `resolve_copper` uses so that it builds the records once.

## 3. DSL

- [x] 3.1 Add `Part.at`, `PadRef.at`, `AnchorRef` and `Anchor`; the one-argument point of `via_step` and `Design.via`; anchors in track paths, `arc_to` and the `along`, `region` and `origin` of a stitch; `region=PadRef`; the refusals; the `copper()` output; the re-exports (`src/fenolite/dsl/intents.py`, `part.py`, `design.py`, `__init__.py`). Write `tests/unit/dsl/test_copper_anchors_dsl.py` (the six scenarios of "Copper anchors in the DSL"); every test of `tests/unit/dsl/test_copper_dsl.py` passes unchanged. Proof: `uv run pytest tests/unit/dsl tests/unit/test_import_graph.py`; `uv run pyright src`.
  - 2026-10-07: `uv run pytest tests/unit/dsl tests/unit/test_import_graph.py`: 443 passed, exit 0 (`test_copper_dsl.py` unchanged); `uv run pyright src`: 0 errors. `AnchorRef` has a read-only property `component` (the part's path), so that the recorded forms satisfy the resolver's protocols.

## 4. Resolution

- [x] 4.1 Add `AnchorLike` and the anchor pass of `resolve_copper` (path elements, via steps, arc steps, via intents, the `along` and `region` points and the `origin` of a stitch) with the codes of "Anchored points in script copper"; write `tests/unit/backends/kicad/test_copper_anchor.py` (its five scenarios), and extend the closed-set test of `test_copper_issues.py` so that the anchor cases produce their five codes with the table's severities. Proof: `uv run pytest tests/unit/backends/kicad -k copper`; `uv run pyright src`.
  - 2026-10-07: `uv run pytest tests/unit/backends/kicad -k copper`: 164 passed, 2111 deselected, exit 0; `uv run pyright src`: 0 errors. `test_anchor_cases_use_the_closed_set` produces the five codes with the table's severities; `test_closed_set` still finds no other `kicad.copper.*` literal in the module.
- [x] 4.2 Add pad regions, the grid of an anchored origin and the exemption of the region's pads to `_resolve_stitch`; extend `tests/unit/backends/kicad/test_copper_stitch.py` with the four new scenarios of "Stitching vias" (the five living ones unchanged) and a comparison of the exact inside test with a 10 µm sampling of rect, roundrect, circle and oval pads at 0° and 30°: no sampled candidate is kept whose disc leaves the pad. Proof: `uv run pytest tests/unit/backends/kicad/test_copper_stitch.py tests/unit/backends/kicad -k copper`.
  - 2026-10-07: `uv run pytest tests/unit/backends/kicad/test_copper_stitch.py`: 47 passed, exit 0 (the living scenarios unchanged; the four new ones, six more cases, and the sampling comparison on the circle, rect, oval and roundrect pads of `Frame_Shapes` at 0° and 30°: no kept candidate whose disc leaves the pad, none refused that stays 2 µm inside); `-k copper` over the folder as in 4.1.
- [x] 4.3 Extend `tests/unit/lens/test_build_copper.py` with a variant of the routed blink that holds an anchored via and an anchored waypoint: built twice for targets 9 and 10 with different seeds and `PYTHONHASHSEED` values, every file has the same bytes; rebuilt over its board after `tests/_layout_edit.py::move_footprint` moved `U1`, its anchored items keep their uuids, move with `U1`, and give `kicad.copper.regenerated`. Proof: `uv run pytest tests/unit/lens/test_build_copper.py -k anchor`.
  - 2026-10-07: `uv run pytest tests/unit/lens/test_build_copper.py -k anchor`: 4 passed, 14 deselected, exit 0 (targets 9 and 10: two processes with seeds and `PYTHONHASHSEED` 1 and 2 write the same bytes; after `move_footprint` moved `U1` by 2 mm the anchored via and waypoint keep their uuids, move with it, and are reported as `kicad.copper.regenerated`). The variant unlocks `U1`, because a locked `place()` wins over the board.
- [x] 4.4 The second backend: extend `tests/unit/cli/test_build_altium_script_copper.py` with the anchored variant of the routed blink built with `--target altium --dry-run --json`: the planned `.PcbDoc` read back holds the anchored via at the point `part_frame` gives, and a variant whose anchor names pad `7` of `R1` exits 5 with `kicad.copper.pad-not-found` and plans no file. Proof: `uv run pytest tests/unit/cli/test_build_altium_script_copper.py -k anchor`.
  - 2026-10-07: `uv run pytest tests/unit/cli/test_build_altium_script_copper.py -k anchor`: 2 passed, 9 deselected, exit 0. A dry run writes no bytes to read back: the test asserts the dry run's plan and counts (12 tracks, 8 vias), then reads the document of a confirmed build of the same script, whose anchored via is at the point `part_frame` gives within one file unit. The variant with pad `7` of `R1` exits 5 with `kicad.copper.pad-not-found` on `--dry-run` and plans no file.

## 5. Oracle

- [x] 5.1 Move the benches of task 1.3 to the script's anchors: `part.at` and `pad.at` for the markers, the anchored track and `stitch(region=part.pad(4))` for the thermal array; the board points computed by the test stay only in the control. The four probes keep their outcomes (scenarios "Anchors land in their pads" and "A thermal array passes DRC"). Proof: `uv run pytest tests/kicad/frame/test_anchor_oracle.py -k "frame or thermal" -rA` on the local KiCad 10.0.6 and inside the pinned 9.0.9 image.
  - 2026-10-07: open for KiCad 9.0.9 only. On the local `kicad-cli` 10.0.6: `FENOLITE_REQUIRE=kicad uv run pytest tests/kicad/frame/test_anchor_oracle.py -rA`: 6 passed, exit 0; with the script's anchors `copper-anchor-frame` = `equal`, `copper-anchor-frame-control` = `different`, `copper-anchor-thermal` = `absent`, `copper-anchor-thermal-alone` = `present`, and the copper guard reports nothing on the thermal builds. The board points computed by the test stay in the control and in the `computed` form of the scripts.
  - 2026-10-08: ticked: the `frame` and `thermal` tests of `tests/kicad/frame/test_anchor_oracle.py` pass inside the pinned 9.0.9 image with the script's anchors (the run named under task 1.3); the four probes keep their outcomes.
- [x] 5.2 Add the moved-part benches and the probes `copper-anchor-moved` and `copper-anchor-moved-control` for majors 9 and 10 (scenario "Anchored copper follows a moved part"). Proof: `uv run pytest tests/kicad/frame/test_anchor_oracle.py -k moved -rA` on both majors; `uv run pytest tests/kicad/test_probe_results.py`.
  - 2026-10-07: open for KiCad 9.0.9 and for `tests/kicad/test_probe_results.py`, which runs every probe of the running major and was not run. On 10.0.6 (the run of 5.1): `copper-anchor-moved` = `absent` after `fenolite place --move U1=40mm,24mm,90 --confirm` and a rebuild (`place.copper-left` from `place`; the rebuild reports `kicad.copper.regenerated` for the 9 vias and the 8 track segments), `copper-anchor-moved-control` = `present` (9 `via_dangling`).
  - 2026-10-08: ticked: the `moved` test passes inside the pinned 9.0.9 image (`copper-anchor-moved` `absent`, `copper-anchor-moved-control` `present`), and `tests/kicad/test_probe_results.py` passed there (the run named under task 1.3) and on the local 10.0.6.

## 6. Documentation

- [x] 6.1 Update `docs/dsl.md` ("Copper": anchors, the one-argument point, the thermal stitch, one short example, and one sentence on the word "anchor": a point in a part's frame here, not the reason of a locked placement of c0096 nor the reference side of `near` of c0113, each named only if it is on `dev` by then), `docs/copper.md` (the map and when it is applied; anchors never join a pad; the codes of anchors and of pad regions beside the table; pad regions, their grid and their exemption, and that keep-outs and the edge still drop their candidates; KiCad re-nets a via of another net inside a pad, so only the copper guard reports it; `via_dangling` for vias joined on one layer; protection of in-pad vias is c0112's), and `docs/placement.md` (script copper follows a moved part at the next build when its tracks end at pads or its points are anchors; copper given by board points stays). Proof: `uv run pytest tests/consistency tests/unit/test_repo_layout.py tests/residue`.
  - 2026-10-07: `uv run pytest tests/consistency tests/unit/test_repo_layout.py tests/residue`: 304 passed, 15 skipped, exit 0. Neither c0096 nor c0113 is implemented on the base, so the sentence on the word "anchor" in `docs/dsl.md` names neither.
- [x] 6.2 If c0080 is on `dev`, add one tested `fenolite-design` line with `part.pad(n).at()` and `stitch(region=part.pad(n))` to its `routing` page, and `Anchor` and `AnchorRef` to its list of DSL names that the guide does not teach, with their reasons (the module of that list is named by c0079 and c0080 as they land; the maintainer's decision 9 of 2026-10-07 renames the agent package); otherwise write under this task that c0080 is not on `dev`. Proof: `uv run pytest tests/unit/agent -q` when c0080 is on `dev`; else `git log --oneline -1 -- openspec/changes/c0080-agent-authoring-guide` prints nothing.
  - 2026-10-07: c0080 is not implemented: it is on the base as a proposal (0 of 15 tasks), and no guide page exists to add a line to. The proof's `git log --oneline -1 -- openspec/changes/c0080-agent-authoring-guide` prints the proposal's commit (`543494b2`) on this base, so the task stays open for the change that lands second.

## 7. Closing
  - 2026-10-08, on `v04-close-c` (`d6e6a19`): c0080 is on `v04` with every task closed, so it counts as available for v0.4. Its `routing` page already used `r1.pad(1).at(dx=mm(-4))` as a waypoint; added to its `fenolite-design` block `design.stitch("d1_thermal", net=gnd, pitch=mm(1), region=d1.pad(2), …)`, one via at the centre of pad 2 of `D1` (built for target 10: the via at `(114.2, 106)`), and one sentence on `region=part.pad(n)`. `Anchor` and `AnchorRef` were already in `fenolite.agent.guide.DSL_NOT_TAUGHT` with the reason "a record that a call of the script returns; a script never names it". `uv run pytest tests/unit/agent -q`: 79 passed, 10 skipped (the `kicad-cli` cases), exit 0. The page's KiCad case `tests/unit/agent/test_pages_kicad.py::test_kicad_routed_script_passes_after_fill` runs the new via in the `kicad-10` job.

- [x] 7.1 Stop and report "ready for the long runs"; an agent in a worktree does not run the full `make check` (AGENTS.md: one full suite, by the coordinator, on the rebased branch at the merge). Proof: `make check-fast PYTEST_WORKERS=4` exits 0; `uv run --isolated --python 3.11 --extra dev pytest tests/unit -q -n 4 -p no:cacheprovider` exits 0; after `git add -A`, `uv run pytest tests/residue tests/corpus/test_manifest.py` and `uv run python tools/residue/scan.py` exit 0; `openspec validate c0111-copper-part-anchors --strict --no-interactive` and `openspec validate --all --strict --no-interactive` pass; `python3 tools/dco_check.py <base>..HEAD` prints nothing. The jobs `unit`, `kicad-9` and `kicad-10` are read by the coordinator after the merge.
  - 2026-10-07: open: `make check-fast` fails on this base in `test_cited_ids_registered` for the id that c0140's design cites (see 1.1), and the whole unit suite on Python 3.11 is the coordinator's. Run here: `make check-fast PYTEST_WORKERS=3`: ruff, format, pyright and the residue scan pass, then 9599 passed, 18 skipped and that 1 failed (exit 2), the nine touched unit files and `test_copper_tracks.py` on Python 3.11 (`uv run --isolated --python 3.11 --extra dev pytest …`: 218 passed, exit 0), `uv run pytest tests/corpus/test_manifest.py tests/residue`: 85 passed, `uv run python tools/residue/scan.py`: 0 hits, `openspec validate --all --strict --no-interactive`: 100 passed, `uv run python tools/gen_schemas.py --check` and `tools/gen_evidence_matrix.py --check`: exit 0, nothing to regenerate.
  - 2026-10-08, on `v04-close-c` from `origin/v04` at `d6e6a19`, with the edits of this closing round staged: `make check-fast PYTEST_WORKERS=3` exits 0 (ruff, format, pyright, residue scan; 12888 passed, 29 skipped; a first run failed only on `tests/unit/test_evidence_matrix_page.py` before `docs/evidence/matrix.md` was regenerated); `uv run --isolated --python 3.11 --extra dev pytest tests/unit -q -n 3 -p no:cacheprovider` exits 0 (12497 passed, 25 skipped); `uv run pytest tests/residue tests/corpus/test_manifest.py` (82 passed, 3 skipped) and `uv run python tools/residue/scan.py` (0 hits) exit 0; `uv run python tools/gen_schemas.py --check` exits 0; `openspec validate --all --strict --no-interactive` gives only the errors that were there before (c0084, c0085 twice, c0086, c0108, c0128) and long-requirement warnings; `python3 tools/dco_check.py origin/v04..HEAD` prints nothing. Three workers in place of four, as parallel agents share the machine. The jobs `unit`, `kicad-9` and `kicad-10` were last all green in CI run 37772583226 on `04ef42a`; this round's commits are read by the coordinator after the merge.
- [x] 7.2 Update the evidence labels: `H-G-FRAME-ANCHOR` and `H-K-VIA-IN-PAD` become `KICAD-VERIFIED (9.0.x, 10.0.x)` with the runs, or record what was refuted and the part stopped; the fact rows of `docs/formats/kicad/frame.md` take the same labels. Proof: `uv run pytest tests/unit/test_provenance.py tests/unit/test_hypotheses_register.py tests/kicad/test_probe_results.py tests/unit/test_format_facts.py`.
  - 2026-10-07: open: the 9.0.9 half is not measured, so both rows and both fact rows stay `INFERRED` with the 10.0.6 runs as their record. After the `kicad-9` job: set the four places to `KICAD-VERIFIED (9.0.x, 10.0.x)`, or record what 9.0.9 showed.
  - 2026-10-08: after the image run named under task 1.3, `H-G-FRAME-ANCHOR` and `H-K-VIA-IN-PAD` are `KICAD-VERIFIED (9.0.x, 10.0.x)`. Still open: the two fact rows were not raised by the commit that recorded the probes; CI has still to confirm the 9.0.9 half.
  - 2026-10-08: ticked. The two fact rows of `docs/formats/kicad/frame.md` are `KICAD-VERIFIED (9.0.x, 10.0.x)`: `tests/kicad/frame/test_anchor_oracle.py` is unchanged since `04ef42a`, and its six tests passed in the all-green CI run 37772583226 on `04ef42a` (job `kicad-9`: `PASSED` for each of the six in its `-rA` log; job `kicad-10`: 3003 passed, none of them among the skips; neither job deselects a marker). `uv run pytest tests/unit/test_provenance.py tests/unit/test_hypotheses_register.py tests/kicad/test_probe_results.py tests/unit/test_format_facts.py`: 66 passed, 1 skipped (no `kicad-cli` here), exit 0.
- [x] 7.3 Add to `CHANGELOG.md` under Unreleased: "Script copper can be given in a part's frame: `part.at(dx, dy)` and `part.pad(n).at(dx, dy)` stand wherever a point is taken, and the build resolves them after placement, so vias, waypoints and stitches follow a moved part at the next build. `design.stitch(region=part.pad(n))` makes a thermal via array inside a pad. `part_frame` gives the same points to the Python API." Update the row c0111 of `docs/roadmap.md` (section of v0.4). Proof: `git diff --stat CHANGELOG.md docs/roadmap.md` lists both files.
  - 2026-10-07: the entry is at the end of "Unreleased" in `CHANGELOG.md`. Open: the row c0111 of `docs/roadmap.md` is the coordinator's edit in this wave, so `git diff --stat` lists `CHANGELOG.md` only.
  - The CHANGELOG line of this round is under `### Changed` of `## [Unreleased]`, and the row of this change in `docs/roadmap.md` (v0.4, the complex board) says what ships in 0.4. `git diff --stat CHANGELOG.md docs/roadmap.md` lists both files.
