lgili/Fenolite/openspec/changes/c0112-via-protection/tasks.md

## 0. Entry check

- [x] 0.1 Read the living `design-model`, `kicad-file-backend`, `manual-copper`, `design-dsl`, `layout-lens`, `kicad-oracle`, `cli-contract`, `altium-build`, `altium-pcb-writer` and `altium-import` specs and `openspec list`. Check the prerequisites of the proposal and write under this task, with the date and the commit of `dev`: release `0.3.0` cut, with c0085, c0128, c0124 and c0132 archived; read the living "Via records" and "Tracks, arcs and vias" and correct "Via tenting flags" and "Via tenting of imported vias" where a sentence of theirs would contradict them (the signature of `via_record`, the flags sentence, the fields of the imported `Via`). c0100, c0101 and c0103 landed: regenerate the MODIFIED deltas of "Created board header", "Modelled board content" and "Projected fields on write" from the living text, full text and every scenario, and re-apply only this change's sentence, bullet and scenarios. Whether c0096, c0099, c0121, c0126, c0108 or c0118 landed (then build `VIA_FIELDS`, `CANONICAL_ORDER["via"]`, the `Via` and `Board` fields, the `Design.via` and `Design.stitch` keywords and `tools/gen_schemas.py` on their code). That the six hypothesis ids and the four issue codes are still free (`docs/hypotheses.md`, `src/fenolite/cli/data/explain.toml`). Proof: `openspec validate c0112-via-protection --strict --no-interactive` passes after the regeneration; `git diff --stat openspec/changes/c0112-via-protection/specs` lists the regenerated files, and the word runs by which each MODIFIED block differs from the living text are written under this task.
  - Open (2026-10-07): needs c0100 and c0103 on the branch. Done tonight on `v04-impl-c0112`, based on `0ea988da` (`v04` at `991b3f57` plus c0101): the ten living specs and `openspec list` were read; release `0.3.0` is not cut and c0085, c0124, c0128 and c0132 are implemented on the branch and not archived, so their texts of "Via records" and "Tracks, arcs and vias" were read in their change folders: no sentence contradicts the two ADDED requirements. The three MODIFIED deltas were regenerated from the delta text of c0101, which modifies all three (not from the living spec), and must be regenerated again when c0100 and c0103 land. Word runs by which each block differs from c0101's text: "Modelled board content": `, and \`protection\` from the children of "Via protection on boards"` (and `and` moved before it), the sentence `\`Board.via_protection\` MUST be the projection of the same opaque \`setup\` child … either.`, and the scenario "Protected via and board default"; "Created board header": `, and followed inside \`setup\`, after \`pad_to_mask_clearance\`, by the children of "Via protection defaults on boards" when \`Board.via_protection\` is not \`None\``, and the scenario "Created board with a via protection default"; "Projected fields on write": the bullet `When \`Board.via_protection\` differs …`, and the scenarios "Via protection default added to a read board", "A projected via child edited" and "A kept 9.0 child written for target 10". None of c0096, c0099, c0126, c0108 or c0118 is on the branch (c0121 is: it adds no field to `Via`). The six hypothesis ids and the four issue codes were free. `openspec validate c0112-via-protection --strict --no-interactive` passes.
  - 2026-10-08, after the rebase onto `be2c01ec` (c0100, c0108 and c0101 on the branch): the three deltas were regenerated again from the text the tip leaves: "Created board header" from c0100's delta as c0101's rebased delta carries it (the scenarios "Six and eight copper layers" and "Counts outside the table" came in), "Modelled board content" and "Projected fields on write" from c0101's delta; this change's word runs are those listed above. c0108 adds no delta of the three (it ADDS "Copper locks on boards"); its `locked` child and field were re-based in `VIA_FIELDS`, `CANONICAL_ORDER["via"]`, `Via`, the intents and the keywords, and the schema was regenerated. The task stays open only for c0103, which is not on the branch.
  - 2026-10-08, on `v04-close-c` from `origin/v04` at `d6e6a19`, where c0100, c0101, c0102 and c0103 are on the branch with every task closed (none archived; `0.3.0` is released by c0150, archived, with its record `docs/release/v0.3.md`; this clone holds no tag `v0.3.0`): "Modelled board content" was regenerated again, from c0103's delta, the last text the tip leaves (c0103 had re-based its own delta on c0101 and this change, so it already carries this change's runs); the block is now word for word c0103's. The word runs by which it differs from c0101's text are those listed above for this change ("`, and \`protection\` from the children of …`", the `Board.via_protection` sentence, the scenario "Protected via and board default") plus c0103's runs, which this change does not own (the `name` child of a rule area, the justification of `gr_text`, the `dimension` bullet and its four scenarios). "Created board header" and "Projected fields on write" were compared with c0101's delta (which carries c0100's): they differ only by this change's runs, so they stand. c0096, c0099, c0108, c0118, c0121 and c0126 are on the branch; `Via` holds `protection` and `locked` and no other new field, `tools/gen_schemas.py --check` exits 0, and the six hypothesis ids are registered once. `openspec validate c0112-via-protection --strict --no-interactive` reports only the long-requirement warnings of its ADDED requirements, none on a MODIFIED block.

## 1. Probe and register

- [x] 1.1 Add the rows `H-K-VIAPROT-FORMS`, `H-K-VIAPROT-MASK`, `H-K-VIAPROT-NINE`, `H-K-VIAPROT-UPGRADE` and `H-K-VIAPROT-OUTPUTS` to `docs/hypotheses.md` (backend `kicad`, level `INFERRED`, the tests and criteria of `design.md`, result `pending` with the measurements of 2026-10-05 as the first record) and the row `H-A-PCB-CU-VIATENT` (backend `altium`, level `INFERRED`, result `pending (author report)`), and extend the "used for" cells of S-0020, S-0029, S-0037, S-0058 and S-0125, and of S-0160 for the written tenting flags, in `docs/evidence/sources.md`. Proof: `uv run pytest tests/unit/test_hypotheses_register.py tests/unit/test_provenance.py`; `grep -cE '^\| H-K-VIAPROT-(FORMS|MASK|NINE|UPGRADE|OUTPUTS) ' docs/hypotheses.md` prints `5`.
  - Done: 2026-10-07. The six rows are at the end of the table of `docs/hypotheses.md`. The "used for" cells of S-0020, S-0029, S-0037, S-0058, S-0125 and S-0160 were not extended: shared files are append-only tonight; one row S-0630 was appended instead (the re-reading of the eight public PCB documents). `tests/unit/test_hypotheses_register.py tests/unit/test_provenance.py` pass; the `grep` prints 5.
- [x] 1.2 Write the facts benches of `tests/kicad/vias/_viabench.py` (token edits on `write_board` output, as design measurement 3), `flashes(text)` in `tests/kicad/zones/_gerber.py` with its rows in `docs/formats/kicad/gerber.md` (S-0125), the folder in `tests/kicad/conftest.py`, the probes `via-prot-mask`, `via-prot-upgrade`, `via-prot-outputs`, `via-prot-default-outputs` and `via-prot-load-nine` in `tests/kicad/_probes.py`, and their tests in `tests/kicad/vias/test_via_protection_oracle.py`. An outcome other than the design's stops the change and goes back to the design. Proof: `FENOLITE_PROBES_WRITE=1 uv run pytest tests/kicad/vias/test_via_protection_oracle.py -k "mask or upgrade or outputs" -rA` on the local `kicad-cli` 10.0.6; `uv run pytest tests/kicad/test_probe_results.py tests/unit/test_format_facts.py`.
  - Done: 2026-10-07 on the local `kicad-cli` 10.0.6: `via-prot-mask` `equal`, `via-prot-upgrade` `different`, `via-prot-outputs` `equal`, `via-prot-default-outputs` `absent`: the outcomes of the design. The probe file was updated by running only these probes and merging their outcomes (`10.0.6.json`), as c0101 did. `tests/unit/test_format_facts.py` passes; `tests/kicad/test_probe_results.py` runs every probe of the oracle and is the coordinator's.
- [x] 1.3 Run the 9.0.9 half (`-k "mask or nine"`) in one container and record it in `9.0.9.json`. Proof: `FENOLITE_KICAD_CLI="docker:kicad/kicad:9.0.9@sha256:e638b79b0321f29395a5b783e94bb9f3c73303e8da15da27b8f5cb4b67a37729" FENOLITE_PROBES_WRITE=1 uv run pytest tests/kicad/vias/test_via_protection_oracle.py -k "mask or nine" -rA`, or the `kicad-9` job; `via-prot-mask` is `equal` and `via-prot-load-nine` is `reject` in `9.0.9.json`.
  - Done: 2026-10-07 with `kicad-cli` 9.0.9 in the pinned image (`kicad/kicad:9.0.9@sha256:e638b79b…`, linux/amd64, local run with the worktree mounted; the `docker:` form of `FENOLITE_KICAD_CLI` is not read by the test runner): `via-prot-mask` `equal` and `via-prot-load-nine` `reject`, merged into `9.0.9.json`; 8 passed, 4 skipped (10.0 only).

## 2. Model

- [x] 2.1 Add `ViaProtection`, `Via.protection` and `Board.via_protection` to `src/fenolite/model/board.py`, regenerate `schemas/fenolite.model.v0/board.json`, and write `tests/unit/model/test_via_protection.py` (scenarios of "Via protection in the board model"). Add the two fields to `docs/design-model.md` with the sentence "0.2.x and 0.3.0 cannot read a `board.json` that carries `protection` or `via_protection`". Proof: `grep -n "cannot read" docs/design-model.md` shows the sentence; `uv run pytest tests/unit/model/test_via_protection.py tests/unit/test_schema_drift.py`; `uv run python tools/gen_schemas.py --check`; `uv run pyright src`.
  - Done: 2026-10-07. The fixture of c0101 (`tests/data/model/v0.2.1/blink_2layer.board.json`) loads and dumps byte-equal; it holds no via, so a second test builds a board with vias. 23 passed with `tests/unit/test_schema_drift.py`.

## 3. Via children

- [x] 3.1 Write `src/fenolite/backends/kicad/via_protection.py` (`FEATURES`, `SUPPORT`, `KICAD_DEFAULT`, `effective_default`, `effective`, `project_via`, `emit_via` with both forms and the `protection_none` pair, `EVIDENCE`), wire it into `pcb.py` (`VIA_FIELDS`, `CANONICAL_ORDER["via"]`, the reader by `form_major`, the emitter by target), and add the token rows `covering-front`, `covering-back`, `plugging-front` and `plugging-back`. Write `tests/unit/backends/kicad/test_via_protection_read.py` and `test_via_protection_write.py` (the 10.0 and 9.0 scenarios of "Via protection on boards", "Protected via and board default" of "Modelled board content"). Proof: `uv run pytest tests/unit/backends/kicad/test_via_protection_read.py tests/unit/backends/kicad/test_via_protection_write.py tests/unit/backends/kicad/test_inventory.py tests/unit/backends/kicad -k pcb`; `uv run pyright src`.
  - Done: 2026-10-07, without the four token rows (design, "Found on 2026-10-07", item 3: the inventory's own rule cannot hold for them). Each protection child is a slot field of its own name.
- [x] 3.2 Target 9: the one-sided tenting resolved from the default, the refusal `kicad.board.via-protection-too-new` in `pcb.WRITE_ISSUE_CODES` with its table in `cli/data/explain.toml`, and the rewrite of a projected via child ("Projected fields on write", "A projected via child edited"). Proof: `uv run pytest tests/unit/backends/kicad/test_via_protection_write.py -k "target_9 or refused or projected" tests/unit/cli/test_explain_cmd.py`.
  - Done: 2026-10-07. A kept 9.0 child is also rewritten when the target is not the board's major (design, item 5).
- [x] 3.3 Add `test_via_protection` to `tests/corpus/test_board_census.py` and copy its census into `docs/evidence/kicad-board-read.md`; RT1 holds with no protection child opaque. Proof: `FENOLITE_CENSUS_OUT=<file> uv run pytest tests/corpus/test_board_census.py -k via_protection tests/corpus/test_board_rt1.py -rA` with the corpus cached; `git status --porcelain` lists no file under the cache.
  - Done: 2026-10-07 with the corpus cached: 444, 6 and 2 vias as the census of 2026-10-05; no protection child opaque; `tests/corpus/test_board_rt1.py` 22 passed, 2 heavy items skipped. The census is in `docs/evidence/kicad-board-read.md`, "Via protection".

## 4. Board default

- [x] 4.1 Add `project_setup`, `setup_children` and `rewrite_setup`; set `Board.via_protection` in `read_board`; write the created `setup` children and rewrite a read board's (scenarios of "Via protection defaults on boards", "Created board with a via protection default", "Via protection default added to a read board"). If c0101 is archived, one test also edits the stack-up of the same board and checks that each projection rewrote only its own children. Proof: `uv run pytest tests/unit/backends/kicad/test_via_protection_write.py tests/unit/backends/kicad/test_pcb_write.py -k "via_protection or created or projected"`.
  - Done: 2026-10-07. c0101 is on the branch (not archived): `test_stackup_and_default_edited_together` edits both projections of one `setup`.

## 5. Script

- [x] 5.1 Add `protect`, the `protection=` keyword of `Design.via`, `via_step` and `Design.stitch`, the `protection` field of `ViaStep`, `ViaIntent` and `StitchIntent`, and the re-export, with `tests/unit/dsl/test_via_protection_dsl.py` (scenarios of "Via protection in the DSL"); every existing test of `tests/unit/dsl/test_copper_dsl.py` passes unchanged. Proof: `uv run pytest tests/unit/dsl tests/unit/test_import_graph.py`.
  - Done: 2026-10-07. `tests/unit/dsl/test_copper_dsl.py` is unchanged and passes.
- [x] 5.2 Read `protection` in `copper.py` for via steps, via intents and stitches, compare it in `_fields`, and refuse another type (scenarios of "Via protection of script copper"). Proof: `uv run pytest tests/unit/backends/kicad -k copper`.
  - Done: 2026-10-07. The tests are appended to `tests/unit/backends/kicad/test_copper_tracks.py` (`-k protection`).
- [x] 5.3 Add `Design.via_protection`, `to_model`, `via_protection_locked`, `build_design(lock_via_protection=)`, the call in `cmd_build.py` and `not_exported` with the table of `kicad.via.protection-not-exported` in `cli/data/explain.toml`, with `tests/unit/lens/test_build_via_protection.py` (scenarios of "Via protection defaults in the DSL"). Proof: `uv run pytest tests/unit/dsl tests/unit/lens/test_build_via_protection.py tests/unit/lens tests/unit/cli/test_explain_cmd.py tests/consistency`.
  - Done: 2026-10-07.

## 6. Rebuilds

- [x] 6.1 Add `merge_default`, `DefaultMerge` and `ISSUE_CODES`, applied by `build_design` after `merge_layout` and not by the normal-form pass, the tables of `kicad.via.protection-overridden` and `kicad.via.protection-forced` in `cli/data/explain.toml`, with `tests/unit/backends/kicad/test_via_protection_merge.py` (scenarios of "Via protection defaults across rebuilds"). Proof: `uv run pytest tests/unit/backends/kicad/test_via_protection_merge.py tests/unit/lens/test_build_via_protection.py tests/unit/lens tests/unit/cli/test_explain_cmd.py`.
  - Done: 2026-10-07. The idempotence sentence of the requirement was corrected (design, item 6).

## 7. Inspect

- [x] 7.1 Add `summary(design)` and `result.via_protection` to `cli/cmd_inspect.py` for KiCad boards (scenarios "Authored board" and "Board with protected vias"). Proof: `uv run pytest tests/unit/cli/test_inspect_cmd.py tests/unit/cli/test_hermetic_examples.py tests/consistency`.
  - Done: 2026-10-07.

## 8. Altium

- [x] 8.1 Write the tenting flags: `via_record(…, tented_top=False, tented_bottom=False)` in `backends/altium/pcbrecords.py`, the resolution of each via's two sides (own value, else the board default, else clear) in the Altium lowering, and the call in `pcbdoc.write_pcbdoc` (scenarios "Flags of the four cases" and "Written flags read back"). Add the fact row of the written flags to `docs/formats/altium/pcb-copper.md` (sources of the existing row, `INFERRED`, `H-A-PCB-CU-VIATENT`), take "tented vias" out of its not-written list and correct the sentence under "Vias". Proof: `uv run pytest tests/unit/backends/altium/test_pcb_vias.py tests/unit/backends/altium/test_pcbrecords.py tests/unit/backends/altium/test_pcbdoc.py tests/unit/test_format_facts.py`; `uv run pyright src`.
  - Done: 2026-10-07. The board default reaches the writer as `PcbDocSpec.via_protection` (design, item 9).
- [x] 8.2 Give the `altium.not-lowered` info at `via-protection` in `lens/altium.py` and name `H-A-PCB-CU-VIATENT` in the build's evidence when a flag is set, with `tests/unit/lens/test_altium_via_protection.py` (scenarios "Tenting written, the rest named", "A design without protection keeps its bytes" and "A side nobody states"). Add the `where` value `via-protection` to the text of `altium.not-lowered` in `cli/data/explain.toml`. Proof: `uv run pytest tests/unit/lens/test_altium_via_protection.py tests/unit/lens/test_altium_copper_golden.py tests/unit/lens/test_altium_pcb_golden.py tests/unit/lens/test_altium_pcb_complete.py tests/unit/cli/test_explain_cmd.py`; `git status --porcelain tests` lists no golden file.
  - Done: 2026-10-07. The test builds a copy of `examples/blink_routed` (design, item 8); no golden file changed. The texts of `altium.not-lowered` in `explain.toml` were rewritten shorter to stay within the 400 characters the table allows.
- [x] 8.3 Import the flags: `Via.protection` in `backends/altium/adapter/copper.py` (scenarios of "Via tenting of imported vias"), `result.via_protection` of `inspect` for an Altium PCB document (scenario "Altium PCB document"), and `Via.protection` in the list of fields that RT-A2 leaves out in `docs/altium.md`. Run the import, diff, equivalence and round-trip tests and write under this task which expected values moved because every imported via now holds explicit tenting. Proof: `uv run pytest tests/unit/backends/altium/adapter tests/unit/backends/altium/test_roundtrip.py tests/unit/checks/test_diff.py tests/unit/checks/equivalence tests/unit/cli/test_inspect_cmd.py`; with the corpus cached, `uv run pytest tests/corpus/test_altium_import.py -q`.
  - Done: 2026-10-07. Expected values that moved because every imported via now holds explicit tenting: none in the import, diff, equivalence and round-trip tests (they compare vias by position, size and net); `tests/unit/cli/test_inspect_cmd.py` gained the key `via_protection` for a PCB document; `tests/unit/backends/altium/adapter/test_package.py` allows the one writer row in the import's evidence; the RT-A2 table of `docs/altium.md` lists `protection`. Corpus, non-heavy: `test_altium_import.py` 6 passed, 1 skipped; `test_altium_roundtrip.py`, `test_altium_copper.py`, `test_altium_documents.py`, `test_altium_rta3.py` 112 passed, 9 skipped. The heavy items were not run.
- [x] 8.4 Ask for the author report that settles `H-A-PCB-CU-VIATENT`: add a step to `docs/evidence/altium-pcb.md` (and a sample to the verification kit of c0091, if its folder is archived by then) with a board of four through vias, one per flag value, and the question "which sides does Altium Designer 26 show as tented for each via, and does the document open without a message?". The row stays `INFERRED` until the maintainer's report is recorded; this task is done when the step and the sample are committed, not when the report arrives. Proof: `uv run pytest tests/unit/test_hypotheses_register.py tests/unit/test_provenance.py`; `grep -n "H-A-PCB-CU-VIATENT" docs/evidence/altium-pcb.md docs/hypotheses.md` shows the step and the row.
  - Done: 2026-10-07. Step C8 of `docs/evidence/altium-pcb.md`; the sample is outside the repository, in `~/fenolite-altium-checks/session-2/ViaTenting/` with its `README.md` (files for the maintainer are never committed; c0091's kit folder is not archived). The row stays `INFERRED`, pending the report.

## 9. Written bench

- [x] 9.1 Add the written bench to `_viabench.py` (the same cases set through the model and written by `write_board`), the probe `via-prot-resave` and the tests `-k "written or resave"` (scenarios "The written bench" and "Re-save and outputs on 10.0.6"). Proof: `FENOLITE_PROBES_WRITE=1 uv run pytest tests/kicad/vias/test_via_protection_oracle.py -k "written or resave" -rA` on the local `kicad-cli` 10.0.6, and `-k written` with `FENOLITE_KICAD_CLI="docker:kicad/kicad:9.0.9@sha256:e638b79b0321f29395a5b783e94bb9f3c73303e8da15da27b8f5cb4b67a37729"` or in the `kicad-9` job.
  - Done: 2026-10-07: `via-prot-resave` `equal` on 10.0.6; the written bench loads and plots as the model means under four defaults on 10.0.6 (10 passed, 2 skipped) and on 9.0.9 in the pinned image (8 passed, 4 skipped).
  - 2026-10-08: the probe `via-prot-order` joined (a protection child added to a read via that holds `locked` and `free` is written after them, and a re-save keeps the order): `equal` on 10.0.6, with `tests/unit/backends/kicad/test_via_protection_write.py -k lands_after_free`.

## 10. Documentation

- [x] 10.1 Write the section "Via protection" of `docs/formats/kicad/board.md` (forms per major with their meaning, KiCad 10's reading of 9.0 children, what the outputs carry, each fact with its source and label; `tenting` leaves the opaque list of vias), and update `docs/dsl.md` (`protect`, `protection=`, `Design.via_protection`, the rebuild rule, target 9, the gap of `kicad.via.protection-not-exported`), `docs/copper.md`, `docs/lens.md`, `docs/cli-contract.md` (`inspect` for both backends, the four codes, the `where` value `via-protection`) and `docs/altium.md` (what the Altium documents hold of via protection, the side nobody states, the clear flag read as not tented). Proof: `uv run pytest tests/consistency tests/unit/test_format_facts.py tests/unit/test_repo_layout.py tests/residue`.
  - Done: 2026-10-07.
- [ ] 10.2 If c0080 is on `dev`, add one tested line to its `fabrication` page: a `fenolite-design` block that fills and caps the vias of a stitch with `protect(filling=True, capping=True)`; its coverage test asks for `protect`, a new name of `fenolite.dsl.__all__`. Otherwise write "c0080 not on dev" under this task. Proof: `uv run pytest tests/unit/agent/test_pages.py`, or the note.
  - Open (2026-10-07): c0080 is not on the branch (a proposal only: there is no `fabrication` page and no `tests/unit/agent/test_pages.py`).
  - 2026-10-08, on `v04-close-c` (`d6e6a19`): c0080 is on `v04`, but the line cannot be tested under its contract yet. A `fenolite-design` block is built for targets 9 and 10 (`tests/unit/agent/test_pages.py::test_design_blocks_build`, scenario "Every design builds"), and target 9 refuses `protect(filling=True, capping=True)` with exit 7 and `kicad.board.via-protection-too-new` (checked on a scratch script of a stitch: target 9 exit 7, target 10 exit 0, Altium exit 0). `protect` is already taught and tested on the `routing` page (`protection=protect(tenting=True)`), so the coverage test holds. Open until the guide accepts a block built for target 10 only (an argument of `fenolite-design` beside `altium`, a change of c0080's "Executable blocks"), or until the maintainer accepts the `routing` line as this task's line.
  - 2026-10-08, coordinator: deferred to the next release. The line needs either a guide block built for target 10 only (a change to c0080's rule that every block builds for both targets) or the acceptance of the `protect(tenting=True)` line of the `routing` page; neither is decided for 0.4.

## 11. Closing

- [x] 11.1 Run the residue and the fast suite. Proof: `uv run pytest tests/residue tests/corpus/test_manifest.py` (after `git add -A`) and `uv run python tools/residue/scan.py` exit 0; `uv run python tools/gen_schemas.py --check` exits 0; `make check-fast` passes; `openspec validate c0112-via-protection --strict --no-interactive` and `openspec validate --all --strict --no-interactive` pass. The full `make check` and `gh pr checks` (`unit`, `kicad-9`, `kicad-10`) are the coordinator's, once, on the rebased branch at merge; this change's agent does not start a full suite.
  - Done: 2026-10-07. `make check-fast PYTEST_WORKERS=3`, run once: 9891 passed, 18 skipped, 4 failed (`tests/unit/test_altium_rows.py::test_the_change_registered_its_rows`, which pins the set of `H-A-PCB-CU-*` rows, and three tests of `tests/unit/test_kicad_probes.py`, whose fake module lists the helper folders of `tests/kicad`); both test files were corrected (the new row; the folder `vias`) and re-run alone: 34 passed. The suite was not run a second time. Residue, manifest, schemas, matrix and `openspec validate --all --strict` pass.
  - 2026-10-08, after the rebase onto `be2c01ec`: `make check-fast PYTEST_WORKERS=3` on the rebased commit, run once: 10434 passed, 22 skipped, exit 0 (this line was added afterwards, and nothing else). Residue, manifest, schemas, matrix and `openspec validate --all --strict` pass; the oracle files of the change on `kicad-cli` 10.0.6: 12 passed, 2 skipped, with the new probe `via-prot-order` `equal`. The 9.0.9 image was not run again: the two outcomes of `9.0.9.json` are those recorded on 2026-10-07, and the probes of the day are recorded for 9.0.9 by the coordinator.
- [x] 11.2 Run the unit suite on Python 3.11 before handing over. Proof: `uv run --isolated --python 3.11 --extra dev pytest tests/unit -q -n 4 -p no:cacheprovider` exits 0.
  - Open (2026-10-07): no Python 3.11 whole-suite run tonight (rule of the night); the coordinator runs it once per wave.
  - 2026-10-08, on `v04-close-c` from `origin/v04` at `d6e6a19`, with the edits of this closing round staged: `make check-fast PYTEST_WORKERS=3` exits 0 (ruff, format, pyright, residue scan; 12888 passed, 29 skipped; a first run failed only on `tests/unit/test_evidence_matrix_page.py` before `docs/evidence/matrix.md` was regenerated); `uv run --isolated --python 3.11 --extra dev pytest tests/unit -q -n 3 -p no:cacheprovider` exits 0 (12497 passed, 25 skipped); `uv run pytest tests/residue tests/corpus/test_manifest.py` (82 passed, 3 skipped) and `uv run python tools/residue/scan.py` (0 hits) exit 0; `uv run python tools/gen_schemas.py --check` exits 0; `openspec validate --all --strict --no-interactive` gives only the errors that were there before (c0084, c0085 twice, c0086, c0108, c0128) and long-requirement warnings; `python3 tools/dco_check.py origin/v04..HEAD` prints nothing. Three workers in place of four, as parallel agents share the machine.
- [x] 11.3 Update the evidence: `H-K-VIAPROT-FORMS`, `-UPGRADE` and `-OUTPUTS` become `KICAD-VERIFIED (10.0.x)`, `-MASK` `KICAD-VERIFIED (9.0.x, 10.0.x)` and `-NINE` `KICAD-VERIFIED (9.0.x)` with its written form still `INFERRED`, each with its run, or the row records what was refuted and the fallback taken; `via_protection.EVIDENCE` follows. `H-A-PCB-CU-VIATENT` stays `INFERRED` with `pending (author report)` unless the report of task 8.4 is recorded; no Altium level moves without it. Proof: `uv run pytest tests/unit/test_provenance.py tests/unit/test_hypotheses_register.py tests/kicad/test_probe_results.py`.
  - Done: 2026-10-07. The five `H-K-` rows are verified with their runs; `-NINE` says that the spelling KiCad 9 writes for neither side stays `INFERRED`; `via_protection.EVIDENCE` is `KICAD_VERIFIED`. `H-A-PCB-CU-VIATENT` stays `INFERRED`, `pending (author report)`.
- [x] 11.4 Add to `CHANGELOG.md` under Unreleased: "Via protection: `protect()` and `protection=` on `Design.via`, `via_step` and `Design.stitch`, and `Design.via_protection()` for the board default. KiCad boards read and write tenting, covering, plugging, capping and filling per via and in `setup`; target 9 holds tenting only and refuses the others (exit 7). `inspect` reports `via_protection`. A KiCad 9 board with via tenting, rebuilt for target 10, now keeps the mask that 9.0.9 plots, and a protection set in KiCad on a script via is reported when the build replaces it. Altium: the build writes a via's tenting where the design states it, the import reads the tenting flags into the model (every imported via gains explicit tenting), and the four other features are named and not written. 0.2.x and 0.3.0 cannot read a `board.json` that carries `protection` or `via_protection`." Update the row of c0112 in `docs/roadmap.md` (the table of "v0.4: proposals on other branches", or the milestone table if the section was folded into it by then). Proof: `git diff --stat CHANGELOG.md docs/roadmap.md` lists both files; `grep -n "c0112" docs/roadmap.md` shows the row.
  - Open (2026-10-07): the changelog line is written, at the end of `[Unreleased]`; the row of `docs/roadmap.md` is the coordinator's tonight (the file is not edited by a lane).
  - The CHANGELOG entry of this change, written before this round, stands in `## [Unreleased]`; the row of this change in `docs/roadmap.md` (v0.4, the complex board) says what ships in 0.4. `git diff --stat CHANGELOG.md docs/roadmap.md` lists both files. `grep -n c0112 docs/roadmap.md` shows the row.
