lgili/Fenolite/openspec/changes/c0113-placement-constraints/tasks.md

## 0. Entry check

- [x] 0.1 Read the living `placement`, `cli-contract`, `design-dsl`, `design-model`, `verification-loop` and `kicad-oracle` specs and `openspec list`. Write under this task, with the date:
  - whether `0.3.0` is released and c0088 and c0090 are archived ("Placement rules stage" names their "Document check pipeline"; this change waits for it);
  - whether c0096 is on `dev`. If it is, regenerate the MODIFIED "Place command" from the living text and apply this change's edits again by the list of `design.md`, "Relation to c0096", and task 4.2 applies; if it is not, write that task 4.2 is void and that c0096 regenerates later;
  - whether "Placement legality" or "Placement legality in a build" changed since `origin/dev` `9aba2dff` (then regenerate that delta from the living text and state in `design.md` which landed first);
  - whether c0103 is on `dev`. If it is, replace the ADDED "Placement keep-outs in the DSL" by a MODIFIED "Rule areas in the DSL" regenerated from the living text (the `forbid` list, the `no_footprints` clause and the refused call of its scenario change; the Altium bullet and the two scenarios of this change are kept); if it is not, task 3.3 waits and the rest goes on;
  - whether c0106 inserted `length.rules` (then `placement.rules` follows it); whether c0104, c0105 or c0114 changed `RuleSet` (then task 2.2 regenerates on their fields);
  - where the Altium build counts what it does not write (`backends/altium/lower.py` at `9aba2dff`), for the two kinds of task 8.4;
  - whether c0123 is on `dev` (Open Questions: a `PinHandle` in `near`); whether c0080 is on `dev` (task 9.2); whether S-0680 is still free.

  Proof: `openspec validate c0113-placement-constraints --strict --no-interactive` passes after any regeneration; `grep -cE '^\| S-0680 ' docs/evidence/sources.md` prints `0` before task 1.1.
  - 2026-10-07, at `origin/dev` `9aba2dff` (proposal repaired, nothing built): the three living requirements this change modifies are unchanged since the proposal's base `7203e4b6`, and no open change on `dev` holds a delta of them; c0088 and c0090 are open on `dev`; `0.3.0` is not released; c0096, c0103, c0106 and c0123 are not on `dev`; the sources end at S-0601; heights were taken out into c0140.
  - 2026-10-08, on `v04` `369ab2c7` (the integration branch of v0.4; the implementation was carried onto it): `0.3.0` is not released; c0088 and c0090 are implemented and their requirement "Document check pipeline" is living (`openspec/specs/verification-loop/spec.md`), the two folders are not archived yet; the stage joins `DOCUMENT_STAGES` as planned.
  - c0096 is not on the branch (`src/fenolite/cli/placement_checks.py` does not exist): task 4.2 is void and c0096 regenerates its "Place command" from the text this change leaves.
  - "Place command", "Placement legality" and "Placement legality in a build" are unchanged in the living specs since `9aba2dff` (compared block by block), and no open change holds a delta of them: the three MODIFIED deltas are the living texts with this change's edits, nothing regenerated.
  - c0103 came onto the branch during the carry (`19ab2ad1`; c0104 and c0102 after it): the ADDED "Placement keep-outs in the DSL" was replaced by a MODIFIED "Rule areas in the DSL", regenerated from c0103's delta (the requirement is on the branch and not living until c0103 is archived, which must come first) with the three edits (the `forbid` list, the `no_footprints` clause, the refused call of its scenario, now `forbid=("silkscreen",)`), the Altium bullet and the two scenarios; task 3.3 applies.
  - c0106 is not on the branch: no `length.rules`, so `placement.rules` follows `copper.clearance`. c0114 and c0104 are on it (`RuleSet.severities`; five rule kinds and the `diff_pair` leaf): `proximity` stands after it and `rules.json` of the schemas was regenerated on both.
  - The Altium build counts what it does not write in `backends/altium/lower.py` (`from_design`) and, for the board items of a build, in `lens/altium_copper.py` (`lower_items`); the two kinds are given there.
  - c0123 is on the branch (a pin may be bonded to several pads); c0080 is on it (task 9.2 applies); S-0680 was free (`git show v04:docs/evidence/sources.md | grep -cE '^\| S-0680 '` prints `0`).
  - Proof: `openspec validate c0113-placement-constraints --strict --no-interactive` and `openspec validate --all --strict --no-interactive` pass (103 items).

## 1. Probe and register

- [x] 1.1 Add the row `H-K-PLACE-KEEPOUT` to `docs/hypotheses.md` (backend `kicad`, level `INFERRED`, the test and criterion of `design.md`, result `pending` with measurement 1 of 2026-10-05 as the first record) and the source S-0680 to `docs/evidence/sources.md` with the URL, licence and "used for" of `design.md`. Proof: `uv run pytest tests/unit/test_hypotheses_register.py tests/unit/test_provenance.py`; `grep -cE '^\| S-0680 ' docs/evidence/sources.md` prints `1`.
  - 2026-10-08: 44 passed; the grep prints `1`. The row and the source stand at the end of their tables.
- [x] 1.2 Port the 18 cases of measurement 1 to `tests/kicad/place/_keepoutcases.py` (benches on `_rulebench.py`, the scoped canary, courtyards removed by token edit for the `nocrt-*` cases, a four-layer board for `inner-only`) and write `tests/kicad/place/test_place_keepout.py` with the probes `place-keepout-<case>`, registered in `tests/kicad/_probes.py` for majors 9 and 10 (scenario "Keep-outs on both majors" without the agreement probe, which task 4.1 adds). If a case records an outcome other than the expected one, stop and write it into the register row. Proof: `uv run pytest tests/kicad/place/test_place_keepout.py -rA` on the local KiCad 10.0.6 and inside the pinned 9.0.9 image; `FENOLITE_PROBES_WRITE=1` updates both probe files; `uv run pytest tests/kicad/test_probe_results.py`.
  - 2026-10-08: on the local `kicad-cli` 10.0.6, `tests/kicad/place/test_place_keepout.py`: 22 passed, none skipped (18 cases, the agreement probe, 3 hermetic tests); `10.0.6.json` written by `FENOLITE_PROBES_WRITE=1 uv run pytest tests/kicad/test_probe_results.py` (19 rows added, no other outcome moved; the file now starts with `version`, as the tool writes it and as `9.0.9.json` does). Open: the run inside the pinned 9.0.9 image and `9.0.9.json` are owed to the coordinator's image run.
  - 2026-10-08: ticked by the second local run of 2026-10-08 in the pinned 9.0.9 image (`kicad/kicad:9.0.9@sha256:e638b79b…`, linux/amd64, branch `v04-k9-probes-2`; whole `tests/kicad` without the corpus: 998 passed, 2 failed, 806 skipped, 1 xfailed; `tests/kicad/test_probe_results.py` passed on the 723 probes of major 9): `tests/kicad/place/test_place_keepout.py` 22 passed; the nineteen rows are in `9.0.9.json`, merged by name, with the outcomes of 10.0.6 (`place-keepout-agree` `equal`).
- [x] 1.3 Write the keep-out facts of `H-K-PLACE-KEEPOUT` (courtyard interiors, faces by copper layer, touching, inner layers, parts without a courtyard, text) into `docs/formats/kicad/board.md` with S-0020, S-0029 and their label. Proof: `uv run pytest tests/unit/test_format_facts.py`.
  - 2026-10-08: 22 passed.

## 2. Model

- [x] 2.1 Add `PlacementSeverity`, `PadSelection`, `ProximityRule` and `RuleSet.proximity` to `src/fenolite/model/rules.py`, with their checks; extend `tests/unit/model/test_rules.py` and `test_canonical.py` (scenarios "Rules round trip" and "Refused values"). Describe the field in `docs/design-model.md`: omitted when empty, so every output of 0.2.0 keeps its bytes; **0.2.x and 0.3.0 cannot read a `rules.json` that carries `proximity`** (scenario "Compatibility is documented"). Proof: `uv run pytest tests/unit/model`; `uv run pyright src`; `grep -c "proximity" docs/design-model.md` prints at least `1`.
  - 2026-10-08: `tests/unit/model` 255 passed, 3 skipped (files of c0126); `pyright src` 0 errors; the grep prints `3`.
- [x] 2.2 Regenerate `schemas/fenolite.model.v0/rules.json`, and load a file of an older build and write it again (scenario "Files of an older build"). Proof: `uv run python tools/gen_schemas.py --check`; `uv run pytest tests/unit/model -k older`.
  - 2026-10-08: `rules.json` regenerated on the tip with `tools/gen_schemas.py` (the field stands beside c0114's `severities`); `--check` exits 0; `-k older` 3 passed.

## 3. DSL

- [x] 3.1 Add `Design.near` with the refusals at the call, in `src/fenolite/dsl/design.py`, and write `tests/unit/dsl/test_placement_rules.py` (scenario "Refused calls"). Write under this task whether c0123 is on `dev`; the `PinHandle` refusal stays either way. Proof: `uv run pytest tests/unit/dsl/test_placement_rules.py tests/unit/test_import_graph.py`; `uv run pyright src`.
  - 2026-10-08: 51 passed; `pyright src` 0 errors. c0123 is on the branch; the `PinHandle` refusal stays, with its hint.
- [x] 3.2 Write the rules in `to_model` (`dsl/convert.py`): selections, module expansion in path order, `DslError` for a part or module outside the design (scenarios "Decoupling rule recorded", "Module expanded", "Unchanged designs"). Proof: `uv run pytest tests/unit/dsl`.
  - 2026-10-08: `tests/unit/dsl` 666 passed.
- [x] 3.3 With c0103 on `dev`: add `footprints` to `FORBID` in `dsl/items.py`, mapped to `Keepout.no_footprints` (scenario "Antenna keep-out", which needs task 8.2 for its last clause). Proof: `uv run pytest tests/unit/dsl/test_placement_rules.py -k keepout`.
  - 2026-10-08: c0103 is on the branch: `footprints` is in `dsl.items.FORBID` and `to_model` sets `Keepout.no_footprints`; c0103's refused-call test now refuses `forbid=("silkscreen",)`. `-k keepout` 2 passed (targets 9 and 10: the model, `(footprints not_allowed)` once in the board text, one `place.keepout` warning of the build's guard naming `R1` and `ANT`; an area on `B.Cu` judges no top-side part).

## 4. Keep-outs in the legality check

- [x] 4.1 Add `keepouts=()`, `place.keepout`, `place.keepout-no-courtyard` and `KEEPOUT_EVIDENCE` to `src/fenolite/placement/legality.py` and `codes.py`, and the tables of the two codes to `src/fenolite/cli/data/explain.toml` (`meaning` and `fix` of at most 400 characters, `see = "place"`); extend `tests/unit/placement/test_legality.py` (scenarios "Keep-out by face", "Touching keep-out", "Part without a courtyard") and `test_place_codes.py`; add the probe `place-keepout-agree` and the hermetic test to `test_place_keepout.py`. Proof: `uv run pytest tests/unit/placement tests/unit/cli/test_explain_cmd.py`; `uv run pytest tests/kicad/place/test_place_keepout.py -k hermetic`; `uv run pytest tests/kicad/place/test_place_keepout.py -k agree -rA` on the local KiCad 10.0.6.
  - 2026-10-08: `tests/unit/placement tests/unit/cli/test_explain_cmd.py` 41 passed; `-k hermetic` 3 passed; `-k agree` 1 passed on the local KiCad 10.0.6 (`place-keepout-agree` = `equal`).
- [x] 4.2 Only when c0096 is on `dev` (task 0.1): in `src/fenolite/cli/placement_checks.py`, take the verdict "a part in a rule area that forbids footprints" of the constrained strategy from `placement.legality.check(…, keepouts=…)`, report it as `place.keepout` at the reference, and remove that case from what gives `place.constraint`; update the table of `place.constraint` in `explain.toml`; add the scenario of "Relation to c0096" (a constrained request that would put a part into a keep-out reports `place.keepout` at the part, and a courtyard that only touches the area is accepted). Proof: `uv run pytest tests/unit/placement tests/unit/cli/test_place_cmd.py -k "constrained or keepout"`; `uv run pytest tests/unit/cli/test_explain_cmd.py`. When c0096 is not on `dev`: `git log --oneline -1 -- src/fenolite/cli/placement_checks.py` prints nothing, and this task is closed with that line under it.
  - 2026-10-08: void, c0096 is not on the branch: `git log --oneline -1 v04 -- src/fenolite/cli/placement_checks.py` prints nothing.

## 5. Rules judged

- [x] 5.1 Write `src/fenolite/checks/placement.py` with `board_box`, `PlacementRules`, `rules_of`, `RuleReport` and `judge`, the three `placement.*` codes in `checks/codes.py` and their tables in `src/fenolite/cli/data/explain.toml` (`see = "check"`); write `tests/unit/checks/test_placement_rules.py` (scenarios "Decoupling rule met and missed", "Distance equal to the limit", "A distance just above the limit is printed above it", "Unresolved and skipped rules", "A board read from an Altium document"). Proof: `uv run pytest tests/unit/checks/test_placement_rules.py tests/unit/checks/test_codes.py tests/unit/cli/test_explain_cmd.py tests/unit/test_import_graph.py`; `uv run pyright src`.
  - 2026-10-08: 59 passed; `pyright src` 0 errors.

## 6. Measures

- [x] 6.1 Add `Measures` and `measure` with `hpwl`, `ratsnest`, `longest` and `left_out`; write `tests/unit/checks/test_placement_measures.py` (scenario "Lengths computed by hand", a tie between two spanning trees of equal length, a property test that `ratsnest` never exceeds the sum of a chain through the pads in path order). Proof: `uv run pytest tests/unit/checks/test_placement_measures.py`.
  - 2026-10-08: 14 passed.
- [x] 6.2 Add the congestion grid (scenarios "Congestion of two cells" and "No pitch", a board whose longer side exceeds 256 mm, and a net whose box is a point). Proof: `uv run pytest tests/unit/checks/test_placement_measures.py -k congestion`.
  - 2026-10-08: 6 passed, 8 deselected.
- [x] 6.3 Measure the cost of `judge` and `measure` on a synthetic layout of 600 parts and 1 650 pads written by the test, round numbers chosen for Fenolite (or on the board of c0119 once it exists), and write the times and the machine into `docs/placement.md`. No time is asserted: c0119 owns the budgets. Proof: `uv run pytest tests/unit/checks/test_placement_measures.py -k synthetic_600 -rA` prints the times.
  - 2026-10-08: 1 passed; it printed `judge 51 ms, measure 294 ms` (600 parts, 1650 pads, 150 rules, 338 measured nets) on a machine shared with other test runs; `docs/placement.md` holds the times of the implementer's run.

## 7. The stage `placement.rules`

- [x] 7.1 Add `placement_stage`, `placement.rules` in `STAGE_ORDER` (after `copper.clearance`, after `length.rules` when present, before `zone.fill`), the skip reason `no-frame`, the pitch from `DesignRulesSource`, the summary and the evidence rule, in `src/fenolite/checks/stages.py` and `placement.py`; write `tests/unit/checks/test_placement_stage.py` (scenarios "A rule fails without kicad-cli", "Native board measured", "Skips") and extend `tests/unit/cli/test_check_cmd.py -k default_stages` and `test_check_readonly.py`. Proof: `uv run pytest tests/unit/checks tests/unit/cli/test_check_cmd.py tests/unit/cli/test_check_readonly.py`.
  - 2026-10-08: 653 passed.
- [x] 7.2 Add `placement.rules` to `DOCUMENT_STAGES` in `src/fenolite/checks/documents.py`, after `copper.clearance` and before `parity`, with the skip `single-source`, the pads and the pitch from the document validator (scenarios "The same rule on a built Altium project" and "Altium documents without a script"). Proof: `uv run pytest tests/unit/checks/test_documents.py tests/unit/checks/test_placement_stage.py -k "document or altium"`; `uv run pytest tests/unit/cli/test_check_altium.py -k placement_rules`.
  - 2026-10-08: 21 passed, 9 deselected; `test_check_altium.py -k placement_rules` 2 passed.

## 8. `place` and `build`

- [x] 8.1 In `src/fenolite/cli/cmd_place.py`: load `.fenolite/` once, give the grid the boxes of keep-outs that forbid footprints, pass the keep-outs to the legality check, judge the rules as warnings, report `result.rules` and `result.measures` with `change`, and combine the evidence; extend `tests/unit/cli/test_place_cmd.py` (scenarios "Nothing to place", "Keep-out avoided by the grid and refused for a move", "Rules and measures of a move"). Proof: `uv run pytest tests/unit/cli/test_place_cmd.py tests/unit/cli/test_hermetic_examples.py tests/consistency`.
  - 2026-10-08: 352 passed, 19 skipped (consistency tests that need `kicad-cli` or the corpus).
- [x] 8.2 In `cmd_build.placement_guard`: keep-outs to the legality check, `judge` with the built model's rules, `result.placement.rules`, every finding at most a warning (scenarios "Rules reported as warnings" and "Clean blink stays clean"). Proof: `uv run pytest tests/unit/cli/test_build_placement_guard.py tests/unit/lens tests/consistency`.
  - 2026-10-08: 1416 passed, 20 skipped. `tests/kicad/place/test_place_oracle.py::test_placed_then_rebuilt` compared `result.placement` with the reply before this change and now expects `rules` too.
- [x] 8.3 Check that no byte moved for a design without the new calls: the blink and the routed blink built for targets 9 and 10 and for the Altium target with a fixed seed and timestamp give, file by file and `.fenolite/` included, the SHA-256 recorded from the commit before task 2.1. Proof: `uv run pytest tests/unit/lens -k unused_keys` (the test file of that name when c0114 has added it, else `tests/unit/lens/test_unused_keys.py` is written here).
  - 2026-10-08: 13 passed. c0114 had added `tests/unit/lens/test_unused_keys.py` with the recorded SHA-256 of every file of the two blink builds for targets 9 and 10 (recorded before its own fields); it passes unchanged with `RuleSet.proximity`, `.fenolite/` included, so no byte moved. This change's tests are in `tests/unit/lens/test_unused_keys_proximity.py` beside it. `tests/unit/lens/test_build_bytes_pinned.py` passes with no pin moved. The Altium target has no recorded digest: `test_no_placement_rule_gives_no_info_and_the_same_bytes` proves that its `rules.json` holds no `proximity`.
- [x] 8.4 The Altium build: the kinds `placement-rule` and `keepout-footprints` of `altium.not-lowered` in `backends/altium/lower.py`, neither in `LOSS_KINDS`; check that `rulemap.TABLE` still has one row per `RuleKind` and none for a proximity rule (scenarios "Rules of an Altium build are stored and announced" and "Antenna keep-out in an Altium build", the second with c0103 on `dev`). Proof: `uv run pytest tests/unit/backends/altium tests/unit/cli/test_build_altium.py -k "placement_rule or keepout_footprints or rulemap or table"`.
  - 2026-10-08: 119 passed; `test_build_altium.py -k keepout_footprints` 1 passed ("Antenna keep-out in an Altium build": exit 0, one info naming `ANT`).

## 9. Documentation

- [x] 9.1 Update `docs/placement.md` (keep-outs and the measured rule under the one code `place.keepout`, `near` rules and the rounding of a printed distance, the measures and how to read them, what is not judged, that heights are c0140's), `docs/dsl.md` (`near`, `footprints` in `forbid`, and one sentence on the word "anchor": the reference side of `near` here, a point in a part's frame in c0111, the reason of a locked placement in c0096, each named only if it is on `dev`), `docs/cli-contract.md` (the stage `placement.rules` on KiCad and on Altium input, `result.rules` and `result.measures` of `place`, `result.placement.rules` of `build`, the five new codes) and `docs/altium.md` (the stage on documents, the two `altium.not-lowered` kinds, no keep-out judged on Altium input). Proof: `uv run pytest tests/consistency tests/unit/test_repo_layout.py tests/residue`.
  - 2026-10-08: 344 passed, 19 skipped. `docs/dsl.md` and `docs/placement.md` teach `forbid=("footprints",)`.
- [x] 9.2 If c0080 is on `dev`, add one tested line each for `near`, `forbid=("footprints",)` and `check --stages placement.rules` to its guide pages; otherwise write under this task that the lines are owed to c0080. Proof: `uv run pytest tests/unit/agent -q` when c0080 is on `dev`; else `git log --oneline -1 -- openspec/changes/c0080-agent-authoring-guide` prints nothing.
  - 2026-10-08: c0080 is on the branch. Page `placement`: `design.near(…)` and `design.rule_area("ANT", …, forbid=("footprints",))` in the tested design block, each with its bullet, and `result.rules`, `result.measures` and `place.keepout` under "On the board"; page `checks`: `fenolite check blink/build --stages placement.rules --json` and the stage's table row; `references/commands.md` regenerated (`tools/gen_agent_guide.py --check` exits 0). `uv run pytest tests/unit/agent -q`: 85 passed; the coverage test names nothing of this change.

## 10. Closing

- [x] 10.1 Stop and report "ready for the long runs"; an agent in a worktree does not run the full `make check`. Proof: `make check-fast PYTEST_WORKERS=4` exits 0; `uv run --isolated --python 3.11 --extra dev pytest tests/unit -q -n 4 -p no:cacheprovider` exits 0; after `git add -A`, `uv run pytest tests/residue tests/corpus/test_manifest.py` and `uv run python tools/residue/scan.py` exit 0 (this change adds no file under `tests/data/`; the manifest test proves it); `openspec validate c0113-placement-constraints --strict --no-interactive` and `openspec validate --all --strict --no-interactive` pass; `python3 tools/dco_check.py <base>..HEAD` prints nothing. The full `make check` and the jobs `unit`, `kicad-9` and `kicad-10` are the coordinator's, once, on the rebased branch at the merge.
  - 2026-10-08, on `v04` `369ab2c7`: `make check-fast PYTEST_MAX_WORKERS=3` exits 0 (11841 passed, 26 skipped); the touched unit files, `tests/unit/agent` and the pinned builds pass on Python 3.11; `tests/residue`, `tests/corpus/test_manifest.py` and `tools/residue/scan.py` pass on the staged tree; both `openspec validate` runs pass; on the local `kicad-cli` 10.0.6, `tests/kicad/place` gives 28 passed. Open: the whole unit suite on Python 3.11, the full `make check` and the jobs `unit`, `kicad-9` and `kicad-10` are the coordinator's, once, at the merge.
  - 2026-10-08, on `v04-close-c` from `origin/v04` at `d6e6a19`, with the edits of this closing round staged: `make check-fast PYTEST_WORKERS=3` exits 0 (ruff, format, pyright, residue scan; 12888 passed, 29 skipped; a first run failed only on `tests/unit/test_evidence_matrix_page.py` before `docs/evidence/matrix.md` was regenerated); `uv run --isolated --python 3.11 --extra dev pytest tests/unit -q -n 3 -p no:cacheprovider` exits 0 (12497 passed, 25 skipped); `uv run pytest tests/residue tests/corpus/test_manifest.py` (82 passed, 3 skipped) and `uv run python tools/residue/scan.py` (0 hits) exit 0; `uv run python tools/gen_schemas.py --check` exits 0; `openspec validate --all --strict --no-interactive` gives only the errors that were there before (c0084, c0085 twice, c0086, c0108, c0128) and long-requirement warnings; `python3 tools/dco_check.py origin/v04..HEAD` prints nothing. Three workers in place of four, as parallel agents share the machine. The jobs `unit`, `kicad-9` and `kicad-10` were last all green in CI run 37772583226 on `04ef42a`; this round's commits are read by the coordinator after the merge.
- [x] 10.2 Update the evidence: `H-K-PLACE-KEEPOUT` becomes `KICAD-VERIFIED (9.0.x, 10.0.x)` with the runs, or records the case that differed and the predicate that followed it; `placement.legality.KEEPOUT_EVIDENCE` follows the row. Proof: `uv run pytest tests/unit/test_provenance.py tests/unit/test_hypotheses_register.py tests/kicad/test_probe_results.py`.
  - 2026-10-08: open: the row is `INFERRED` with the 10.0.6 record; the 9.0.9 image run is owed to the coordinator's image run, and `KEEPOUT_EVIDENCE` follows the row then.
  - 2026-10-08: the image run named under task 1.2 met the criterion of `H-K-PLACE-KEEPOUT` on 9.0.9. The row is left at `INFERRED`, with that run in its result, by the commit that recorded the probes: `test_legality_keepout_evidence_follows_the_register` ties `KEEPOUT_EVIDENCE` to the row's level, and the constant is this change's to raise. Owed: the row to `KICAD-VERIFIED (9.0.x, 10.0.x)` and `KEEPOUT_EVIDENCE` to `KICAD_VERIFIED`, together.
  - 2026-10-08, on `v04-close-c` from `origin/v04` at `d6e6a19`: ticked. `tests/kicad/place/test_place_keepout.py` is unchanged since `04ef42a`, and its 22 tests passed in the all-green CI run 37772583226 on that commit, in the `kicad-9` job (each `PASSED` in its `-rA` log, `place-keepout-agree` among them) and in the `kicad-10` job (none skipped); neither job deselects a marker. `H-K-PLACE-KEEPOUT` is `KICAD-VERIFIED (9.0.x, 10.0.x)` with that run in its result, `placement.legality.KEEPOUT_EVIDENCE` is `KICAD_VERIFIED` (`test_legality_keepout_evidence_follows_the_register` ties the two), the eight fact rows of `docs/formats/kicad/board.md` "Rule areas that forbid footprints" carry the same label, and `docs/placement.md` no longer counts a keep-out among the cases that lower the level of `place`. `uv run pytest tests/unit/test_provenance.py tests/unit/test_hypotheses_register.py tests/kicad/test_probe_results.py` with `tests/unit/placement` and `tests/unit/cli`: 1465 passed, 4 skipped, exit 0.
- [x] 10.3 Add to `CHANGELOG.md` under Unreleased: "Placement rules: `design.near()` for decoupling, crystal and gate-driver proximity, and `footprints` in `rule_area(forbid=…)`. `fenolite check` gains the default stage `placement.rules` (rules of a built project, wire length and congestion of every board), on KiCad projects and on Altium documents; `place` reports the same numbers and refuses a part in a keep-out that forbids footprints, as KiCad's DRC does (`place.keepout`); `build` reports rule findings as warnings. A `rules.json` with `proximity` cannot be read by 0.2.x or 0.3.0." Update the row c0113 of `docs/roadmap.md` (section of v0.4), and the inputs it leaves for the placer of v0.5a. Proof: `git diff --stat CHANGELOG.md docs/roadmap.md` lists both files.
  - 2026-10-08: the entry stands at the end of `## [Unreleased]` of `CHANGELOG.md`. Open: `docs/roadmap.md` is edited by the coordinator.
  - The CHANGELOG line of this round is under `### Changed` of `## [Unreleased]`, and the row of this change in `docs/roadmap.md` (v0.4, the complex board) says what ships in 0.4. `git diff --stat CHANGELOG.md docs/roadmap.md` lists both files. The row names the inputs the placer of v0.5a gets: the `near` rules, the keep-outs that forbid footprints and the measures of `placement.rules`.
