lgili/Fenolite/openspec/changes/c0114-net-ties-waivers/tasks.md

## 0. Entry check

- [x] 0.1 Read the living `copper-check`, `verification-loop`, `design-dsl`, `dsl-footprint-authoring`, `design-model`, `kicad-file-backend`, `backend-protocol`, `altium-build` and `kicad-oracle` specs, and `openspec list`. Write under this task, with the date: whether `0.3.0` is released and c0088, c0084 and c0126 are archived ("Waivers in the copper guard" and "Waivers in the check" name c0088's "Copper guard in an Altium build" and "Document check pipeline"; this change waits for them); whether "Supported cases are documented against KiCad's DRC", "Pairs that are judged" or "Copper stage issue codes" changed since `origin/dev` `9aba2dff` (then regenerate that delta from the living text and re-apply this change's edits, design Decision 13); whether `drc_json.RESERVED_SUFFIXES` still holds exactly `rules-not-loaded`, `rules-unchecked` and `parity-unchecked`; where the Altium build counts what it does not write (`backends/altium/lower.py`, Decision 16); whether c0097, c0096 or c0113 are on `dev` (Decision 14; if c0097 is, the skip reads `CopperRef.footprint_id`). Proof: `openspec validate c0114-net-ties-waivers --strict --no-interactive` passes after any regeneration; `grep -c "Zone rows of the table" openspec/changes/c0114-net-ties-waivers/specs/copper-check/spec.md` prints `1`.
  - 2026-10-07, at the wave base `f36e08d9` (`dev` plus the proposals of v0.4): `0.3.0` is not released and c0088, c0084 and c0126 are open, not archived. The code of c0088 and c0084 is on the base (both copper guards, `run_document_checks`, `backends/altium/lower.py`), so the two requirements that name c0088's were implemented; the code of c0126 is not (no `FootprintInstance.graphics`). `openspec/specs/` changed since `9aba2dff` only in `altium-build`, `altium-schematic-writer` and `release-gate`: the three living texts are the ones the deltas copy, nothing was regenerated. `RESERVED_SUFFIXES` is the three names. The Altium build reports what it does not write from `lens/altium.py` (`_not_lowered`), and the write of a model counts per kind in `backends/altium/lower.py`. c0097, c0096 and c0113 are not on the base. `openspec validate c0114-net-ties-waivers --strict --no-interactive`: valid, exit 0; the grep prints `1`.
  - 2026-10-07, at `origin/dev` `9aba2dff` (proposal repaired, nothing built): c0068 and c0062 are archived; "Supported cases are documented against KiCad's DRC" was regenerated from the living text, with c0068's zone clauses and scenario kept; the other two living texts are unchanged since the proposal's base `7203e4b6`; c0088, c0084 and c0126 are open on `dev`; `0.3.0` is not released; c0096, c0097 and c0113 are not on `dev`; `RESERVED_SUFFIXES` is the three names above.

## 1. Probe and register

- [x] 1.1 Add the rows `H-K-NETTIE-DRC`, `H-K-DRC-EXCL` and `H-K-PRO-SEV-KEYS` to `docs/hypotheses.md` (backend `kicad`, level `INFERRED`, the tests and criteria of `design.md`, result `pending` with the measurements of 2026-10-05 as the first record). Proof: `uv run pytest tests/unit/test_hypotheses_register.py tests/unit/test_provenance.py`; `grep -cE '^\| (H-K-NETTIE-DRC|H-K-DRC-EXCL|H-K-PRO-SEV-KEYS) ' docs/hypotheses.md` prints `3`.
  - 2026-10-07: the three rows are at the end of the table, the grep prints `3`. They were written once, with the level task 7.2 reached (`KICAD-VERIFIED (10.0.x)`), and keep the measurements of 2026-10-05 as their first record. `uv run pytest tests/unit/test_hypotheses_register.py tests/unit/test_provenance.py`: every test passes but one. `tests/unit/test_hypotheses_register.py::test_cited_ids_registered` failed on the base `f36e08d9` too, on an Altium body hypothesis id that the design of c0140 cited without a register row. It was not this change's, and the design of c0140 no longer cites it on the base `7392159d`.
- [x] 1.2 Write `tests/kicad/check/_tiebench.py` and `tests/kicad/check/test_net_ties.py` with the ten cases and four copies without groups of "Net-tie facts are probed", the footprints written as footprint text with the token until task 2.4, the control pair, and the probes `nettie-<case>` and `nettie-<case>-plain` registered in `tests/kicad/_probes.py` for majors 9 and 10. If a probe records `different`, stop the net-tie part and write what KiCad showed into the register row. Proof: `uv run pytest tests/kicad/check/test_net_ties.py -rA` on the local KiCad 10.0.6 and inside the pinned 9.0.9 image; `FENOLITE_PROBES_WRITE=1` updates both probe files; `uv run pytest tests/kicad/test_probe_results.py`.
  - 2026-10-07: written, with the footprints authored from the start (`Footprint.net_tie`, task 2.4), the control pair and 14 `nettie-*` probes for majors 9 and 10. On the local 10.0.6: `tests/kicad/check/test_net_ties.py` 17 passed, exit 0, three runs in a row; no probe is `different`. One reading differs from the proposal: without the token, a pad that touches the netless polygon is reported as `shorting_items` or as `clearance` at distance 0 (both in one run), so the bench counts the two as one. `10.0.6.json` gained the outcomes by running these probes and merging them; `tests/kicad/test_probe_results.py`, which runs every probe, was not run. The 9.0.9 half of the proof is owed: no 9.0.9 image was run in this session (no docker); the `kicad-9` job runs it and records `9.0.9.json`.
  - 2026-10-08: ticked by the second local run of 2026-10-08 in the pinned 9.0.9 image (`kicad/kicad:9.0.9@sha256:e638b79b…`, linux/amd64, branch `v04-k9-probes-2`; whole `tests/kicad` without the corpus: 998 passed, 2 failed, 806 skipped, 1 xfailed; `tests/kicad/test_probe_results.py` passed on the 723 probes of major 9): `tests/kicad/check/test_net_ties.py` 17 passed; the fourteen `nettie-*` rows are `equal` in `9.0.9.json`, merged by name.
- [x] 1.3 Write `tests/kicad/check/test_drc_exclusions.py` with the bench and the seven `drc-excl-*` probes of "Exclusion facts are probed", each key built from a first run's report. Proof: `uv run pytest tests/kicad/check/test_drc_exclusions.py -rA` on the local KiCad 10.0.6 and inside the pinned 9.0.9 image; both probe files updated; `uv run pytest tests/kicad/test_probe_results.py`.
  - 2026-10-07: written (`_exclcases.py`, seven `drc-excl-*` probes). On the local 10.0.6: `tests/kicad/check/test_drc_exclusions.py` 10 passed, exit 0; every probe `equal`, recorded in `10.0.6.json`. The 9.0.9 half of the proof is owed: no 9.0.9 image was run in this session (no docker); the `kicad-9` job runs it and records `9.0.9.json`.
  - 2026-10-08: ticked by the second local run of 2026-10-08 in the pinned 9.0.9 image (`kicad/kicad:9.0.9@sha256:e638b79b…`, linux/amd64, branch `v04-k9-probes-2`; whole `tests/kicad` without the corpus: 998 passed, 2 failed, 806 skipped, 1 xfailed; `tests/kicad/test_probe_results.py` passed on the 723 probes of major 9): `tests/kicad/check/test_drc_exclusions.py` 10 passed; the seven `drc-excl-*` rows are `equal` in `9.0.9.json`.
- [x] 1.4 Write `tests/kicad/check/test_severity_keys.py` with `pro-sev-keys-10` and `pro-sev-keys-9-bench` ("Severity keys are probed"); `pro-sev-script` follows in task 5.2. Proof: `uv run pytest tests/kicad/check/test_severity_keys.py -k keys -rA` on the local KiCad 10.0.6 and inside the pinned 9.0.9 image.
  - 2026-10-07: written. On the local 10.0.6: `pro-sev-keys-10` `equal` (62 keys), exit 0; `pro-sev-keys-9-bench` runs on 9.0.9 only and was skipped. The 9.0.9 half of the proof is owed: no 9.0.9 image was run in this session (no docker); the `kicad-9` job runs it and records `9.0.9.json`.
  - 2026-10-08: ticked by the second local run of 2026-10-08 in the pinned 9.0.9 image (`kicad/kicad:9.0.9@sha256:e638b79b…`, linux/amd64, branch `v04-k9-probes-2`; whole `tests/kicad` without the corpus: 998 passed, 2 failed, 806 skipped, 1 xfailed; `tests/kicad/test_probe_results.py` passed on the 723 probes of major 9): `tests/kicad/check/test_severity_keys.py` 3 passed, 1 skipped (`pro-sev-keys-10` skips on 9.0.9); `pro-sev-keys-9-bench` = `absent` in `9.0.9.json`.
- [x] 1.5 Write the facts with their sources and labels: the net-tie verdicts and the exclusion keys, `excluded` and `comment` in `docs/formats/kicad/drc.md`; the token's form, its two spellings and its place after `attr` in `docs/formats/kicad/libraries.md` and `board.md`; the stored exclusion forms, both severity key sets and the six template keys that no 9.0.9.1 demo project holds in `docs/formats/kicad/project.md`. Proof: `uv run pytest tests/unit/test_format_facts.py tests/unit/test_provenance.py tests/residue`.
  - 2026-10-07: sections appended to `drc.md`, `libraries.md`, `board.md` and `project.md`. Rows proved here are `KICAD-VERIFIED (10.0.x)`; the readings of the libraries and of the demo files that the proposal states were not run again and are `INFERRED`. `uv run pytest tests/unit/test_format_facts.py tests/unit/test_provenance.py tests/residue`: passed, exit 0.

## 2. Net-tie groups

- [x] 2.1 Add `FootprintInstance.net_ties` and `FootprintDef.net_ties`, regenerate `board.json` and `library.json`, and describe both in `docs/design-model.md` with the sentence that 0.2.x and 0.3.0 cannot read a document that carries the key (scenarios of "Net-tie groups in the model"). Before the fields are added, record in `tests/unit/lens/test_unused_keys.py` the SHA-256 of every file that `examples/blink_2layer/design.py` and `examples/blink_routed/design.py` plan for targets 9 and 10 with a fixed seed and timestamp; the test then holds through tasks 3.1 and 5.1 (scenario "Unused keys change no byte"). Proof: `uv run pytest tests/unit/model tests/unit/test_schema_drift.py tests/unit/lens/test_unused_keys.py`; `uv run python tools/gen_schemas.py --check` exits 0; `grep -c "cannot read" docs/design-model.md` grows by one.
  - 2026-10-07: the digests were recorded at `f36e08d9` before the fields were added (80 files, four builds; `fenolite_version` of `meta.json` left out). `uv run pytest tests/unit/model tests/unit/test_schema_drift.py tests/unit/lens/test_unused_keys.py`: passed, exit 0; `gen_schemas.py --check` exit 0; `docs/design-model.md` says `cannot read` once per key.
- [x] 2.2 Project `net_tie_pad_groups` in `pcb.py` and `mod.py` as a projected slot, refuse an edit with `kicad.board.projection-read-only`, and carry the child through `embed.place_footprint`; write `tests/unit/backends/kicad/test_net_ties.py` (scenarios of "Net-tie groups on boards and footprints"). Proof: `uv run pytest tests/unit/backends/kicad/test_net_ties.py tests/unit/backends/kicad/test_pcb_write_projections.py tests/unit/backends/kicad/test_mod.py tests/unit/backends/kicad/test_embed_property.py`; `uv run pyright src`.
  - 2026-10-07: `tests/unit/backends/kicad/test_net_ties.py` 15 passed; the four named files passed, exit 0; `uv run pyright src`: 0 errors.
- [x] 2.3 Add `Footprint.net_tie`, its checks in `definition`, the emitter child after `attr` in `_fpmap.py`, and the kind `net-tie` of `altium.not-lowered` in `backends/altium/lower.py`, outside `LOSS_KINDS` (if the Altium build still reports from `lens/altium.py` when this task starts, write under this task where the kind was added); write `tests/unit/dsl/test_net_tie.py` (scenarios of "Net-tie groups in authored footprints", "A net tie in an Altium build" in `tests/unit/cli/test_build_altium.py`). Proof: `uv run pytest tests/unit/dsl tests/unit/backends/kicad/test_mod_write.py tests/unit/backends/altium/test_lower.py`; `uv run pytest tests/unit/cli/test_build_altium.py -k net_tie`.
  - 2026-10-07: the Altium build still reports from `lens/altium.py`, so the two kinds were added in both places: `lens.altium.kicad_only_issues` (the build: one info per kind, from the resolved footprint definitions and the rule set) and `backends/altium/lower.py` (`MORE_KINDS`, `NET_TIE_KIND`, `SEVERITY_KIND`, counted in `_document` for the write of a model). Neither is in `LOSS_KINDS`. `uv run pytest tests/unit/dsl tests/unit/backends/kicad/test_mod_write.py tests/unit/backends/altium/test_lower.py`: passed, exit 0; `tests/unit/cli/test_build_altium.py -k net_tie`: 1 passed.
- [x] 2.4 Build the footprints of the net-tie bench as authored definitions with `Footprint.net_tie` (scenario "The written token loads") and run it again. Proof: `uv run pytest tests/kicad/check/test_net_ties.py -rA` on the local KiCad 10.0.6 and inside the pinned 9.0.9 image; the probe outcomes are unchanged.
  - 2026-10-07: done with task 1.2, the bench never held footprint text. On the local 10.0.6 the written token loads and the outcomes are those of task 1.2. The 9.0.9 half of the proof is owed: no 9.0.9 image was run in this session (no docker); the `kicad-9` job runs it and records `9.0.9.json`.
  - 2026-10-08: ticked: `tests/kicad/check/test_net_ties.py` passes inside the pinned 9.0.9 image with the authored footprints (the run named under task 1.2); the outcomes are those of 10.0.6.
- [x] 2.5 Skip the pad pairs of one group in `checks/copper.py`, count them in `summary.net_tie_pairs`, and extend `tests/unit/checks/test_copper.py` with the scenarios of "Pairs that are judged" and a brute-force comparison on boards with groups. Proof: `uv run pytest tests/unit/checks/test_copper.py -k "net_tie or brute_force"`; `uv run pytest tests/unit/checks`.
  - 2026-10-07: `uv run pytest tests/unit/checks/test_copper.py -k "net_tie or brute_force"`: 12 passed, exit 0; `tests/unit/checks`: passed.
- [x] 2.6 Add the net-tie rows to `tests/kicad/copper/test_parity_bench.py` and `test_copper_parity.py` with the probes `copper-nettie-group` and `copper-nettie-ungrouped`, and rewrite the net-tie and severity rows of the supported-cases table of `docs/formats/kicad/copper.md` (scenarios of "Net-tie parity canaries" and "Supported cases are documented against KiCad's DRC"). Proof: `uv run pytest tests/kicad/copper/test_parity_bench.py -k net_tie` without `kicad-cli`; `uv run pytest tests/kicad/copper/test_copper_parity.py -k net_tie -rA` on the local KiCad 10.0.6 and inside the pinned 9.0.9 image; `uv run pytest tests/unit/test_format_facts.py -k copper`.
  - 2026-10-07: `tests/kicad/copper/test_parity_bench.py -k net_tie` 4 passed without `kicad-cli`; `tests/kicad/copper/test_copper_parity.py -k net_tie` 2 passed on the local 10.0.6 (`copper-nettie-group` `equal`, `copper-nettie-ungrouped` `different`); `tests/unit/test_format_facts.py -k copper` passed. The two net-tie rows of `copper.md` say that 9.0.9 was not run. The 9.0.9 half of the proof is owed: no 9.0.9 image was run in this session (no docker); the `kicad-9` job runs it and records `9.0.9.json`.
  - 2026-10-08: ticked by the second local run of 2026-10-08 in the pinned 9.0.9 image (`kicad/kicad:9.0.9@sha256:e638b79b…`, linux/amd64, branch `v04-k9-probes-2`; whole `tests/kicad` without the corpus: 998 passed, 2 failed, 806 skipped, 1 xfailed; `tests/kicad/test_probe_results.py` passed on the 723 probes of major 9): `copper-nettie-group` = `equal` and `copper-nettie-ungrouped` = `different` on 9.0.9, recorded in `9.0.9.json`; `tests/kicad/copper/test_copper_parity.py` 30 passed, 2 skipped. The two net-tie rows of `copper.md` still say that 9.0.9 was not run: their labels were not touched by the commit that recorded the probes.

## 3. Waivers

- [x] 3.1 Add `Waiver` and `Findings.waivers`, regenerate `findings.json`, describe them in `docs/design-model.md` with the sentence that 0.2.x and 0.3.0 cannot read a `findings.json` that carries `waivers`, and add `Design.waive` with its checks and `to_model`; write `tests/unit/dsl/test_waivers.py` (scenarios of "Waivers in the DSL" and "Waivers in the findings layer"). Proof: `uv run pytest tests/unit/dsl/test_waivers.py tests/unit/model tests/unit/test_import_graph.py tests/unit/lens/test_unused_keys.py`; `uv run python tools/gen_schemas.py --check`.
  - 2026-10-07: `uv run pytest tests/unit/dsl/test_waivers.py tests/unit/model tests/unit/test_import_graph.py tests/unit/lens/test_unused_keys.py`: passed, exit 0; `gen_schemas.py --check` exit 0.
- [x] 3.2 Write `src/fenolite/checks/waivers.py` (`UNREPEATABLE_TYPES`, `waiver_matches`, `apply_waivers`, `WaiverOutcome`) and `tests/unit/checks/test_waivers.py` (matching, order of items, `min_gap`, effect on the issue, judged and unjudged waivers). Proof: `uv run pytest tests/unit/checks/test_waivers.py`; `uv run pyright src`.
  - 2026-10-07: `uv run pytest tests/unit/checks/test_waivers.py`: 27 passed, exit 0; pyright 0 errors. One addition to the spec's matching: an item also names an item of the same text, because a locator such as `/kicad_pcb/segment[12]` holds brackets that a glob reads as a set.
- [x] 3.3 Pass waivers through `run_checks`, `copper_stage` and `drc_stage`, and through `run_document_checks` to the copper stage of document input; add `CheckReport.waivers` and `result.waivers`, load them in `cmd_check.py` for a built project of either target, add `check.waiver-unmatched` and the `info` severity of the three copper codes to `ISSUE_CODES`, and the table of `check.waiver-unmatched` to `src/fenolite/cli/data/explain.toml` (`see = "check"`) (scenarios of "Waivers in the check", the one on a built Altium project included, "Waiver and exclusion issue codes" and "Copper stage issue codes"). Proof: `uv run pytest tests/unit/checks tests/unit/cli/test_check_readonly.py tests/unit/cli/test_explain_cmd.py`; `uv run pytest tests/unit/cli/test_check_cmd.py tests/unit/cli/test_check_altium_copper.py -k waiver`.
  - 2026-10-07: `uv run pytest tests/unit/checks tests/unit/cli/test_check_readonly.py tests/unit/cli/test_explain_cmd.py`: passed, exit 0; `tests/unit/cli/test_check_cmd.py tests/unit/cli/test_check_altium_copper.py -k waiver`: 3 passed. The scenario with pads uses `U1-9` and `U1-10` of the routed blink (0.25 mm apart under a class of 0.3 mm), library footprints, because the board footprint of an authored definition has no reference before c0077.
- [x] 3.4 Apply the design's copper waivers in `copper_guard` and in `altium_copper_guard` before their modes and report `result.copper_check.waivers` (scenarios of "Waivers in the copper guard", "A waived short builds for Altium" included). Proof: `uv run pytest tests/unit/cli/test_build_copper_guard.py tests/unit/cli/test_build_altium_guard.py`.
  - 2026-10-07: `uv run pytest tests/unit/cli/test_build_copper_guard.py tests/unit/cli/test_build_altium_guard.py`: passed, exit 0. On the KiCad target the test of "A waived short builds" names the two pads as the refused build prints them: on this base that is the footprint id and the pad number, and `KS1-1`, `KS1-2` once c0077 gives authored footprints a reference. On the Altium target the names are `KS1-1` and `KS1-2` already.
- [x] 3.5 Write `tests/kicad/check/test_waivers_oracle.py`: a built project with an authored net tie whose pads touch, a test-point via waived as `kicad.drc.via-dangling` and two pads waived as `copper.clearance`; `fenolite check` exits 0 with the three findings at `info`, and with the via removed it reports one `check.waiver-unmatched`. Proof: `uv run pytest tests/kicad/check/test_waivers_oracle.py -rA` on the local KiCad 10.0.6 and inside the pinned 9.0.9 image.
  - 2026-10-07: written. On the local 10.0.6: 1 passed, exit 0, with `--stages copper.clearance,drc.kicad`, the two stages a waiver reaches: no error is left, the waived findings are `info`, and without the via one `check.waiver-unmatched` is reported. The whole default pipeline cannot exit 0 on a project with an authored footprint before c0077 (`netlist.assignment_compare` reports its pads). The 9.0.9 half of the proof is owed: no 9.0.9 image was run in this session (no docker); the `kicad-9` job runs it and records `9.0.9.json`.
  - 2026-10-08: ticked by the second local run of 2026-10-08 in the pinned 9.0.9 image (`kicad/kicad:9.0.9@sha256:e638b79b…`, linux/amd64, branch `v04-k9-probes-2`; whole `tests/kicad` without the corpus: 998 passed, 2 failed, 806 skipped, 1 xfailed; `tests/kicad/test_probe_results.py` passed on the 723 probes of major 9): `tests/kicad/check/test_waivers_oracle.py` 1 passed.

## 4. KiCad exclusions

- [x] 4.1 Add `StoredExclusion` and `ExclusionSource` to `backends/base.py`, `ProjectInfo.exclusions` to `pro.py`, and `KicadBackend.stored_exclusions` with `_EXCLUSION_SOURCE` (scenarios of "Stored exclusions source" and "Stored exclusions are read"). Proof: `uv run pytest tests/unit/backends/test_base_types.py -k exclusion tests/unit/backends/kicad/test_pro_read.py -k exclusion tests/unit/test_import_graph.py`; `uv run pyright src`.
  - 2026-10-07: `uv run pytest tests/unit/backends/test_base_types.py -k exclusion tests/unit/backends/kicad/test_pro_read.py -k exclusion tests/unit/test_import_graph.py`: passed, exit 0; pyright 0 errors.
- [x] 4.2 Add the comment, the live and stale verdicts, `summary.exclusions` and `check.exclusion-stale` to `drc_stage`, pass the stored exclusions from `run_checks`, and add a stage run to `test_drc_exclusions.py` in which an exclusion moved by 1 nm gives `moved`, and add the table of `check.exclusion-stale` to `src/fenolite/cli/data/explain.toml` (scenarios of "Exclusions in the DRC stage" and "Codes explained"). Proof: `uv run pytest tests/unit/checks/test_drc_stage.py -k exclusion`; `uv run pytest tests/unit/cli/test_explain_cmd.py`; `uv run pytest tests/kicad/check/test_drc_exclusions.py -k stage -rA` on the local KiCad 10.0.6 and inside the pinned 9.0.9 image.
  - 2026-10-07: `tests/unit/checks/test_drc_stage.py -k exclusion` 7 passed; `tests/unit/cli/test_explain_cmd.py` passed; `tests/kicad/check/test_drc_exclusions.py -k stage` 1 passed on the local 10.0.6. The 9.0.9 half of the proof is owed: no 9.0.9 image was run in this session (no docker); the `kicad-9` job runs it and records `9.0.9.json`.
  - 2026-10-08: ticked: the stage test of `tests/kicad/check/test_drc_exclusions.py` passes inside the pinned 9.0.9 image (the run named under task 1.3).
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
