lgili/Fenolite/openspec/changes/c0115-power-copper-analysis/tasks.md

## 0. Entry check

- [x] 0.1 Read the living `board-analyses` spec and `openspec list`, and the state of c0101, c0102, c0105 and c0106. Write under this task, with the date: whether `0.3.0` is released; whether "Clearance on a layer", "Creepage on the board surface" or "Requirement tables supplied by the user" changed since `origin/dev` `9aba2dff` (then regenerate that MODIFIED text from the living one and re-apply this change's edits); whether c0101 is on `dev` (its `Stackup.depth` and one entry per sheet are used by tasks 6.1 and 7.1; if it is not, those parts wait for it and the rest goes on); whether c0102 is on `dev` (its "Board boundary" is the boundary that task 8.1 bridges); whether c0105, c0106 or c0099 added codes, kinds or modules whose names collide with this change's; whether S-0681 and S-0682 are still free in `docs/evidence/sources.md`. Proof: `openspec validate c0115-power-copper-analysis --strict --no-interactive` passes after any regeneration; `grep -cE '^\| S-068[12] ' docs/evidence/sources.md` prints `0` before task 1.1.
  - 2026-10-07, at `origin/dev` `9aba2dff` (proposal repaired, nothing built): the three living texts are unchanged since the proposal's base `7203e4b6`; no open change on `dev` holds a delta of `board-analyses`; `Stackup` has no `depth`; `0.3.0` is not released; c0101 and c0102 are not on `dev`; the sources end at S-0601.
  - 2026-10-07, on the branch `v04-impl-c0115` from the local integration branch `v04` at `991b3f57`: `0.3.0` is not released (tags end at `v0.2.1`); `git diff 9aba2dff HEAD` over the living `board-analyses` spec, `src/fenolite/analysis` and `cli/cmd_analyze.py` is empty, so the three MODIFIED texts need no regeneration; c0101, c0102, c0105 and c0106 are proposals only (no task ticked) and c0099 is not in `openspec/changes`, so `Stackup` has no `depth`, tasks 6.1 (barrel heights) and 7.1 wait for c0101, and no code, kind or module name collides; c0126 is a proposal only, so `FootprintInstance` has no `graphics` and the count of copper graphics reads board graphics and, when the field exists, those of a footprint instance; S-0681 and S-0682 are free (`grep -c` prints 0). `openspec validate c0115-power-copper-analysis --strict --no-interactive` passes.
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
