lgili/Fenolite/openspec/changes/c0116-export-documents/tasks.md

## 0. Entry check

- [x] 0.1 Read the living `manufacturing-exports`, `cli-contract`, `kicad-library-resolution`, `kicad-oracle` and `kicad-schematic` specs and `openspec list`. Write under this task, with the date and the commit of `dev`: that `0.3.0` is released and c0084 is archived (if c0084 is still open, stop: it lands first); for each of the nine MODIFIED requirements of this change ("Export command", "Manifest option of producing commands", "Export kinds
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
