lgili/Fenolite/tests/data/kicad/routing/planebench_t9_after_filled.kicad_pcb

## KiCad design tests/data/kicad/routing/planebench_t9_after_filled.kicad_pcb (2026-10-09)

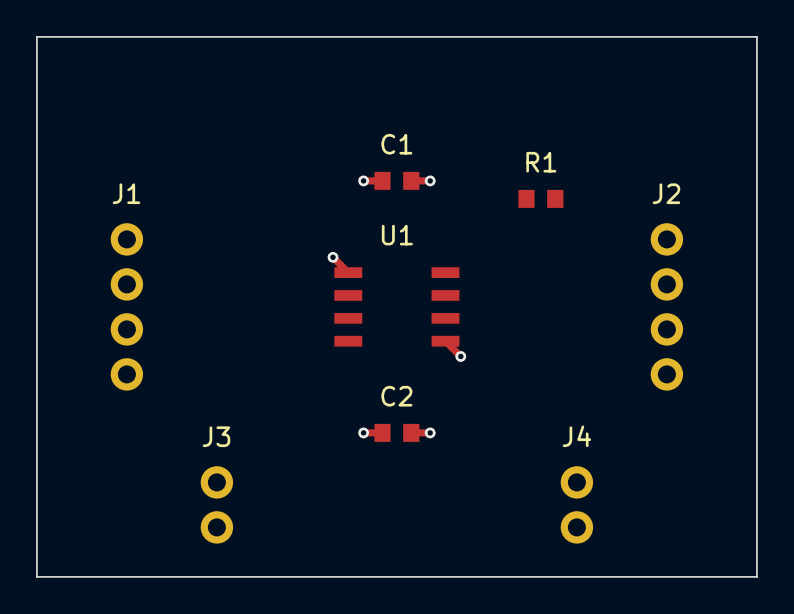
[picture p5: board planebench_t9_after_filled.kicad_pcb from above]

Board: 4 copper layers, 40.0 x 30.0 mm, 8 parts (0 on the bottom side), 10 nets.

Parts:
C1, C2: 100n; Chip_0603
J1: IN; Header_1x4_P2.5
J2: OUT; Header_1x4_P2.5
J3, J4: HV; Header_1x2_P2.5
R1: 1k; Chip_0603
U1: MCU; SOIC_8

Connections:
GND: C1.2, C2.2, J1.2, J2.3, U1.4
HV1: J3.1, J4.1
HV2: J3.2, J4.2
SIG1: J1.3, U1.1
SIG2: J1.4, U1.2
SIG3: R1.1, U1.3
SIG4: R1.2, U1.5
SIG5: J2.1, U1.6
SIG6: J2.2, U1.7
VCC: C1.1, C2.1, J1.1, J2.4, U1.8
