lgili/Fenolite/tests/data/kicad/routing/pair_two_headers.kicad_pcb

## KiCad design tests/data/kicad/routing/pair_two_headers.kicad_pcb (2026-10-09)

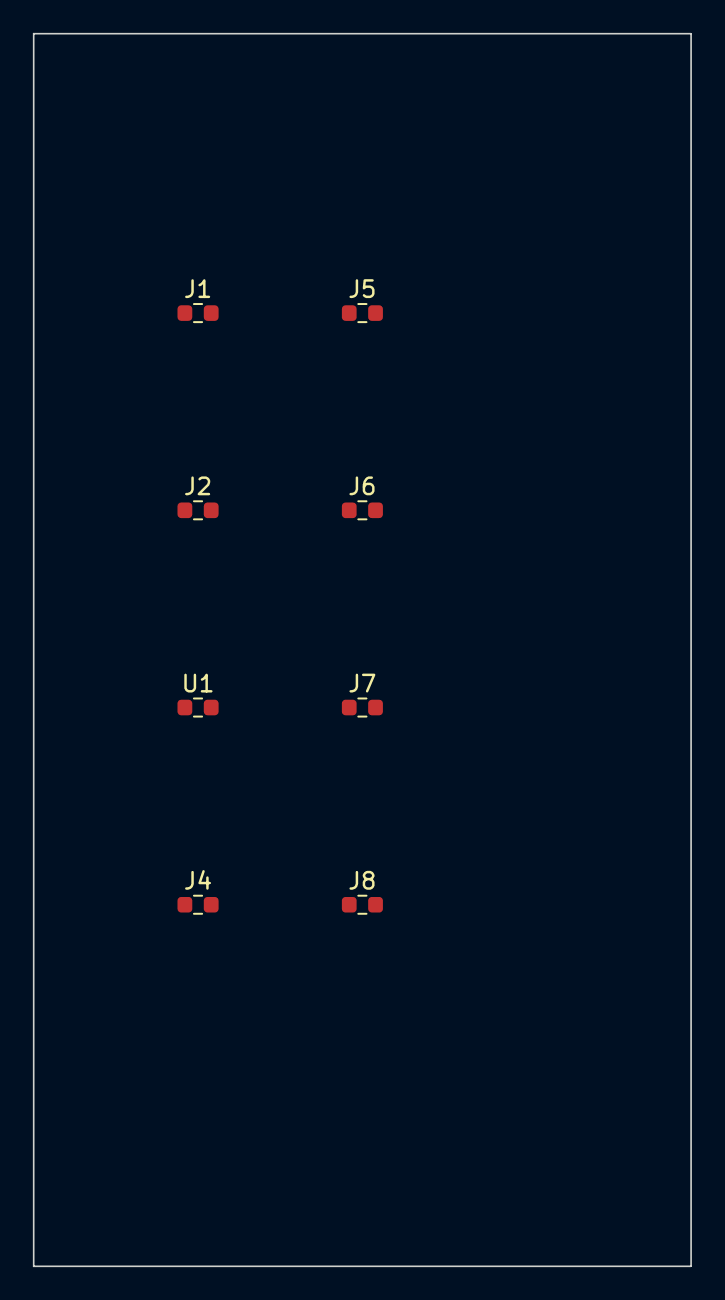
[picture p6: board pair_two_headers.kicad_pcb from above]

Board: 2 copper layers, 40.0 x 75.0 mm, 8 parts (0 on the bottom side), 4 nets, no tracks yet.

Parts:
J1, J2, J4, J5, J6, J7, J8: Mini_R_0603
U1: Mini_R_0603

Connections:
S1: J7.1, U1.1
S2: J4.1, J8.1
USB_N: J2.1, J6.1
USB_P: J1.1, J5.1
