lgili/Fenolite/src/fenolite/backends/kicad/_fpmap.py

# SPDX-License-Identifier: Apache-2.0
# Copyright (c) 2026 Fenolite contributors
"""The footprint mapping shared by footprint files (``mod``) and boards (``pcb``): pads, drills,
padstacks and graphics, their scoped ids, and the field emitters that write them back.

Facts: ``docs/formats/kicad/libraries.md`` (footprints) and ``docs/formats/kicad/board.md``
(boards). Readers are parameterised by the root chain (``("footprint",)`` in a footprint file,
``("kicad_pcb", "footprint")`` for pads of a board, ``("kicad_pcb",)`` for board graphics), so that
anchored inventory rows match, and report kept-opaque children with the context's code. Emitters
return the items of each modelled field; ``pcb.ModelSource`` wraps them, so this module never imports
``pcb``.
"""

# evidence: see mod, pcb

from __future__ import annotations

from collections.abc import Callable, Mapping, Sequence
from types import MappingProxyType
from typing import Protocol

from fenolite.backends.kicad import slots as slotlib
from fenolite.backends.kicad import zones as zonelib
from fenolite.backends.kicad._libread import Context, child_locators, leading_atoms
from fenolite.backends.kicad.sexpr import Atom, AtomKind, Node, dumps
from fenolite.core.coords import Point, Size
from fenolite.core.ids import content_hash, content_id, derived_id
from fenolite.core.units import format_angle
from fenolite.model.base import Modeled, Opaque, Slot
from fenolite.model.board import (
    Graphic,
    GraphicKind,
    Pad,
    PadFabProperty,
    Padstack,
    PadstackLayer,
    ZoneConnection,
)
from fenolite.model.library import FootprintDef

FP_GRAPHIC_HEADS: Mapping[str, GraphicKind] = MappingProxyType(
    {"fp_line": "line", "fp_arc": "arc", "fp_circle": "circle", "fp_rect": "rect", "fp_poly": "polygon"}
)
GR_GRAPHIC_HEADS: Mapping[str, GraphicKind] = MappingProxyType(
    {"gr_line": "line", "gr_arc": "arc", "gr_circle": "circle", "gr_rect": "rect", "gr_poly": "polygon"}
)
PAD_FIELDS: Mapping[str, str] = MappingProxyType(
    {
        "at": "position",
        "size": "size",
        "layers": "layers",
        "uuid": "native_ids",
        "drill": "drill",
        "zone_connect": "zone_connection",
        "property": "fab_property",
    }
)
PAD_POSITIONAL = ("number", "kind", "shape")
PAD_CANONICAL: tuple[str, ...] = (
    *PAD_POSITIONAL, "position", "size", "drill", "fab_property", "layers", "zone_connection", "native_ids",
)  # fmt: skip
"""Where a library pad gains a child it did not have: ``zone_connect`` goes before ``uuid``, and the
fabrication ``property`` after ``drill`` (or ``size``) and before ``layers``."""
ZONE_CONNECT = "zone_connect"
NET_TIES = "net_tie_pad_groups"
"""The footprint child that lists the net-tie groups, one string per group (``libraries.md``, "Net-tie
groups"; change c0114). It is no field of ``DEF_FIELDS``: a read child stays an opaque slot, projected into
``net_ties``, and only an authored definition writes it from the field."""
FAB_PROPERTY = "property"
FAB_PROPERTY_TOKENS: Mapping[PadFabProperty, str] = MappingProxyType(
    {
        "bga": "pad_prop_bga",
        "fiducial_global": "pad_prop_fiducial_glob",
        "fiducial_local": "pad_prop_fiducial_loc",
        "test_point": "pad_prop_testpoint",
        "heatsink": "pad_prop_heatsink",
        "castellated": "pad_prop_castellated",
        "mechanical": "pad_prop_mechanical",
        "press_fit": "pad_prop_pressfit",
    }
)
"""``Pad.fab_property`` to the token of a pad's ``(property <token>)`` child (``board.md``,
``H-K-PAD-FABPROP``)."""
_FAB_PROPERTIES: Mapping[str, PadFabProperty] = MappingProxyType(
    {token: value for value, token in FAB_PROPERTY_TOKENS.items()}
)
DEF_FIELDS: Mapping[str, str] = MappingProxyType(
    {"descr": "description", "attr": "kind", "pad": "pads", **dict.fromkeys(FP_GRAPHIC_HEADS, "graphics")}
)
"""The field map of a footprint definition (``mod.FOOTPRINT_FIELDS`` is this mapping)."""
DEF_POSITIONAL = ("name",)
GRAPHIC_FIELDS: Mapping[str, str] = MappingProxyType(
    {
        **dict.fromkeys(("start", "mid", "end", "center", "pts"), "points"),
        "layer": "layer",
        "uuid": "native_ids",
        "fill": "filled",
        "width": "width",
    }
)
PAD_KINDS: frozenset[str] = frozenset({"smd", "thru_hole", "np_thru_hole", "connect"})
PAD_SHAPES: frozenset[str] = frozenset({"circle", "rect", "oval", "roundrect", "trapezoid", "custom"})
PADSTACK_MODES: frozenset[str] = frozenset({"front_inner_back", "custom"})
POINT_HEADS: Mapping[GraphicKind, tuple[str, ...]] = MappingProxyType(
    {
        "line": ("start", "end"),
        "arc": ("start", "mid", "end"),
        "circle": ("center", "end"),
        "rect": ("start", "end"),
    }
)
_FILLS = {"yes": True, "solid": True, "no": False, "none": False}
_FP_KIND_HEADS: Mapping[GraphicKind, str] = MappingProxyType(
    {kind: head for head, kind in FP_GRAPHIC_HEADS.items()}
)
_PLAIN_STROKES = frozenset({"solid", "default"})

Items = dict[str, list[Node | Atom]]
"""Field name → the children a modelled field emits, in order."""
LayerExpander = Callable[[tuple[str, ...]], "tuple[str, ...] | None"]
"""Expands wildcard layer names; returns ``None`` when the list has no wildcard."""
NetResolver = Callable[[Node, str], "tuple[str | None, bool]"]
"""Resolves a pad's ``net`` child to ``(net id, modelled)``; ``modelled`` false keeps it opaque."""


class IdSource(Protocol):
    """Gives ``(id, native_ids)`` for a node; ``section`` scopes content ids, ``suffix`` extends uuids."""

    def of(self, prefix: str, section: str, node: Node, suffix: str = "") -> tuple[str, dict[str, str]]: ...


class Ids:
    """Scoped ids of the sub-entities of one definition (see docs/design-model.md, "Library definitions").

    A uuid repeated inside one definition (copied graphics in the official library, S-0018) keeps the
    plain form for its first occurrence; the k-th repetition appends ``:<k>``, so ids stay unique.
    """

    def __init__(self, native: str) -> None:
        self.native = native
        self.seen: dict[tuple[str, str], int] = {}
        self.uuids: dict[tuple[str, str], int] = {}

    def of(self, prefix: str, section: str, node: Node, suffix: str = "") -> tuple[str, dict[str, str]]:
        uuid = node.find("uuid")
        atoms = uuid.atoms() if uuid is not None else ()
        if atoms:
            value = atoms[0].value
            repeat = self.uuids.get((prefix, value), 0)
            self.uuids[(prefix, value)] = repeat + 1
            native = f"{self.native}:{value}{suffix}" + (f":{repeat}" if repeat else "")
            return derived_id(prefix, "kicad", native), {"kicad": value}
        text = dumps(node, style="compact") + suffix
        count = self.seen.get((section, text), 0)
        self.seen[(section, text)] = count + 1
        return content_id(prefix, "kicad", self.native, section, content_hash(text, count)), {}


def text_of(node: Node) -> str:
    return " ".join(a.value for a in node.atoms())


def symbols(node: Node) -> list[str]:
    return [a.value for a in node.atoms()]


def size_of(ctx: Context, node: Node, locator: str) -> Size:
    point = ctx.point(node, locator)
    return Size(point.x, point.y)


def read_padstack(
    ctx: Context, pad: Node, node: Node, pad_loc: str, loc: str, shape: str, size: Size, ids: IdSource
) -> Padstack:
    mode = node.find("mode")
    if mode is not None:
        value = " ".join(symbols(mode))
        if value not in PADSTACK_MODES:
            raise ctx.error(f"unknown padstack mode {value!r}", pad_loc, pad)
    layers = [PadstackLayer("F.Cu", shape, size)]  # type: ignore[arg-type]
    for layer_loc, child in child_locators(loc, node):
        if not isinstance(child, Node) or child.name != "layer":
            continue
        names = child.atoms()
        name = names[0].value if names else ""
        shape_node, size_node = child.find("shape"), child.find("size")
        if shape_node is None or size_node is None:
            missing = "shape" if shape_node is None else "size"
            raise ctx.error(f"padstack layer {name!r} has no {missing}", layer_loc, child)
        layer_shape = " ".join(symbols(shape_node))
        if layer_shape not in PAD_SHAPES:
            raise ctx.error(f"unknown pad shape {layer_shape!r} in padstack layer {name!r}", layer_loc, child)
        layers.append(PadstackLayer(name, layer_shape, size_of(ctx, size_node, f"{layer_loc}/size[0]")))  # type: ignore[arg-type]
    ident, native_ids = ids.of("pst", "pad", pad, ":padstack")
    return Padstack(id=ident, native_ids=native_ids, provenance=ctx.provenance(loc), layers=tuple(layers))


def read_pad(
    ctx: Context,
    node: Node,
    loc: str,
    ids: IdSource,
    *,
    root: tuple[str, ...],
    fields: Mapping[str, str] = PAD_FIELDS,
    expand: LayerExpander | None = None,
    net: NetResolver | None = None,
) -> Pad:
    """One pad. ``expand`` and ``net`` are given for board pads (wildcard layers, net references)."""
    chain = (*root, "pad")
    atoms = leading_atoms(node)
    if len(atoms) < 3:
        raise ctx.error("a pad needs a number, a type and a shape", loc, node)
    number, kind, shape = atoms[0].value, atoms[1].value, atoms[2].value
    if kind not in PAD_KINDS:
        raise ctx.error(f"unknown pad type {kind!r}", loc, node)
    if shape not in PAD_SHAPES:
        raise ctx.error(f"unknown pad shape {shape!r}", loc, node)
    slots = ctx.split(node, dict(fields), chain, PAD_POSITIONAL)
    position, rotation, size, drill = None, 0, None, None
    hole_shape, hole_length, hole_turn = "round", None, 0
    layers: tuple[str, ...] = ()
    net_id: str | None = None
    zone_connection: ZoneConnection | None = None
    padstack_at: tuple[int, Node, str] | None = None
    fab_property: PadFabProperty | None = None
    connects = len(node.nodes(ZONE_CONNECT))
    marks = len(node.nodes(FAB_PROPERTY))
    for index, (child_loc, child) in enumerate(child_locators(loc, node)):
        if not isinstance(child, Node):
            continue
        head = child.name
        if head == ZONE_CONNECT:
            # one child with a code from 0 to 3 is modelled; a repeated one is projected from the first
            found = zonelib.read_pad_connect(child)
            if child_loc.endswith("[0]"):
                zone_connection = found
            if found is None or connects > 1:
                slots[index] = ctx.opaque(child, chain)
                why = "is repeated" if found is not None else "is not a code from 0 to 3"
                ctx.kept_opaque(f"zone_connect {why}; kept as written", child_loc)
        elif head == FAB_PROPERTY:
            # one child with a known token is modelled; a repeated one is projected from the first
            mark = read_fab_property(child)
            if child_loc.endswith("[0]"):
                fab_property = mark
            if mark is None or marks > 1:
                slots[index] = ctx.opaque(child, chain)
                why = "is repeated" if mark is not None else "is not a known fabrication property"
                ctx.kept_opaque(f"pad property {why}; kept as written", child_loc)
        elif head == "at":
            position = ctx.point(child, child_loc)
            values = child.atoms()
            if len(values) > 2:
                rotation = ctx.udeg(values[2], child_loc, child)
        elif head == "size":
            size = size_of(ctx, child, child_loc)
        elif head == "layers":
            layers = tuple(symbols(child))
            expanded = expand(layers) if expand is not None else None
            if expanded is not None:
                layers = expanded
                slots[index] = ctx.opaque(child, chain)
        elif head == "drill":
            drill, hole_shape, hole_length, hole_turn = read_drill(ctx, child, child_loc, slots, index, chain)
        elif head == "padstack":
            padstack_at = (index, child, child_loc)
        elif head == "net" and net is not None:
            net_id, modelled = net(child, child_loc)
            if not modelled:
                slots[index] = ctx.opaque(child, chain)
    if position is None or size is None:
        raise ctx.error(f"pad {number!r} has no {'at' if position is None else 'size'}", loc, node)
    padstack = None
    if padstack_at is not None:
        index, child, child_loc = padstack_at
        padstack = read_padstack(ctx, node, child, loc, child_loc, shape, size, ids)
        slots[index] = ctx.opaque(child, chain)
        ctx.kept_opaque("padstack: per-layer extras are not modelled", child_loc)
    elif hole_shape == "slot":
        ident, native_ids = ids.of("pst", "pad", node, ":padstack")
        padstack = Padstack(
            id=ident,
            native_ids=native_ids,
            provenance=ctx.provenance(loc),
            hole_shape="slot",
            hole_length=hole_length,
            hole_rotation=hole_turn,  # in the pad's own frame, for a footprint file and for a board
        )
    ident, native_ids = ids.of("pad", "pad", node)
    return Pad(
        id=ident,
        native_ids=native_ids,
        provenance=ctx.provenance(loc),
        ext={"kicad": slotlib.to_ext(slots)},
        number=number,
        shape=shape,  # type: ignore[arg-type]
        size=size,
        position=position,
        kind=kind,  # type: ignore[arg-type]
        rotation=rotation,
        drill=drill,
        layers=layers,
        net_id=net_id,
        padstack=padstack,
        zone_connection=zone_connection,
        fab_property=fab_property,
    )


def read_fab_property(child: Node) -> PadFabProperty | None:
    """The mark of a pad's ``(property <token>)`` child, or ``None`` for a token outside the table."""
    atoms = child.atoms()
    if len(atoms) != 1 or child.nodes():
        return None
    return _FAB_PROPERTIES.get(atoms[0].value)


def fab_property_node(value: PadFabProperty) -> Node:
    """``(property <token>)`` for a pad's mark."""
    return node(FAB_PROPERTY, Atom.symbol(FAB_PROPERTY_TOKENS[value]))


def read_drill(
    ctx: Context, node: Node, loc: str, slots: list[Slot], index: int, chain: tuple[str, ...]
) -> tuple[int | None, str, int | None, int]:
    """Round and oval drills are modelled; offsets and unusual forms stay opaque."""
    atoms = node.atoms()
    numbers = [a for a in atoms if a.kind == AtomKind.NUMBER]
    lists = node.nodes()
    simple = len(atoms) == 1 and len(numbers) == 1
    if simple and not lists:
        return ctx.nm(numbers[0], loc, node), "round", None, 0
    if len(atoms) == 3 and atoms[0].value == "oval" and len(numbers) == 2 and not lists:
        x_size, y_size = (ctx.nm(value, loc, node) for value in numbers)
        slots[index] = Modeled("drill")
        if x_size == y_size:
            return x_size, "round", None, 0
        return min(x_size, y_size), "slot", max(x_size, y_size), 90_000_000 if y_size > x_size else 0
    slots[index] = ctx.opaque(node, chain)
    if simple and [c.name for c in lists] == ["offset"]:
        ctx.kept_opaque("drill offset is not modelled", loc)
        return ctx.nm(numbers[0], loc, node), "round", None, 0
    ctx.kept_opaque("oval or unusual drill: drill is None", loc)
    return None, "round", None, 0


def padstack_key(pad: Pad, child: Node) -> tuple[tuple[str, str, int, int], ...] | None:
    """The padstack layers a ``padstack`` child stands for, as ``read_padstack`` reads them."""
    layers = [("F.Cu", str(pad.shape), pad.size.w, pad.size.h)]
    for row in child.nodes("layer"):
        names, shape, size = row.atoms(), row.find("shape"), row.find("size")
        if not names or shape is None or size is None or len(size.atoms()) != 2:
            return None
        try:
            w, h = (a.to_nm() for a in size.atoms())
        except ValueError:
            return None
        layers.append((names[0].value, " ".join(symbols(shape)), w, h))
    return tuple(layers)


def unrepresentable(node: Node, kind: GraphicKind) -> str | None:
    """Why a graphic cannot be represented, or None."""
    if node.find("layer") is None:
        return "graphic without a layer"
    if kind == "polygon":
        pts = node.find("pts")
        if pts is None:
            return "polygon without points"
        if any(c.name != "xy" for c in pts.nodes()):
            return "arc inside the points of a polygon"
    else:
        missing = [name for name in POINT_HEADS[kind] if node.find(name) is None]
        if missing:
            return f"{kind} without {missing[0]}"
    fill = node.find("fill")
    if fill is not None:
        values = symbols(fill)
        if fill.nodes() or len(values) != 1 or values[0] not in _FILLS:
            return f"fill {' '.join(values) or '(list)'} is not representable"
    if kind == "rect" and node.find("radius") is not None:
        return "rectangle with a corner radius"
    return None


def read_graphic(
    ctx: Context, node: Node, loc: str, kind: GraphicKind, ids: IdSource, *, root: tuple[str, ...]
) -> Graphic:
    chain = (*root, node.name)
    slots = ctx.split(node, dict(GRAPHIC_FIELDS), chain)
    if kind == "polygon":
        pts = node.find("pts")
        assert pts is not None
        points = tuple(ctx.point(c, f"{loc}/pts[0]/xy[{i}]") for i, c in enumerate(pts.nodes()))
    else:
        points = tuple(ctx.point(node.find(name), f"{loc}/{name}[0]") for name in POINT_HEADS[kind])  # type: ignore[arg-type]
    layer_node = node.find("layer")
    assert layer_node is not None
    layer = text_of(layer_node)
    fill = node.find("fill")
    filled = _FILLS[symbols(fill)[0]] if fill is not None else False
    width = 0
    for child_loc, child in child_locators(loc, node):
        if not isinstance(child, Node):
            continue
        if child.name == "width" and child.atoms():
            width = ctx.nm(child.atoms()[0], child_loc, child)
        elif child.name == "stroke":
            stroke_width, stroke_type = child.find("width"), child.find("type")
            if stroke_width is not None and stroke_width.atoms():
                width = ctx.nm(stroke_width.atoms()[0], f"{child_loc}/width[0]", stroke_width)
            kind_text = text_of(stroke_type) if stroke_type is not None else "default"
            if kind_text not in _PLAIN_STROKES:
                ctx.kept_opaque(f"stroke type {kind_text!r} is not modelled", child_loc)
    ident, native_ids = ids.of("gfx", "gfx", node)
    return Graphic(
        id=ident,
        native_ids=native_ids,
        provenance=ctx.provenance(loc),
        ext={"kicad": slotlib.to_ext(slots)},
        kind=kind,
        layer=layer,
        points=points,
        width=width,
        filled=filled,
    )


# --- emitters -------------------------------------------------------------------------------------


def angle_atom(udeg: int) -> Atom:
    """An angle in degrees, the shortest exact decimal (``90``, ``-45``, ``30.5``)."""
    return Atom(format_angle(udeg, "deg")[: -len("deg")], AtomKind.NUMBER)


def node(head: str, *children: Node | Atom) -> Node:
    return Node(Atom.symbol(head), children)


def point_node(head: str, point: Point, *extra: Atom) -> Node:
    return node(head, Atom.from_nm(point.x), Atom.from_nm(point.y), *extra)


def at_node(point: Point, udeg: int, *, always: bool = False) -> Node:
    """``(at X Y [ANGLE])``; the angle is omitted when it is zero unless ``always``."""
    return point_node("at", point, *((angle_atom(udeg),) if udeg or always else ()))


def uuid_items(native_ids: Mapping[str, str]) -> list[Node | Atom]:
    value = native_ids.get("kicad")
    return [node("uuid", Atom.string(value))] if value is not None else []


def layers_node(head: str, layers: tuple[str, ...]) -> Node:
    return node(head, *(Atom.string(name) for name in layers))


def emit_pad(pad: Pad, net: Node | None, *, angle: int | None = None) -> Items:
    """The modelled fields of a pad; ``angle`` replaces ``pad.rotation`` (a board stores it absolute)."""
    drill_node: list[Node | Atom] = []
    if pad.drill is not None:
        stack = pad.padstack
        if stack is not None and stack.hole_shape == "slot":
            if stack.hole_length is None:
                raise ValueError(f"pad {pad.number}: KiCad writer cannot represent this slot rotation")
            # The slot's axis is in the pad's own frame, as KiCad stores it: along X or along Y.
            turn = stack.hole_rotation % 180_000_000
            if turn == 0:
                w, h = stack.hole_length, pad.drill
            elif turn == 90_000_000:
                w, h = pad.drill, stack.hole_length
            else:
                raise ValueError(f"pad {pad.number}: KiCad writer cannot represent this slot rotation")
            drill_node.append(node("drill", Atom.symbol("oval"), Atom.from_nm(w), Atom.from_nm(h)))
        else:
            drill_node.append(node("drill", Atom.from_nm(pad.drill)))
    items: Items = {
        "number": [Atom.string(pad.number)],
        "kind": [Atom.symbol(pad.kind)],
        "shape": [Atom.symbol(pad.shape)],
        "position": [at_node(pad.position, pad.rotation if angle is None else angle)],
        "size": [node("size", Atom.from_nm(pad.size.w), Atom.from_nm(pad.size.h))],
        "layers": [layers_node("layers", pad.layers)],
        "native_ids": uuid_items(pad.native_ids),
        "drill": drill_node,
        "zone_connection": (
            [] if pad.zone_connection is None else [zonelib.pad_connect_node(pad.zone_connection)]
        ),
        "fab_property": [] if pad.fab_property is None else [fab_property_node(pad.fab_property)],
    }
    if net is not None:
        items["net_id"] = [net]
    return items


def emit_graphic(graphic: Graphic, head: str) -> Items:
    """The modelled fields of a graphic (``head`` is its ``fp_*`` or ``gr_*`` head)."""
    if graphic.kind == "polygon":
        points: list[Node | Atom] = [node("pts", *(point_node("xy", p) for p in graphic.points))]
    else:
        points = [
            point_node(name, p) for name, p in zip(POINT_HEADS[graphic.kind], graphic.points, strict=True)
        ]
    return {
        "points": points,
        "layer": [node("layer", Atom.string(graphic.layer))],
        "native_ids": uuid_items(graphic.native_ids),
        "filled": [node("fill", Atom.symbol("yes" if graphic.filled else "no"))],
        "width": [node("width", Atom.from_nm(graphic.width))],
    }


def net_tie_groups(child: Node) -> tuple[tuple[str, ...], ...]:
    """The groups of one ``net_tie_pad_groups`` child: each string is split at commas, the spaces around a
    number and empty parts are dropped (``"1, 2"`` and ``"1,2"`` both give ``("1", "2")``), and a string
    without a number gives no group."""
    groups: list[tuple[str, ...]] = []
    for atom in child.atoms():
        numbers = tuple(part.strip() for part in atom.value.split(",") if part.strip())
        if numbers:
            groups.append(numbers)
    return tuple(groups)


def net_tie_node(groups: Sequence[Sequence[str]]) -> Node:
    """``(net_tie_pad_groups "1, 2" …)``: one string per group, its numbers joined with ``", "``."""
    return node(NET_TIES, *(Atom.string(", ".join(group)) for group in groups))


def projected_net_ties(slots: Sequence[Slot]) -> tuple[tuple[str, ...], ...] | None:
    """The groups that the opaque ``net_tie_pad_groups`` children of a footprint's slot list stand for, in
    slot order; ``None`` when it has no such child."""
    found: list[tuple[str, ...]] = []
    seen = False
    for slot in slots:
        if isinstance(slot, Opaque) and slot.fragment.startswith(f"({NET_TIES}"):
            child = slotlib.opaque_child(slot)
            if isinstance(child, Node) and child.name == NET_TIES:
                seen = True
                found.extend(net_tie_groups(child))
    return tuple(found) if seen else None


def emit_attr(kind: str, flags: Sequence[str]) -> Node:
    """``(attr KIND FLAG …)``; the kind ``unspecified`` is not written."""
    values = ([] if kind == "unspecified" else [kind]) + list(flags)
    return node("attr", *(Atom.symbol(v) for v in values))


class _Items:
    """A ``slots.SlotSource`` over prepared items (``pcb.ModelSource`` without importing ``pcb``)."""

    def __init__(self, items: Mapping[str, Sequence[Node | Atom]], wanted: set[str]) -> None:
        self._items = {k: tuple(v) for k, v in items.items() if k in wanted}

    def items(self, field: str) -> Sequence[Node | Atom]:
        return self._items.get(field, ())

    def fields(self) -> list[str]:
        return [name for name, values in self._items.items() if values]


def _modelled(slots: Sequence[Slot]) -> set[str]:
    return {s.field for s in slots if isinstance(s, Modeled)}


def _entity_slots(entity: Pad | Graphic | FootprintDef) -> tuple[Slot, ...]:
    bag = entity.ext.get("kicad")
    return slotlib.from_ext(bag) if bag is not None else ()


def _graphic_head(graphic: Graphic) -> str:
    locator = graphic.provenance.locator if graphic.provenance is not None else ""
    head = locator.rsplit("/", 1)[-1].split("[", 1)[0]
    return head if head in FP_GRAPHIC_HEADS else _FP_KIND_HEADS[graphic.kind]


def emit_footprint(
    defn: FootprintDef,
    *,
    root_chain: tuple[str, ...] = ("footprint",),
    opaque: Callable[[Opaque], Node | Atom] = slotlib.opaque_child,
) -> Node:
    """A definition read from a file, emitted as a ``footprint`` node from its slots.

    Opaque children come back as read (through ``opaque``, which a writer passes to see each one);
    modelled ones from the definition's current values. Definitions without slots are refused.
    """
    slots = _entity_slots(defn)
    if not slots:
        raise ValueError(
            f"{defn.lib_id!r} has no KiCad slot list; only definitions read from a file are emitted"
        )
    pads = [_rebuild_pad(pad, opaque) for pad in defn.pads]
    graphics = [
        _rebuild(g, emit_graphic(g, _graphic_head(g)), _graphic_head(g), opaque=opaque) for g in defn.graphics
    ]
    items: dict[str, list[Node | Atom]] = {
        "name": [Atom.string(defn.name)],
        "description": [node("descr", Atom.string(defn.description))],
        "kind": [emit_attr(defn.kind, defn.flags)],
        "net_ties": [net_tie_node(defn.net_ties)] if defn.net_ties else [],
        "pads": list(pads),
        "graphics": list(graphics),
    }
    return slotlib.rebuild(Atom.symbol(root_chain[-1]), slots, _Items(items, _modelled(slots)), opaque=opaque)


def opaque_zone_connects(slots: Sequence[Slot]) -> list[tuple[int, Node]]:
    """``(slot index, child)`` of each opaque ``zone_connect`` child of a pad's slot list."""
    out: list[tuple[int, Node]] = []
    for index, slot in enumerate(slots):
        if isinstance(slot, Opaque) and slot.fragment.startswith(f"({ZONE_CONNECT}"):
            child = slotlib.opaque_child(slot)
            if isinstance(child, Node) and child.name == ZONE_CONNECT:
                out.append((index, child))
    return out


def projected_zone_connect(slots: Sequence[Slot]) -> ZoneConnection | None:
    """The connection that the opaque ``zone_connect`` children of a pad stand for (the first one's)."""
    found = opaque_zone_connects(slots)
    return zonelib.read_pad_connect(found[0][1]) if found else None


def opaque_fab_properties(slots: Sequence[Slot]) -> list[tuple[int, Node]]:
    """``(slot index, child)`` of each opaque ``property`` child of a pad's slot list."""
    out: list[tuple[int, Node]] = []
    for index, slot in enumerate(slots):
        if isinstance(slot, Opaque) and slot.fragment.startswith(f"({FAB_PROPERTY}"):
            child = slotlib.opaque_child(slot)
            if isinstance(child, Node) and child.name == FAB_PROPERTY:
                out.append((index, child))
    return out


def projected_fab_property(slots: Sequence[Slot]) -> PadFabProperty | None:
    """The mark that the opaque ``property`` children of a pad stand for (the first one's)."""
    found = opaque_fab_properties(slots)
    return read_fab_property(found[0][1]) if found else None


def _rebuild_pad(pad: Pad, opaque: Callable[[Opaque], Node | Atom]) -> Node:
    """A library pad from its slots; a pad without a ``zone_connect`` or a fabrication ``property`` child
    gains one when the model sets ``zone_connection`` or ``fab_property``."""
    slots = _entity_slots(pad)
    wanted = _modelled(slots)
    if not opaque_zone_connects(slots):
        wanted = wanted | {"zone_connection"}
    if not opaque_fab_properties(slots):
        wanted = wanted | {"fab_property"}
    source = _Items(emit_pad(pad, None), wanted)
    return slotlib.rebuild(Atom.symbol("pad"), slots, source, canonical=PAD_CANONICAL, opaque=opaque)


def _rebuild(
    entity: Pad | Graphic,
    items: Mapping[str, Sequence[Node | Atom]],
    head: str = "pad",
    *,
    opaque: Callable[[Opaque], Node | Atom] = slotlib.opaque_child,
) -> Node:
    slots = _entity_slots(entity)
    return slotlib.rebuild(Atom.symbol(head), slots, _Items(items, _modelled(slots)), opaque=opaque)


__all__ = [
    "DEF_FIELDS",
    "DEF_POSITIONAL",
    "FP_GRAPHIC_HEADS",
    "GRAPHIC_FIELDS",
    "GR_GRAPHIC_HEADS",
    "PADSTACK_MODES",
    "PAD_CANONICAL",
    "PAD_FIELDS",
    "PAD_KINDS",
    "PAD_POSITIONAL",
    "PAD_SHAPES",
    "POINT_HEADS",
    "FAB_PROPERTY_TOKENS",
    "IdSource",
    "Ids",
    "Items",
    "angle_atom",
    "at_node",
    "emit_attr",
    "emit_footprint",
    "emit_graphic",
    "emit_pad",
    "fab_property_node",
    "layers_node",
    "net_tie_groups",
    "net_tie_node",
    "node",
    "opaque_fab_properties",
    "opaque_zone_connects",
    "padstack_key",
    "point_node",
    "projected_fab_property",
    "projected_net_ties",
    "projected_zone_connect",
    "read_drill",
    "read_fab_property",
    "read_graphic",
    "read_pad",
    "read_padstack",
    "size_of",
    "symbols",
    "text_of",
    "unrepresentable",
    "uuid_items",
]
