lgili/Fenolite/src/fenolite/backends/kicad/cli.py

# SPDX-License-Identifier: Apache-2.0
# Copyright (c) 2026 Fenolite contributors
"""The package ``kicad-cli`` runner: KiCad's command-line tool as an oracle, always on copies.

``kicad-cli`` writes files next to the board it opens (S-0020), so every run copies its inputs to a
fresh temporary folder, runs there with an isolated environment and returns the files the run
created or changed. The caller's files are only ever read. Commands: S-0022 (10.0), S-0037 (9.0).

Each run also gets its own temporary, runtime, cache and state folders (``private_state``, c0153), so
parallel ``kicad-cli`` processes share no instance lock or cache file (``docs/formats/kicad/cli.md``,
"Per-run state").
"""

# evidence: see altium_import, helpmatrix, oracle, plot

from __future__ import annotations

import hashlib
import json
import os
import re
import shutil
import subprocess
import tempfile
from collections.abc import Mapping, Sequence
from dataclasses import dataclass
from pathlib import Path, PurePosixPath
from typing import Literal, cast

from fenolite.backends.base import DrcReport, ErcReport
from fenolite.core.errors import FenoliteError

MACOS_KICAD_CLI = Path("/Applications/KiCad/KiCad.app/Contents/MacOS/kicad-cli")
WINDOWS_KICAD_VERSIONS = ("10.0", "9.0")
"""The install folders KiCad's Windows installer uses, newest first: ``<Program Files>\\KiCad\\<major>.0``."""


def windows_kicad_clis() -> tuple[Path, ...]:
    """``kicad-cli.exe`` in each default Windows install folder, newest first; empty on other systems.
    KiCad's installer does not put ``kicad-cli`` on ``PATH``."""
    if os.name != "nt":
        return ()
    roots = dict.fromkeys(
        os.environ[name] for name in ("ProgramW6432", "ProgramFiles") if os.environ.get(name)
    )
    return tuple(
        Path(root) / "KiCad" / version / "bin" / "kicad-cli.exe"
        for version in WINDOWS_KICAD_VERSIONS
        for root in roots
    )


CONFIG_DIR = "config"
STATE_DIR = ".fenolite-state"
"""The run folder's subfolder holding the run's private temporary, runtime, cache and state folders."""
RESERVED_DIRS = (CONFIG_DIR, STATE_DIR)
STATE_VARIABLES: tuple[tuple[str, str], ...] = (
    ("TMPDIR", "tmp"),
    ("TMP", "tmp"),
    ("TEMP", "tmp"),
    ("XDG_RUNTIME_DIR", "runtime"),
    ("XDG_CACHE_HOME", "cache"),
    ("XDG_STATE_HOME", "xdg-state"),
)
"""Each variable ``private_state`` sets and the subfolder it names: the temporary folder of POSIX
(``TMPDIR``, S-0703) with the two other names Python's ``tempfile`` reads (``TEMP``, ``TMP``, S-0705),
and the runtime, cache and state folders of the XDG Base Directory specification (S-0704). Configuration
and data folders are not moved: ``KICAD_CONFIG_HOME`` is set apart, and fonts and user data are only
read."""
DRC_REPORT = "drc.json"
ERC_REPORT = "erc.json"
NETLIST = "out.net"
"""The file name ``export_netlist`` asks ``kicad-cli`` to write."""
BOM = "bom.csv"
"""The file name ``export_bom`` asks ``kicad-cli`` to write."""
RENDER_DIR = "render"
IMPORTED_BOARD = "imported.kicad_pcb"
"""The file name ``import_board`` asks ``kicad-cli`` to write."""
IMPORT_REPORT = "import.json"
_VERSION = re.compile(r"(\d+)\.(\d+)")
DOCKER_PREFIX = "docker:"


def find_kicad_cli(explicit: str | os.PathLike[str] | None = None) -> Path | None:
    """The ``kicad-cli`` to use: ``explicit``, else ``FENOLITE_KICAD_CLI``, else ``PATH``, else the default
    Windows install folder, else the macOS application bundle. An explicit path or override naming a
    missing file gives ``None``."""
    if explicit is not None:
        if os.fspath(explicit).startswith(DOCKER_PREFIX) and os.fspath(explicit)[len(DOCKER_PREFIX) :]:
            return Path(os.fspath(explicit))
        path = Path(os.fspath(explicit))
        return path if path.is_file() else None
    override = os.environ.get("FENOLITE_KICAD_CLI")
    if override:
        if override.startswith(DOCKER_PREFIX) and override[len(DOCKER_PREFIX) :]:
            return Path(override)
        return Path(override) if Path(override).is_file() else None
    found = shutil.which("kicad-cli")
    if found:
        return Path(found)
    installed = next((path for path in windows_kicad_clis() if path.is_file()), None)
    if installed is not None:
        return installed
    return MACOS_KICAD_CLI if MACOS_KICAD_CLI.is_file() else None


CandidateSource = Literal["explicit", "env", "path", "windows-install", "macos-app"]


@dataclass(frozen=True, slots=True)
class CliCandidate:
    """An existing ``kicad-cli`` file and where it was found."""

    path: Path
    source: CandidateSource


def _program_names(stem: str) -> tuple[str, ...]:
    """The file names a program has in a ``PATH`` folder: the bare name, and on Windows the name with each
    extension of ``PATHEXT`` (``kicad-cli.exe`` for KiCad itself)."""
    if os.name != "nt":
        return (stem,)
    extensions = os.environ.get("PATHEXT", ".COM;.EXE;.BAT;.CMD").split(os.pathsep)
    return (stem, *(stem + extension.lower() for extension in extensions if extension))


def kicad_cli_candidates(explicit: Sequence[str | os.PathLike[str]] = ()) -> tuple[CliCandidate, ...]:
    """Every existing ``kicad-cli``: each ``explicit`` path, ``FENOLITE_KICAD_CLI``, ``kicad-cli`` in each
    ``PATH`` entry, then the macOS bundle; deduplicated by resolved path, keeping the first source."""
    found: list[tuple[Path, CandidateSource]] = [(Path(os.fspath(p)), "explicit") for p in explicit]
    override = os.environ.get("FENOLITE_KICAD_CLI")
    if override:
        found.append((Path(override), "env"))
    for entry in os.environ.get("PATH", "").split(os.pathsep):
        if entry:
            found.extend((Path(entry) / name, "path") for name in _program_names("kicad-cli"))
    found.extend((path, "windows-install") for path in windows_kicad_clis())
    found.append((MACOS_KICAD_CLI, "macos-app"))
    seen: set[Path] = set()
    candidates: list[CliCandidate] = []
    for path, source in found:
        if not path.is_file():
            continue
        resolved = path.resolve()
        if resolved in seen:
            continue
        seen.add(resolved)
        candidates.append(CliCandidate(path, source))
    return tuple(candidates)


@dataclass(frozen=True)
class CliRun:
    """One ``kicad-cli`` run: its outcome, output streams and the files it created or changed."""

    outcome: Literal["exit", "timeout"]
    returncode: int | None
    stdout: str
    stderr: str
    outputs: Mapping[str, bytes]

    @property
    def ok(self) -> bool:
        return self.outcome == "exit" and self.returncode == 0


@dataclass(frozen=True)
class RefillRun:
    """A zone-refill run and the board KiCad saved, if it saved one."""

    run: CliRun
    board: bytes | None


@dataclass(frozen=True)
class ImportRun:
    """A ``pcb import`` run: the board KiCad wrote (``None`` when it wrote none) and its JSON report
    (``None`` when it wrote none, or one that is not a JSON object)."""

    run: CliRun
    board: bytes | None
    report: Mapping[str, object] | None


class KicadCliError(FenoliteError):
    """A ``kicad-cli`` helper failed (non-zero exit or timeout); ``run`` holds what happened."""

    def __init__(self, message: str, run: CliRun) -> None:
        self.run = run
        super().__init__(message)


class KicadCliVersionError(KicadCliError):
    """The command needs another ``kicad-cli`` major (for example ``pcb upgrade``, 10.0 only)."""

    cli_code = "FEN-6002"

    def __init__(self, message: str, run: CliRun, hint: str = "") -> None:
        super().__init__(message, run)
        self.hint = hint


def _sha256(path: Path) -> str:
    return hashlib.sha256(path.read_bytes()).hexdigest()


def _files(root: Path) -> dict[str, Path]:
    """Every regular file under ``root``, keyed by POSIX path relative to it, the config and state folders
    excluded."""
    found: dict[str, Path] = {}
    for path in sorted(root.rglob("*")):
        rel = path.relative_to(root)
        if rel.parts[0] in RESERVED_DIRS or not path.is_file():
            continue
        found[rel.as_posix()] = path
    return found


def _relative(name: str) -> PurePosixPath:
    rel = PurePosixPath(name)
    if rel.is_absolute() or not rel.parts or ".." in rel.parts or rel.parts[0] in RESERVED_DIRS:
        raise ValueError(f"run file name {name!r} must be a relative path outside {RESERVED_DIRS!r}")
    return rel


def private_state(root: Path) -> dict[str, str]:
    """Create under ``root`` a temporary, runtime, cache and state folder readable by the owner only, and
    return the variables of ``STATE_VARIABLES`` naming them: the state of one process or one run.

    ``kicad-cli`` keeps an instance lock file under the system temporary folder, so processes that share
    that folder share the file (c0153); with these variables each run has its own."""
    found: dict[str, str] = {}
    for variable, name in STATE_VARIABLES:
        folder = root / name
        folder.mkdir(mode=0o700, parents=True, exist_ok=True)
        folder.chmod(0o700)
        found[variable] = str(folder)
    return found


def _environment(config: Path, state: Mapping[str, str], extra: Mapping[str, str] | None) -> dict[str, str]:
    environ = {key: value for key, value in os.environ.items() if not key.startswith("KICAD")}
    environ.update(state)
    environ.update({"KICAD_CONFIG_HOME": str(config), "LANG": "C", "LC_ALL": "C"})
    environ.update(extra or {})
    return environ


def _decode(data: bytes | str | None) -> str:
    if data is None:
        return ""
    return data if isinstance(data, str) else data.decode("utf-8", "replace")


class KicadCli:
    """A ``kicad-cli`` binary, run as a subprocess on temporary copies (``timeout`` in seconds)."""

    def __init__(self, path: Path, *, timeout: float = 120) -> None:
        self.path = Path(path)
        self.timeout = timeout
        self._version: str | None = None

    def version(self) -> str:
        """The first line that ``kicad-cli version`` prints, for example ``10.0.6``."""
        if self._version is None:
            run = self.run(["version"], files={})
            lines = run.stdout.strip().splitlines()
            if not run.ok or not lines:
                raise KicadCliError(f"kicad-cli version failed: {run.stderr.strip()}", run)
            self._version = lines[0].strip()
        return self._version

    def major(self) -> int:
        match = _VERSION.search(self.version())
        if match is None:
            raise ValueError(f"cannot read a version from {self.version()!r}")
        return int(match.group(1))

    def run(
        self,
        args: Sequence[str],
        *,
        files: Mapping[str, Path | bytes],
        env: Mapping[str, str] | None = None,
        folders: Sequence[str] = (),
    ) -> CliRun:
        """Copy ``files`` (relative name → file or folder, or the bytes of a file that exists nowhere on
        disk: a plot copy of change c0117) to a fresh folder, create the empty ``folders`` there, and
        run. A file given as bytes is an output only when the run changed it, like any copied file."""
        tmp = Path(tempfile.mkdtemp(prefix="fenolite-kicad-"))
        try:
            config = tmp / CONFIG_DIR
            config.mkdir()
            for name, source in files.items():
                target = tmp / _relative(name)
                target.parent.mkdir(parents=True, exist_ok=True)
                if isinstance(source, bytes):
                    target.write_bytes(source)
                elif Path(source).is_dir():
                    shutil.copytree(source, target)
                else:
                    shutil.copyfile(source, target)
            for name in folders:
                (tmp / _relative(name)).mkdir(parents=True, exist_ok=True)
            before = {rel: _sha256(path) for rel, path in _files(tmp).items()}
            command = self._command(args, tmp, env)
            try:
                proc = subprocess.run(
                    command,
                    cwd=tmp,
                    env=_environment(config, self._state(tmp / STATE_DIR), env),
                    capture_output=True,
                    timeout=self.timeout,
                    check=False,
                )
                outcome: Literal["exit", "timeout"] = "exit"
                returncode: int | None = proc.returncode
                stdout, stderr = _decode(proc.stdout), _decode(proc.stderr)
            except subprocess.TimeoutExpired as exc:
                outcome, returncode = "timeout", None
                stdout, stderr = _decode(exc.stdout), _decode(exc.stderr)
            outputs = {
                rel: path.read_bytes()
                for rel, path in _files(tmp).items()
                if rel not in before or _sha256(path) != before[rel]
            }
            return CliRun(outcome, returncode, _sanitise(stdout, tmp), _sanitise(stderr, tmp), outputs)
        finally:
            shutil.rmtree(tmp, ignore_errors=True)

    def _command(self, args: Sequence[str], tmp: Path, env: Mapping[str, str] | None = None) -> list[str]:
        """The command line of one run. ``env`` is the run's extra environment: a runner whose tool does
        not inherit the process environment (a container) passes it on the command line."""
        return [str(self.path), *map(str, args)]

    def _state(self, root: Path) -> dict[str, str]:
        """The run's private state variables: ``private_state`` under ``root``."""
        return private_state(root)

    def _checked(self, args: Sequence[str], files: Mapping[str, Path | bytes], what: str) -> CliRun:
        run = self.run(args, files=files)
        if run.outcome == "timeout":
            raise KicadCliError(f"kicad-cli {what} timed out after {self.timeout} s", run)
        if run.returncode != 0:
            detail = (run.stderr or run.stdout).strip()
            raise KicadCliError(f"kicad-cli {what} exited {run.returncode}: {detail}", run)
        return run

    def load_board_svg(self, board: Path, *, files: Mapping[str, Path] | None = None) -> CliRun:
        """The board load check: ``pcb export svg -l Edge.Cuts --mode-single`` exits 0 and writes the SVG.

        ``files`` are copied next to the board (a project file, ``fp-lib-table``, library folders).
        """
        name = Path(board).name
        args = ["pcb", "export", "svg", "-l", "Edge.Cuts", "--mode-single", "-o", "out.svg", name]
        run = self._checked(args, _with(board, files), "pcb export svg")
        if "out.svg" not in run.outputs:
            raise KicadCliError("kicad-cli pcb export svg wrote no SVG", run)
        return run

    def export_pos_csv(self, board: Path, *, files: Mapping[str, Path] | None = None) -> str:
        """``pcb export pos --format csv --side both --units mm`` (the default unit is inches)."""
        name = Path(board).name
        args = ["pcb", "export", "pos", "--format", "csv", "--side", "both", "--units", "mm"]
        run = self._checked([*args, "-o", "pos.csv", name], _with(board, files), "pcb export pos")
        return _output(run, "pos.csv", "pcb export pos")

    def export_ipcd356(self, board: Path, *, files: Mapping[str, Path] | None = None) -> str:
        """``pcb export ipcd356``: the IPC-D-356 netlist text."""
        name = Path(board).name
        run = self._checked(
            ["pcb", "export", "ipcd356", "-o", "board.d356", name], _with(board, files), "pcb export ipcd356"
        )
        return _output(run, "board.d356", "pcb export ipcd356")

    def export(
        self, args: Sequence[str], board: Path, *, files: Mapping[str, Path | bytes] | None = None, out: str
    ) -> CliRun:
        """An export command (``args`` without the board) on a copy of ``board``, with the folder ``out``
        created in the run folder first; the caller reads ``returncode`` and the files under ``out``."""
        return self.run([*args, Path(board).name], files=_with(board, files), folders=(out,))

    def render(
        self,
        board: Path,
        *,
        side: Literal["top", "bottom"],
        width: int,
        height: int,
        files: Mapping[str, Path] | None = None,
    ) -> CliRun:
        """``pcb render --side <side>``: the PNG is ``render/<side>.png`` among the outputs. The image is at
        most ``width`` by ``height`` (``docs/formats/kicad/cli.md``)."""
        args = ["pcb", "render", "--side", side, "--width", str(width), "--height", str(height)]
        return self.export([*args, "-o", f"{RENDER_DIR}/{side}.png"], board, files=files, out=RENDER_DIR)

    def _require_ten(self, what: str) -> None:
        if self.major() < 10:
            run = CliRun("exit", None, "", "", {})
            raise KicadCliVersionError(
                f"{what} needs kicad-cli 10.0 or newer; running {self.version()}",
                run,
                hint="run the 10.0 image, for example the kicad-10 job's container",
            )

    def upgrade_board(self, board: Path, *, files: Mapping[str, Path] | None = None) -> bytes:
        """``pcb upgrade --force`` (10.0 only): the board re-saved in the running version's format."""
        self._require_ten("pcb upgrade")
        name = Path(board).name
        run = self._checked(["pcb", "upgrade", "--force", name], _with(board, files), "pcb upgrade")
        return run.outputs.get(name, Path(board).read_bytes())

    def import_board(self, source: Path, *, format: str = "altium") -> ImportRun:  # noqa: A002
        """``pcb import --format <format>`` (10.0 only) on a copy of ``source``: the run, the board it
        wrote and its JSON report. It never raises for a non-zero exit; the caller reads ``board``."""
        self._require_ten("pcb import")
        name = Path(source).name
        args = ["pcb", "import", "--format", format, "--report-format", "json"]
        args += ["--report-file", IMPORT_REPORT, "-o", IMPORTED_BOARD, name]
        run = self.run(args, files={name: Path(source)})
        report: object = None
        if IMPORT_REPORT in run.outputs:
            try:
                report = json.loads(run.outputs[IMPORT_REPORT].decode("utf-8", "replace"))
            except ValueError:
                report = None
        return ImportRun(
            run,
            run.outputs.get(IMPORTED_BOARD),
            cast(Mapping[str, object], report) if isinstance(report, dict) else None,
        )

    def export_netlist(self, schematic: Path, *, files: Mapping[str, Path] | None = None) -> CliRun:
        """``sch export netlist --format kicadsexpr`` on a copy: the run, with the netlist under
        ``NETLIST`` in its outputs when one was written. It never raises for a non-zero exit, so a
        caller can use it as the load check of a schematic."""
        name = Path(schematic).name
        args = ["sch", "export", "netlist", "--format", "kicadsexpr", "-o", NETLIST, name]
        return self.run(args, files=_with(schematic, files))

    def export_bom(
        self, schematic: Path, *, fields: Sequence[str], files: Mapping[str, Path] | None = None
    ) -> CliRun:
        """``sch export bom`` on a copy, one row per reference: ``fields`` are the columns and their own
        labels, nothing is grouped and no reference range is folded. The CSV (comma-separated, text in
        double quotes: the tool's defaults) is under ``BOM`` in the outputs when one was written; the run
        never raises for a non-zero exit."""
        name = Path(schematic).name
        joined = ",".join(fields)
        args = ["sch", "export", "bom", "--fields", joined, "--labels", joined]
        return self.run([*args, "--ref-range-delimiter", "", "-o", BOM, name], files=_with(schematic, files))

    def upgrade_schematic(self, schematic: Path, *, files: Mapping[str, Path] | None = None) -> bytes:
        """``sch upgrade --force`` (10.0 only): the schematic re-saved in the running version's format."""
        self._require_ten("sch upgrade")
        name = Path(schematic).name
        run = self._checked(["sch", "upgrade", "--force", name], _with(schematic, files), "sch upgrade")
        return run.outputs.get(name, Path(schematic).read_bytes())

    def drc(
        self,
        board: Path,
        *,
        files: Mapping[str, Path] | None = None,
        env: Mapping[str, str] | None = None,
        schematic_parity: bool = False,
    ) -> DrcRun:
        """``pcb drc --format json --severity-all``: the run and its report (``None`` when none was written).

        The exit code is only a load signal; ``--exit-code-violations`` is never passed, and every
        verdict is read from the report. ``env`` is passed unchanged to ``run``, which applies its entries
        after its own ``KICAD_CONFIG_HOME``: the way a probe names a configuration folder or a library
        variable. With ``schematic_parity`` the run also passes ``--schematic-parity``, which makes the
        tool compare the board with the schematic of its stem (c0062).
        """
        from fenolite.backends.kicad.drc import read_drc_report
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
